peter-hanzo/KD/Документы/Чертежи/Конструктив/веранда 1.pdf

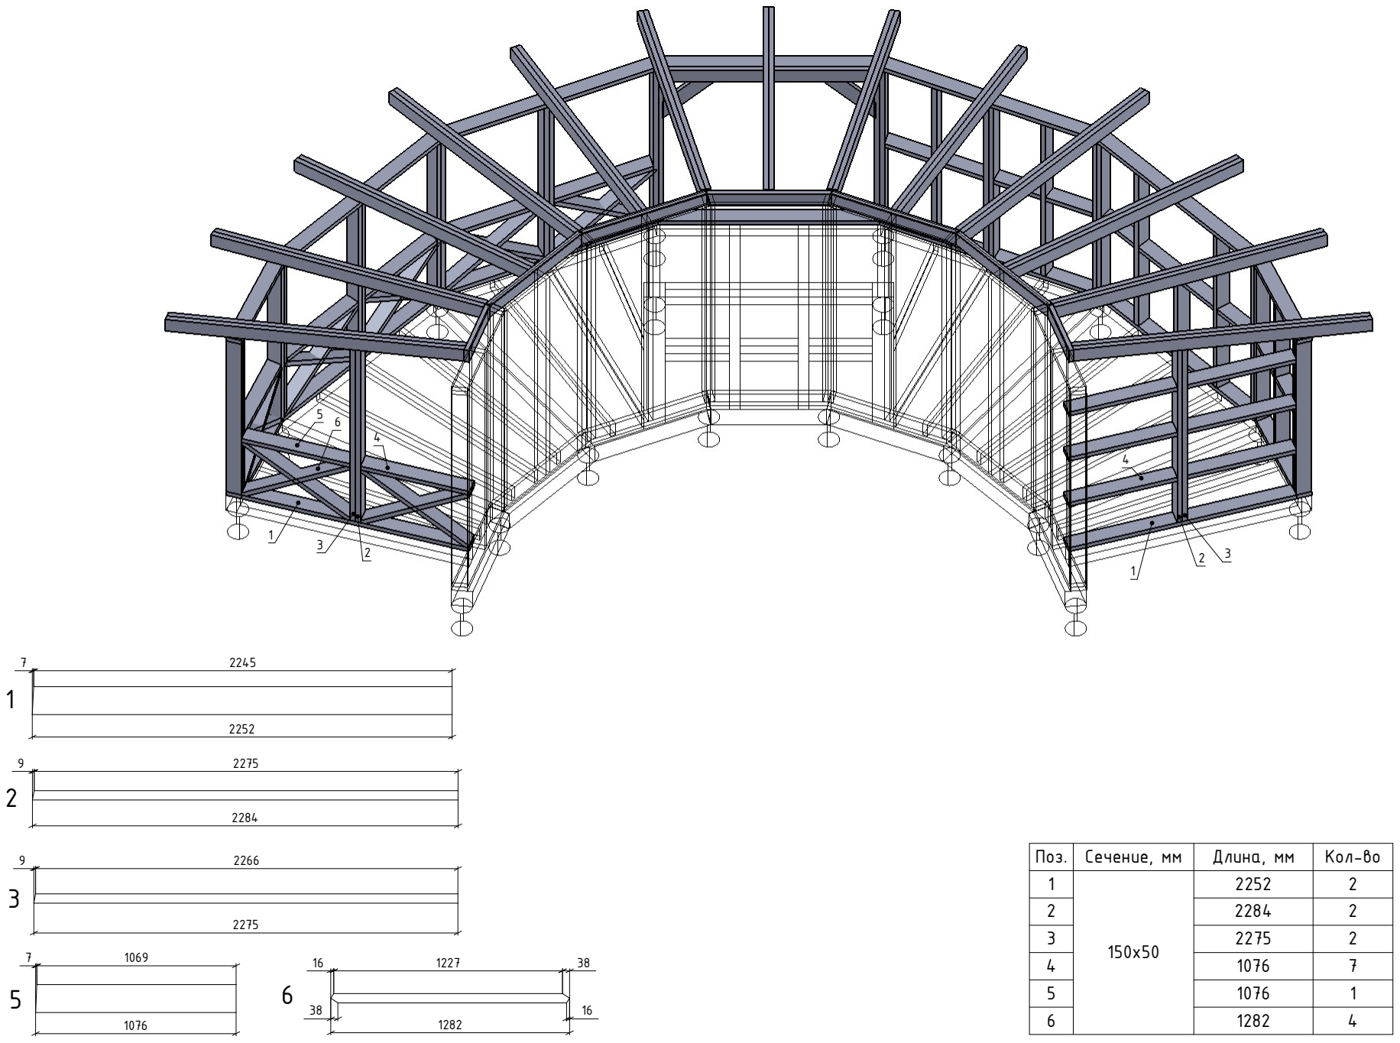
[picture p2: page 1]

6

1227 38
38
1282

16
16
Поз. | Сечение, мм | Длина, мм 2252 2 | Кол-во 1
3 | | 2275 | 2
5 | | 1076 | 1
2 | 150x50 | 2284 | 2
4 | | 1076 | 7
6 | | 1282 | 4

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
7 1069

1076

2245

2252

7 2

2284

9 2275

9 2266

2275
