peter-hanzo/KD/Документы/Участок/Кадастр - выписка.jpg

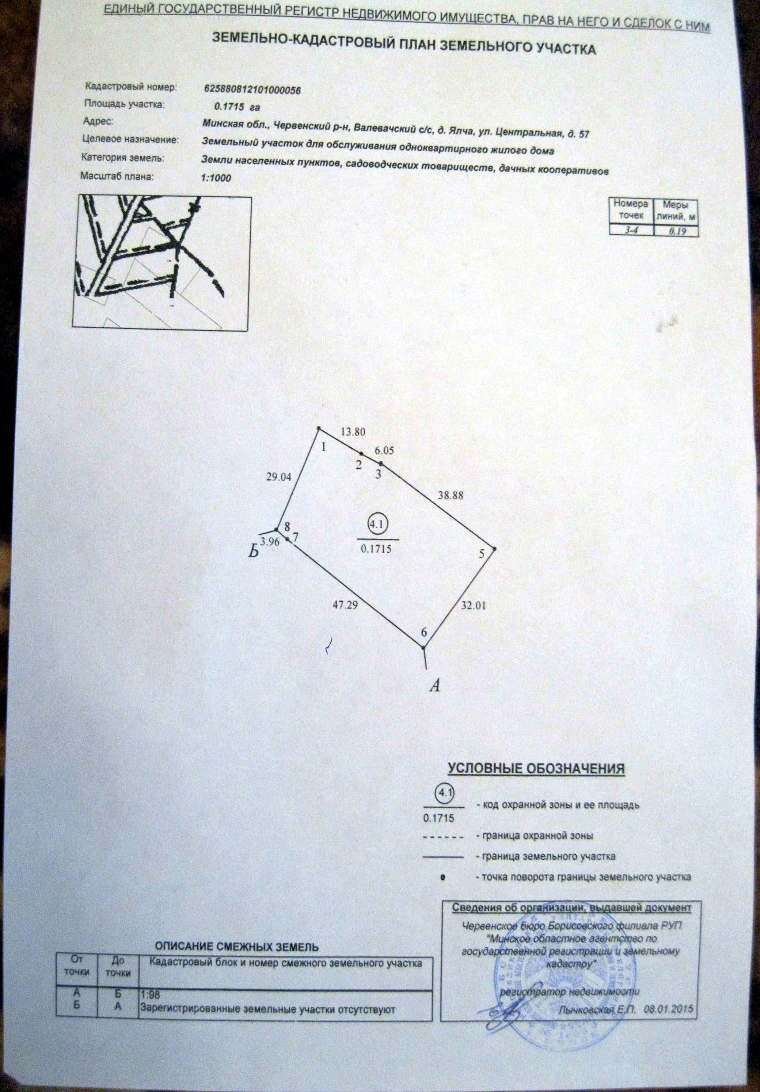
Документы/Участок/Кадастр - выписка.jpg
