peter-hanzo/KD/Документы/Участок/Свидетельство о государственной регистрации.jpg

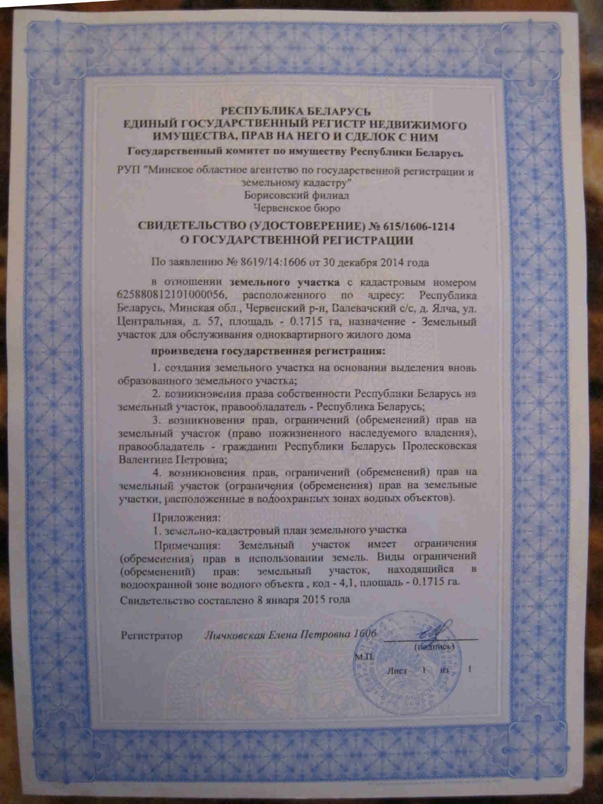
Документы/Участок/Свидетельство о государственной регистрации.jpg
