peter-hanzo/KD/Документы/Фактические расходы/2015-05/2015-05-20 - 2 109 300р - Установка электричества.jpg

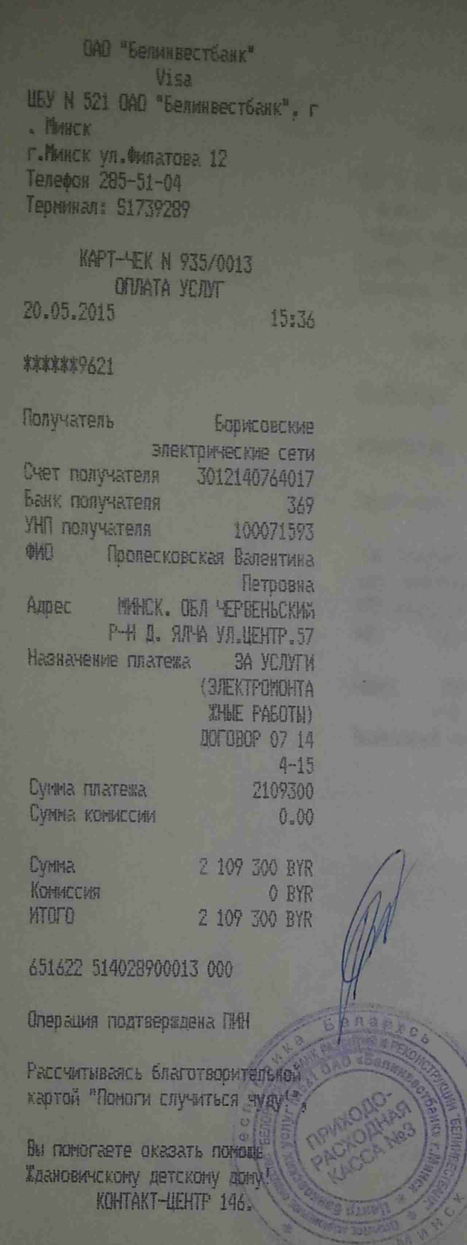
Документы/Фактические расходы/2015-05/2015-05-20 - 2 109 300р - Установка электричества.jpg
