peter-hanzo/KD/Документы/Фактические расходы/2015-05/2015-05-29 - 1 020 000р - Чертежи - Выбава-архитектура.jpg

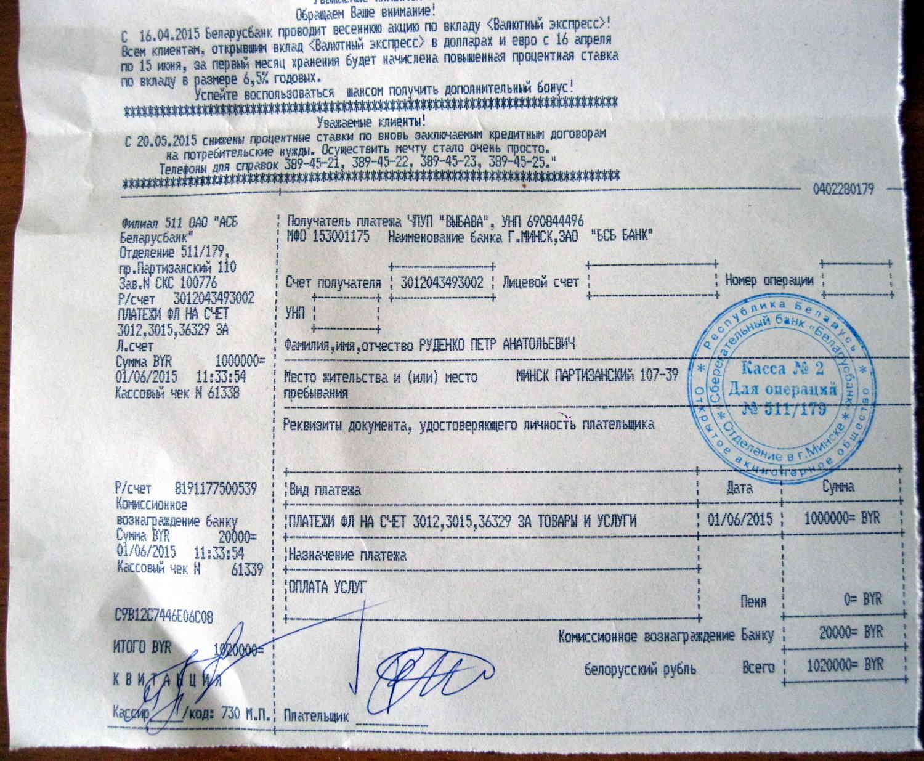
Документы/Фактические расходы/2015-05/2015-05-29 - 1 020 000р - Чертежи - Выбава-архитектура.jpg
