peter-hanzo/KD/Документы/Фактические расходы/2015-06/2015-06-15 - 21 300р - Транспорт - Ялча-Минск.jpg

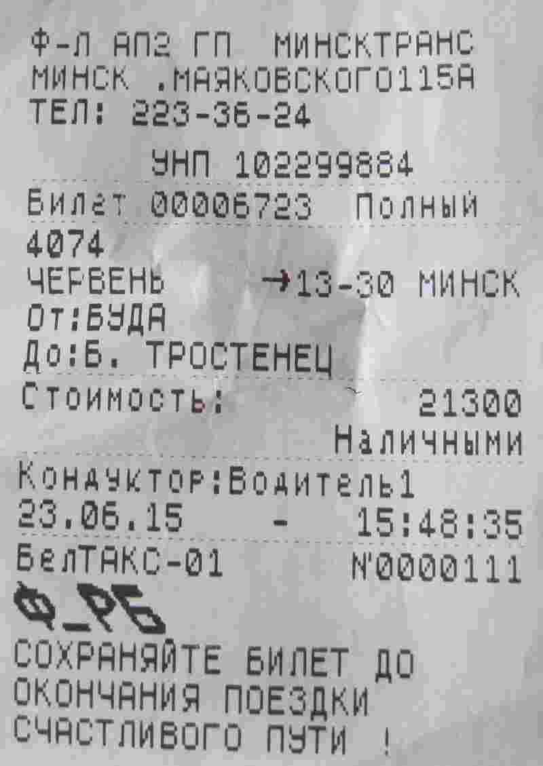
Документы/Фактические расходы/2015-06/2015-06-15 - 21 300р - Транспорт - Ялча-Минск.jpg
