peter-hanzo/KD/Документы/Фактические расходы/2015-06/2015-06-22 - 195 800р - Транспорт - Проездной.jpg

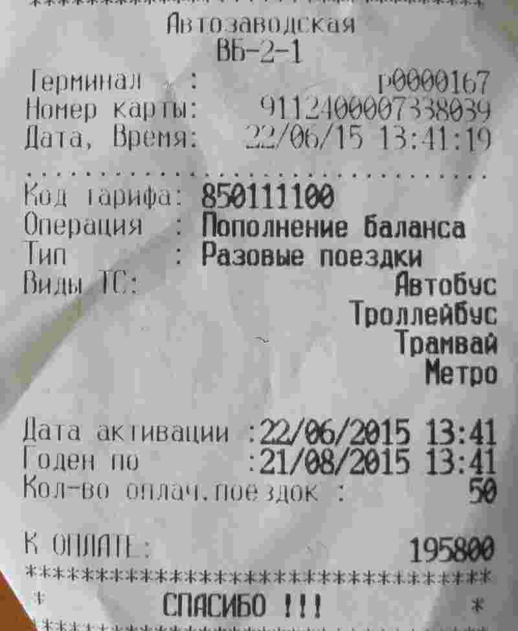
Документы/Фактические расходы/2015-06/2015-06-22 - 195 800р - Транспорт - Проездной.jpg
