peter-hanzo/KD/Документы/Фактические расходы/2015-06/2015-06-26 - 27 000р - Фундамент - Арматура.JPG

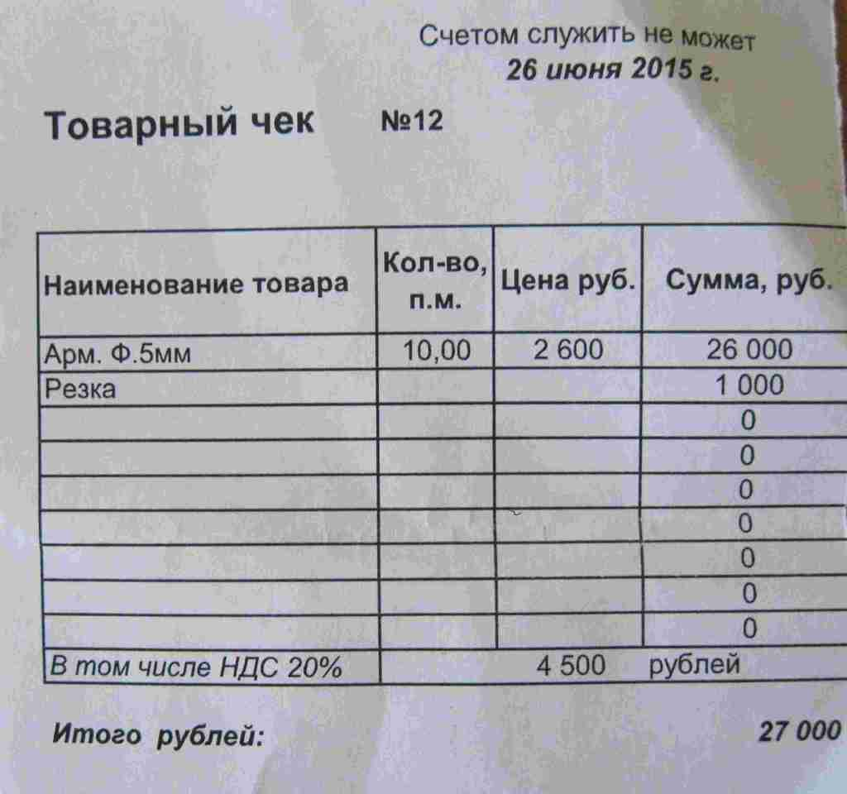
Документы/Фактические расходы/2015-06/2015-06-26 - 27 000р - Фундамент - Арматура.JPG
