peter-hanzo/KD/Документы/Фактические расходы/2015-06/2015-06-26 - 535 700р - Фундамент - Руберойд.JPG

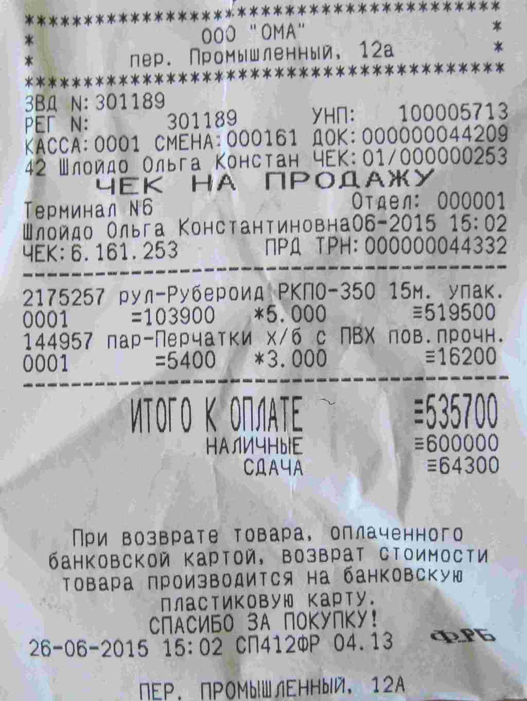
Документы/Фактические расходы/2015-06/2015-06-26 - 535 700р - Фундамент - Руберойд.JPG
