peter-hanzo/KD/Документы/Фактические расходы/2015-06/2015-06-26 - 600 000р - Доставка.JPG

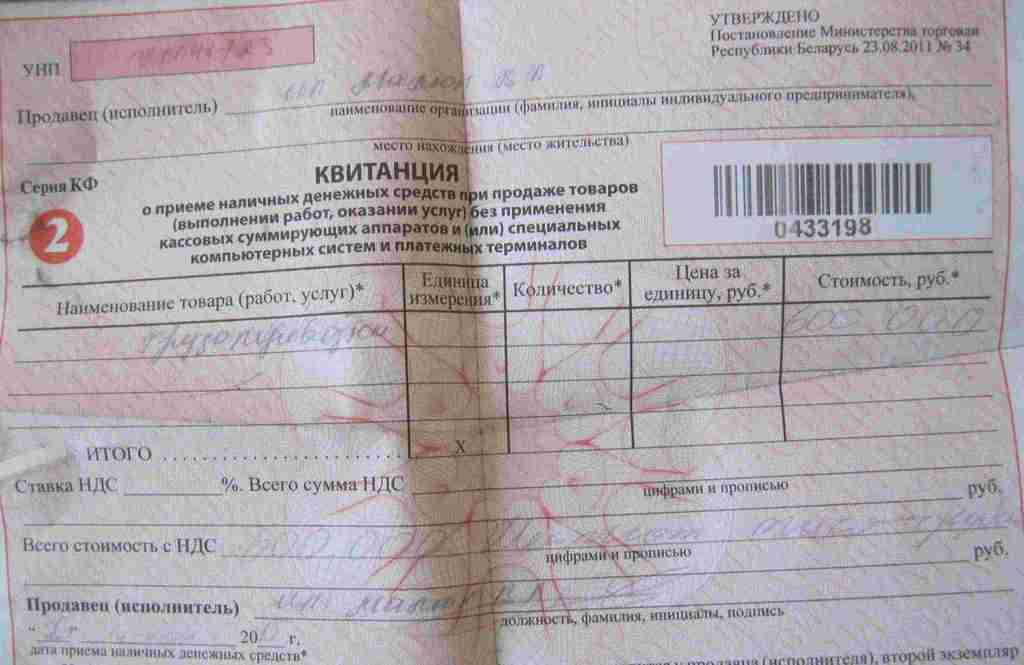
Документы/Фактические расходы/2015-06/2015-06-26 - 600 000р - Доставка.JPG
