peter-hanzo/KD/Документы/Фактические расходы/2015-06/2015-06-28 - 23 850р - Транспорт - Минск-Ялча.JPG

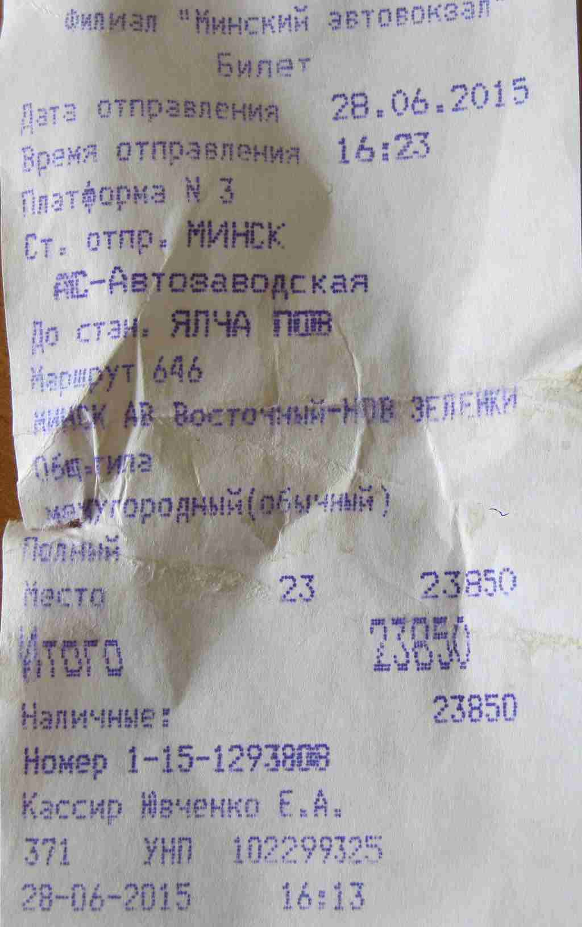
Документы/Фактические расходы/2015-06/2015-06-28 - 23 850р - Транспорт - Минск-Ялча.JPG
