peter-hanzo/KD/Документы/Фактические расходы/2015-06/2015-06-28 - 120 000р - Интернет.JPG

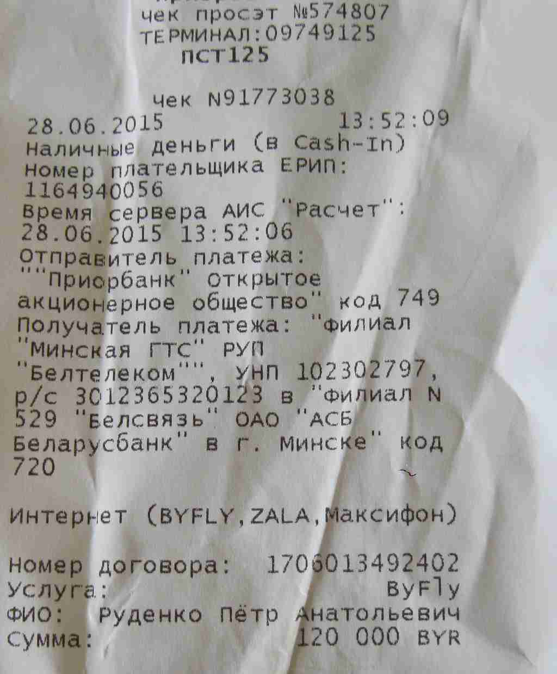
Документы/Фактические расходы/2015-06/2015-06-28 - 120 000р - Интернет.JPG
