peter-hanzo/KD/Документы/Фактические расходы/2015-06/2015-06-29 - 23 950р - Транспорт - Ялча-Минск.JPG

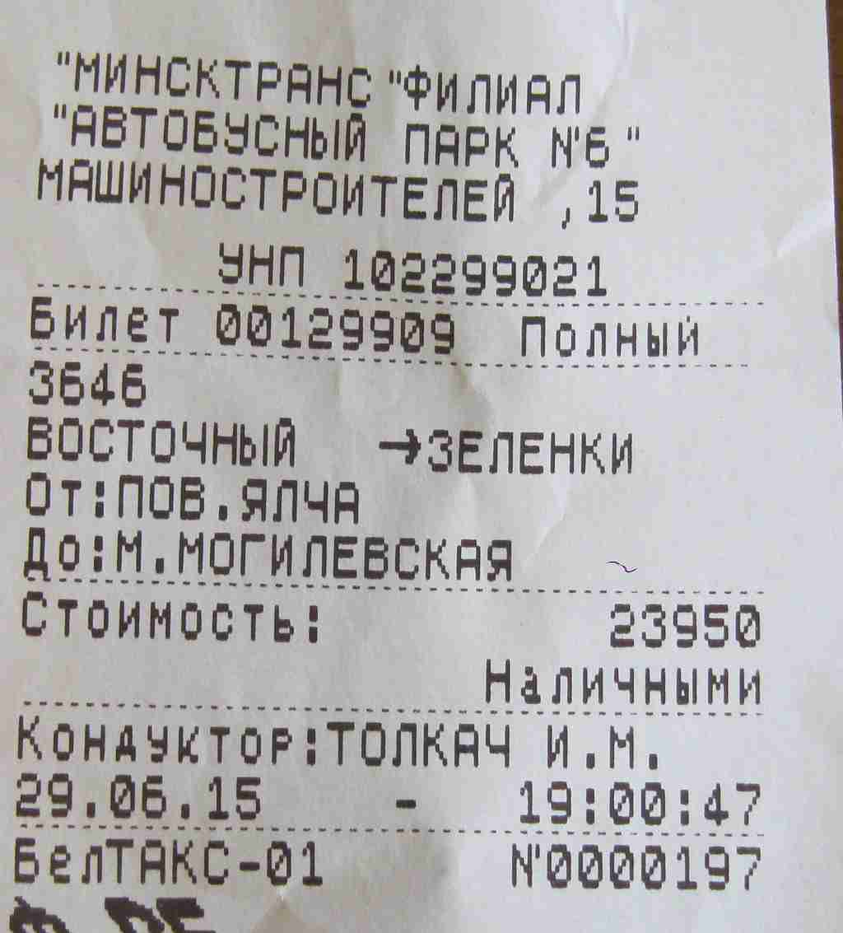
Документы/Фактические расходы/2015-06/2015-06-29 - 23 950р - Транспорт - Ялча-Минск.JPG
