peter-hanzo/KD/Документы/Фактические расходы/2015-07/2015-07-01 - 58 000р - Фундамент - Арматура.JPG

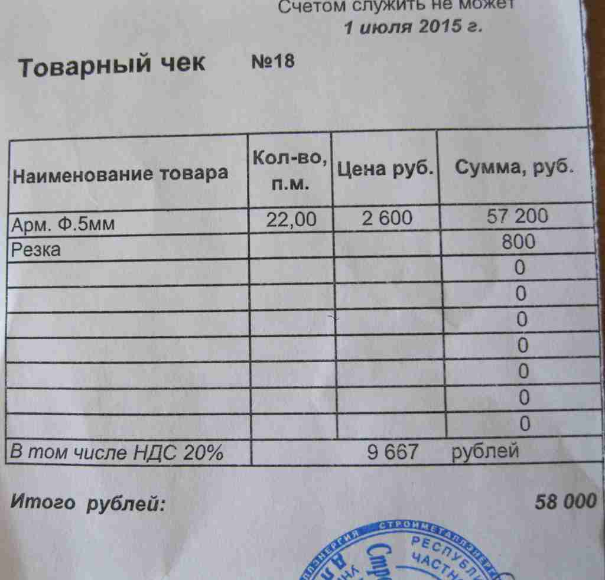
Документы/Фактические расходы/2015-07/2015-07-01 - 58 000р - Фундамент - Арматура.JPG
