peter-hanzo/KD/Документы/Фактические расходы/2015-07/2015-07-01 - 62 000р - Фундамент - Вязальная проволока.JPG

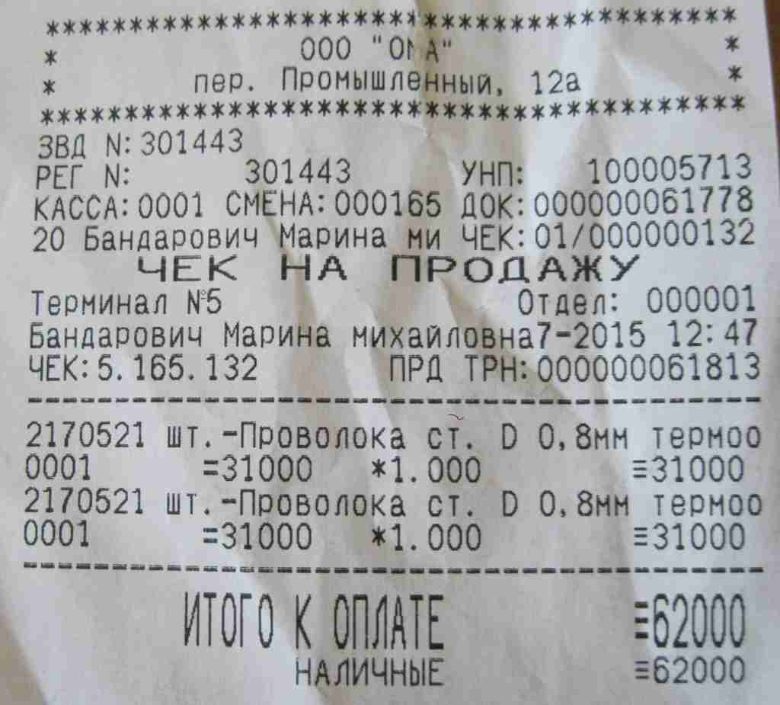
Документы/Фактические расходы/2015-07/2015-07-01 - 62 000р - Фундамент - Вязальная проволока.JPG
