peter-hanzo/KD/Документы/Фактические расходы/2015-07/2015-07-01 - 119 200р - Фундамент - Лента-скотч.JPG

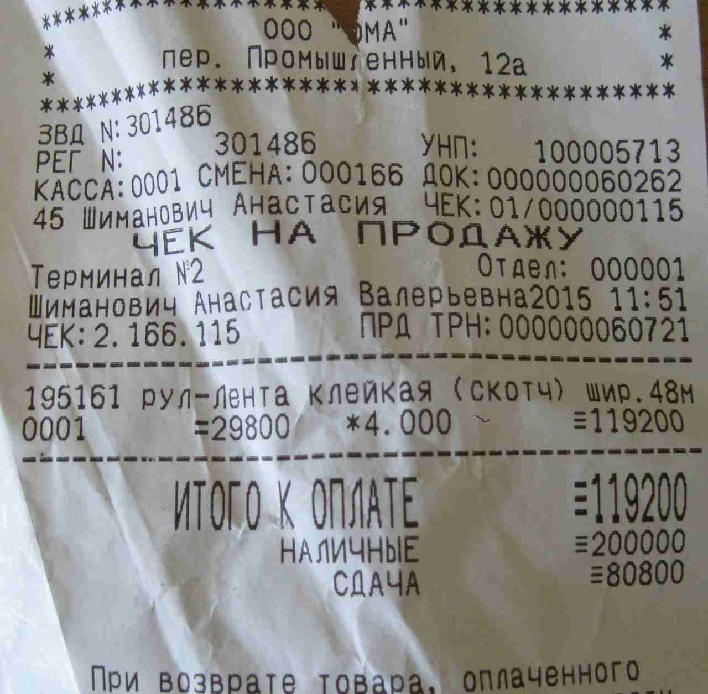
Документы/Фактические расходы/2015-07/2015-07-01 - 119 200р - Фундамент - Лента-скотч.JPG
