peter-hanzo/KD/Документы/Фактические расходы/2015-07/2015-07-01 - 220 00р - Связь - Мобильный.JPG

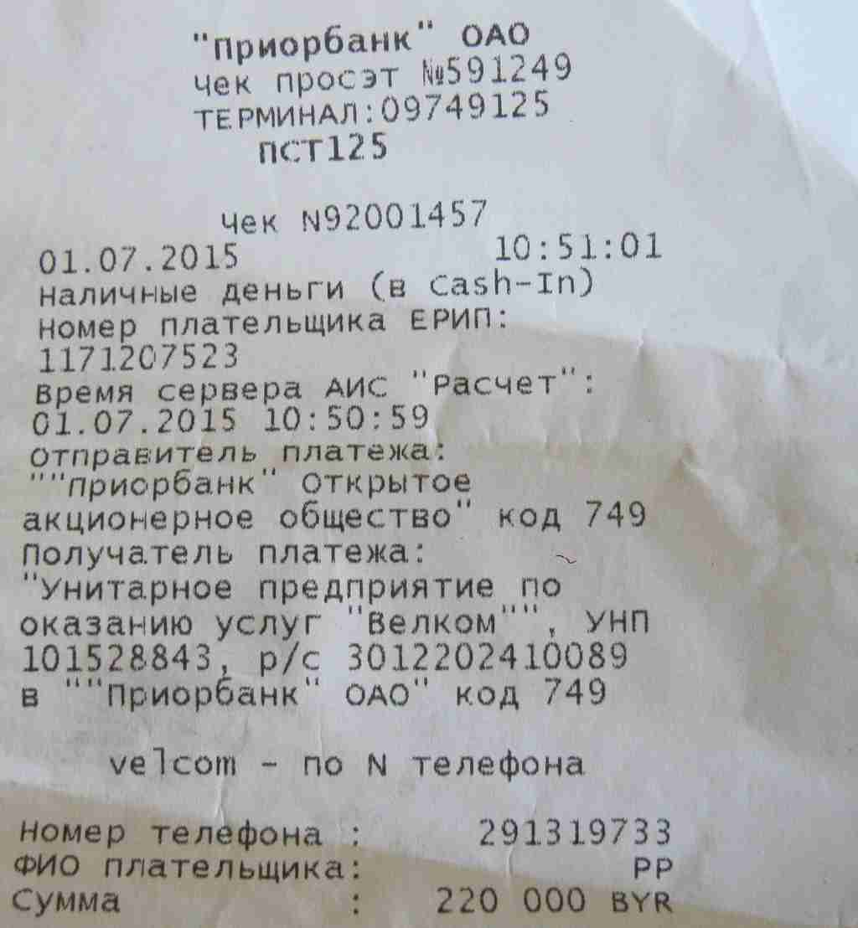
Документы/Фактические расходы/2015-07/2015-07-01 - 220 00р - Связь - Мобильный.JPG
