peter-hanzo/KD/Документы/Фактические расходы/2015-07/2015-07-02 - 23 900р - Транспорт - Ялча-Минск.JPG

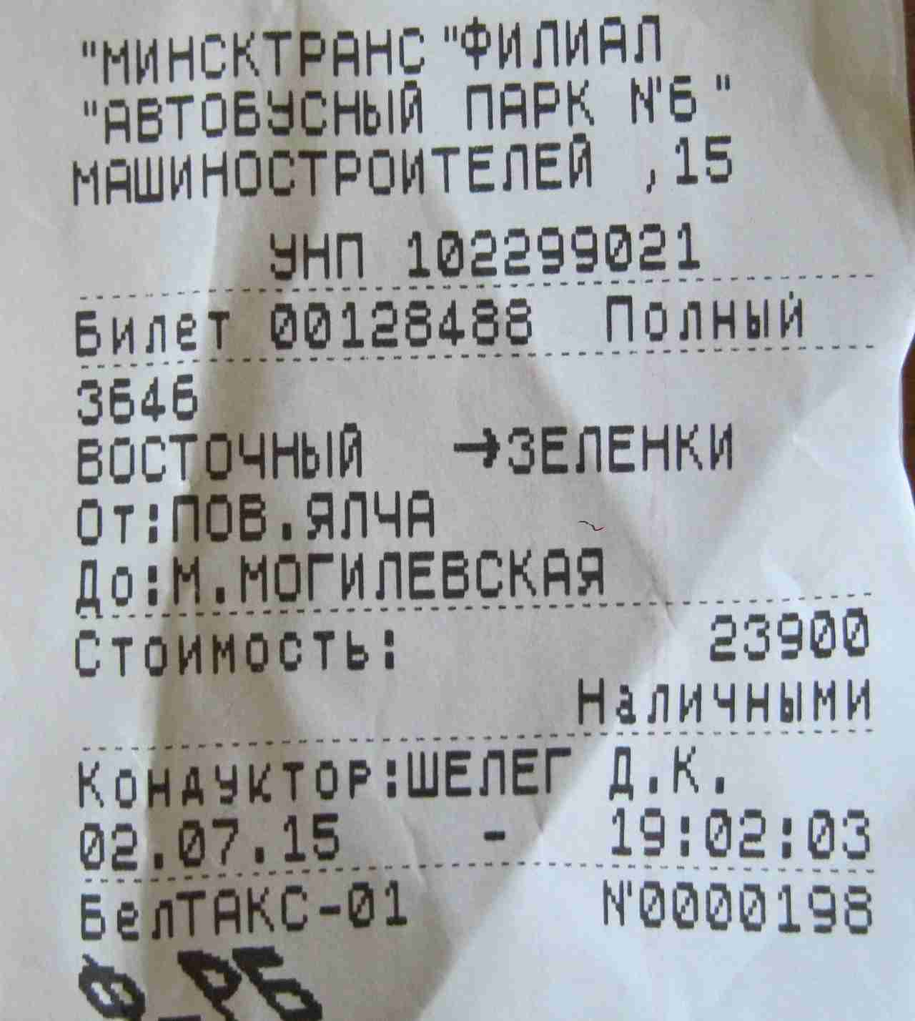
Документы/Фактические расходы/2015-07/2015-07-02 - 23 900р - Транспорт - Ялча-Минск.JPG
