peter-hanzo/KD/Документы/Фактические расходы/2015-07/2015-07-21 - 26 100р - Транспорт - Минск-Ялча.jpg

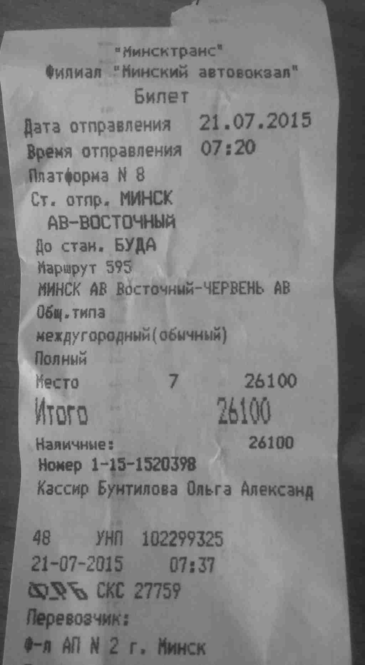
Документы/Фактические расходы/2015-07/2015-07-21 - 26 100р - Транспорт - Минск-Ялча.jpg
