peter-hanzo/KD/Документы/Фактические расходы/2015-07/2015-07-22 - 160 200р - Транспорт - Проездной.jpg

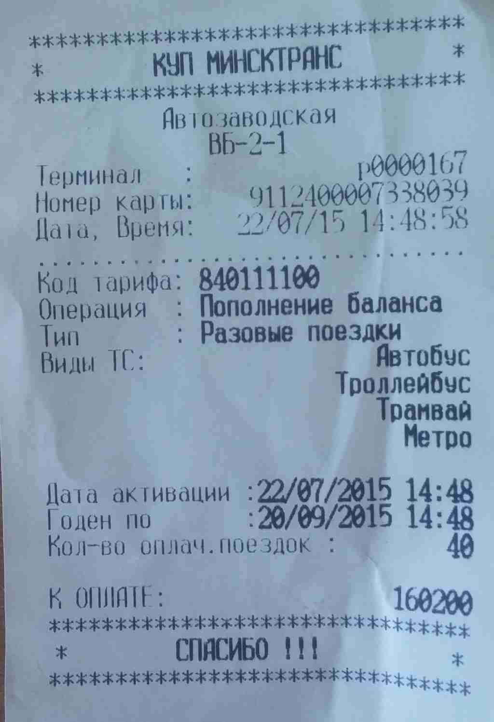
Документы/Фактические расходы/2015-07/2015-07-22 - 160 200р - Транспорт - Проездной.jpg
