peter-hanzo/KD/Документы/Фактические расходы/2015-07/2015-07-29 - 70 000р - Связь - Интернет.JPG

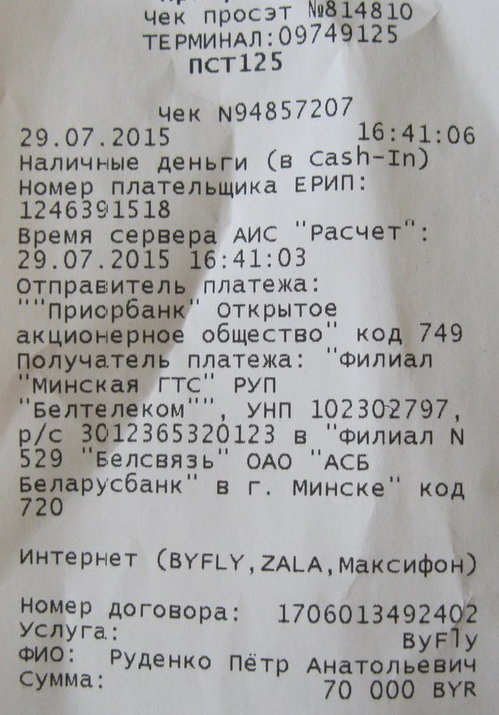
Документы/Фактические расходы/2015-07/2015-07-29 - 70 000р - Связь - Интернет.JPG
