peter-hanzo/KD/Документы/Фактические расходы/2015-08/2015-08-01 - 23 800р - Транспорт - Минск-Ялча.JPG

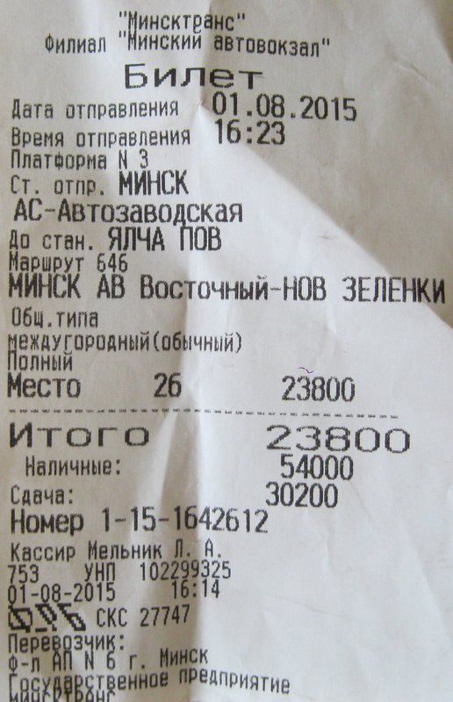
Документы/Фактические расходы/2015-08/2015-08-01 - 23 800р - Транспорт - Минск-Ялча.JPG
