peter-hanzo/KD/Документы/Фактические расходы/2015-08/2015-08-03 - 300 000р - Доставка - Бензин.JPG

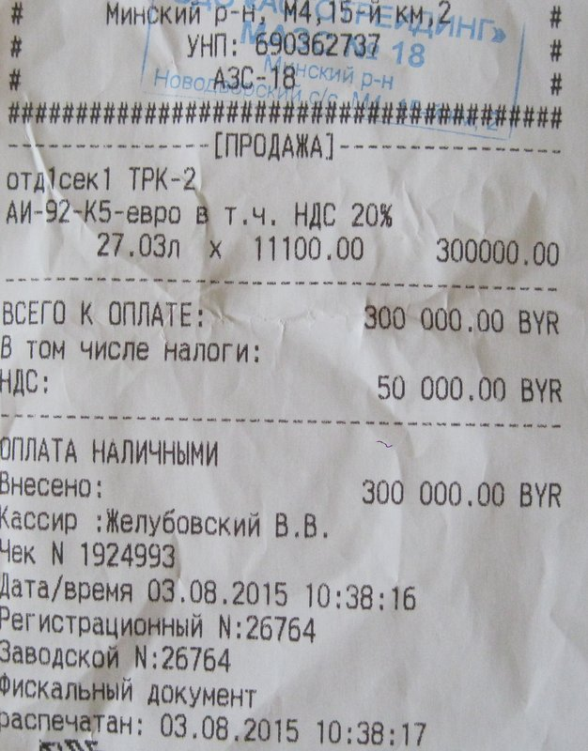
Документы/Фактические расходы/2015-08/2015-08-03 - 300 000р - Доставка - Бензин.JPG
