peter-hanzo/KD/Документы/Фактические расходы/2015-08/2015-08-03 - 620 000р - Инструмент - Аренда инструмента.JPG

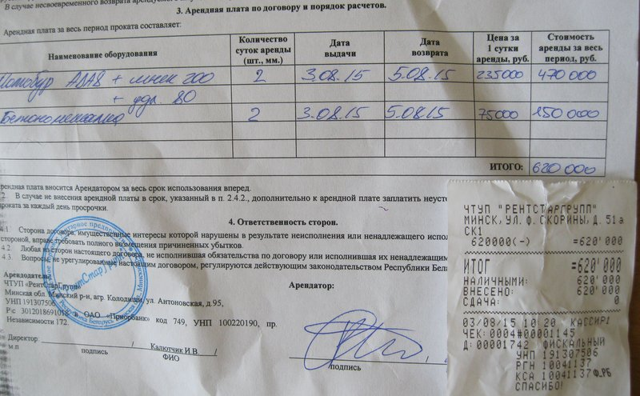
Документы/Фактические расходы/2015-08/2015-08-03 - 620 000р - Инструмент - Аренда инструмента.JPG
