peter-hanzo/KD/Документы/Фактические расходы/2015-08/2015-08-05 - 200 000р - Доставка - Бензин.JPG

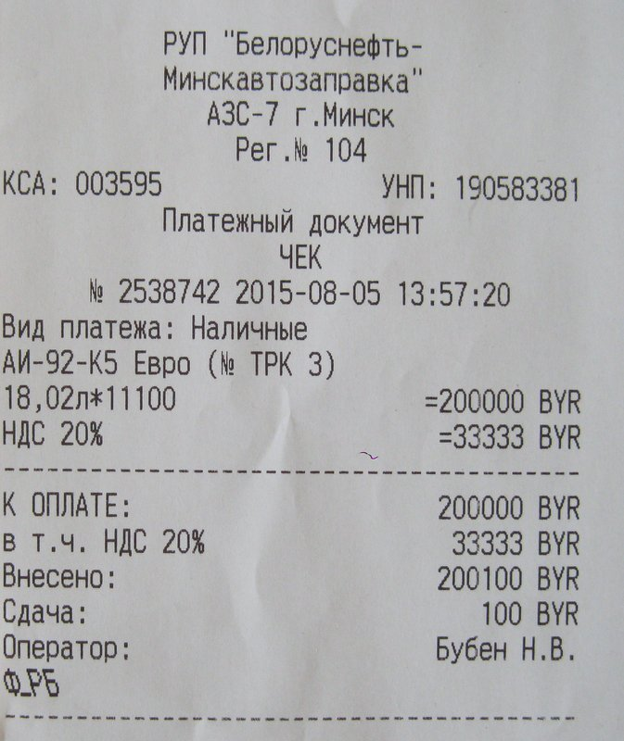
Документы/Фактические расходы/2015-08/2015-08-05 - 200 000р - Доставка - Бензин.JPG
