peter-hanzo/KD/Документы/Фактические расходы/2015-08/2015-08-11 - 195 800р - Транспорт - Проездной.jpg

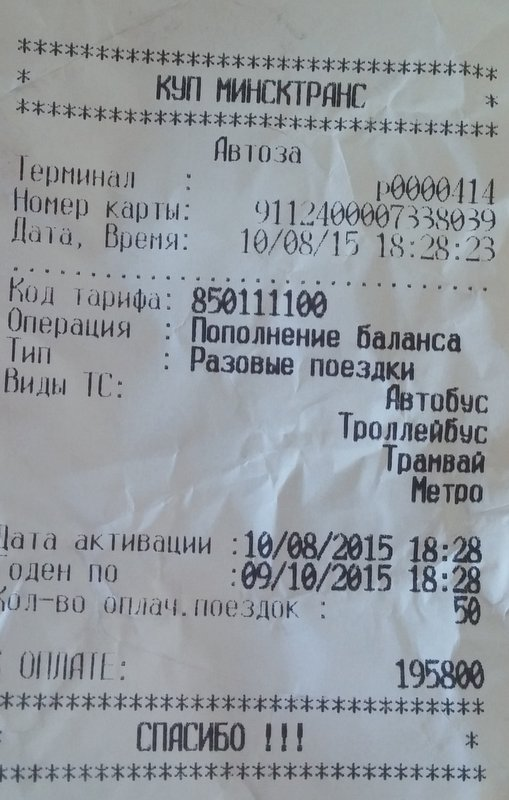
Документы/Фактические расходы/2015-08/2015-08-11 - 195 800р - Транспорт - Проездной.jpg
