peter-hanzo/KD/Документы/Фактические расходы/2015-08/2015-08-12 - 128 000р - Инструмент - Сверло для свай + 2 анкера.jpg

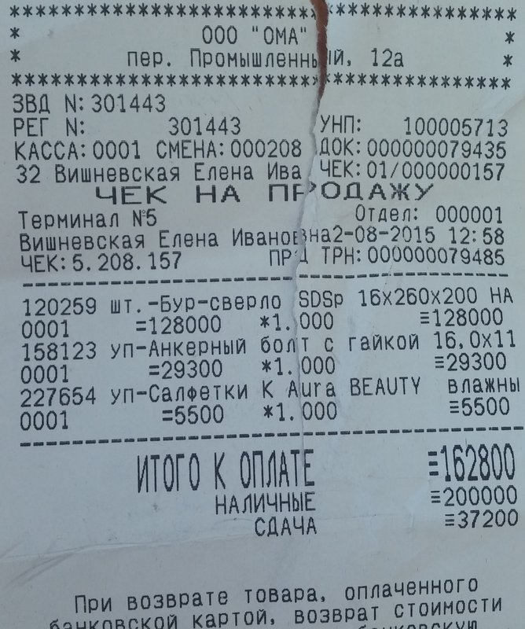
Документы/Фактические расходы/2015-08/2015-08-12 - 128 000р - Инструмент - Сверло для свай + 2 анкера.jpg
