peter-hanzo/KD/Документы/Фактические расходы/2015-08/2015-08-17 - 100 000р - Связь - Интернет.jpg

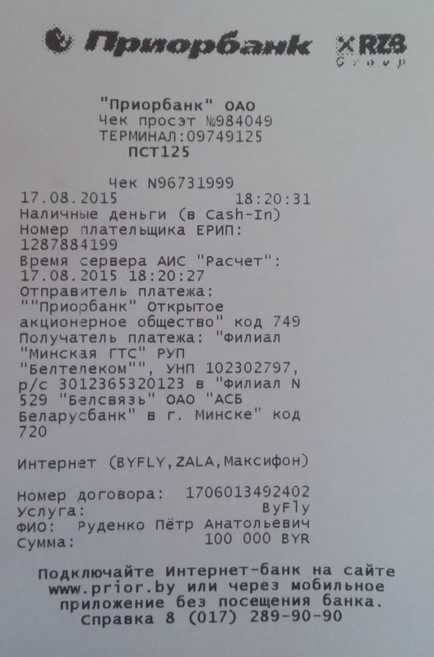
Документы/Фактические расходы/2015-08/2015-08-17 - 100 000р - Связь - Интернет.jpg
