peter-hanzo/KD/Документы/Фактические расходы/2015-08/2015-08-17 - 200 000р - Связь - Мобильный.jpg

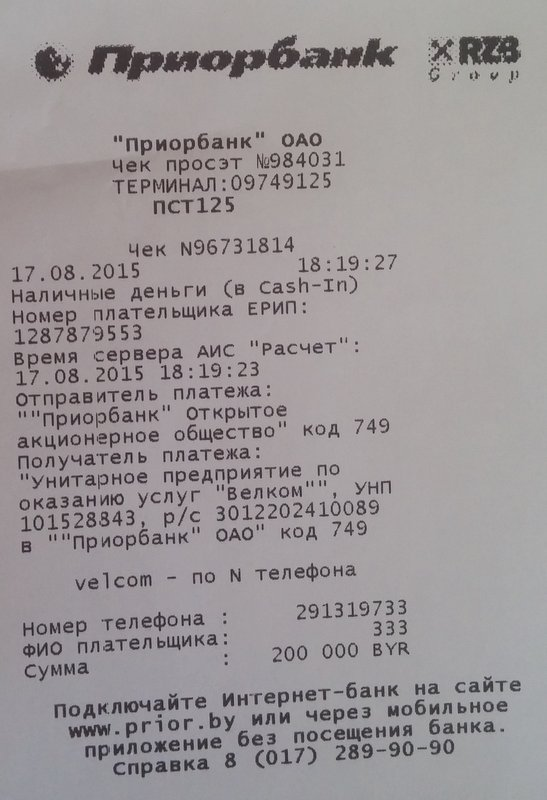
Документы/Фактические расходы/2015-08/2015-08-17 - 200 000р - Связь - Мобильный.jpg
