peter-hanzo/KD/Документы/Фактические расходы/2015-08/2015-08-21 - 26 900р - Фундамент - хомут стальной.jpg

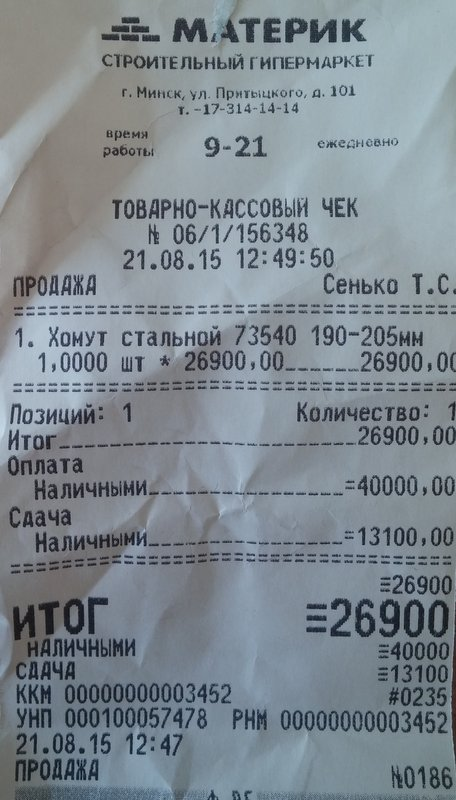
Документы/Фактические расходы/2015-08/2015-08-21 - 26 900р - Фундамент - хомут стальной.jpg
