peter-hanzo/KD/Документы/Фактические расходы/2015-08/2015-08-21 - 300 000р - Доставка - Бензин.jpg

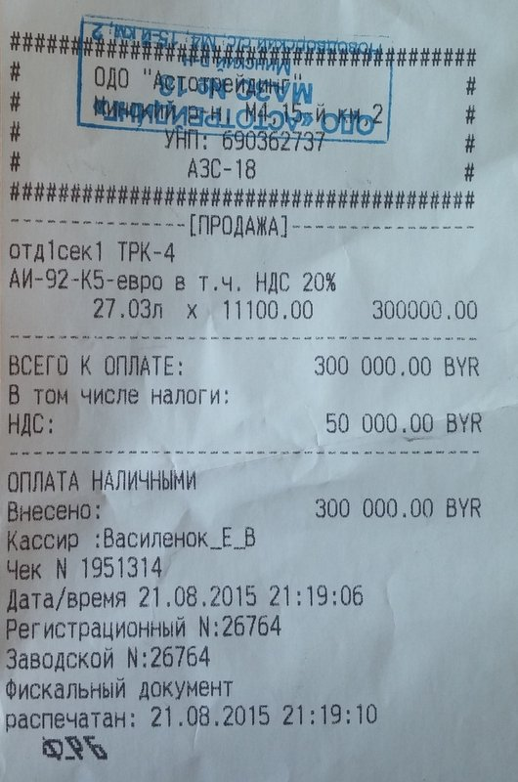
Документы/Фактические расходы/2015-08/2015-08-21 - 300 000р - Доставка - Бензин.jpg
