peter-hanzo/KD/Документы/Фактические расходы/2015-08/2015-08-21 - 768 400р - Каркас - Шурупы шестигранные+пропитка.jpg

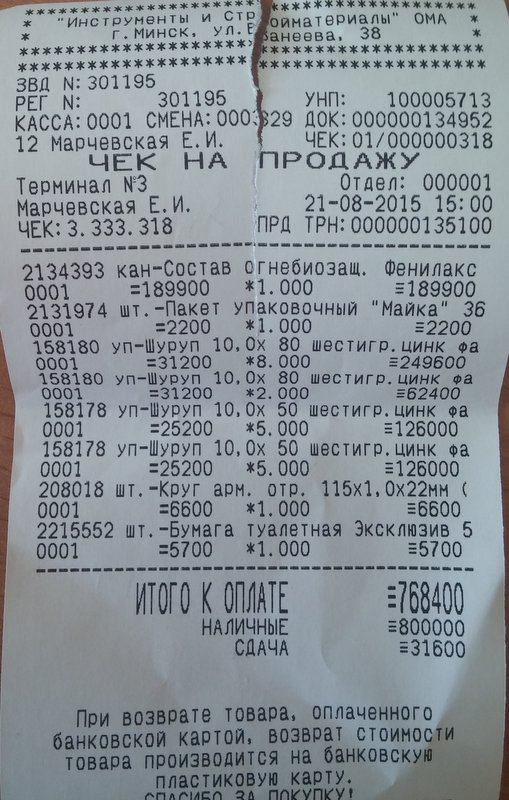
Документы/Фактические расходы/2015-08/2015-08-21 - 768 400р - Каркас - Шурупы шестигранные+пропитка.jpg
