peter-hanzo/KD/Документы/Фактические расходы/2015-08/2015-08-22 - 23 900р - Транспорт - Ялча-Минск.jpg

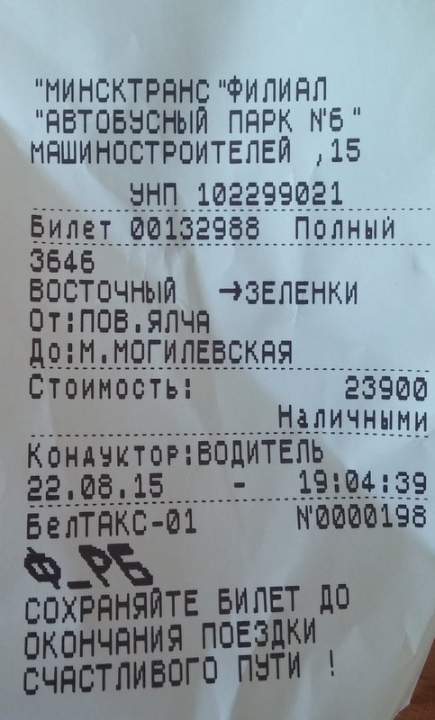
Документы/Фактические расходы/2015-08/2015-08-22 - 23 900р - Транспорт - Ялча-Минск.jpg
