peter-hanzo/KD/Документы/Фактические расходы/2015-08/2015-08-28 - 30 000р - Транспорт - Минск-Ялча.jpg

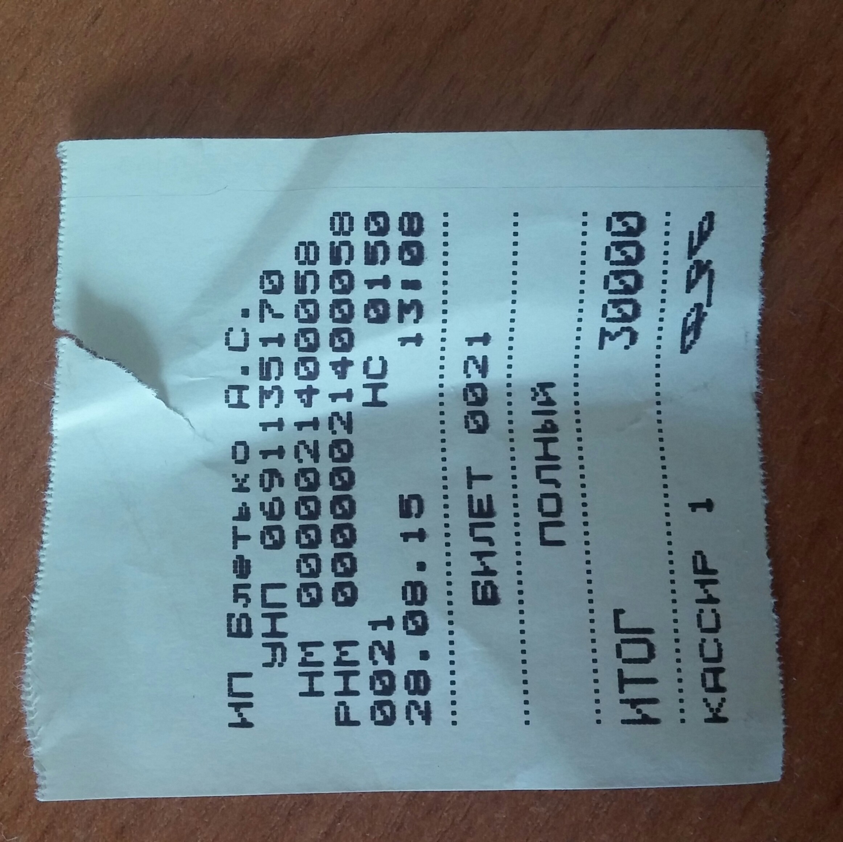
Документы/Фактические расходы/2015-08/2015-08-28 - 30 000р - Транспорт - Минск-Ялча.jpg
