peter-hanzo/KD/Документы/Фактические расходы/2015-08/2015-08-30 - 30 000р - Транспорт - Ялча-Минск.jpg

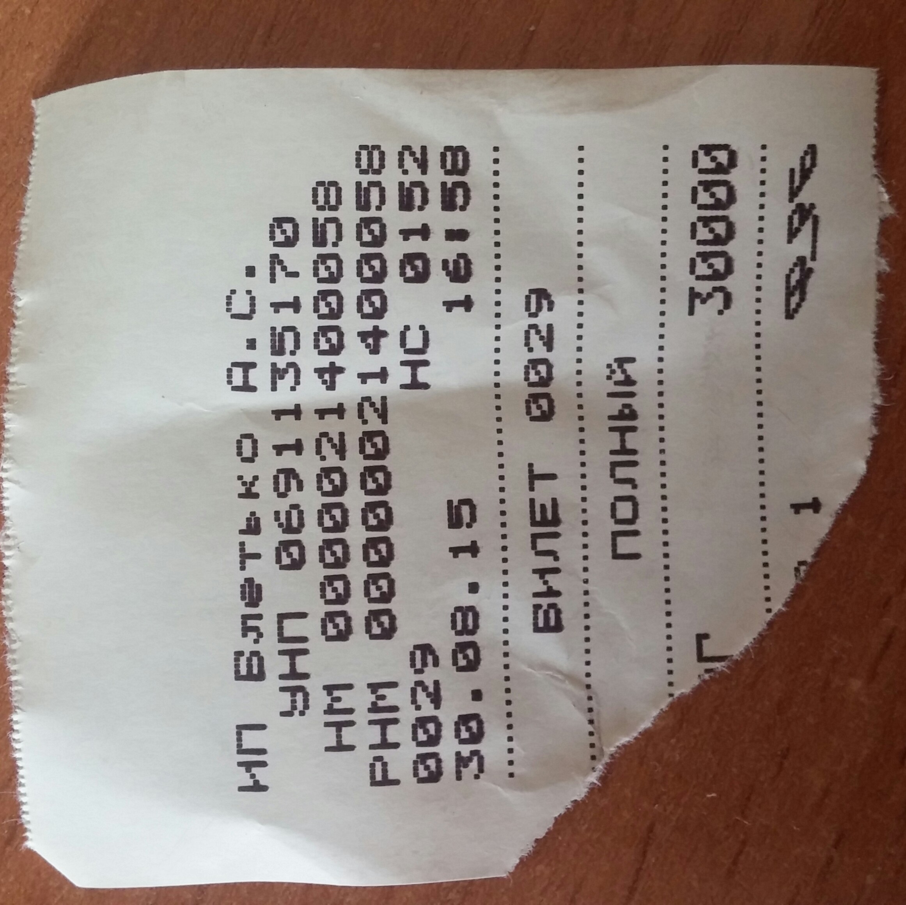
Документы/Фактические расходы/2015-08/2015-08-30 - 30 000р - Транспорт - Ялча-Минск.jpg
