peter-hanzo/KD/Документы/Фактические расходы/2015-09/2015-09-02 - 2 162 200р - Каркас - Шурупы+болты.jpg

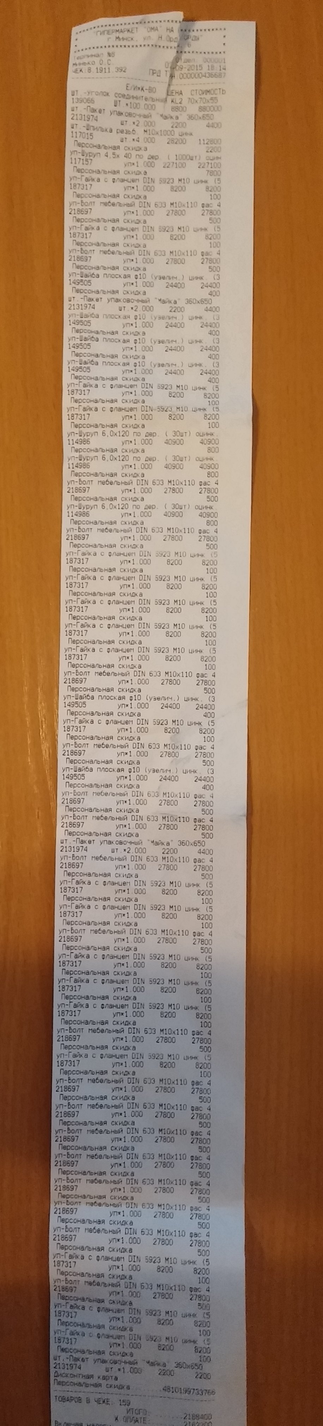
Документы/Фактические расходы/2015-09/2015-09-02 - 2 162 200р - Каркас - Шурупы+болты.jpg
