peter-hanzo/KD/Документы/Фактические расходы/2015-09/2015-09-02 - 18 800р - Инструмент - Головка.jpg

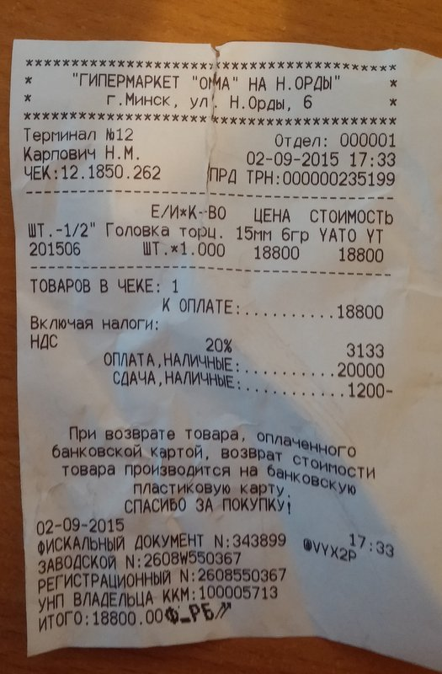
Документы/Фактические расходы/2015-09/2015-09-02 - 18 800р - Инструмент - Головка.jpg
