peter-hanzo/KD/Документы/Фактические расходы/2015-09/2015-09-02 - 250 000р - Связь - Мобильный.jpg

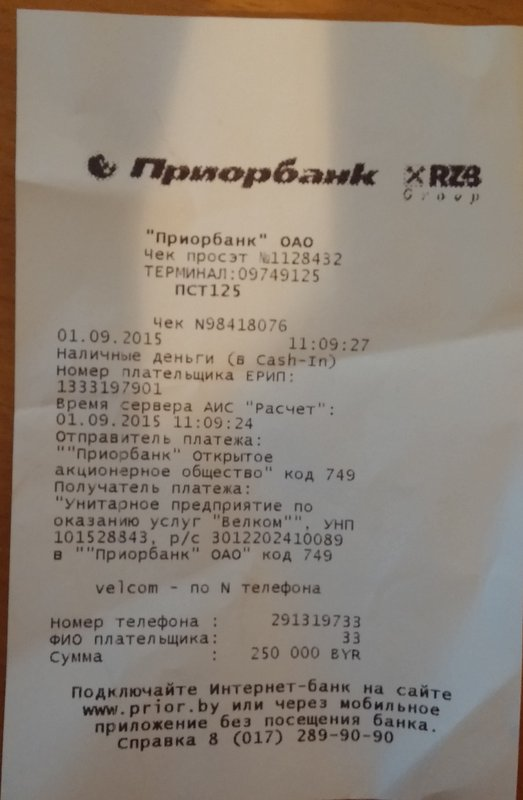
Документы/Фактические расходы/2015-09/2015-09-02 - 250 000р - Связь - Мобильный.jpg
