peter-hanzo/KD/Документы/Фактические расходы/2015-09/2015-09-02 - 276 500р - Каркас - Шурупы.jpg

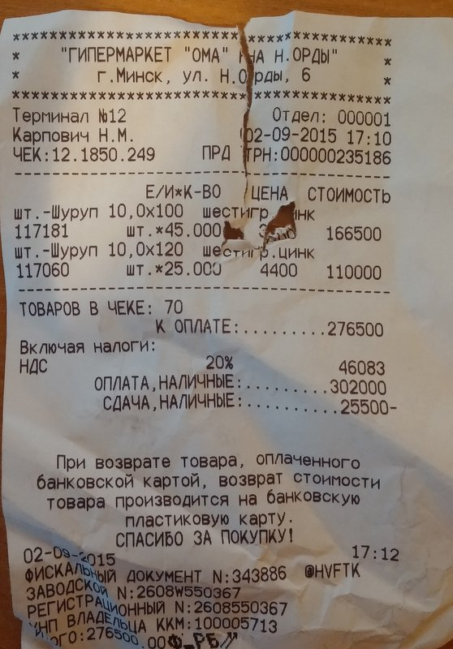
Документы/Фактические расходы/2015-09/2015-09-02 - 276 500р - Каркас - Шурупы.jpg
