peter-hanzo/KD/Документы/Фактические расходы/2015-09/2015-09-02 - 509 700р - Каркас - Крепления+шурупы.jpg

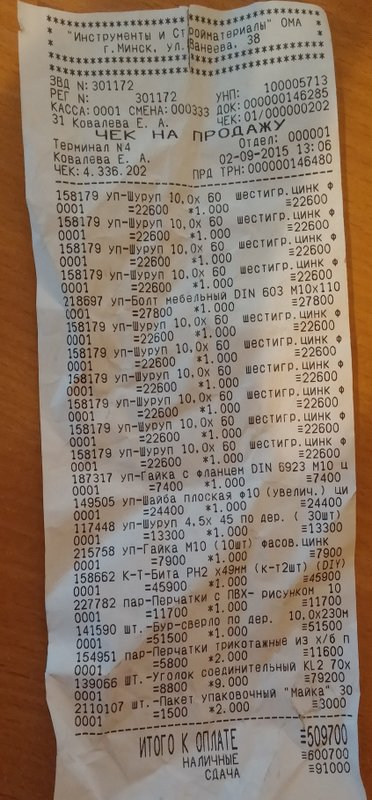
Документы/Фактические расходы/2015-09/2015-09-02 - 509 700р - Каркас - Крепления+шурупы.jpg
