peter-hanzo/KD/Документы/Фактические расходы/2015-09/2015-09-08 - 90 200р - Каркас - Шурупы.jpg

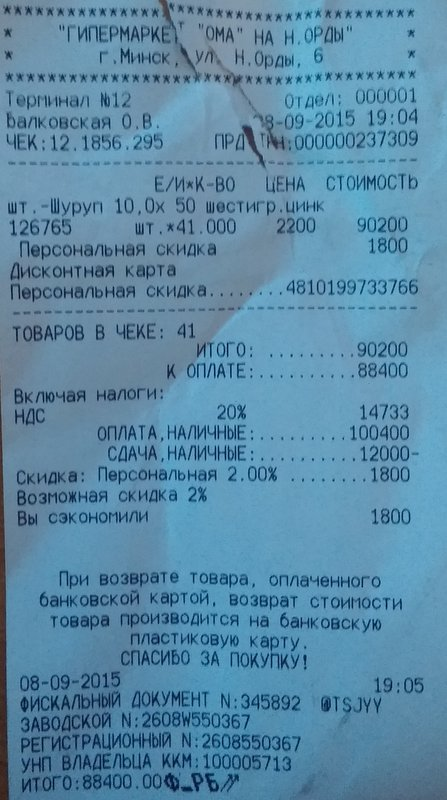
Документы/Фактические расходы/2015-09/2015-09-08 - 90 200р - Каркас - Шурупы.jpg
