peter-hanzo/KD/Документы/Фактические расходы/2015-09/2015-09-08 - 172 100р - Инструмент - Цепь для пилы.jpg

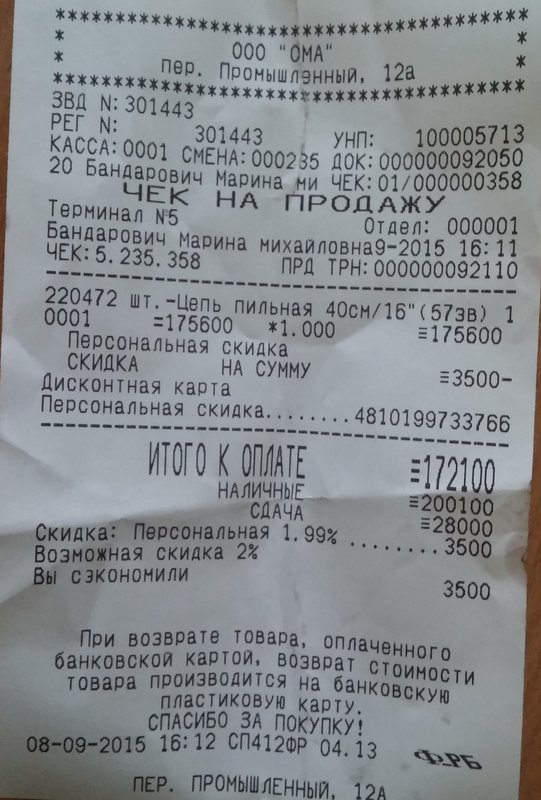
Документы/Фактические расходы/2015-09/2015-09-08 - 172 100р - Инструмент - Цепь для пилы.jpg
