peter-hanzo/KD/Документы/Фактические расходы/2015-09/2015-09-08 - 195 800р - Транспорт - Проездной.jpg

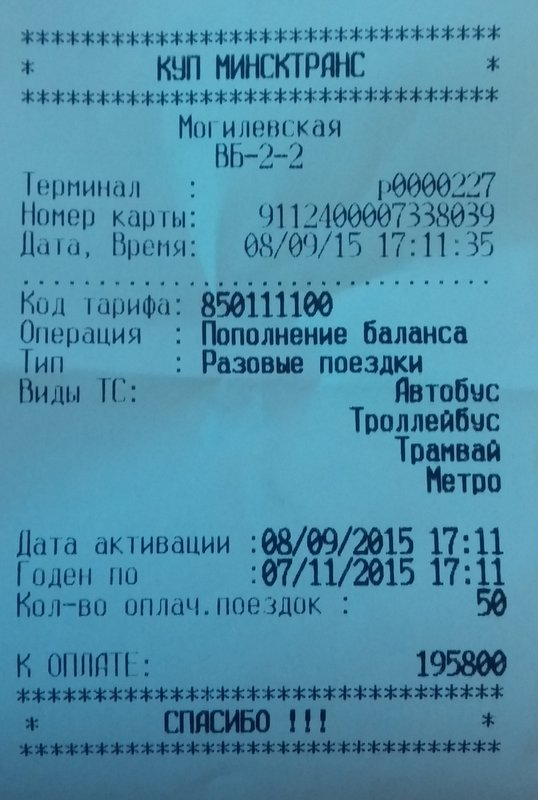
Документы/Фактические расходы/2015-09/2015-09-08 - 195 800р - Транспорт - Проездной.jpg
