peter-hanzo/KD/Документы/Фактические расходы/2015-09/2015-09-08 - 265 000р - Инструмент - Сверло и трещетка.jpg

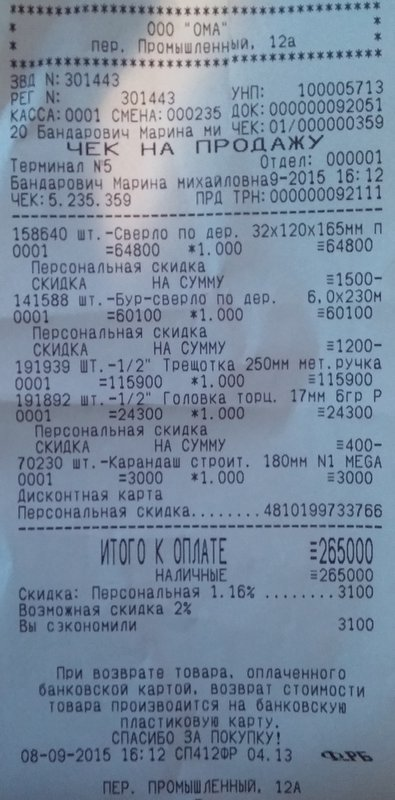
Документы/Фактические расходы/2015-09/2015-09-08 - 265 000р - Инструмент - Сверло и трещетка.jpg
