peter-hanzo/KD/Документы/Фактические расходы/2015-09/2015-09-08 - 6331 000р - Каркас - Доска 150мм.jpg

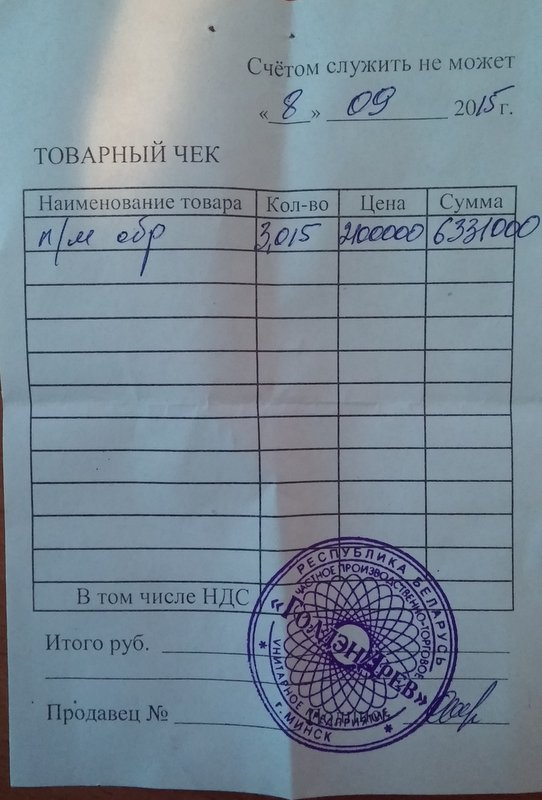
Документы/Фактические расходы/2015-09/2015-09-08 - 6331 000р - Каркас - Доска 150мм.jpg
