peter-hanzo/KD/Документы/Фактические расходы/2015-09/2015-09-15 - 2200 000р - Каркас - Брусок 50мм.jpg

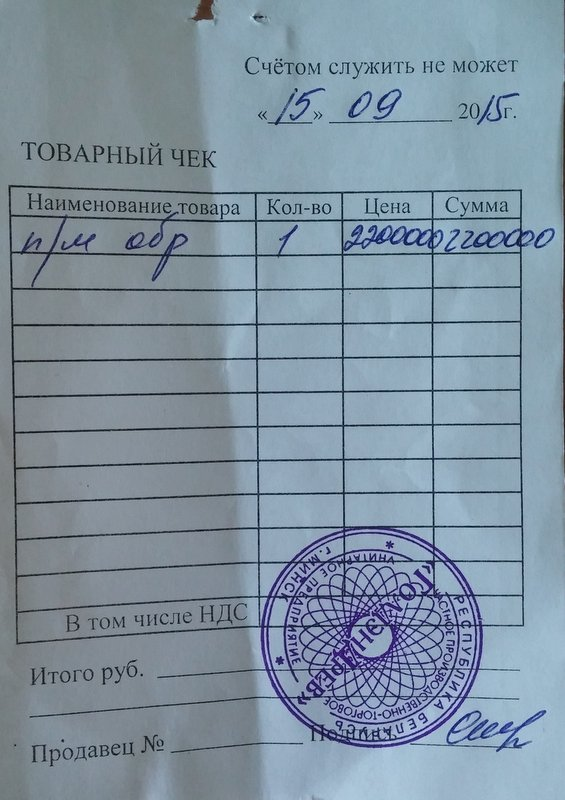
Документы/Фактические расходы/2015-09/2015-09-15 - 2200 000р - Каркас - Брусок 50мм.jpg
