peter-hanzo/KD/Документы/Фактические расходы/2015-09/2015-09-16 - 170 000р - Связь - Мобильный.jpg

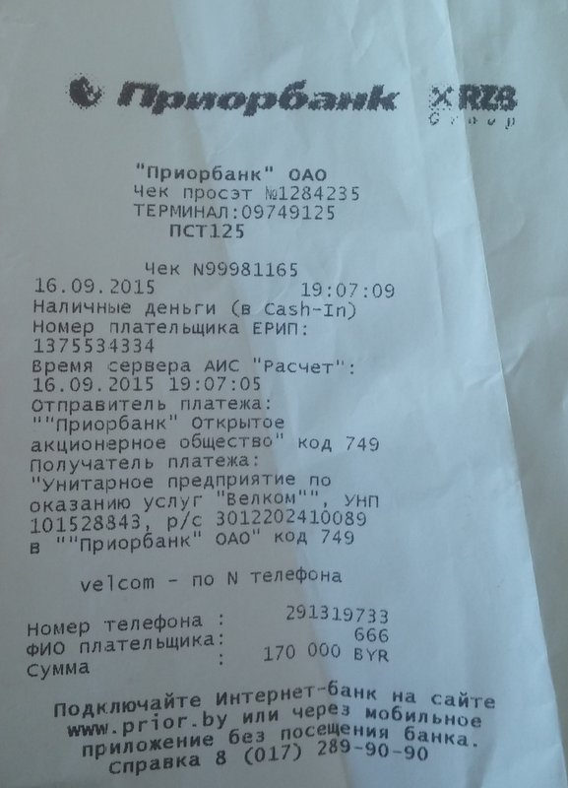
Документы/Фактические расходы/2015-09/2015-09-16 - 170 000р - Связь - Мобильный.jpg
