peter-hanzo/KD/Документы/Фактические расходы/2015-09/2015-09-20 - 3946 000р - Каркас - Крепления и пленка.jpg

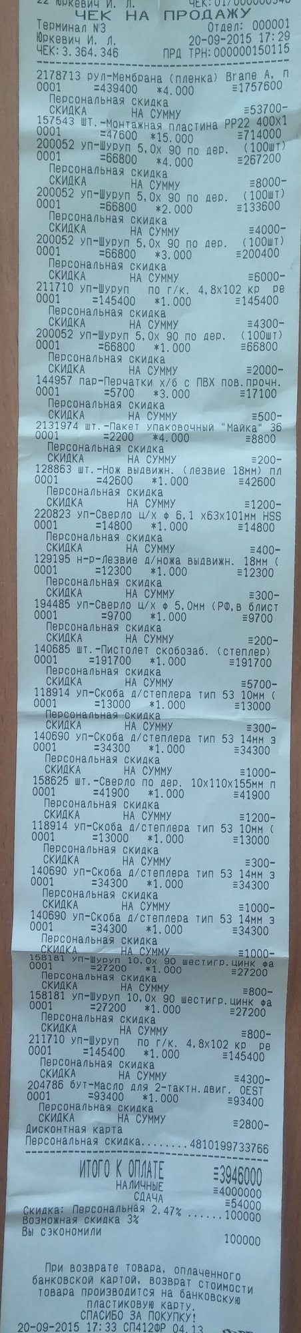
Документы/Фактические расходы/2015-09/2015-09-20 - 3946 000р - Каркас - Крепления и пленка.jpg
