peter-hanzo/KD/Документы/Фактические расходы/2015-09/2015-09-25 - 30 000р - Транспорт - Ялча_Минск.jpg

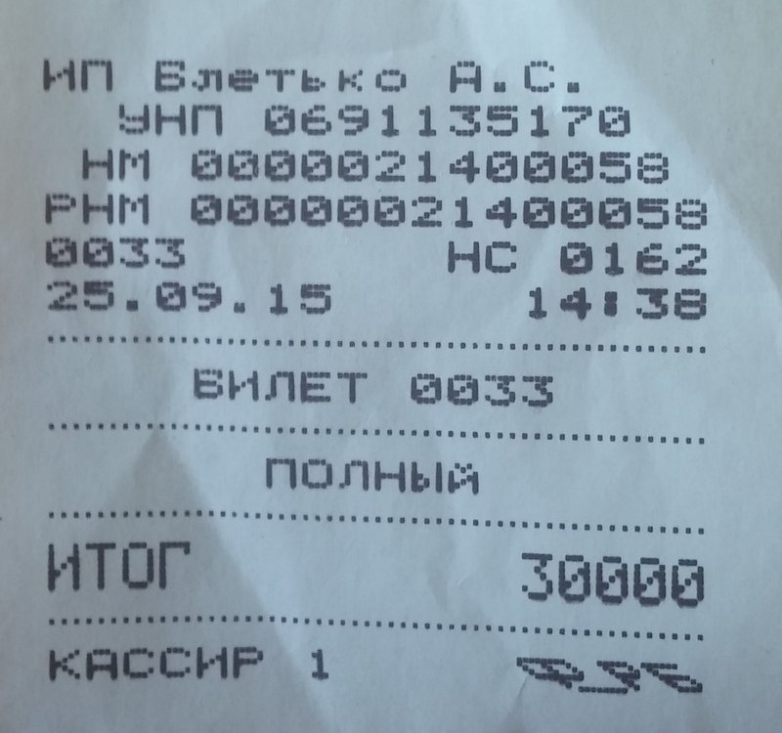
Документы/Фактические расходы/2015-09/2015-09-25 - 30 000р - Транспорт - Ялча_Минск.jpg
