peter-hanzo/KD/Документы/Фактические расходы/2015-09/2015-09-28 - 23 800р - Транспорт - Минск-Ялча.jpg

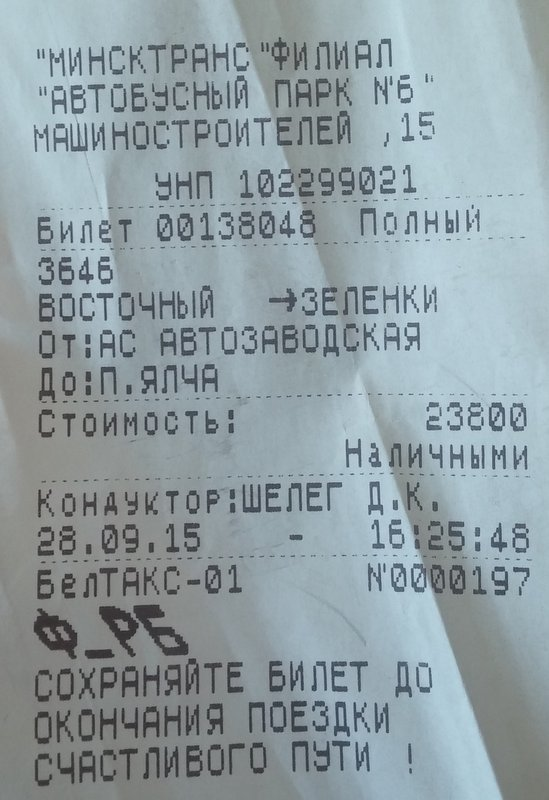
Документы/Фактические расходы/2015-09/2015-09-28 - 23 800р - Транспорт - Минск-Ялча.jpg
