peter-hanzo/KD/Документы/Фактические расходы/2015-10/2015-10-02 - 200 000р - Связь - Мобильный.jpg

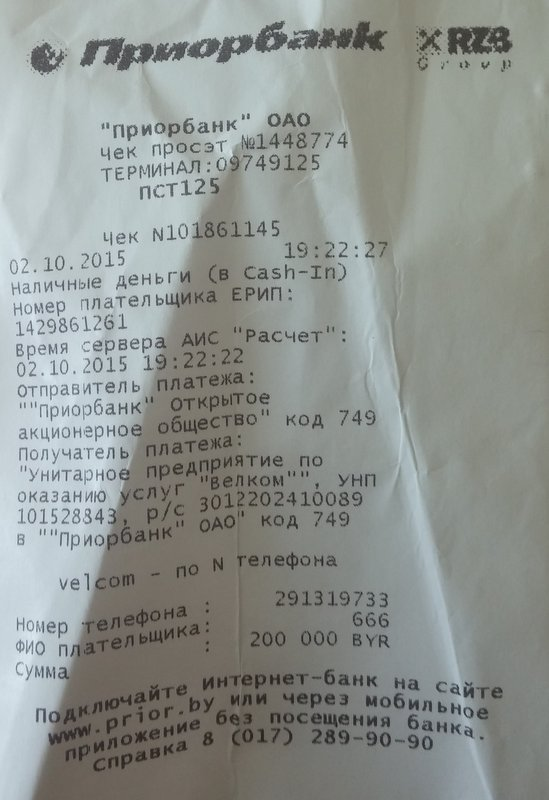
Документы/Фактические расходы/2015-10/2015-10-02 - 200 000р - Связь - Мобильный.jpg
