peter-hanzo/KD/Документы/Фактические расходы/2015-10/2015-10-04 - 731 800р - Крыша - Шурупы и гвозди.jpg

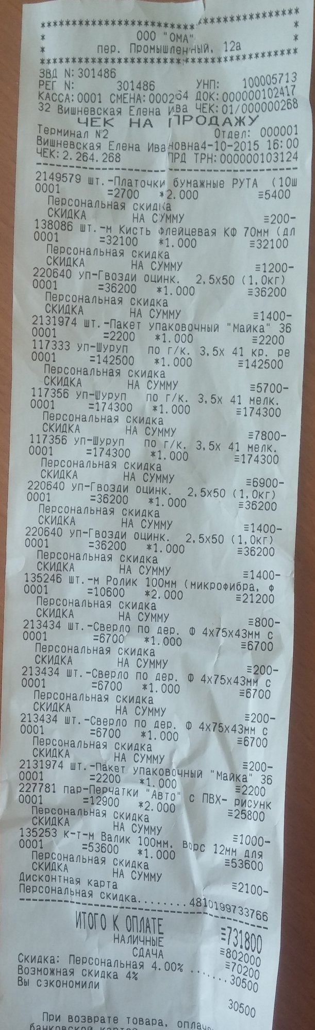
Документы/Фактические расходы/2015-10/2015-10-04 - 731 800р - Крыша - Шурупы и гвозди.jpg
