peter-hanzo/KD/Документы/Фактические расходы/2015-10/2015-10-05 - 607 900р - Каркас - Шурупы и пропитка.jpg

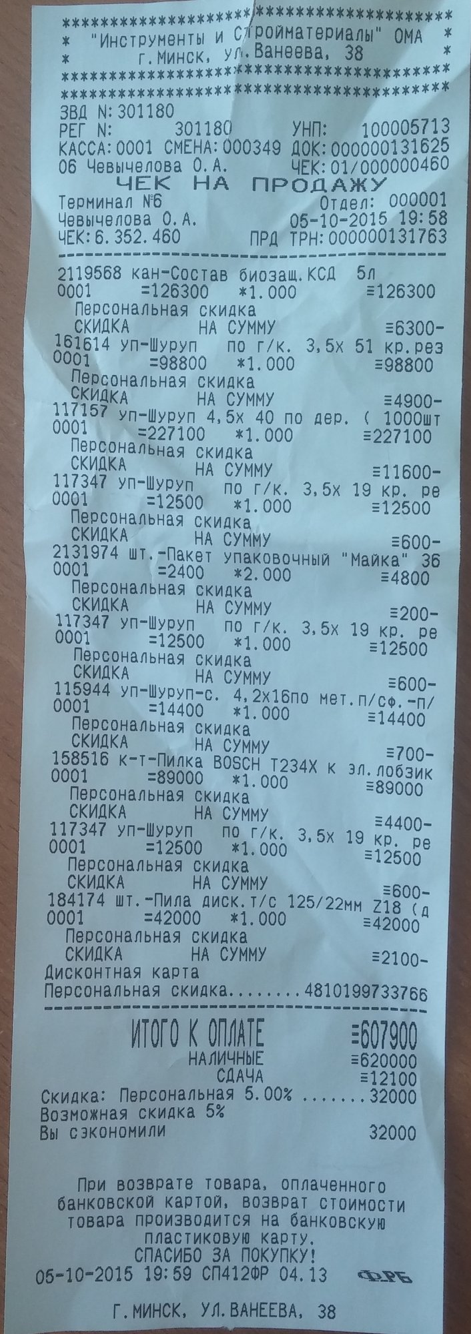
Документы/Фактические расходы/2015-10/2015-10-05 - 607 900р - Каркас - Шурупы и пропитка.jpg
