peter-hanzo/KD/Документы/Фактические расходы/2015-10/2015-10-06 - 2400 000р - Крыша - Подкладочный ковер.jpg

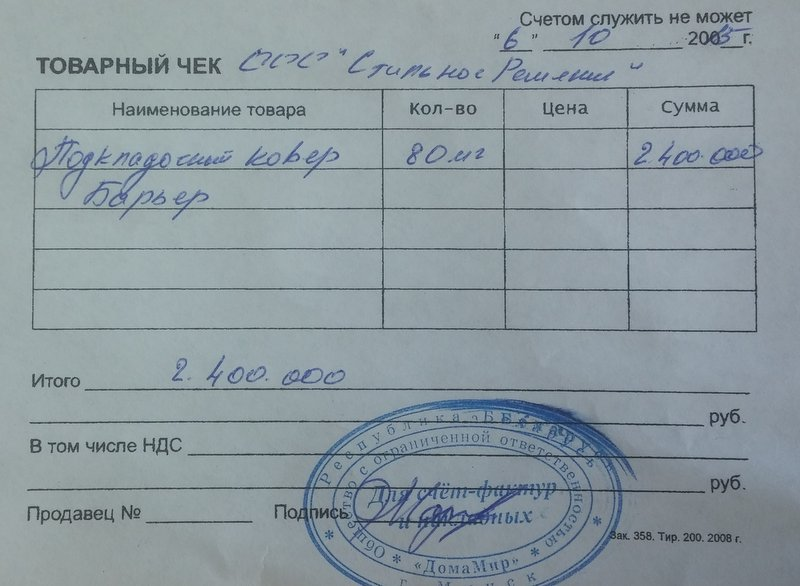
Документы/Фактические расходы/2015-10/2015-10-06 - 2400 000р - Крыша - Подкладочный ковер.jpg
