peter-hanzo/KD/Документы/Фактические расходы/2015-10/2015-10-06 - 3166 500р - Пол - Фанера и мембрана .jpg

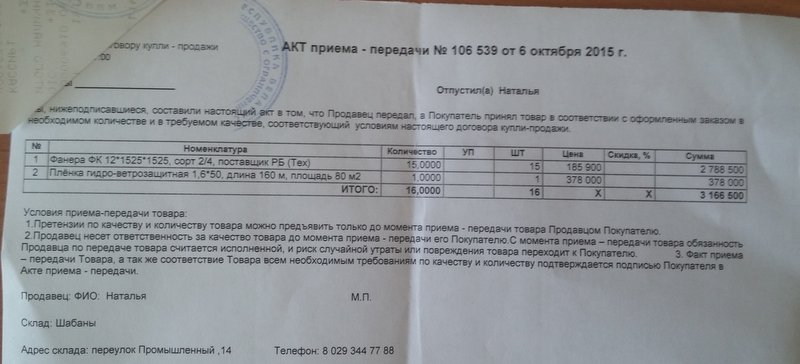
Документы/Фактические расходы/2015-10/2015-10-06 - 3166 500р - Пол - Фанера и мембрана .jpg
