peter-hanzo/KD/Документы/Фактические расходы/2015-10/2015-10-06 - 4972 000р - Стены - Имитация бруса.jpg

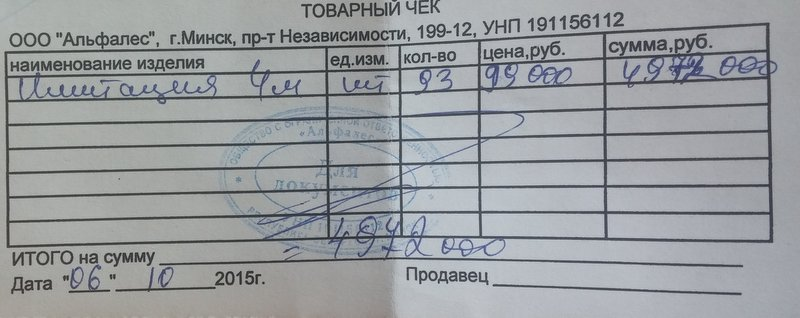
Документы/Фактические расходы/2015-10/2015-10-06 - 4972 000р - Стены - Имитация бруса.jpg
