peter-hanzo/KD/Документы/Фактические расходы/2015-10/2015-10-12 - 718 100р - Крыша - Гвозди+шурупы+инструмент.jpg

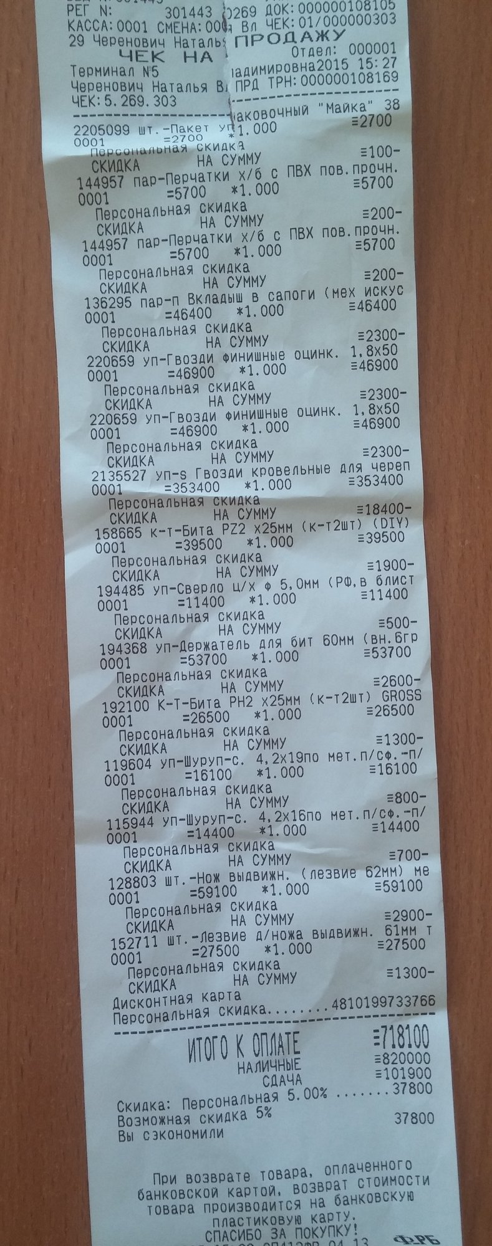
Документы/Фактические расходы/2015-10/2015-10-12 - 718 100р - Крыша - Гвозди+шурупы+инструмент.jpg
