peter-hanzo/KD/Документы/Фактические расходы/2015-10/2015-10-13 - 28 300р - Транспорт - Минск-Ялча.jpg

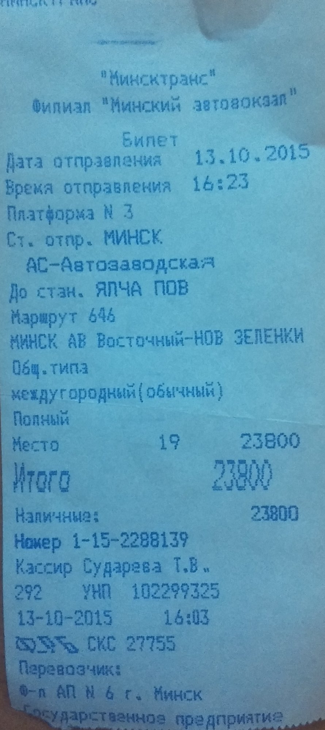
Документы/Фактические расходы/2015-10/2015-10-13 - 28 300р - Транспорт - Минск-Ялча.jpg
