peter-hanzo/KD/Документы/Фактические расходы/2015-10/2015-10-18 - 30 000р - Транспорт - Ялча-Минск.jpg

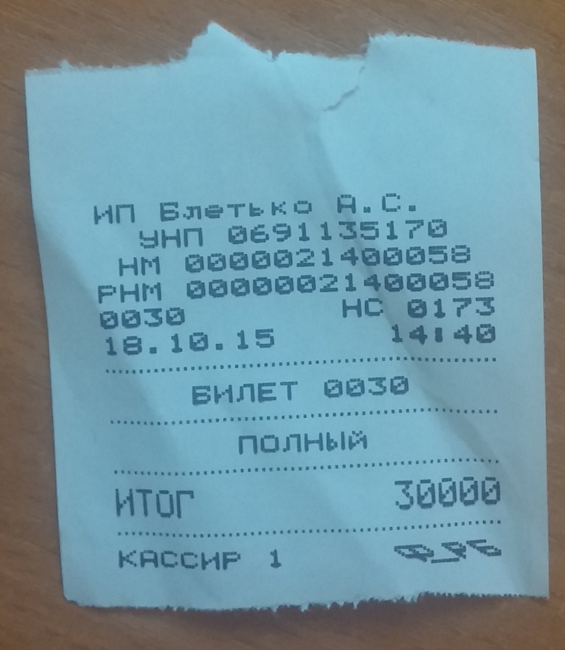
Документы/Фактические расходы/2015-10/2015-10-18 - 30 000р - Транспорт - Ялча-Минск.jpg
