peter-hanzo/KD/Документы/Фактические расходы/2015-10/2015-10-22 - 23 800р - Транспорт - Минск-Ялча.jpg

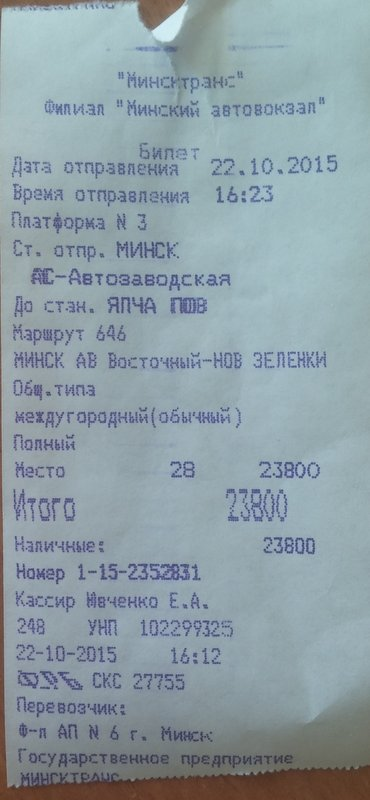
Документы/Фактические расходы/2015-10/2015-10-22 - 23 800р - Транспорт - Минск-Ялча.jpg
