peter-hanzo/KD/Документы/Фактические расходы/2015-10/2015-10-22 - 1038 000р - Стены - Пропитка.jpg

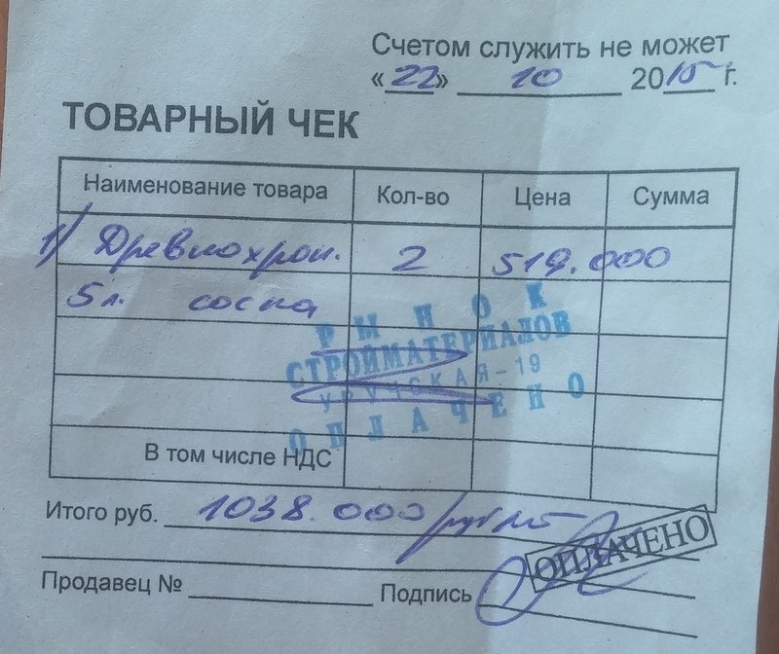
Документы/Фактические расходы/2015-10/2015-10-22 - 1038 000р - Стены - Пропитка.jpg
