peter-hanzo/KD/Документы/Фактические расходы/2015-10/2015-10-29 - 23 800р - Транспорт - Минск-Ялча.jpg.jpg

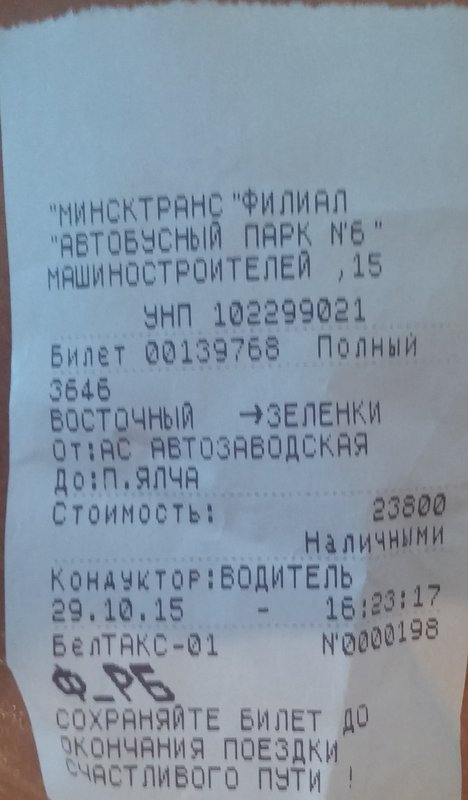
Документы/Фактические расходы/2015-10/2015-10-29 - 23 800р - Транспорт - Минск-Ялча.jpg.jpg
