peter-hanzo/KD/Документы/Фактические расходы/2015-10/2015-10-29 - 525 200р - Стены - Дверь_врезка петель и замка.jpg

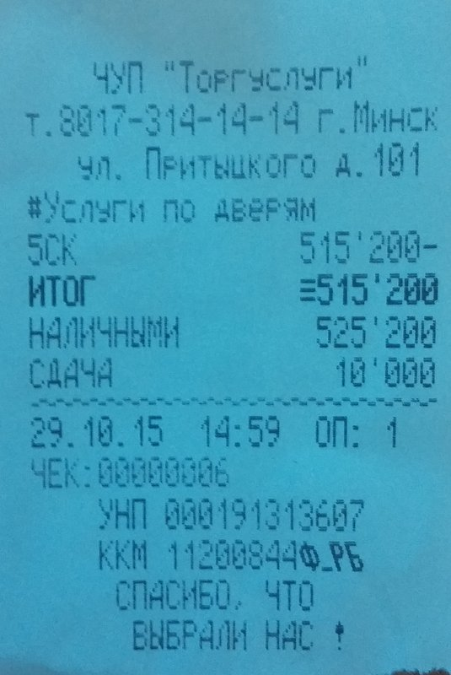
Документы/Фактические расходы/2015-10/2015-10-29 - 525 200р - Стены - Дверь_врезка петель и замка.jpg
