peter-hanzo/KD/Документы/Фактические расходы/2015-10/2015-10-29 - 1625 400р - Стены - входная дверь.jpg

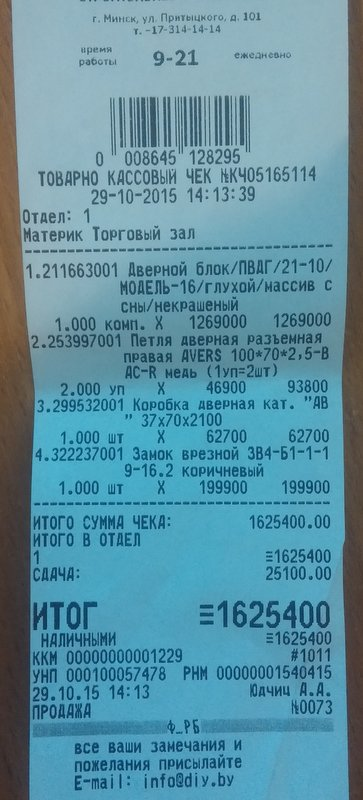
Документы/Фактические расходы/2015-10/2015-10-29 - 1625 400р - Стены - входная дверь.jpg
