peter-hanzo/KD/Документы/Фактические расходы/2015-10/2015-11-01 - 129 000р - Доставка - аренда прицепа.jpg

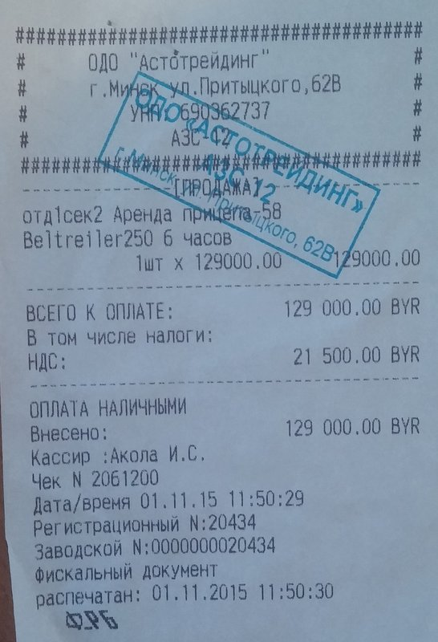
Документы/Фактические расходы/2015-10/2015-11-01 - 129 000р - Доставка - аренда прицепа.jpg
