peter-hanzo/KD/Документы/Фактические расходы/2015-10/2015-11-01 - 244 400р - крыша - жесть для отливов.jpg

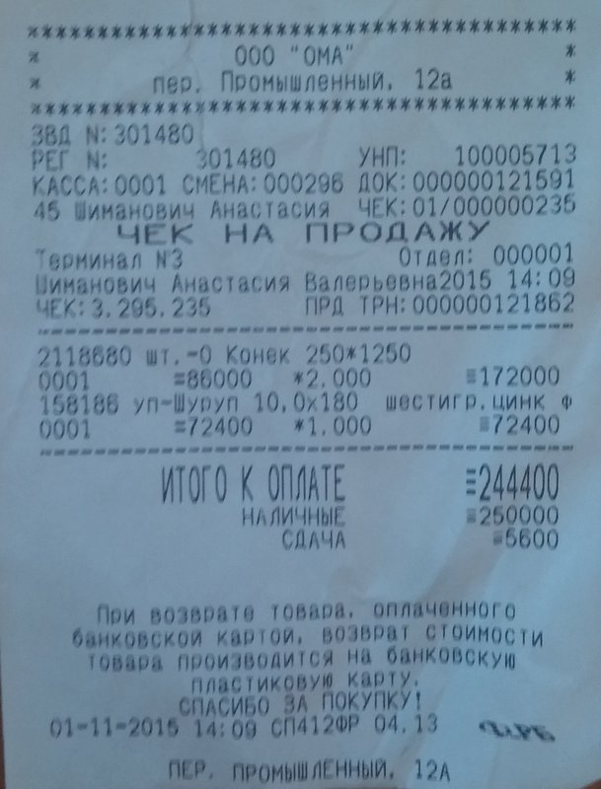
Документы/Фактические расходы/2015-10/2015-11-01 - 244 400р - крыша - жесть для отливов.jpg
