peter-hanzo/KD/Документы/Фактические расходы/2015-10/2015-11-01 - 300 000р - Доставка - бензин.jpg

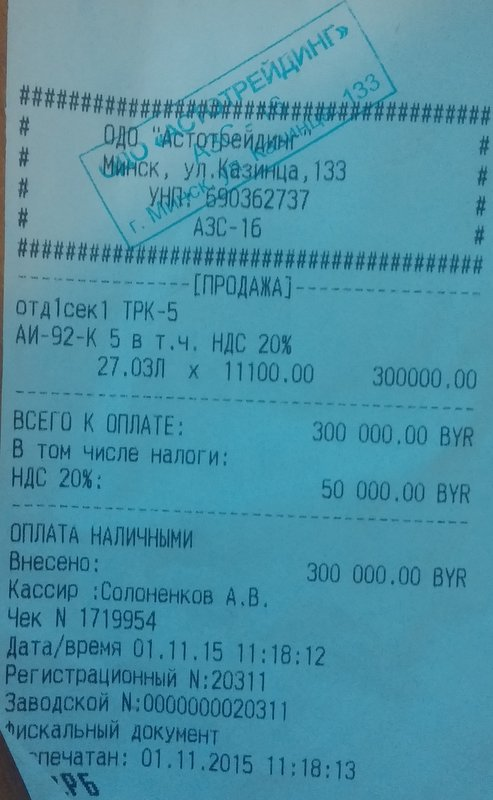
Документы/Фактические расходы/2015-10/2015-11-01 - 300 000р - Доставка - бензин.jpg
