peter-hanzo/KD/Документы/Фактические расходы/2015-10/2015-11-04 - 300 000р - Связь - Мобильный.jpg

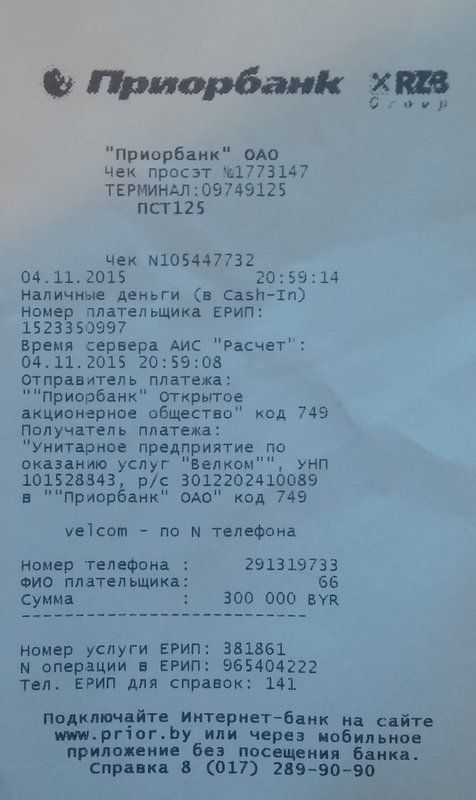
Документы/Фактические расходы/2015-10/2015-11-04 - 300 000р - Связь - Мобильный.jpg
