peter-hanzo/KD/Документы/Фактические расходы/2016-03/2016-03-28 - 200 000р - Доставка - Кабеля для электропроводки.jpg

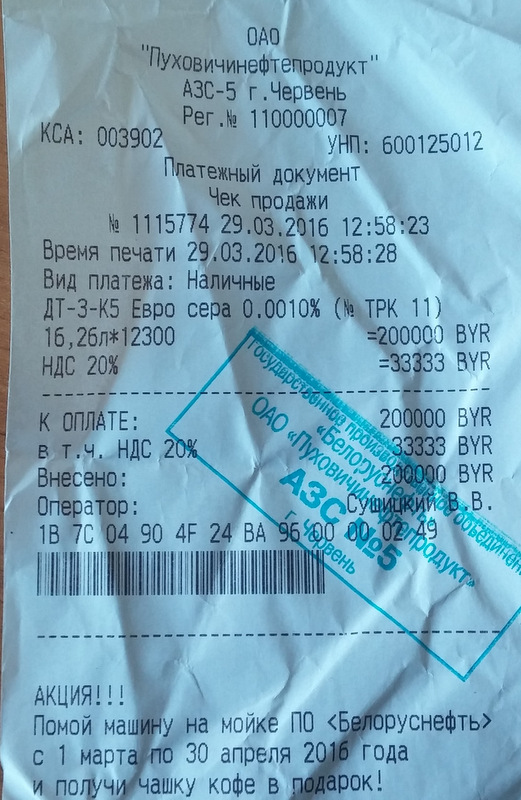
Документы/Фактические расходы/2016-03/2016-03-28 - 200 000р - Доставка - Кабеля для электропроводки.jpg
