peter-hanzo/KD/Документы/Фактические расходы/2016-03/2016-03-28 - 1360 000р - Электричество - Кабеля для электропроводки.jpg

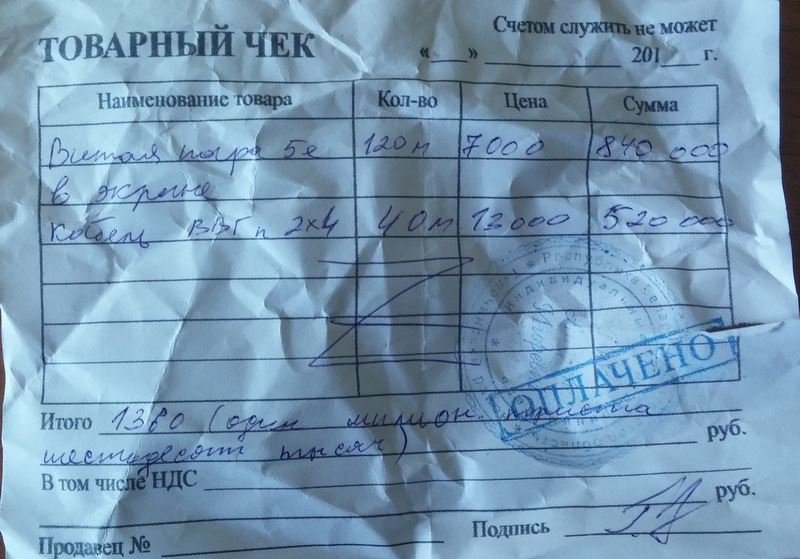
Документы/Фактические расходы/2016-03/2016-03-28 - 1360 000р - Электричество - Кабеля для электропроводки.jpg
