peter-hanzo/KD/Документы/Фактические расходы/2016-04/2016-04-01 - 564 100р - Инструмент - для второго этажа.jpg

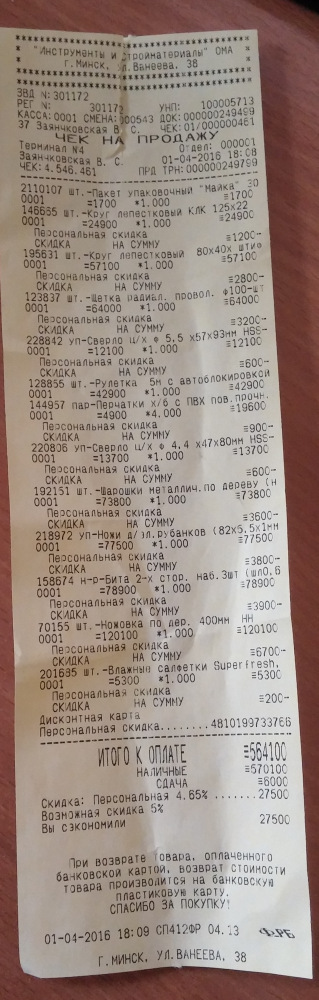
Документы/Фактические расходы/2016-04/2016-04-01 - 564 100р - Инструмент - для второго этажа.jpg
