peter-hanzo/KD/Документы/Фактические расходы/2016-04/2016-04-12 - 330 700р - Инструмент - для веранды часть 1.jpg

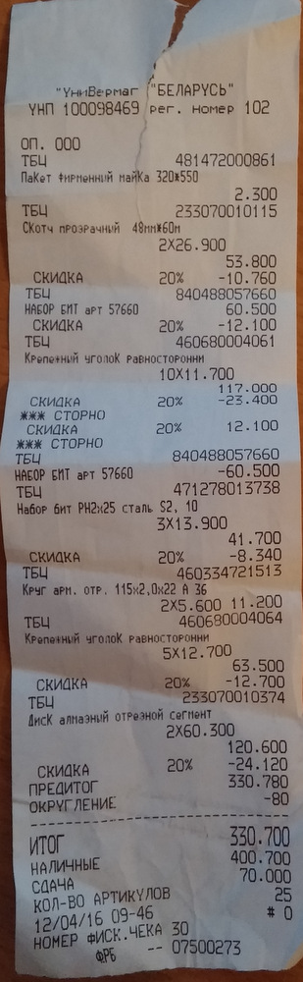
Документы/Фактические расходы/2016-04/2016-04-12 - 330 700р - Инструмент - для веранды часть 1.jpg
