peter-hanzo/KD/Документы/Фактические расходы/2016-04/2016-04-12 - 545 000р - Веранда - арматура.jpg

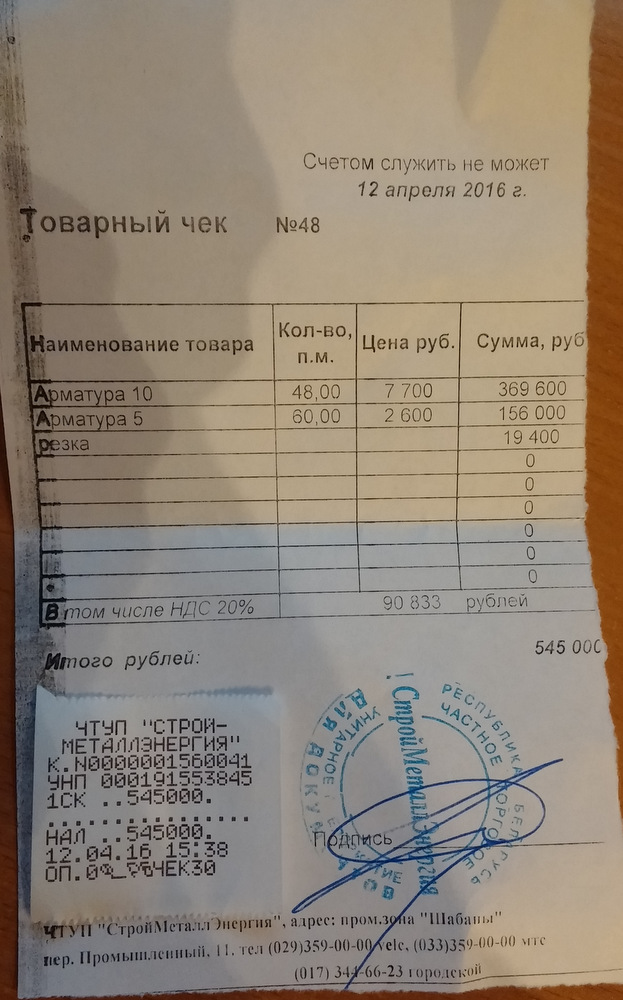
Документы/Фактические расходы/2016-04/2016-04-12 - 545 000р - Веранда - арматура.jpg
