peter-hanzo/KD/Документы/Фактические расходы/2016-04/2016-04-12 - 7240 100р - Веранда - пиломатериалы.jpg

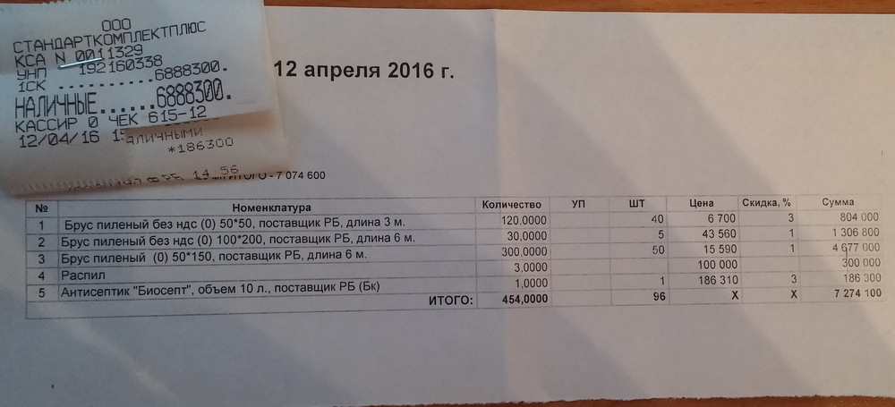
Документы/Фактические расходы/2016-04/2016-04-12 - 7240 100р - Веранда - пиломатериалы.jpg
