peter-hanzo/KD/Документы/Фактические расходы/2016-04/2016-04-12 - 9000 000р - Окна - изготовление окон часть 1.jpg

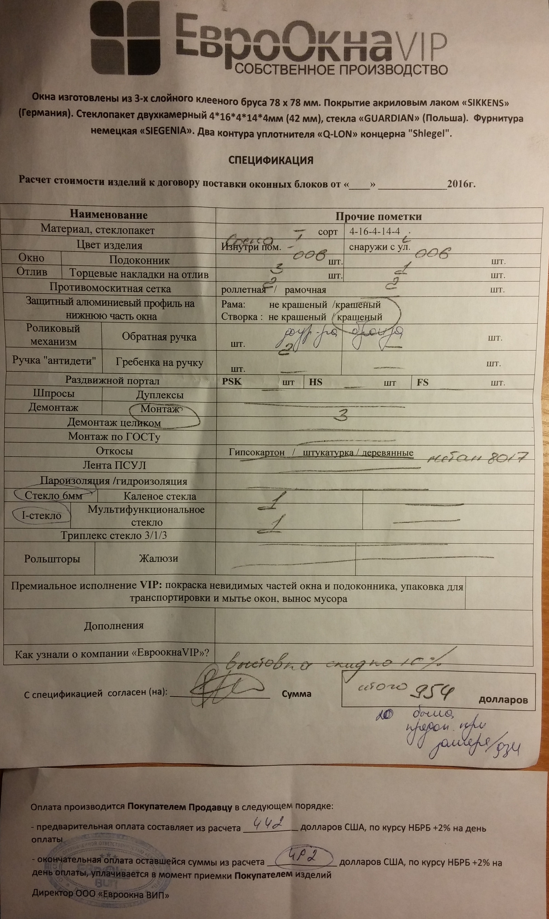
Документы/Фактические расходы/2016-04/2016-04-12 - 9000 000р - Окна - изготовление окон часть 1.jpg
