peter-hanzo/KD/Документы/Фактические расходы/2016-04/2016-04-13 - 197 600р - Веранда - Руберойд на фундамент.jpg

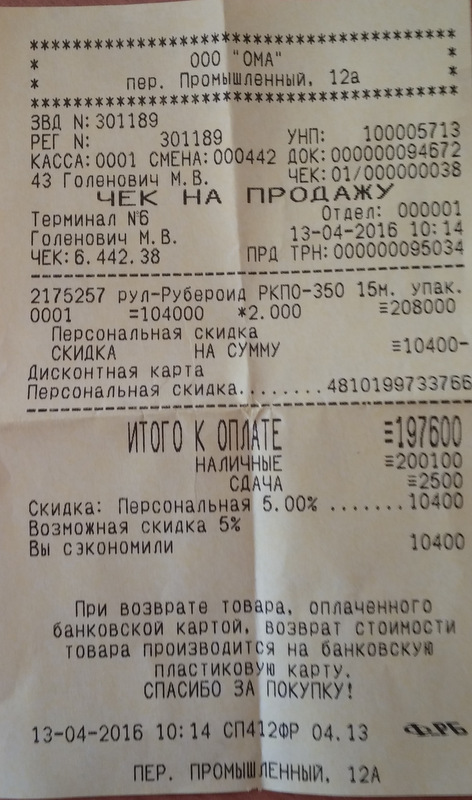
Документы/Фактические расходы/2016-04/2016-04-13 - 197 600р - Веранда - Руберойд на фундамент.jpg
