peter-hanzo/KD/Документы/Фактические расходы/2016-04/2016-04-13 - 329 900р - Веранда - Цемент для фундамента.jpg

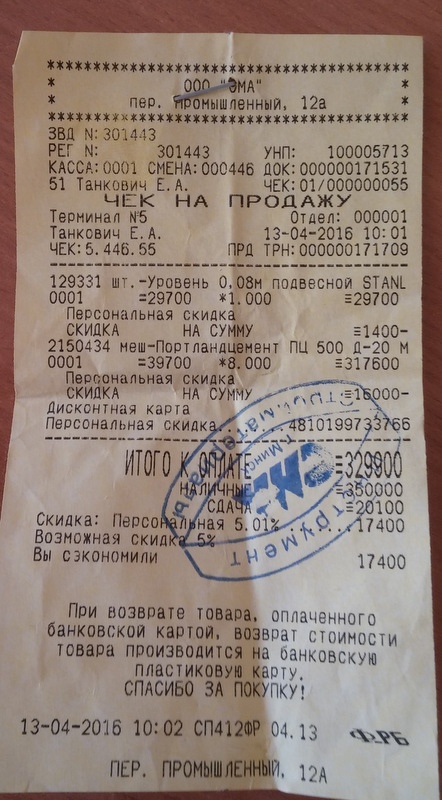
Документы/Фактические расходы/2016-04/2016-04-13 - 329 900р - Веранда - Цемент для фундамента.jpg
