peter-hanzo/KD/Документы/Фактические расходы/2016-04/2016-04-14 - 2040 000р - Водопровод - Кольца для септика_.jpg

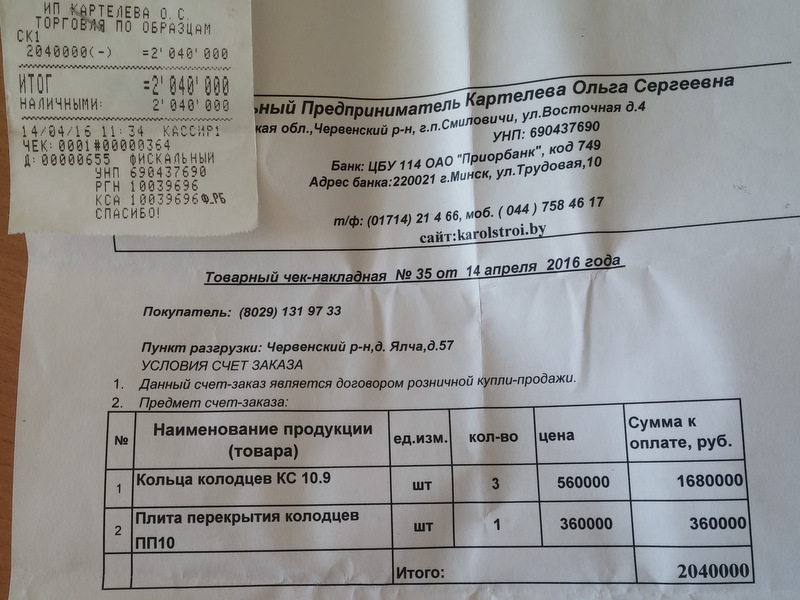
Документы/Фактические расходы/2016-04/2016-04-14 - 2040 000р - Водопровод - Кольца для септика_.jpg
