peter-hanzo/KD/Документы/Фактические расходы/2016-04/2016-04-16 - 592 000р - Инструмент - Пилки и струбцины.jpg

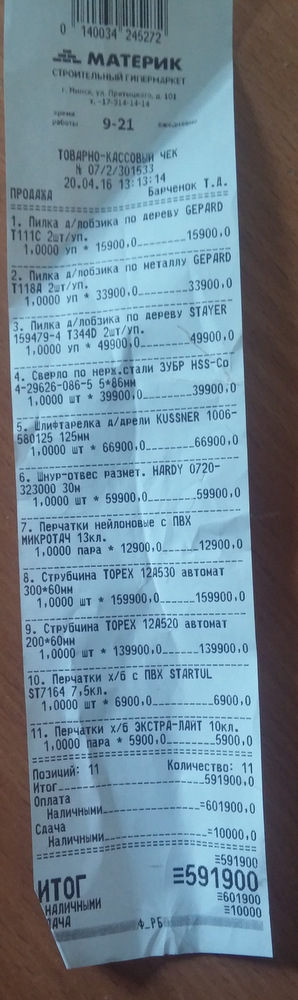
Документы/Фактические расходы/2016-04/2016-04-16 - 592 000р - Инструмент - Пилки и струбцины.jpg
