peter-hanzo/KD/Документы/Фактические расходы/2016-04/2016-04-19 - 3420 000р - Инструмент - Покупка лобзика болгарки рубанка.jpg

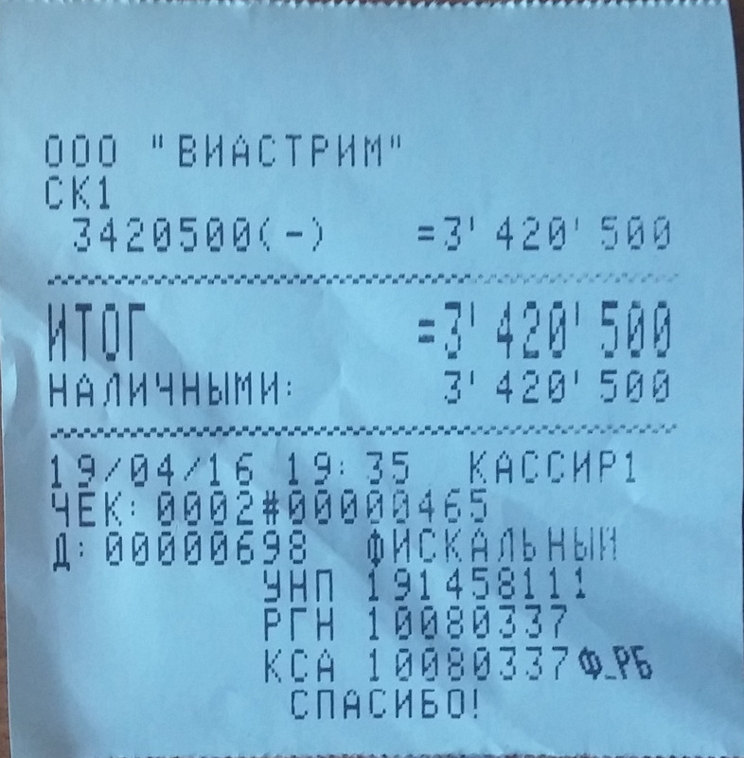
Документы/Фактические расходы/2016-04/2016-04-19 - 3420 000р - Инструмент - Покупка лобзика болгарки рубанка.jpg
