peter-hanzo/KD/Документы/Фактические расходы/2016-04/2016-04-25 - 130 000 - Инструмент - Масло и миксер.jpg

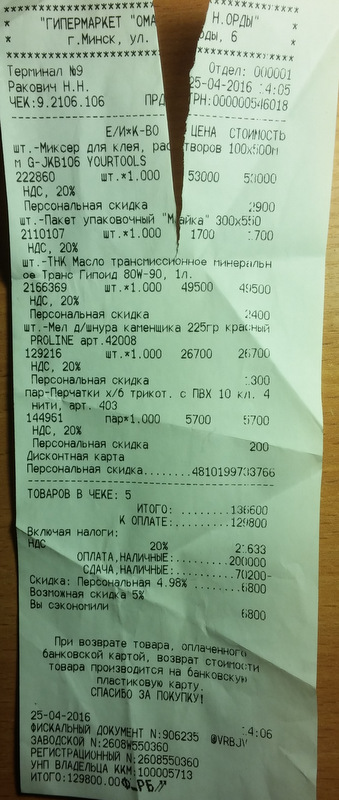
Документы/Фактические расходы/2016-04/2016-04-25 - 130 000 - Инструмент - Масло и миксер.jpg
