peter-hanzo/KD/Документы/Фактические расходы/2016-04/2016-04-25 - 6056 000р - Забор - евроограждение оплата.jpg

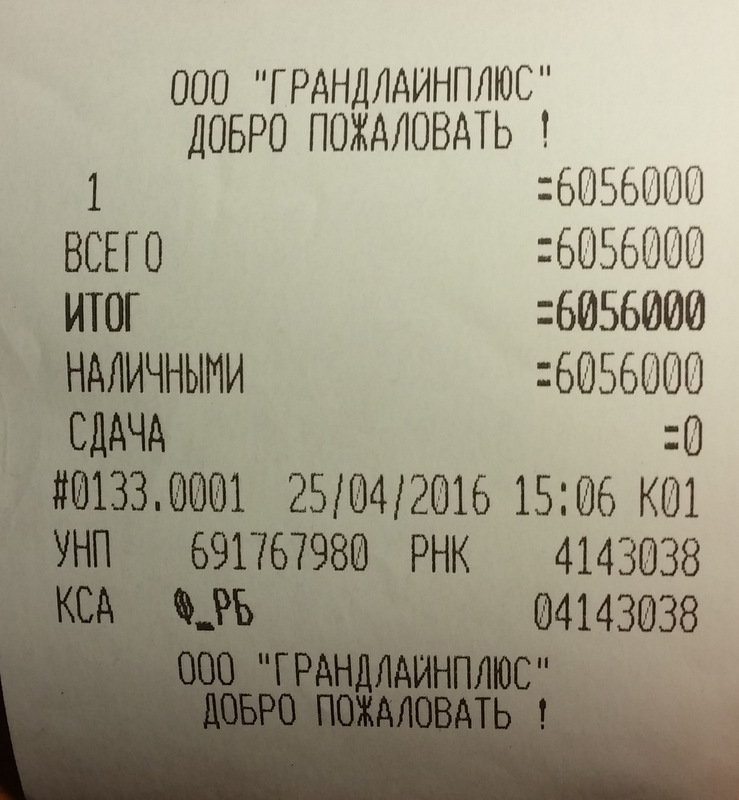
Документы/Фактические расходы/2016-04/2016-04-25 - 6056 000р - Забор - евроограждение оплата.jpg
