peter-hanzo/KD/Документы/Фактические расходы/2016-05/2016-05-10 - 181 400р - Инструмент - круги на болгарку.jpg

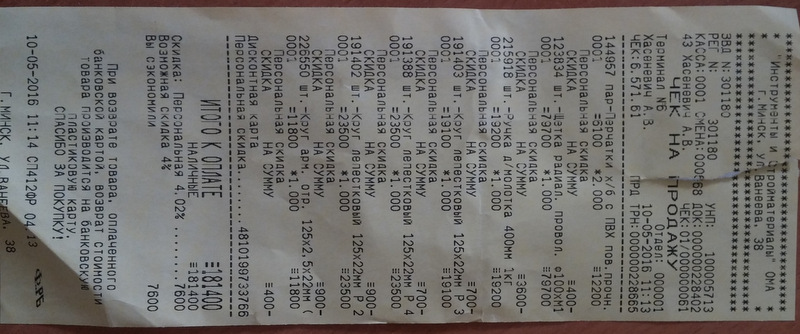
Документы/Фактические расходы/2016-05/2016-05-10 - 181 400р - Инструмент - круги на болгарку.jpg
