peter-hanzo/KD/Документы/Фактические расходы/2016-05/2016-05-10 - 921 800р - Веранда - крепеж.jpg

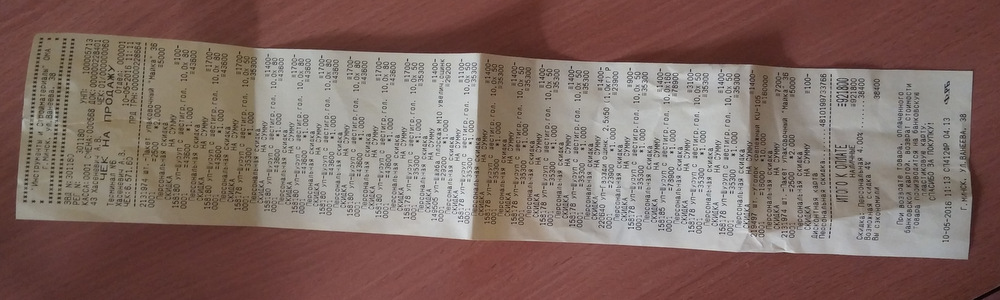
Документы/Фактические расходы/2016-05/2016-05-10 - 921 800р - Веранда - крепеж.jpg
