peter-hanzo/KD/Документы/Фактические расходы/2016-05/2016-05-16 - 158 000р - Веранда - уголок.jpg

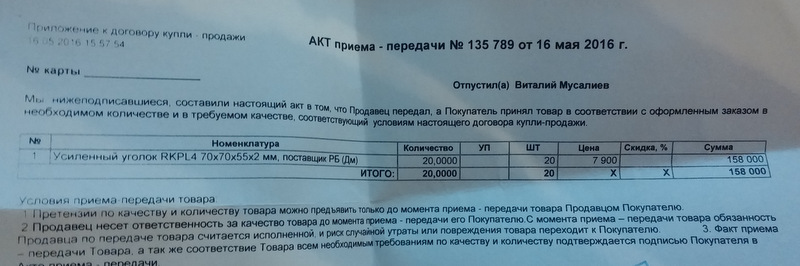
Документы/Фактические расходы/2016-05/2016-05-16 - 158 000р - Веранда - уголок.jpg
