peter-hanzo/KD/Документы/Фактические расходы/2016-05/2016-05-16 - 1120 000р - Веранда - доска на каркас.jpg

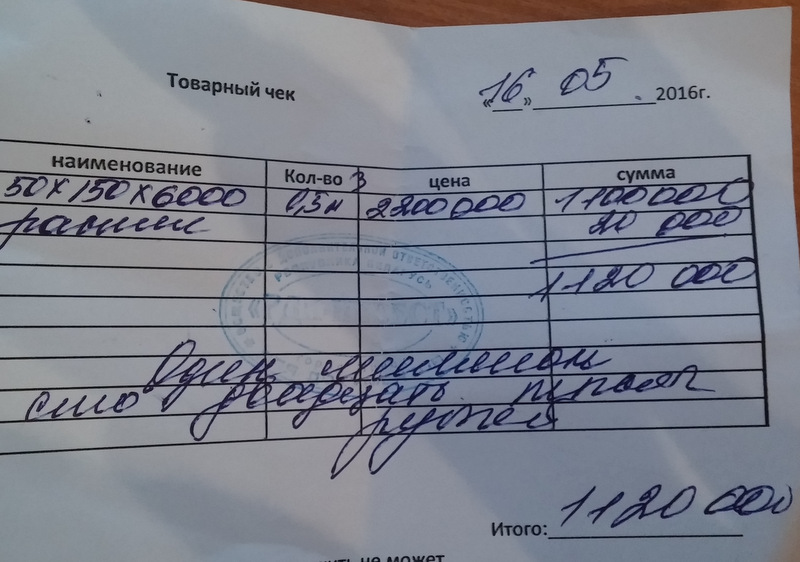
Документы/Фактические расходы/2016-05/2016-05-16 - 1120 000р - Веранда - доска на каркас.jpg
