peter-hanzo/KD/Документы/Фактические расходы/2016-05/2016-05-16 - 1268 000р - Второй этаж - брус и фанера.jpg

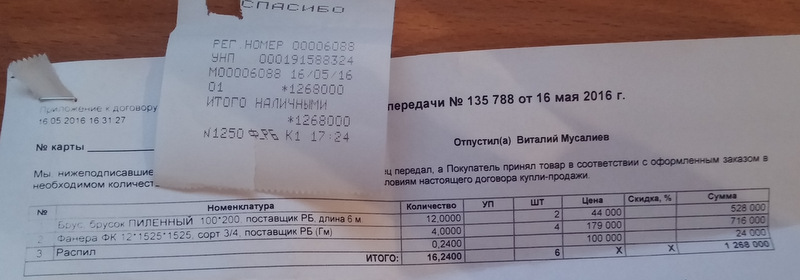
Документы/Фактические расходы/2016-05/2016-05-16 - 1268 000р - Второй этаж - брус и фанера.jpg
