peter-hanzo/KD/Документы/Фактические расходы/2016-05/2016-05-16 - 4480 000р - Веранда - доска для пола и потолка.jpg

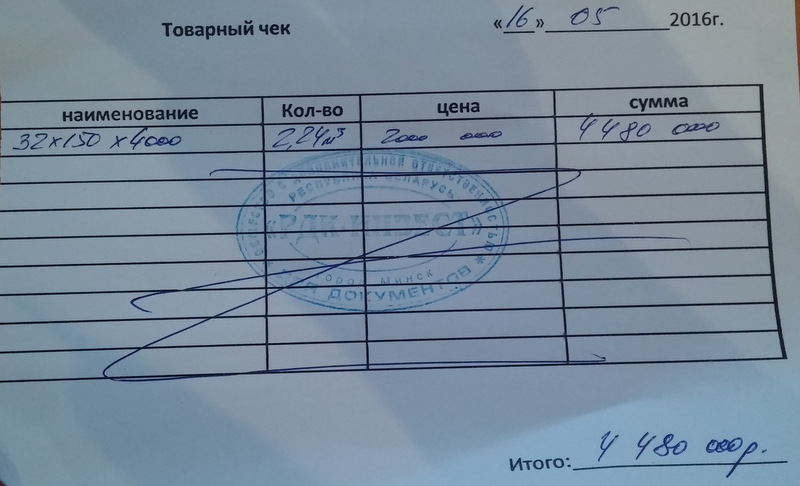
Документы/Фактические расходы/2016-05/2016-05-16 - 4480 000р - Веранда - доска для пола и потолка.jpg
