peter-hanzo/KD/Документы/Фактические расходы/2016-05/2016-05-17 - 152 000р - Веранда - уголок крепежный.jpg

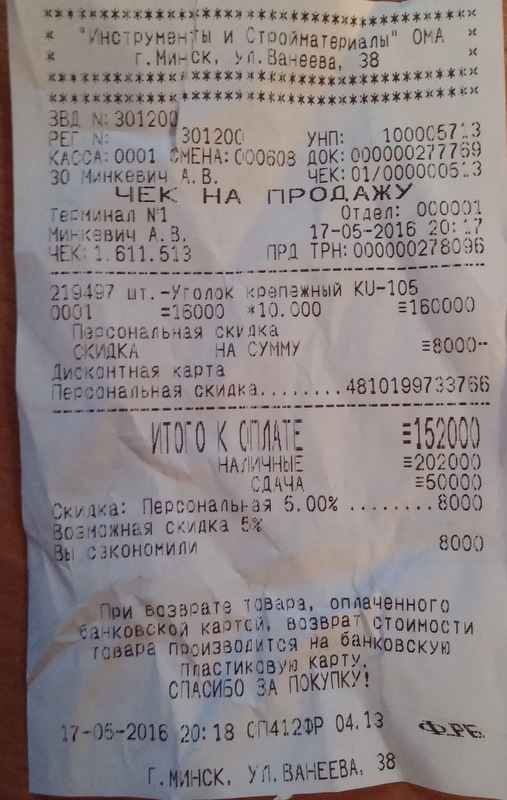
Документы/Фактические расходы/2016-05/2016-05-17 - 152 000р - Веранда - уголок крепежный.jpg
