peter-hanzo/KD/Документы/Фактические расходы/2016-05/2016-05-17 - 403 200р - Веранда - пропитка для пола.jpg

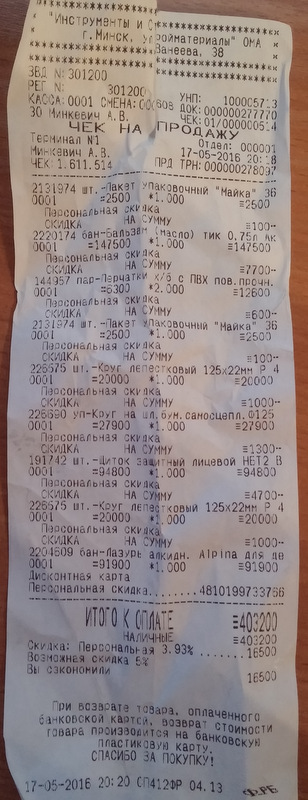
Документы/Фактические расходы/2016-05/2016-05-17 - 403 200р - Веранда - пропитка для пола.jpg
