peter-hanzo/KD/Документы/Фактические расходы/2016-05/2016-05-17 - 1200 000р - Веранда - подкладочный ковер на кровлю=.jpg

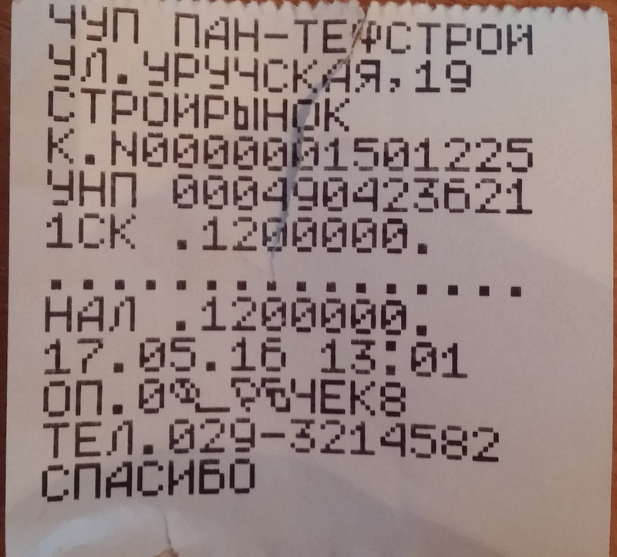
Документы/Фактические расходы/2016-05/2016-05-17 - 1200 000р - Веранда - подкладочный ковер на кровлю=.jpg
