peter-hanzo/KD/Документы/Фактические расходы/2016-05/2016-05-20 - 419 000р - Веранда - крепеж для каркаса.jpg

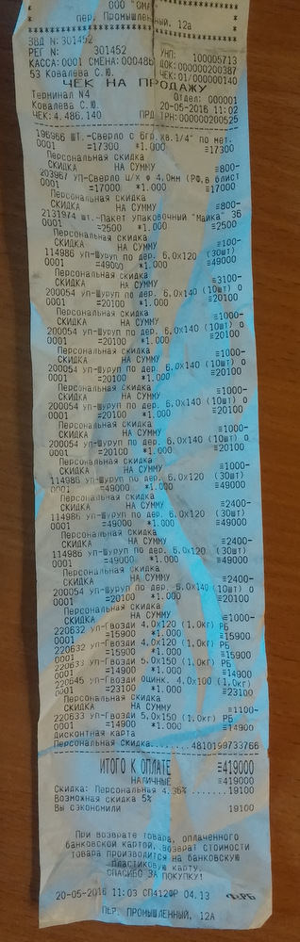
Документы/Фактические расходы/2016-05/2016-05-20 - 419 000р - Веранда - крепеж для каркаса.jpg
