peter-hanzo/KD/Документы/Фактические расходы/2016-05/2016-05-23 - 196 700р - Веранда - расходники для пола.jpg

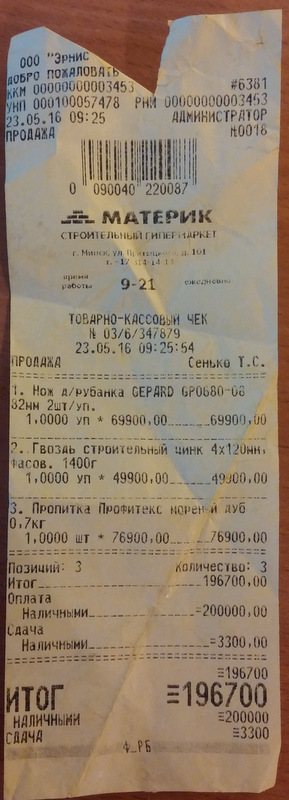
Документы/Фактические расходы/2016-05/2016-05-23 - 196 700р - Веранда - расходники для пола.jpg
