peter-hanzo/KD/Документы/Фактические расходы/2016-05/2016-05-25 - 40 000р - Водопровод - цемет 25кг.jpg

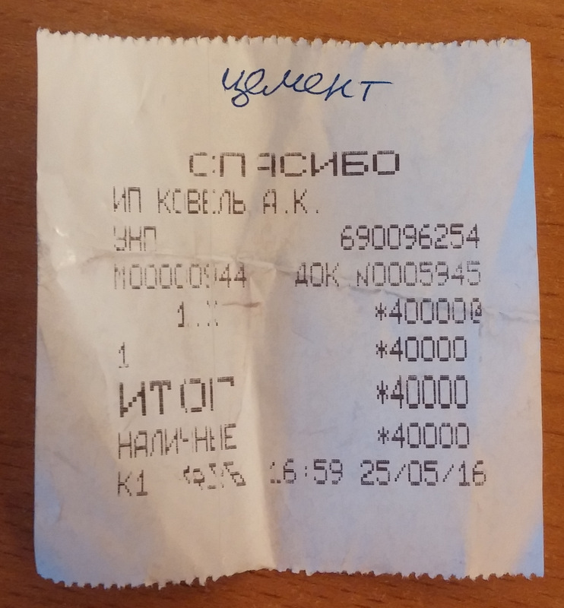
Документы/Фактические расходы/2016-05/2016-05-25 - 40 000р - Водопровод - цемет 25кг.jpg
