peter-hanzo/KD/Документы/Фактические расходы/2016-05/2016-05-25 - 75 000р - Водопровод - сантехника.jpg

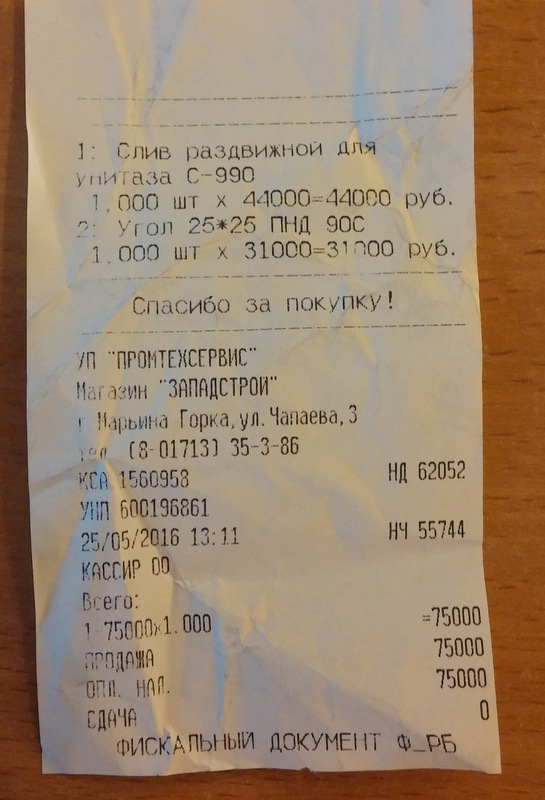
Документы/Фактические расходы/2016-05/2016-05-25 - 75 000р - Водопровод - сантехника.jpg
