peter-hanzo/KD/Документы/Фактические расходы/2016-05/2016-05-25 - 264 400р - Водопровод - фильтр от песка.jpg

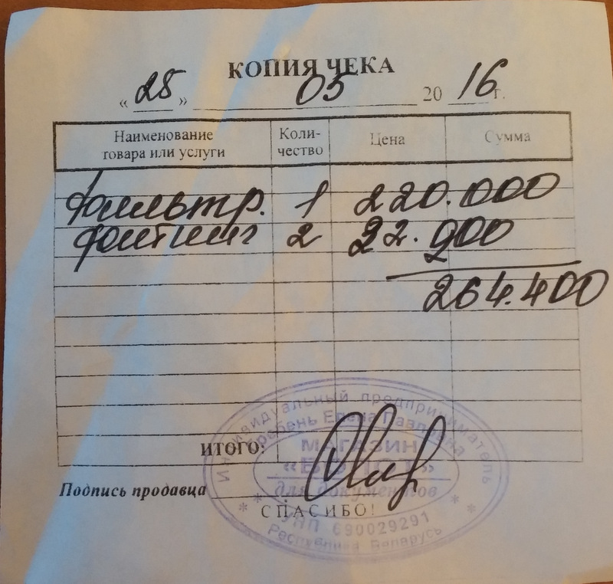
Документы/Фактические расходы/2016-05/2016-05-25 - 264 400р - Водопровод - фильтр от песка.jpg
