peter-hanzo/KD/Документы/Фактические расходы/2016-05/2016-05-25 - 800 200р - Второй этаж - уголки для лаг пола.jpg

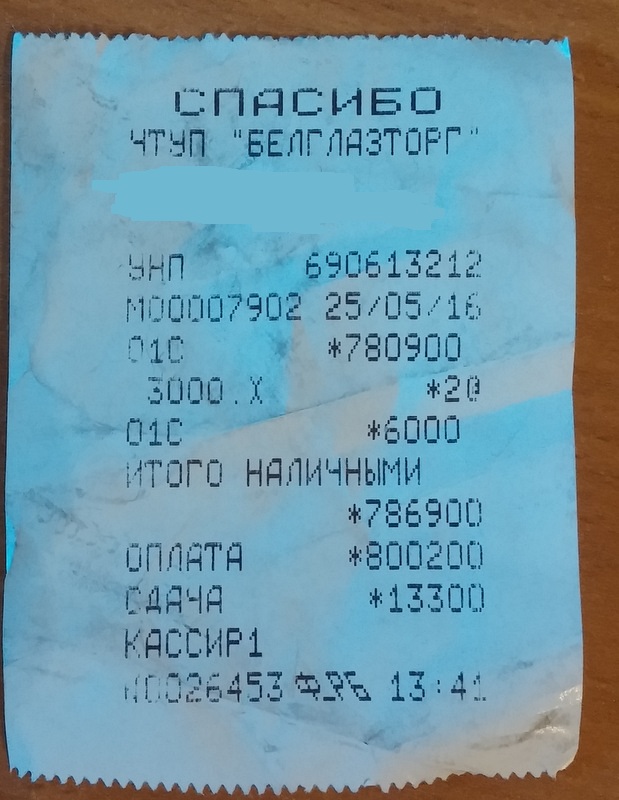
Документы/Фактические расходы/2016-05/2016-05-25 - 800 200р - Второй этаж - уголки для лаг пола.jpg
