peter-hanzo/KD/Документы/Фактические расходы/2016-05/2016-05-25 - 871 700р - Санузел - смеситель.jpg

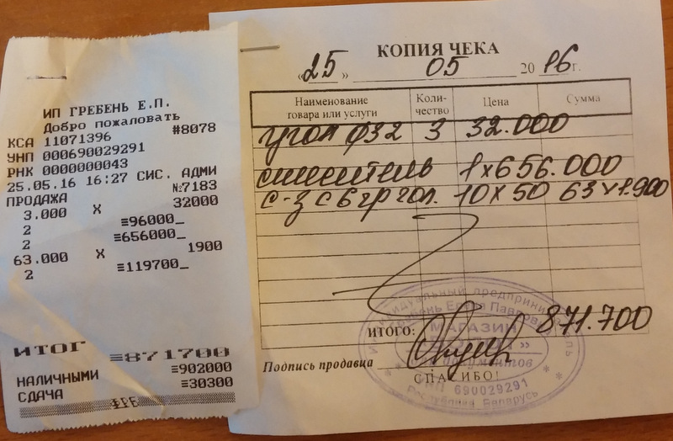
Документы/Фактические расходы/2016-05/2016-05-25 - 871 700р - Санузел - смеситель.jpg
