peter-hanzo/KD/Документы/Фактические расходы/2016-05/2016-05-25 - 1089 500р - Водопровод - коплектующие для  сантехники.jpg

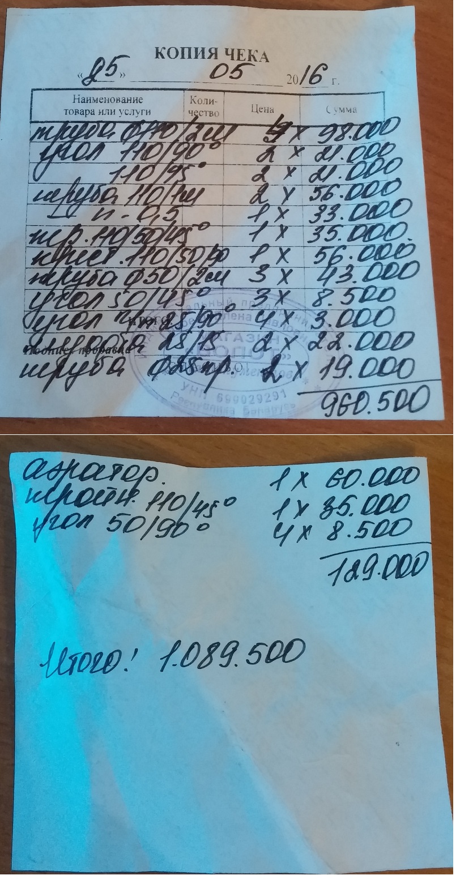
Документы/Фактические расходы/2016-05/2016-05-25 - 1089 500р - Водопровод - коплектующие для сантехники.jpg
