peter-hanzo/KD/Документы/Фактические расходы/2016-05/2016-05-25 - 1922 000р - Водопровод - унитаз и сантехника.jpg

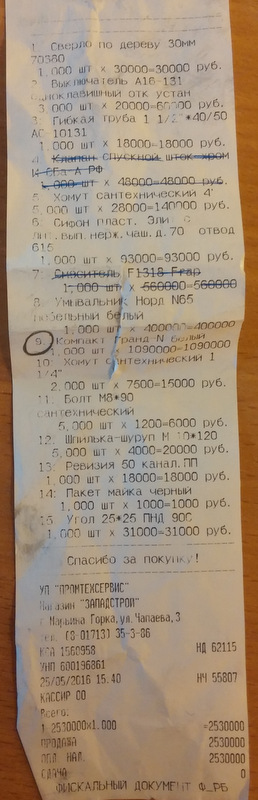
Документы/Фактические расходы/2016-05/2016-05-25 - 1922 000р - Водопровод - унитаз и сантехника.jpg
