peter-hanzo/KD/Документы/Фактические расходы/2016-05/2016-05-25 - 1924 600р - Электричество - провода и автоматы.jpg

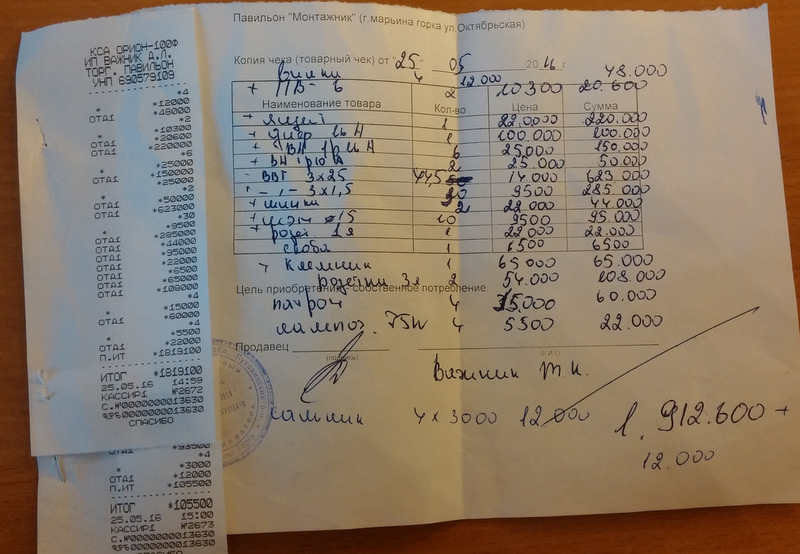
Документы/Фактические расходы/2016-05/2016-05-25 - 1924 600р - Электричество - провода и автоматы.jpg
