peter-hanzo/KD/Документы/Фактические расходы/2016-05/2016-05-25 - 3200 000р - Водопровод - коплектующие для скважины.jpg

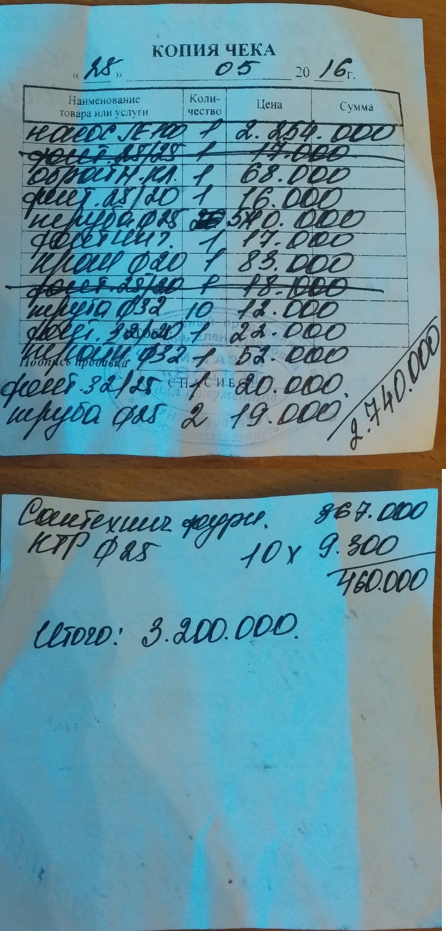
Документы/Фактические расходы/2016-05/2016-05-25 - 3200 000р - Водопровод - коплектующие для скважины.jpg
