peter-hanzo/KD/Документы/Фактические расходы/2016-05/2016-05-27 - 28 000р - Водопровод - комплектующие часть 2.jpg

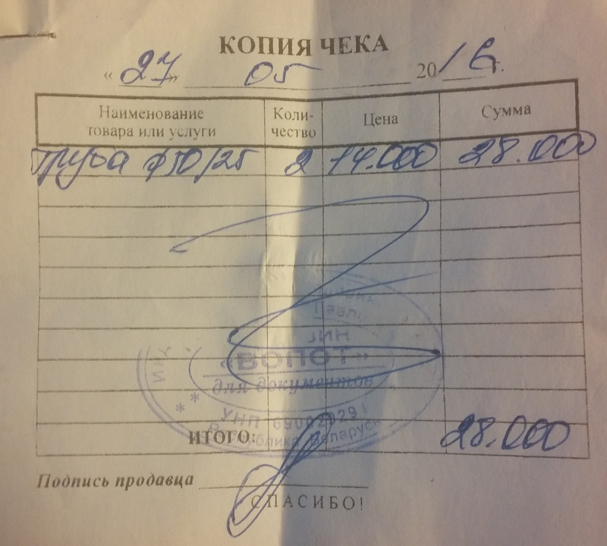
Документы/Фактические расходы/2016-05/2016-05-27 - 28 000р - Водопровод - комплектующие часть 2.jpg
