peter-hanzo/KD/Документы/Фактические расходы/2016-05/2016-05-27 - 185 000р - Электричество - комплектующие часть 3.jpg

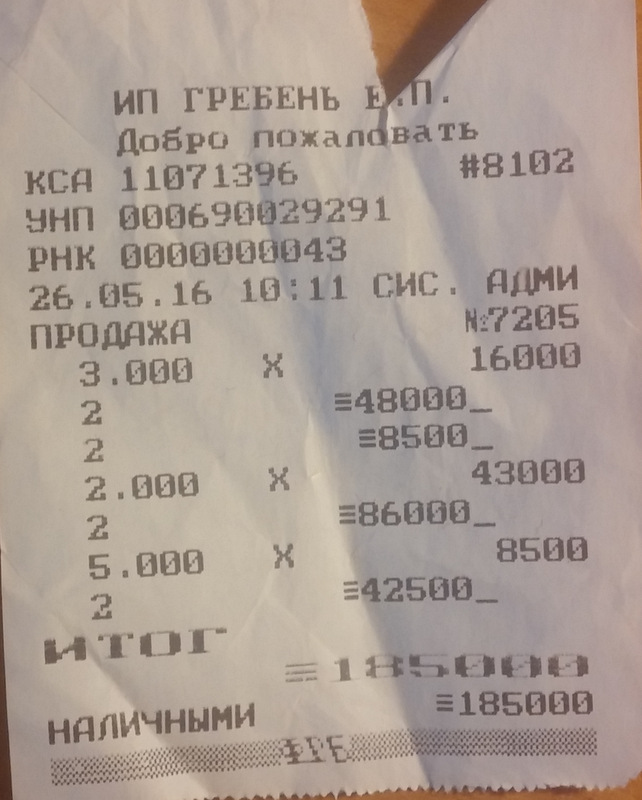
Документы/Фактические расходы/2016-05/2016-05-27 - 185 000р - Электричество - комплектующие часть 3.jpg
