peter-hanzo/KD/Документы/Фактические расходы/2016-05/2016-05-27 - 285 000р - Водопровод - комплектующие часть 3.jpg

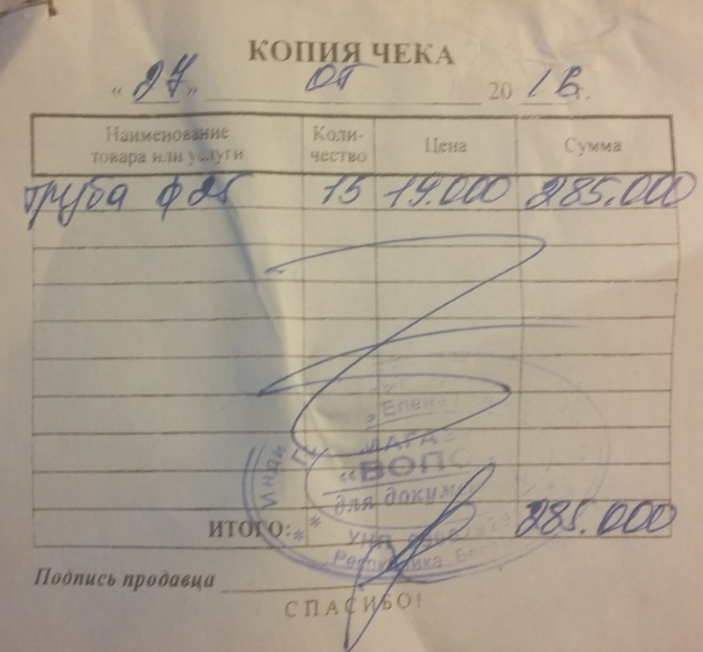
Документы/Фактические расходы/2016-05/2016-05-27 - 285 000р - Водопровод - комплектующие часть 3.jpg
