peter-hanzo/KD/Документы/Фактические расходы/2016-05/2016-05-27 - 434 000р - Водопровод - комплектующие часть 5.jpg

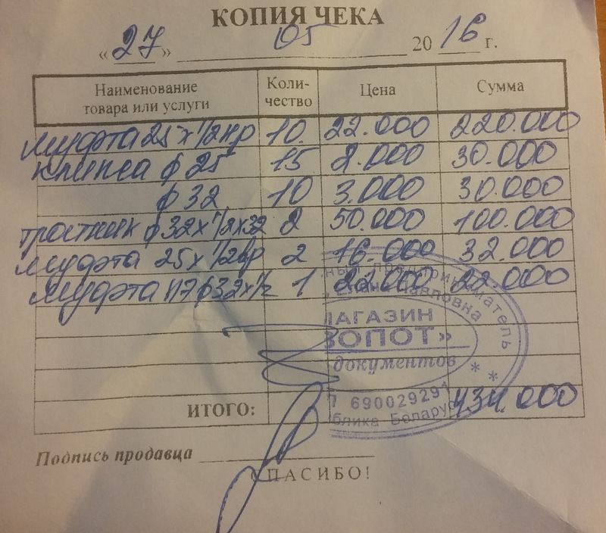
Документы/Фактические расходы/2016-05/2016-05-27 - 434 000р - Водопровод - комплектующие часть 5.jpg
