peter-hanzo/KD/Документы/Фактические расходы/2016-05/2016-05-27 - 525 000р - Водопровод - комплектующие часть 4.jpg

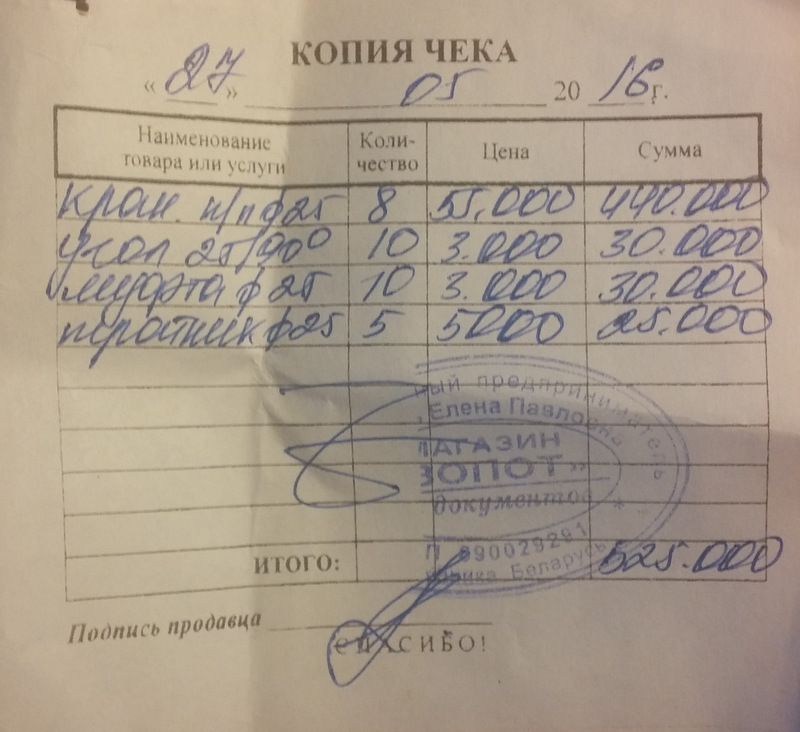
Документы/Фактические расходы/2016-05/2016-05-27 - 525 000р - Водопровод - комплектующие часть 4.jpg
