peter-hanzo/KD/Документы/Фактические расходы/2016-05/2016-05-27 - 855 000р - Электричество - комплектующие часть 2.jpg

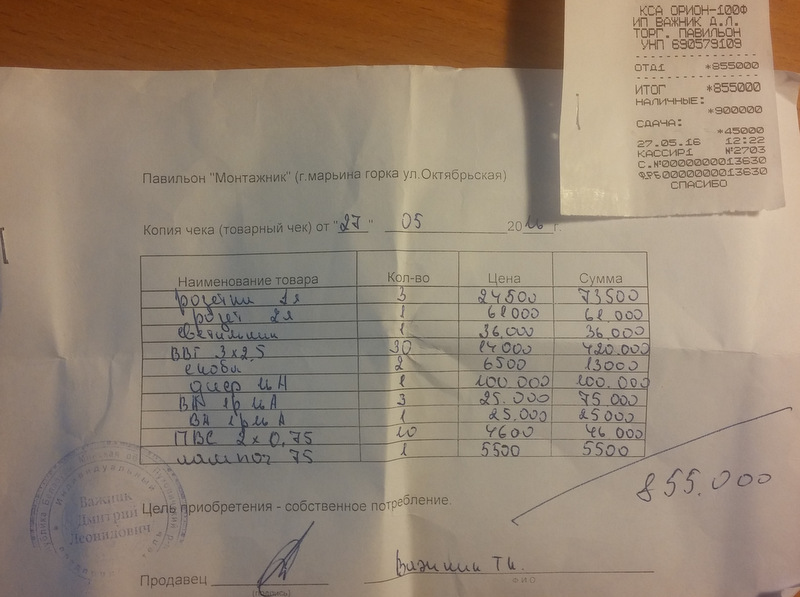
Документы/Фактические расходы/2016-05/2016-05-27 - 855 000р - Электричество - комплектующие часть 2.jpg
