peter-hanzo/KD/Документы/Фактические расходы/2016-05/2016-05-27 - 2140 000р - Электричество - диодная лента.jpg

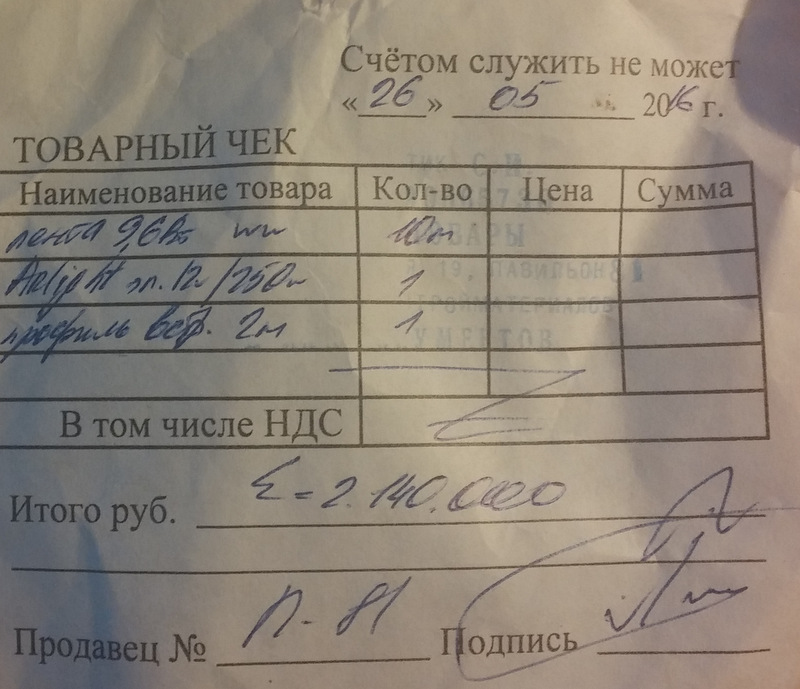
Документы/Фактические расходы/2016-05/2016-05-27 - 2140 000р - Электричество - диодная лента.jpg
