peter-hanzo/KD/Документы/Фактические расходы/2016-05/2016-05-29 - 100 000р - Электричество - светильники.jpg

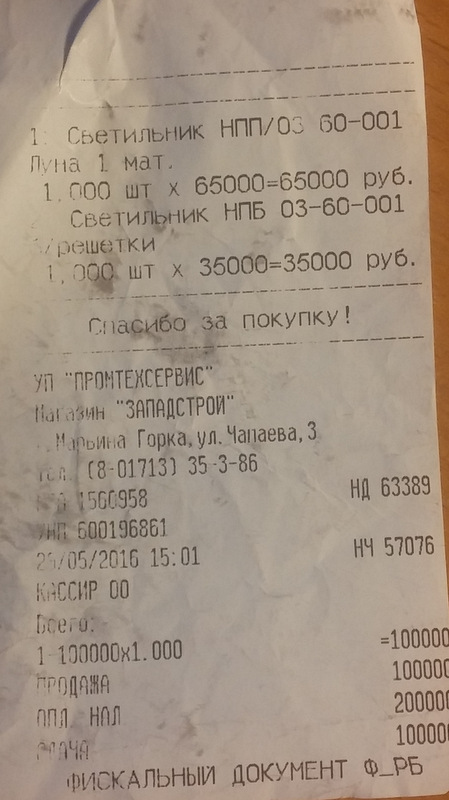
Документы/Фактические расходы/2016-05/2016-05-29 - 100 000р - Электричество - светильники.jpg
