peter-hanzo/KD/Документы/Фактические расходы/2016-05/2016-05-29 - 602 600р - Электричество - вентилятор.jpg

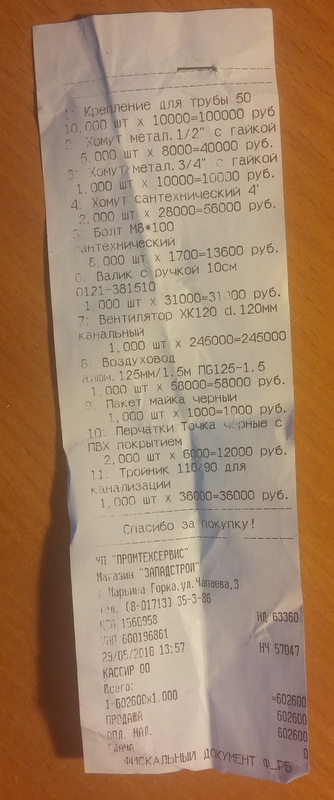
Документы/Фактические расходы/2016-05/2016-05-29 - 602 600р - Электричество - вентилятор.jpg
