peter-hanzo/KD/Документы/Фактические расходы/2016-06/2016-06-03 - 54 800р - Веранда - круги шлифовальные.jpg

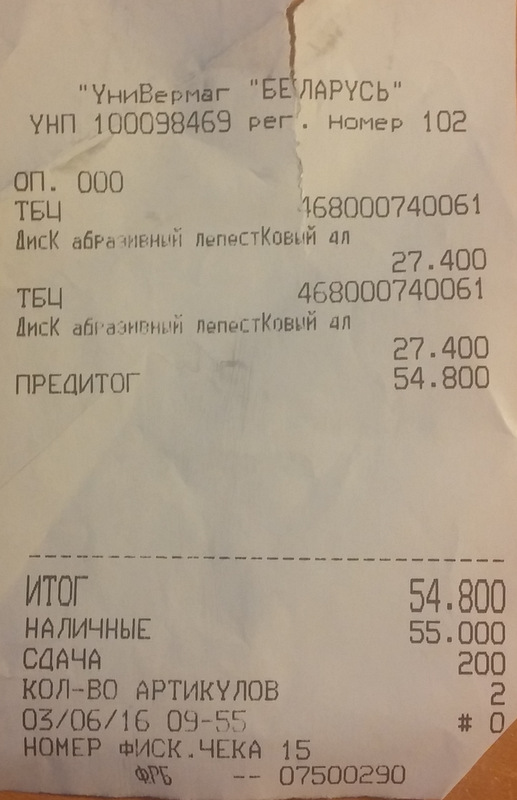
Документы/Фактические расходы/2016-06/2016-06-03 - 54 800р - Веранда - круги шлифовальные.jpg
