peter-hanzo/KD/Документы/Фактические расходы/2016-06/2016-06-18 - 300 000р - Санузел - доставка двери.jpg

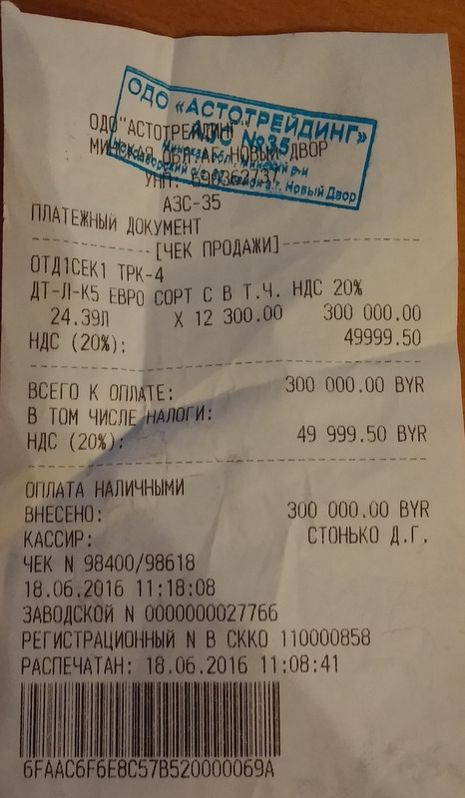
Документы/Фактические расходы/2016-06/2016-06-18 - 300 000р - Санузел - доставка двери.jpg
