peter-hanzo/KD/Документы/Фактические расходы/2016-06/2016-06-18 - 2618 400р - Санузел - дверь и комплектующие.jpg

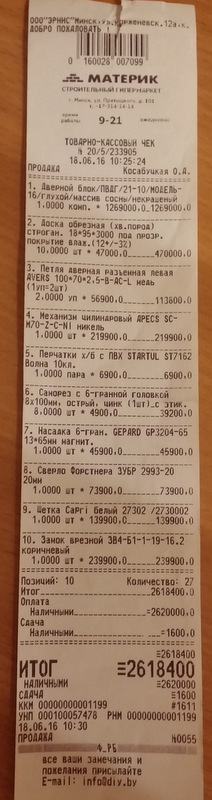
Документы/Фактические расходы/2016-06/2016-06-18 - 2618 400р - Санузел - дверь и комплектующие.jpg
