peter-hanzo/KD/Документы/Фактические расходы/2016-07/2016-07-14 - 30.00 - 15$ - Кровля - консультация у кровельщиков.jpg

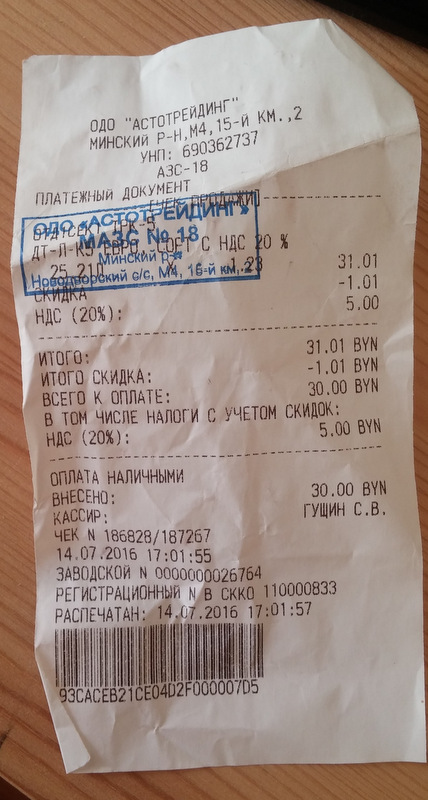
Документы/Фактические расходы/2016-07/2016-07-14 - 30.00 - 15$ - Кровля - консультация у кровельщиков.jpg
