peter-hanzo/KD/Документы/Фактические расходы/2016-07/2016-07-27 - 29.64 - 15$ - Первый этаж - известь гашеная.jpg

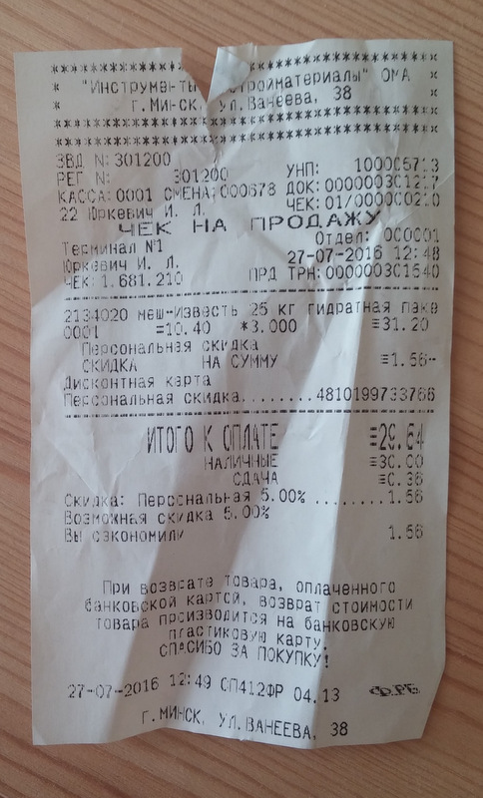
Документы/Фактические расходы/2016-07/2016-07-27 - 29.64 - 15$ - Первый этаж - известь гашеная.jpg
