peter-hanzo/KD/Документы/Фактические расходы/2016-07/2016-07-27 - 39.18 - 20$ - Первый этаж - спанбон для стружки.jpg

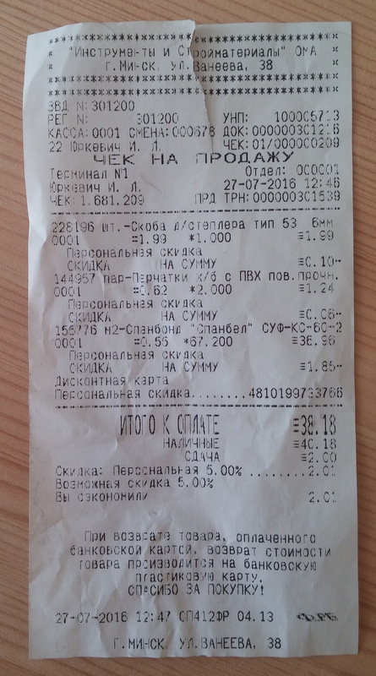
Документы/Фактические расходы/2016-07/2016-07-27 - 39.18 - 20$ - Первый этаж - спанбон для стружки.jpg
