peter-hanzo/KD/Документы/Фактические расходы/2016-07/2016-07-27 - 619.15 - 310$ - Первый этаж - доска пола_.jpg

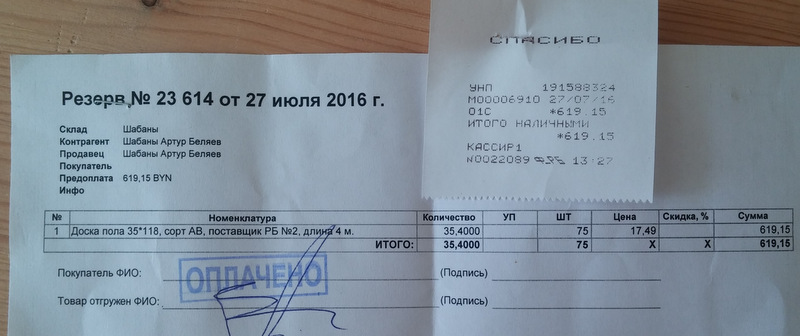
Документы/Фактические расходы/2016-07/2016-07-27 - 619.15 - 310$ - Первый этаж - доска пола_.jpg
