peter-hanzo/KD/Документы/Фактические расходы/2016-07/2016-07-29 - 20.00 - 10$ - Первый этаж - доставка межков для стружки.jpg

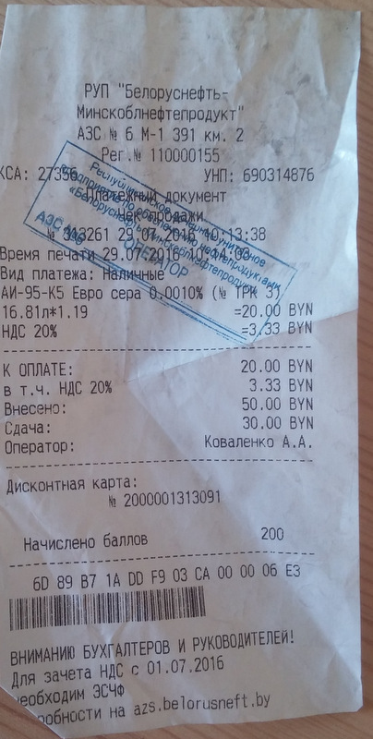
Документы/Фактические расходы/2016-07/2016-07-29 - 20.00 - 10$ - Первый этаж - доставка межков для стружки.jpg
