peter-hanzo/KD/Документы/Фактические расходы/2016-07/2016-07-29 - 541.80 - 272$ - Умный дом - комплектующие ноолайт.jpg

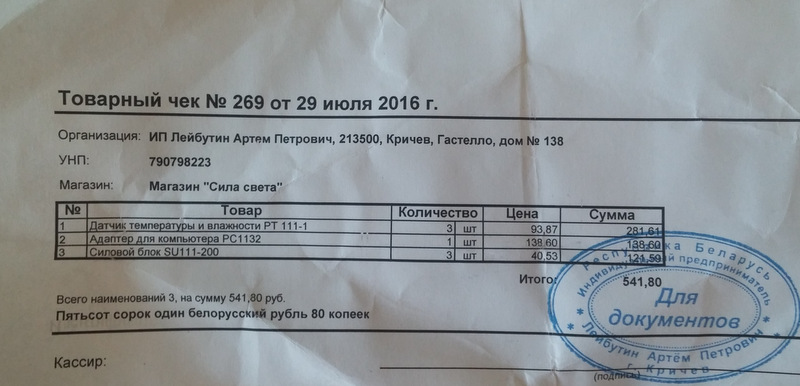
Документы/Фактические расходы/2016-07/2016-07-29 - 541.80 - 272$ - Умный дом - комплектующие ноолайт.jpg
