peter-hanzo/KD/Документы/Фактические расходы/2016-08/2016-08-02 - 38.32 - 19$ - Первый этаж - шурупы.jpg

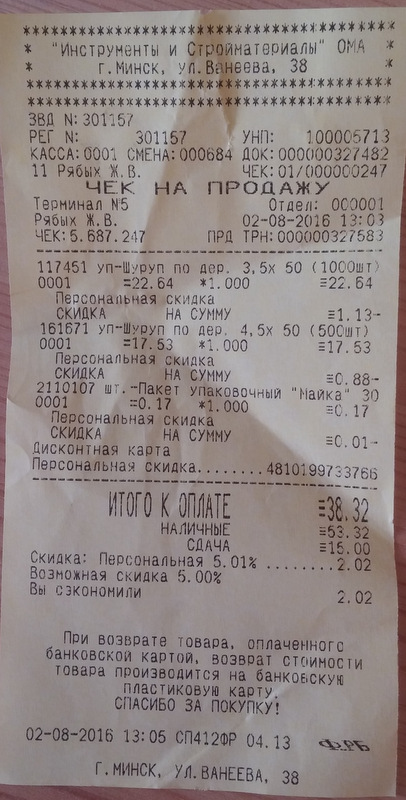
Документы/Фактические расходы/2016-08/2016-08-02 - 38.32 - 19$ - Первый этаж - шурупы.jpg
