peter-hanzo/KD/Документы/Фактические расходы/2016-08/2016-08-16 - 27.24 - 14$ - Умный дом - контакторы.jpg

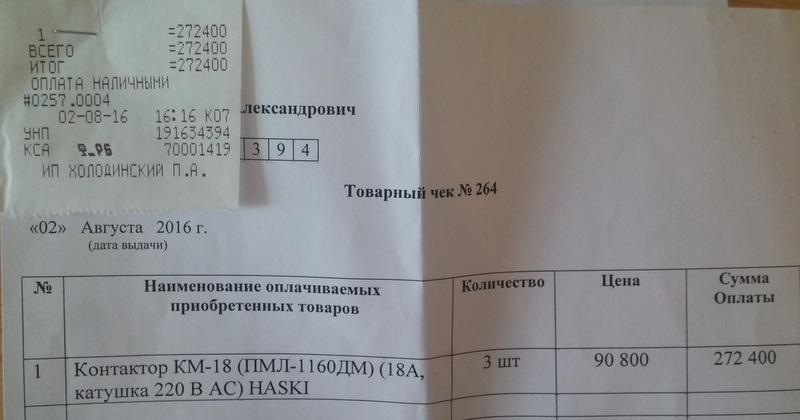
Документы/Фактические расходы/2016-08/2016-08-16 - 27.24 - 14$ - Умный дом - контакторы.jpg
