peter-hanzo/KD/Документы/Фактические расходы/2016-08/2016-08-31 - 38.40 - 20$ - Герметизация - утеплитель первого производителя.jpg

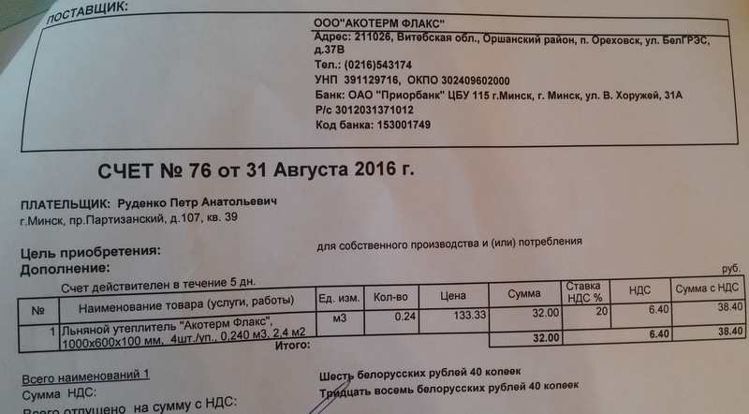
Документы/Фактические расходы/2016-08/2016-08-31 - 38.40 - 20$ - Герметизация - утеплитель первого производителя.jpg
