peter-hanzo/KD/Документы/Фактические расходы/2016-08/2016-08-31 - 167.00 - 85$ - Второй этаж - доска пола+.jpg

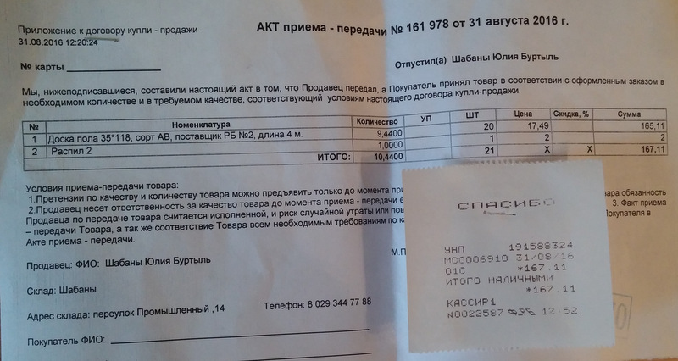
Документы/Фактические расходы/2016-08/2016-08-31 - 167.00 - 85$ - Второй этаж - доска пола+.jpg
