peter-hanzo/KD/Документы/Фактические расходы/2016-09/2016-09-12 - 44.45 - 23$ - Второй этаж - масло и крепления+.jpg

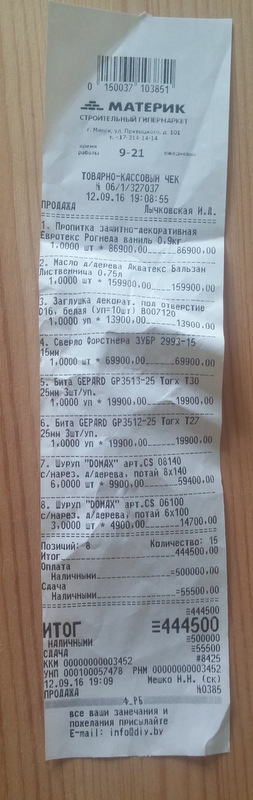
Документы/Фактические расходы/2016-09/2016-09-12 - 44.45 - 23$ - Второй этаж - масло и крепления+.jpg
