peter-hanzo/KD/Документы/Фактические расходы/2016-09/2016-09-13 - 15.99 - 8$ - Второй этаж - масло для потолка+.jpg

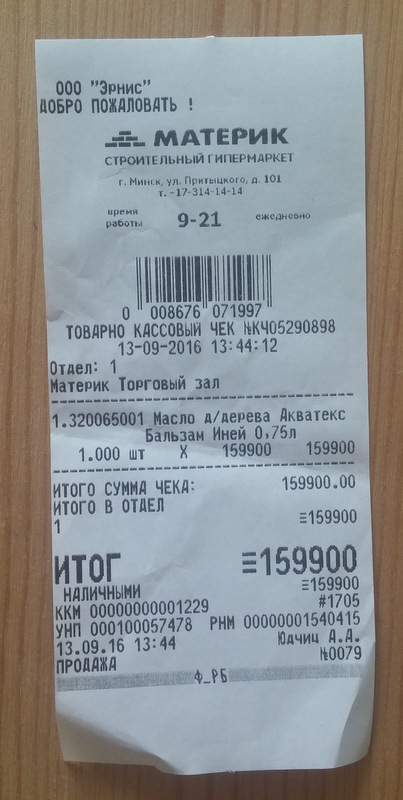
Документы/Фактические расходы/2016-09/2016-09-13 - 15.99 - 8$ - Второй этаж - масло для потолка+.jpg
