peter-hanzo/KD/Документы/Фактические расходы/2016-09/2016-09-20 - 12.93 - 7$ - Умный дом - контактор+.jpg

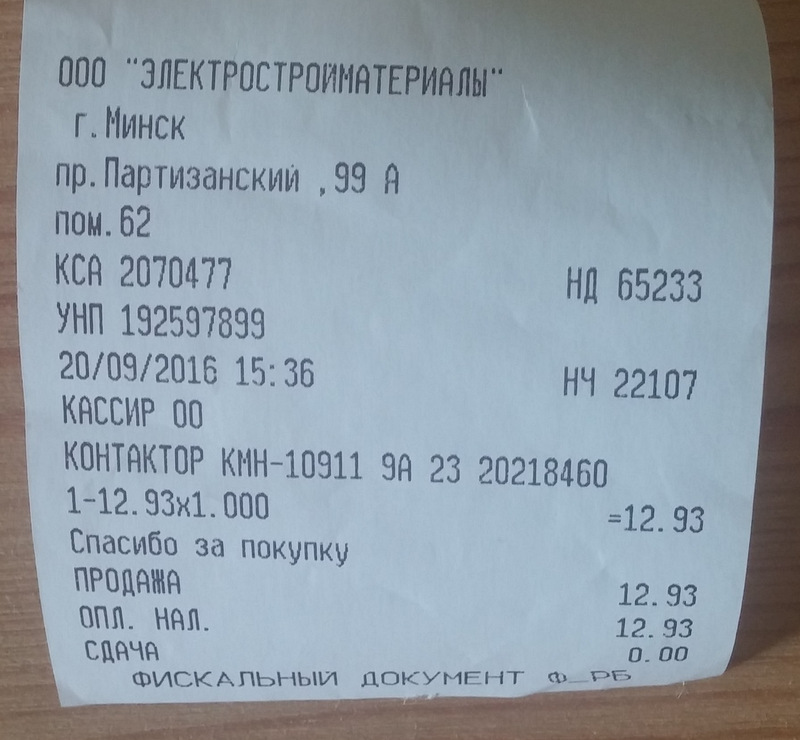
Документы/Фактические расходы/2016-09/2016-09-20 - 12.93 - 7$ - Умный дом - контактор+.jpg
