peter-hanzo/KD/Документы/Фактические расходы/2016-09/2016-09-24 - 12.03 - 6$ - Благоустройство - замок в гараж+.jpg

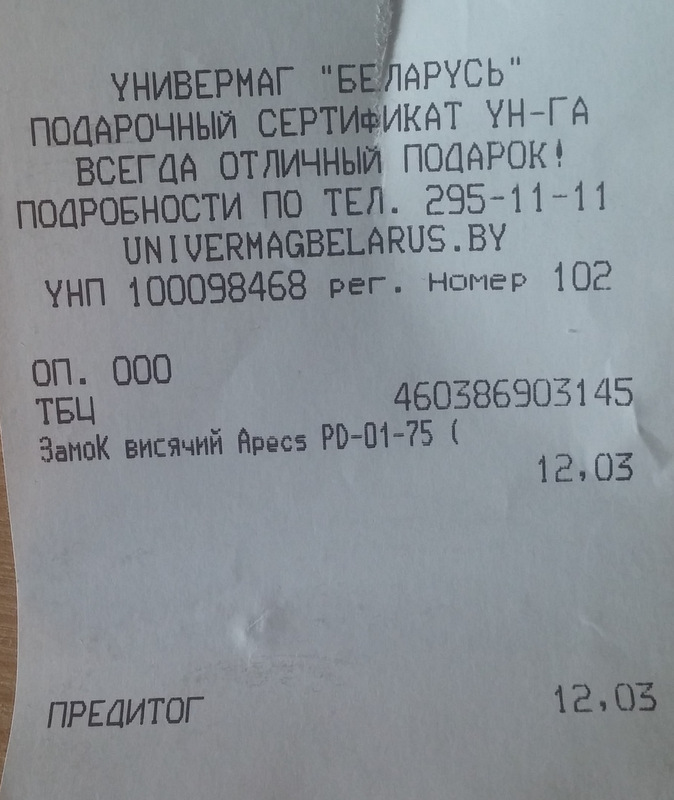
Документы/Фактические расходы/2016-09/2016-09-24 - 12.03 - 6$ - Благоустройство - замок в гараж+.jpg
