peter-hanzo/KD/Документы/Фактические расходы/2017-04/2017-04-07 - 70.47 - 37$ - Второй этаж - Шумоглушитель.jpg

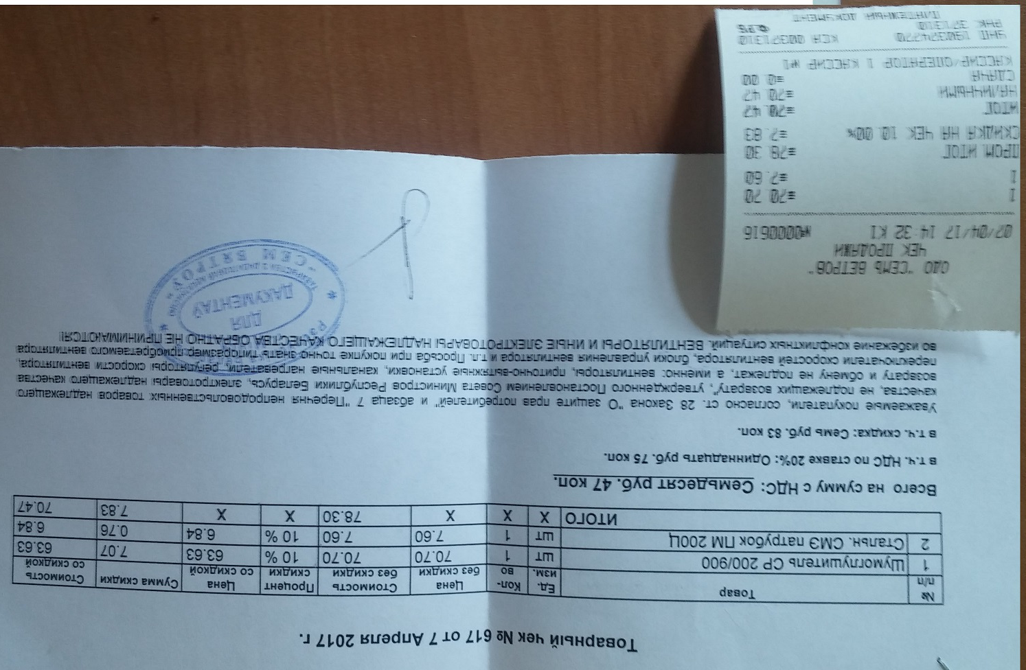
Документы/Фактические расходы/2017-04/2017-04-07 - 70.47 - 37$ - Второй этаж - Шумоглушитель.jpg
