peter-hanzo/KD/Документы/Фактические расходы/2017-04/2017-04-07 - 87.20 - 46$ - Второй этаж - Вентилятор.jpg

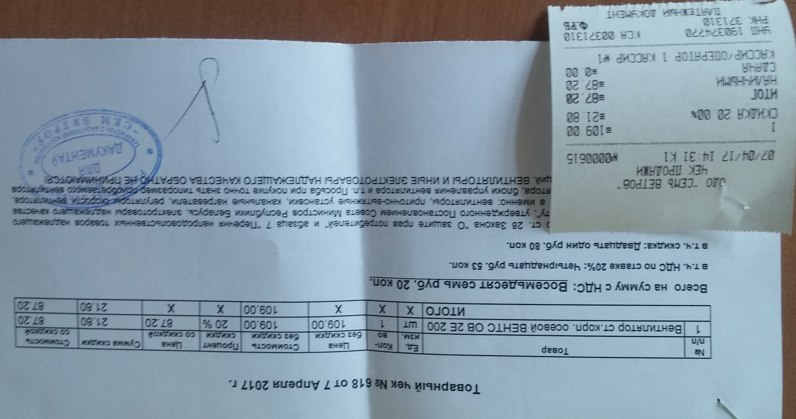
Документы/Фактические расходы/2017-04/2017-04-07 - 87.20 - 46$ - Второй этаж - Вентилятор.jpg
