peter-hanzo/KD/Документы/Фактические расходы/2017-04/2017-04-07 - 700.00 - 370$ - Серверная - Аванс за климатический шкаф.jpg

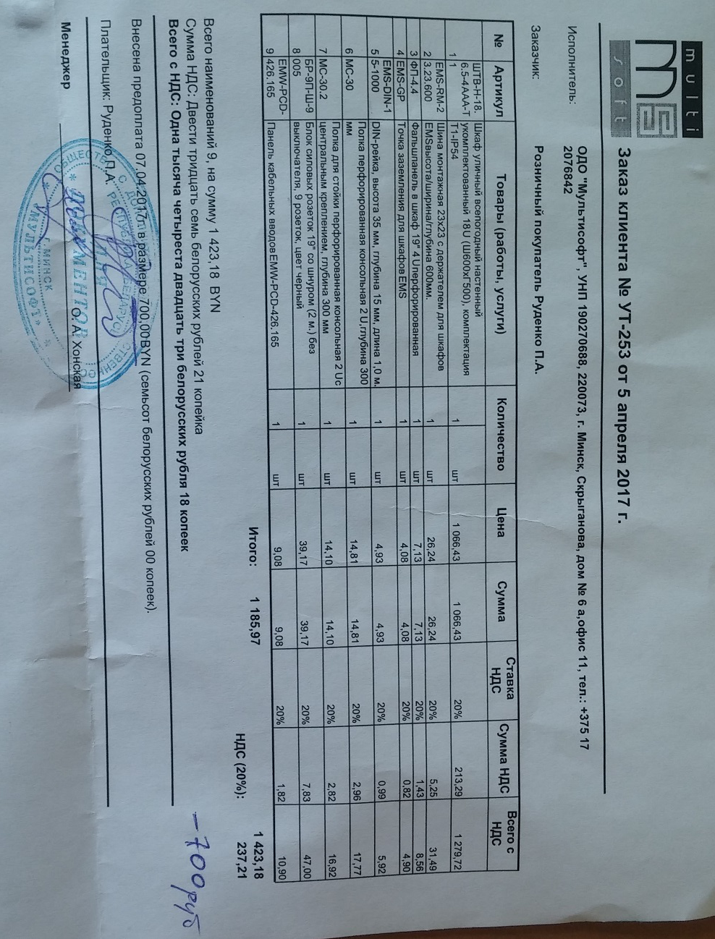
Документы/Фактические расходы/2017-04/2017-04-07 - 700.00 - 370$ - Серверная - Аванс за климатический шкаф.jpg
