peter-hanzo/KD/Документы/Фактические расходы/2017-04/2017-04-12 - 71.50 - 38$ - Второй этаж - Дефлектор.jpg

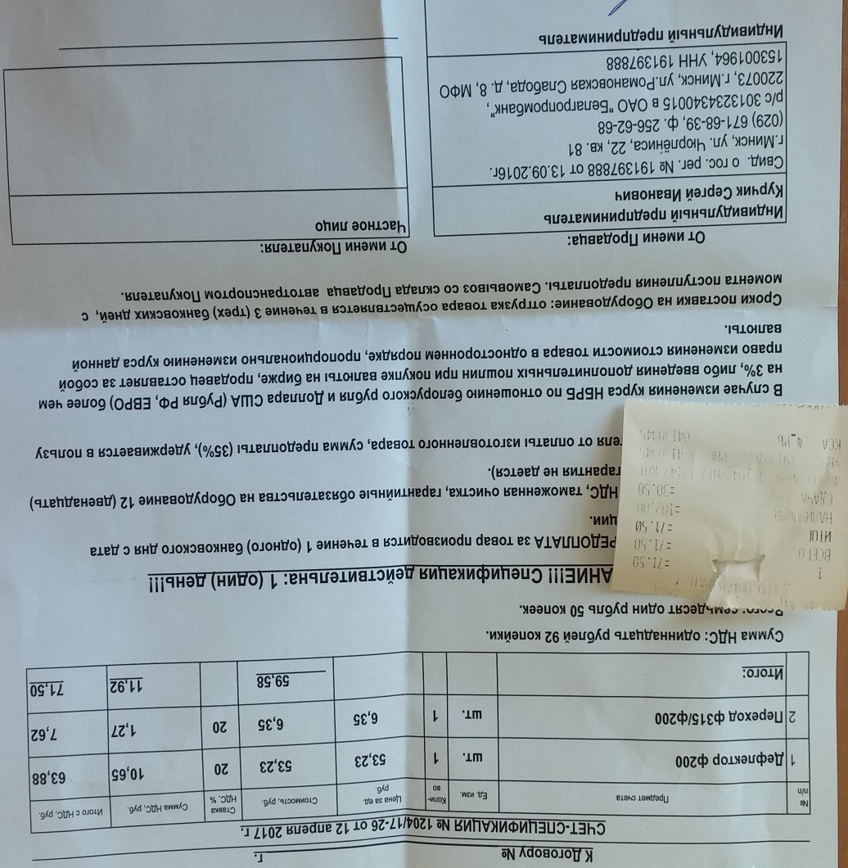
Документы/Фактические расходы/2017-04/2017-04-12 - 71.50 - 38$ - Второй этаж - Дефлектор.jpg
