peter-hanzo/KD/Документы/Фактические расходы/2017-04/2017-04-12 - 142.03 - 75$ - Второй этаж - Комплектующие вентиляции и другое.jpg

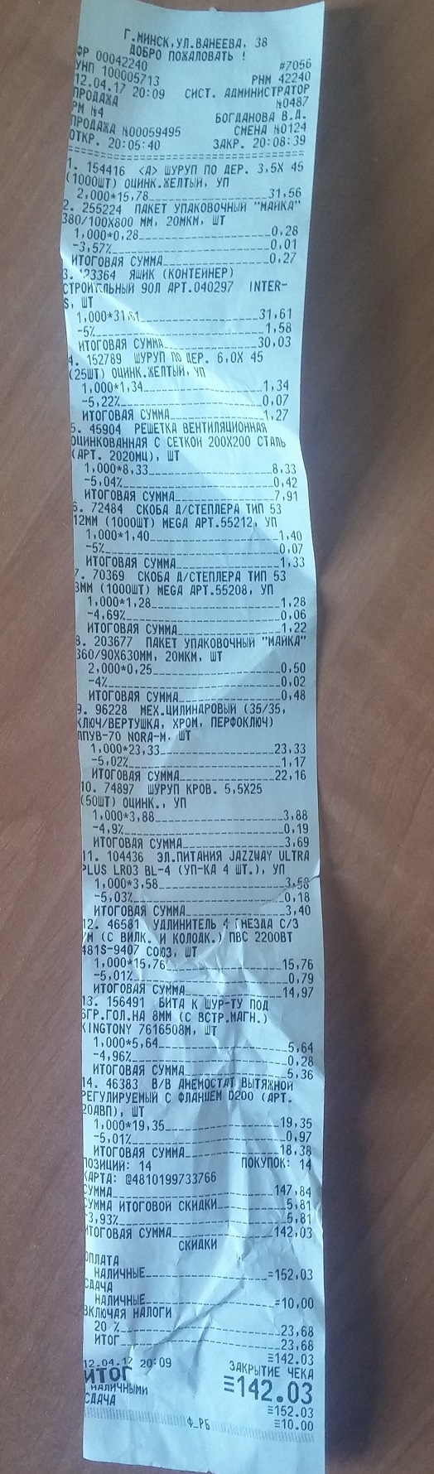
Документы/Фактические расходы/2017-04/2017-04-12 - 142.03 - 75$ - Второй этаж - Комплектующие вентиляции и другое.jpg
