peter-hanzo/KD/Документы/Фактические расходы/2017-04/2017-04-18 - 3.38 - 2$ - Второй этаж - Инструмент.jpg

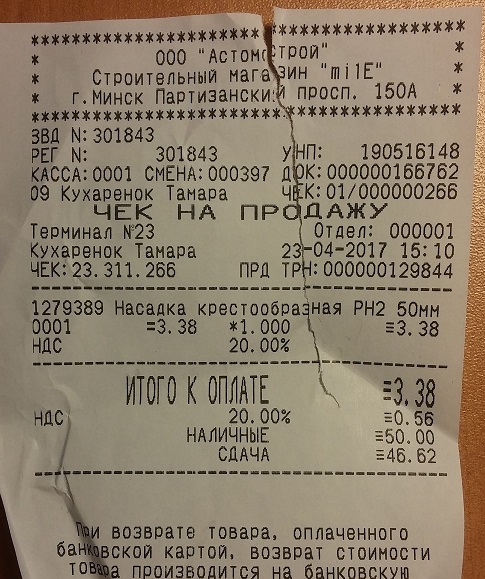
Документы/Фактические расходы/2017-04/2017-04-18 - 3.38 - 2$ - Второй этаж - Инструмент.jpg
