peter-hanzo/KD/Документы/Фактические расходы/2017-04/2017-04-18 - 4.93 - 2$ - Второй этаж - Штатлевка.jpg

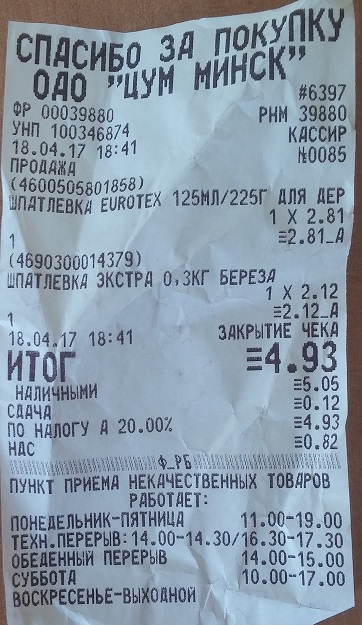
Документы/Фактические расходы/2017-04/2017-04-18 - 4.93 - 2$ - Второй этаж - Штатлевка.jpg
