peter-hanzo/KD/Документы/Фактические расходы/2017-04/2017-04-19 - 75.00 - 40$ - Второй этаж - Проходной элемент.jpg

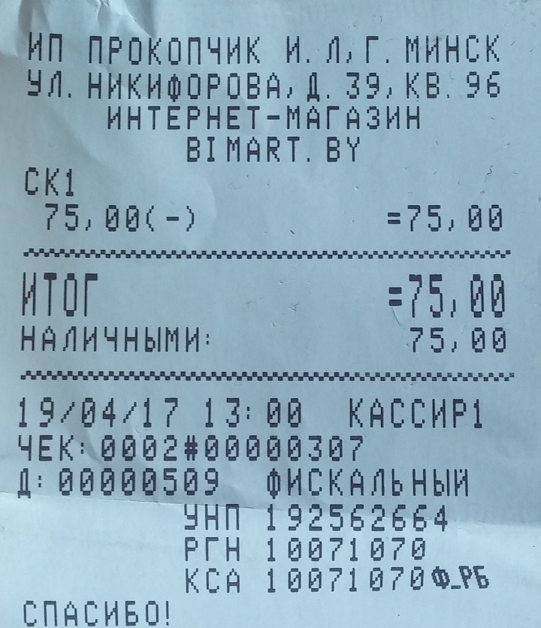
Документы/Фактические расходы/2017-04/2017-04-19 - 75.00 - 40$ - Второй этаж - Проходной элемент.jpg
