peter-hanzo/KD/Документы/Фактические расходы/2017-04/2017-04-19 - 359.50 - 191$ - Электросети - Кабеля и гофра.jpg

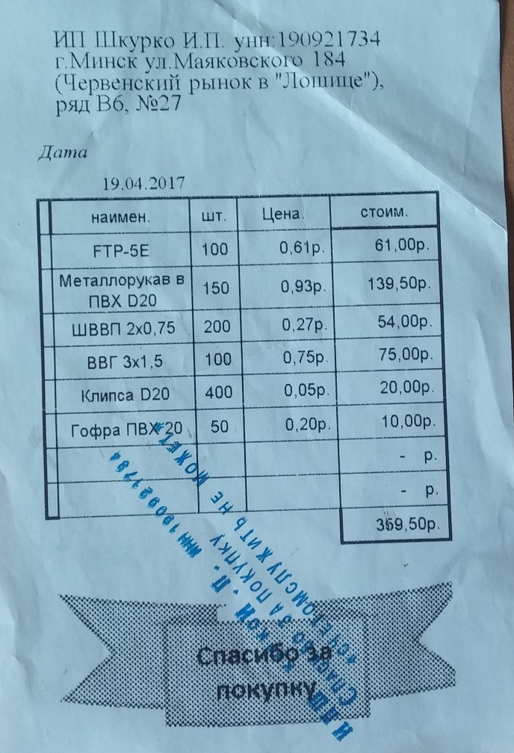
Документы/Фактические расходы/2017-04/2017-04-19 - 359.50 - 191$ - Электросети - Кабеля и гофра.jpg
