peter-hanzo/KD/Документы/Фактические расходы/2017-04/2017-04-24 - 13.25 - 7$ - Второй этаж - Инструмент.jpg

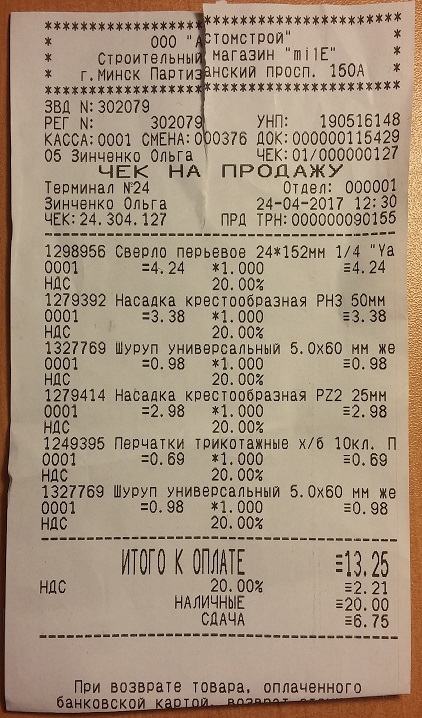
Документы/Фактические расходы/2017-04/2017-04-24 - 13.25 - 7$ - Второй этаж - Инструмент.jpg
