peter-hanzo/KD/Документы/Фактические расходы/2017-04/2017-04-28 - 29.36 - 15$ - Купол - Крепеж.jpg

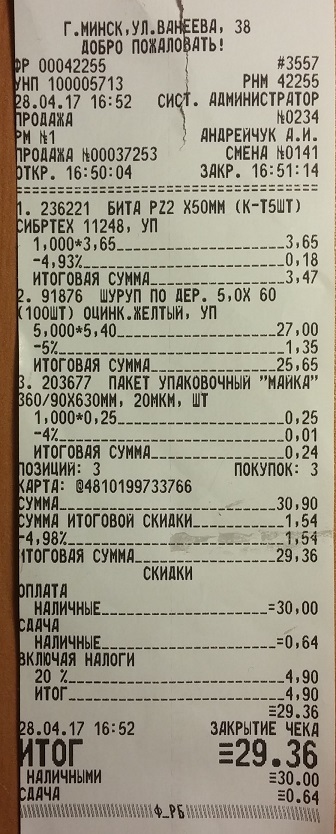
Документы/Фактические расходы/2017-04/2017-04-28 - 29.36 - 15$ - Купол - Крепеж.jpg
