peter-hanzo/KD/Документы/Фактические расходы/2017-04/2017-04-29 - 10.05 - 5$ - Серверная - Разъемы.jpg

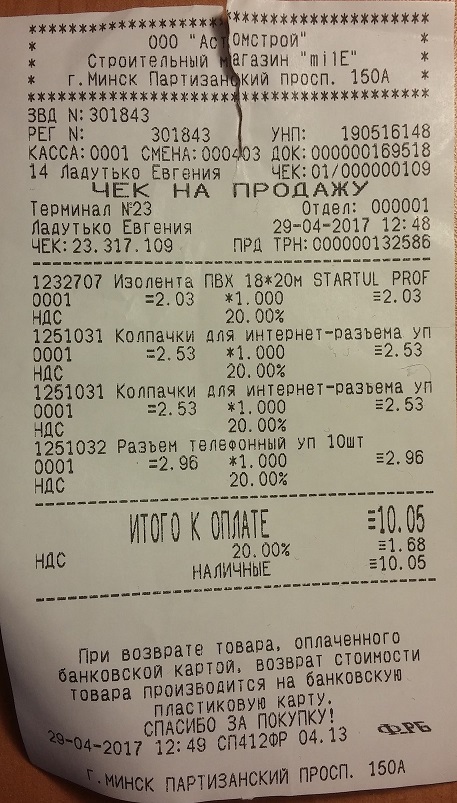
Документы/Фактические расходы/2017-04/2017-04-29 - 10.05 - 5$ - Серверная - Разъемы.jpg
