peter-hanzo/KD/Документы/Фактические расходы/2017-04/2017-04-29 - 10.23 - 5$ - Второй этаж - Инструмент.jpg

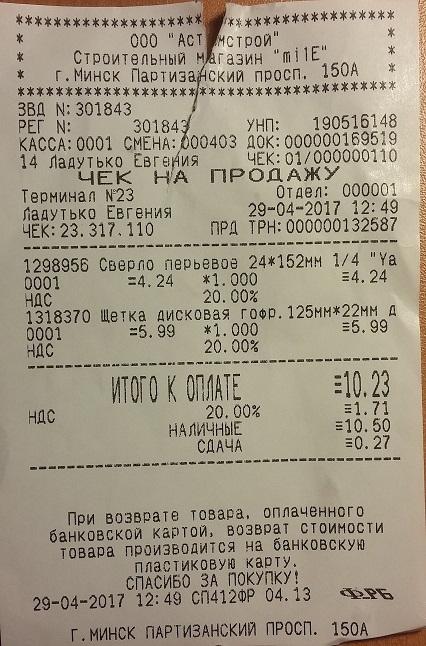
Документы/Фактические расходы/2017-04/2017-04-29 - 10.23 - 5$ - Второй этаж - Инструмент.jpg
