peter-hanzo/KD/Документы/Фактические расходы/2017-05/2017-05-05 - 4.00 - 2$ - Водопровод -  Фильтр для воды.jpg

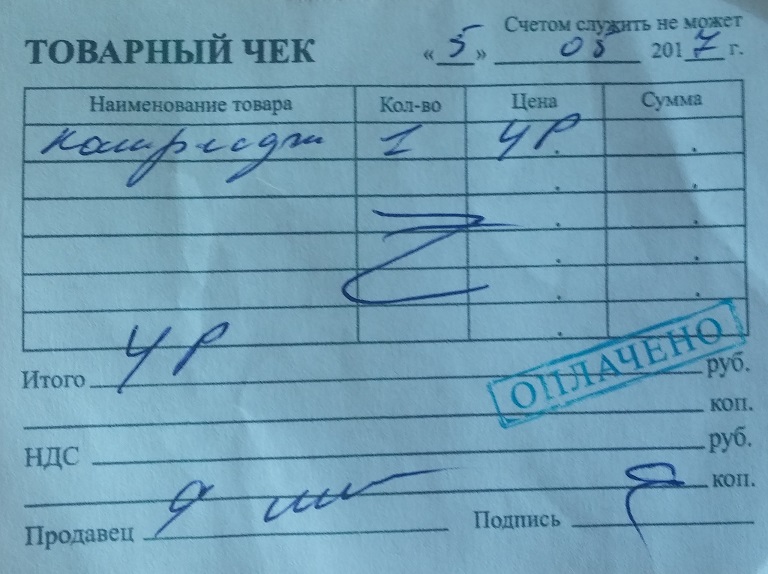
Документы/Фактические расходы/2017-05/2017-05-05 - 4.00 - 2$ - Водопровод - Фильтр для воды.jpg
