peter-hanzo/KD/Документы/Фактические расходы/2017-05/2017-05-05 - 6.00 - 3$ - Электросети - шурупы для крепления.jpg

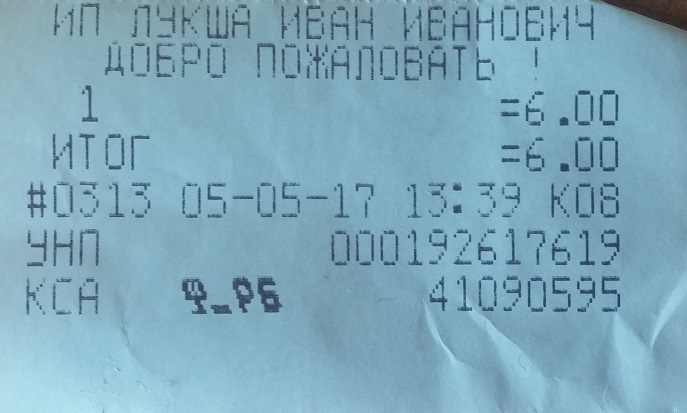
Документы/Фактические расходы/2017-05/2017-05-05 - 6.00 - 3$ - Электросети - шурупы для крепления.jpg
