peter-hanzo/KD/Документы/Фактические расходы/2017-05/2017-05-05 - 94.79 - 50$ - Электросети - Кабель и муфты.jpg

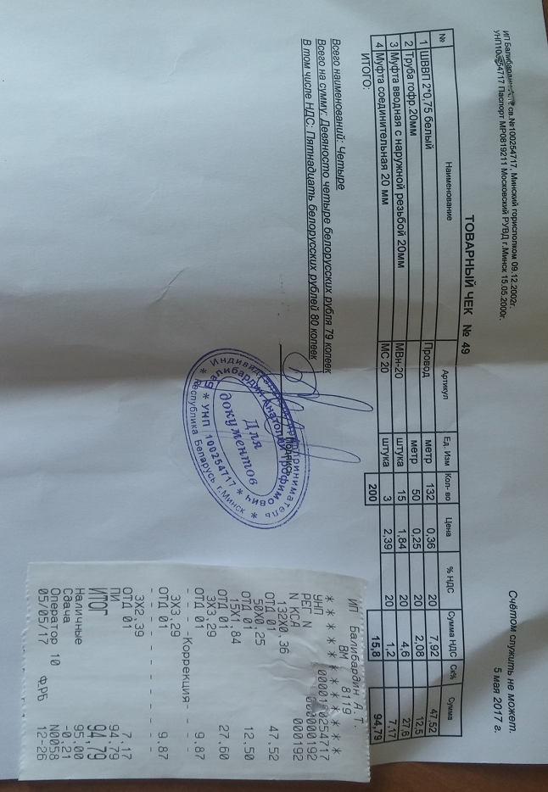
Документы/Фактические расходы/2017-05/2017-05-05 - 94.79 - 50$ - Электросети - Кабель и муфты.jpg
