peter-hanzo/KD/Документы/Фактические расходы/2017-05/2017-05-06 - 6.00 - 3$ - Серверная - утеплитель для шкафа.jpg

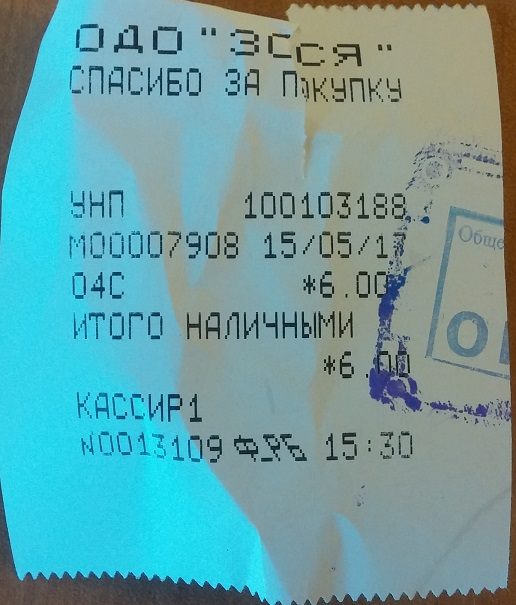
Документы/Фактические расходы/2017-05/2017-05-06 - 6.00 - 3$ - Серверная - утеплитель для шкафа.jpg
