peter-hanzo/KD/Документы/Фактические расходы/2017-05/2017-05-10 - 4.63 - 2$ - Электросети - шурупы для монтажа кабелей.jpg

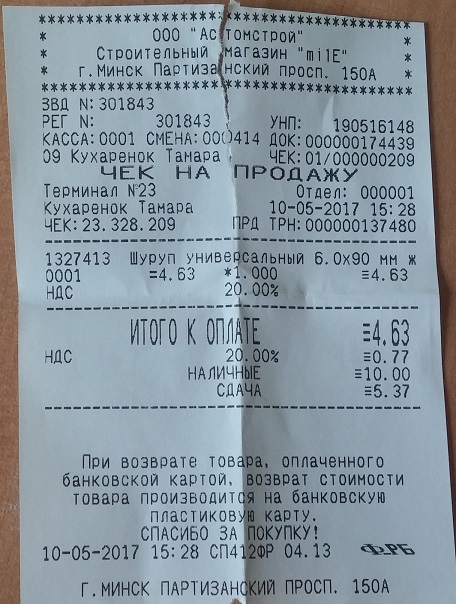
Документы/Фактические расходы/2017-05/2017-05-10 - 4.63 - 2$ - Электросети - шурупы для монтажа кабелей.jpg
