peter-hanzo/KD/Документы/Фактические расходы/2017-05/2017-05-17 - 55.06 - 30$ - Каркас - материалы для перемычек.jpg

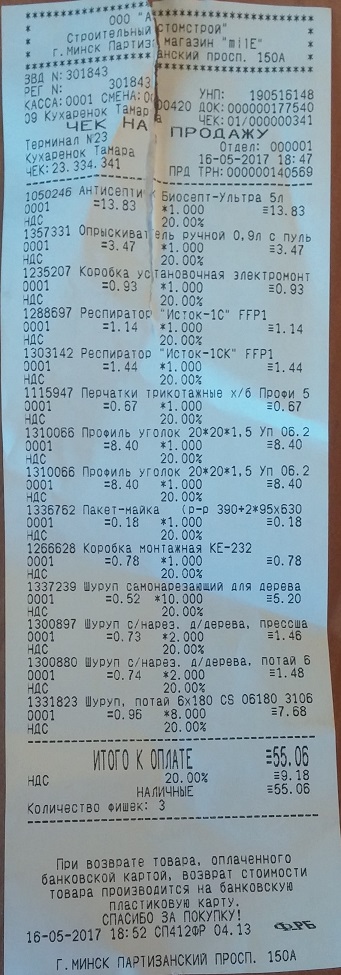
Документы/Фактические расходы/2017-05/2017-05-17 - 55.06 - 30$ - Каркас - материалы для перемычек.jpg
