peter-hanzo/KD/Документы/Фактические расходы/2017-05/2017-05-22 - 48.72 - 26$ - Второй этаж - масло пилки гвозди шурупы.jpg

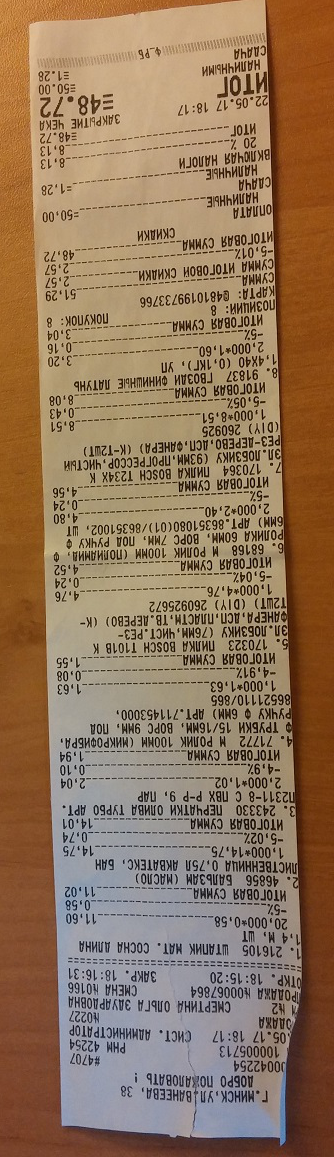
Документы/Фактические расходы/2017-05/2017-05-22 - 48.72 - 26$ - Второй этаж - масло пилки гвозди шурупы.jpg
