peter-hanzo/KD/Документы/Фактические расходы/2017-05/2017-05-23 - 29.40 - 16$ - Серверная - цемент 6 мешков.jpg

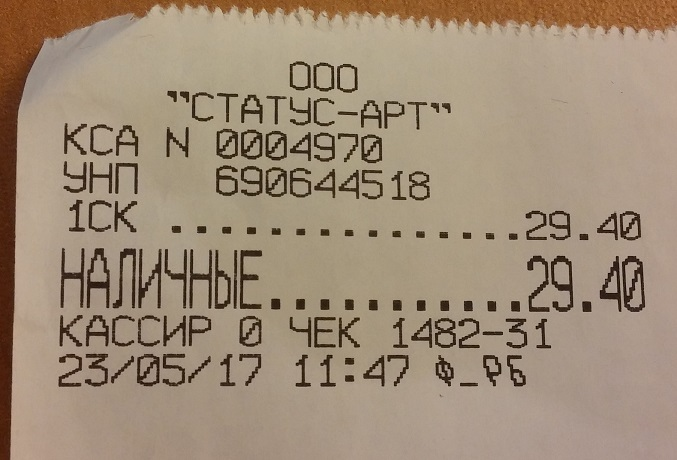
Документы/Фактические расходы/2017-05/2017-05-23 - 29.40 - 16$ - Серверная - цемент 6 мешков.jpg
