peter-hanzo/KD/Документы/Фактические расходы/2017-05/2017-05-23 - 88.14 - 47$ - Утепление купола - крафт бумага 300м.jpg

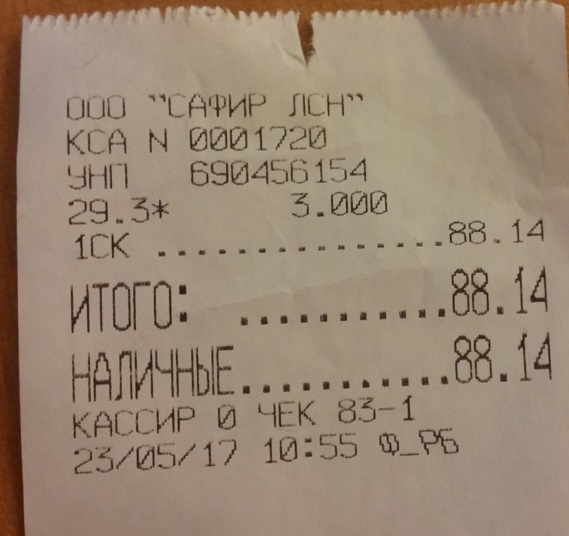
Документы/Фактические расходы/2017-05/2017-05-23 - 88.14 - 47$ - Утепление купола - крафт бумага 300м.jpg
