peter-hanzo/KD/Документы/Фактические расходы/2017-05/2017-05-25 - 26.50 - 14$ - Водопровод -  детали труб часть 2.jpg

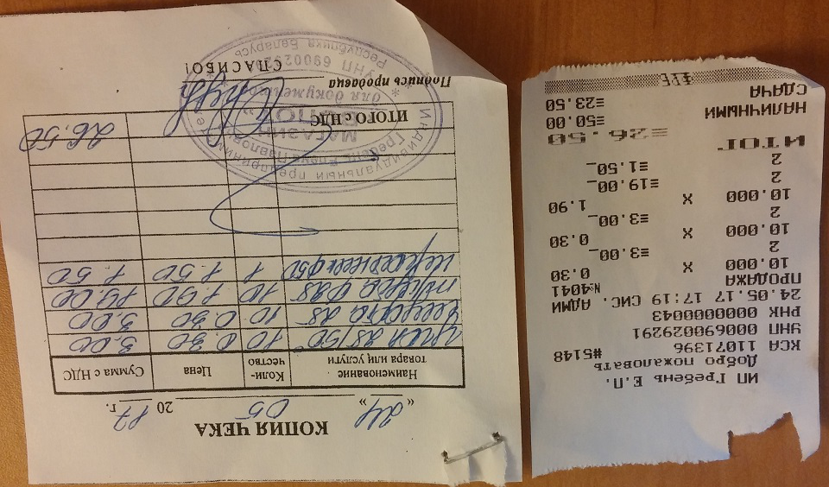
Документы/Фактические расходы/2017-05/2017-05-25 - 26.50 - 14$ - Водопровод - детали труб часть 2.jpg
