peter-hanzo/KD/Документы/Фактические расходы/2017-05/2017-05-27 - 7.12 - 3$ - Водопровод -  детали труб часть 3.jpg

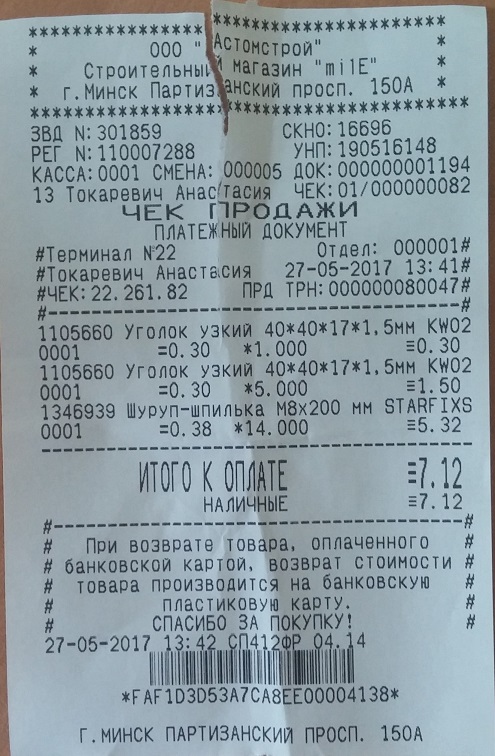
Документы/Фактические расходы/2017-05/2017-05-27 - 7.12 - 3$ - Водопровод - детали труб часть 3.jpg
