peter-hanzo/KD/Документы/Фактические расходы/2017-05/2017-05-29 - 23.01 - 12$ - Электросети - детали для электрошкафа часть 2.jpg

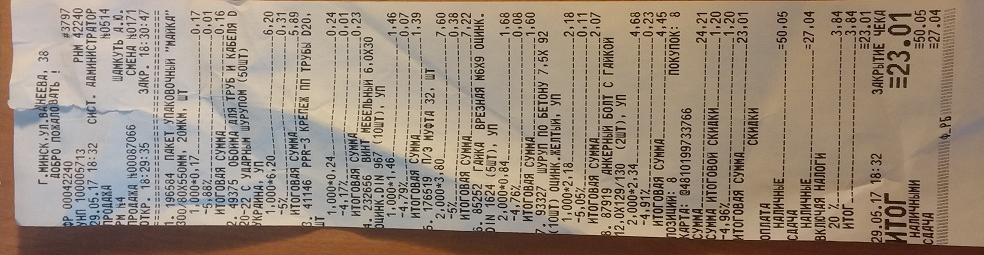
Документы/Фактические расходы/2017-05/2017-05-29 - 23.01 - 12$ - Электросети - детали для электрошкафа часть 2.jpg
