peter-hanzo/KD/Документы/Фактические расходы/2017-05/2017-05-30 - 78.5 - 42$ - Электросети - кабель и термотруба.jpg

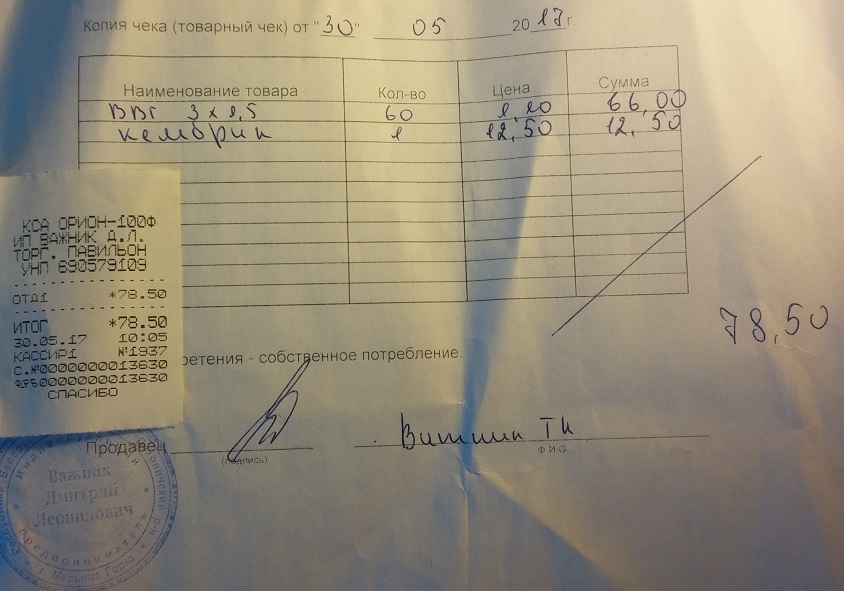
Документы/Фактические расходы/2017-05/2017-05-30 - 78.5 - 42$ - Электросети - кабель и термотруба.jpg
