peter-hanzo/KD/Документы/Фактические расходы/2017-06/2017-06-02 - 146.35 - 78$ - Электросети - детали для электрошкафа часть 1.jpg

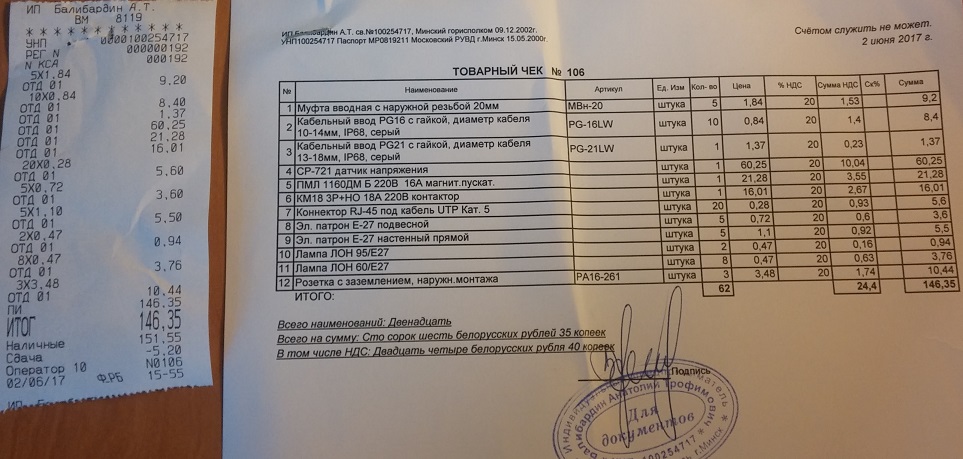
Документы/Фактические расходы/2017-06/2017-06-02 - 146.35 - 78$ - Электросети - детали для электрошкафа часть 1.jpg
