peter-hanzo/KD/Документы/Фактические расходы/2017-06/2017-06-07 - 119.70 - 63$ - Серверная - комплектующие 1.jpg

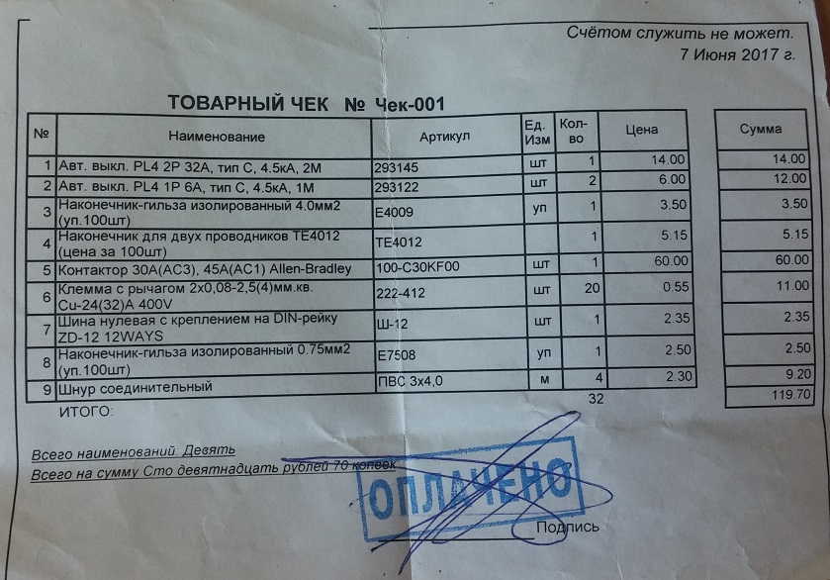
Документы/Фактические расходы/2017-06/2017-06-07 - 119.70 - 63$ - Серверная - комплектующие 1.jpg
