peter-hanzo/KD/Документы/Фактические расходы/2017-06/2017-06-08 - 35.94 - 19$ - Электросети - комплектующие 1.jpg

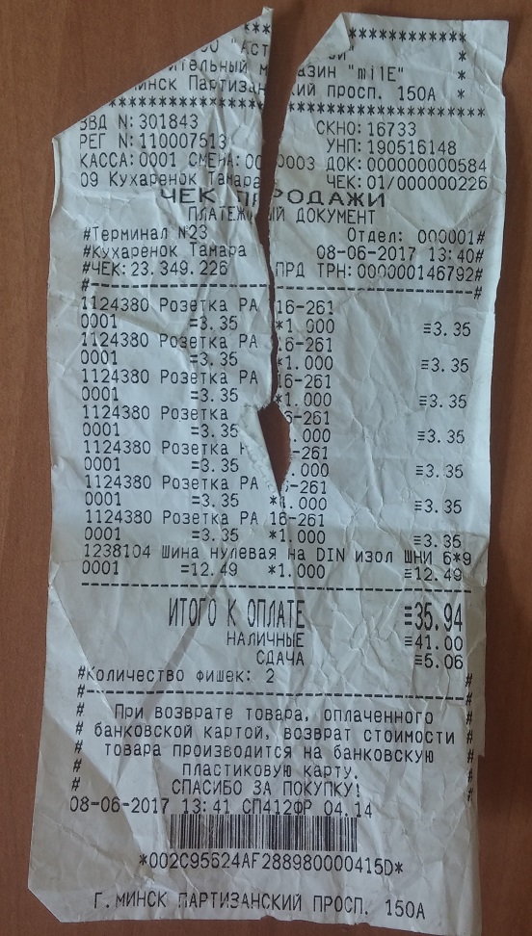
Документы/Фактические расходы/2017-06/2017-06-08 - 35.94 - 19$ - Электросети - комплектующие 1.jpg
