peter-hanzo/KD/Документы/Фактические расходы/2017-06/2017-06-09 - 24.50 - 13$ - Телефон - комплектующие 1.jpg

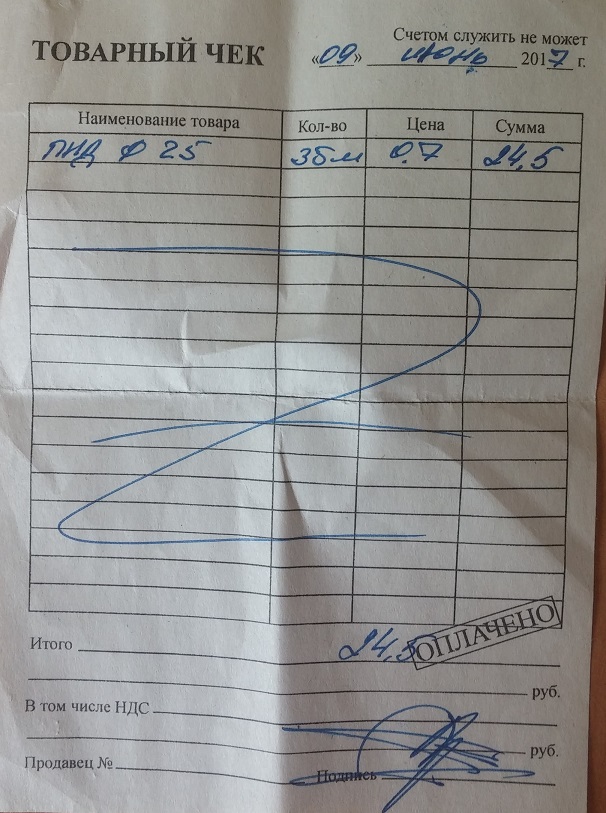
Документы/Фактические расходы/2017-06/2017-06-09 - 24.50 - 13$ - Телефон - комплектующие 1.jpg
