peter-hanzo/KD/Документы/Фактические расходы/2017-06/2017-06-09 - 153.12 - 82$ - Серверная - комплектующие 2.jpg

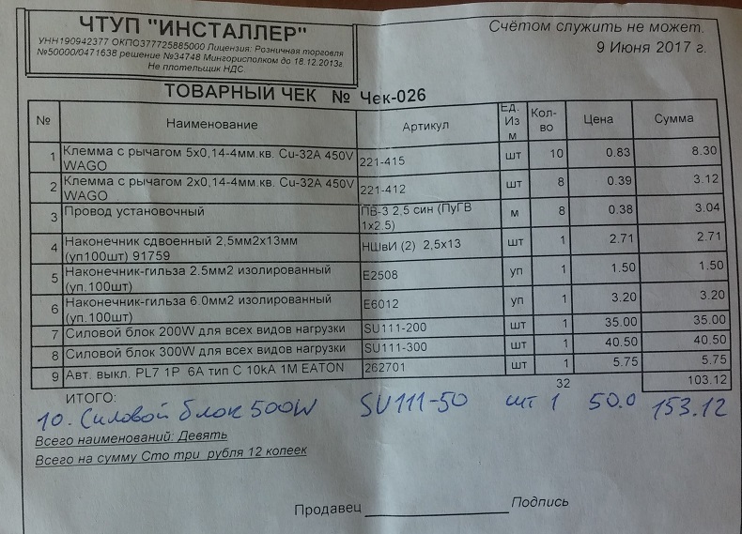
Документы/Фактические расходы/2017-06/2017-06-09 - 153.12 - 82$ - Серверная - комплектующие 2.jpg
