peter-hanzo/KD/Документы/Фактические расходы/2017-06/2017-06-14 - 104.64 - 55$ - Серверная - комплектующие 3.jpg

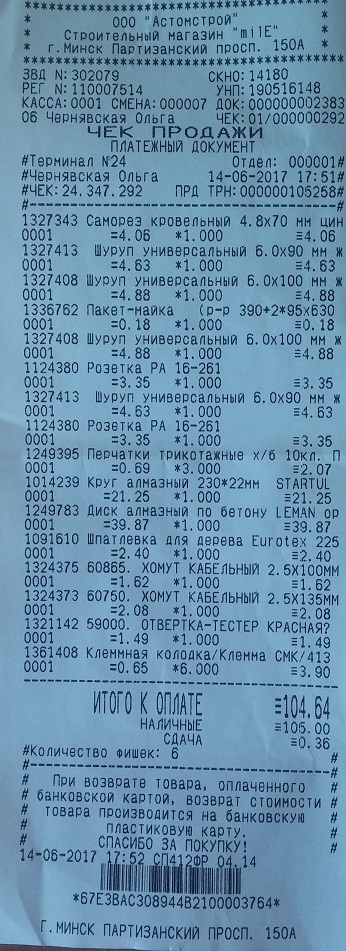
Документы/Фактические расходы/2017-06/2017-06-14 - 104.64 - 55$ - Серверная - комплектующие 3.jpg
