peter-hanzo/KD/Документы/Фактические расходы/2017-06/2017-06-23 - 2296.00 - 1189$ - Второй этаж - утеплитель на весь дом.jpg

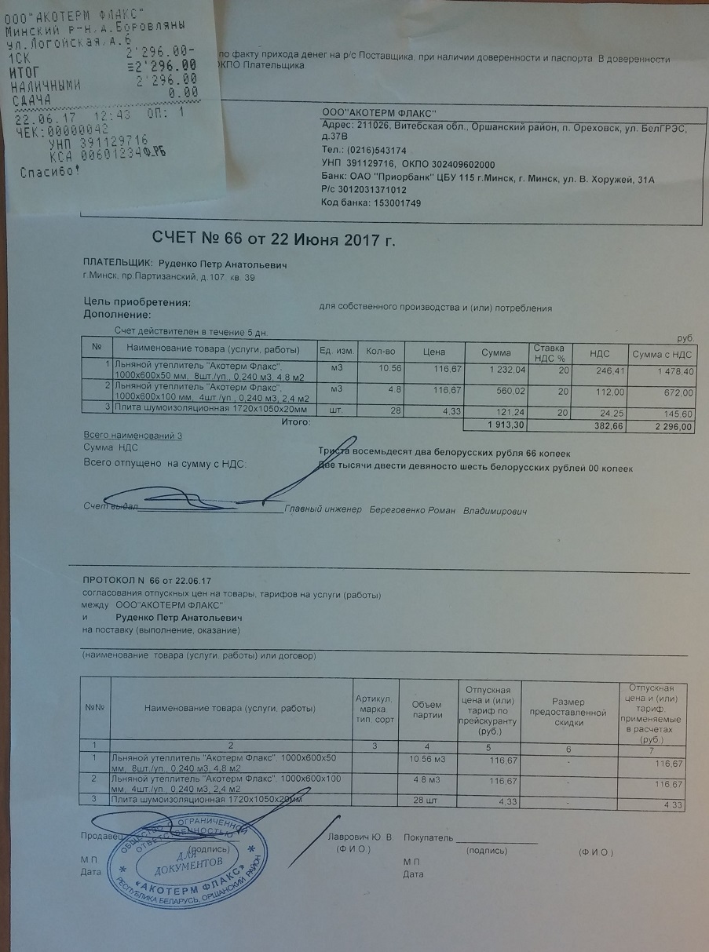
Документы/Фактические расходы/2017-06/2017-06-23 - 2296.00 - 1189$ - Второй этаж - утеплитель на весь дом.jpg
