peter-hanzo/KD/Документы/Фактические расходы/2017-07/2017-07-02 - 126.00 - 64$ - Отделка - комплектующие часть 1.jpg

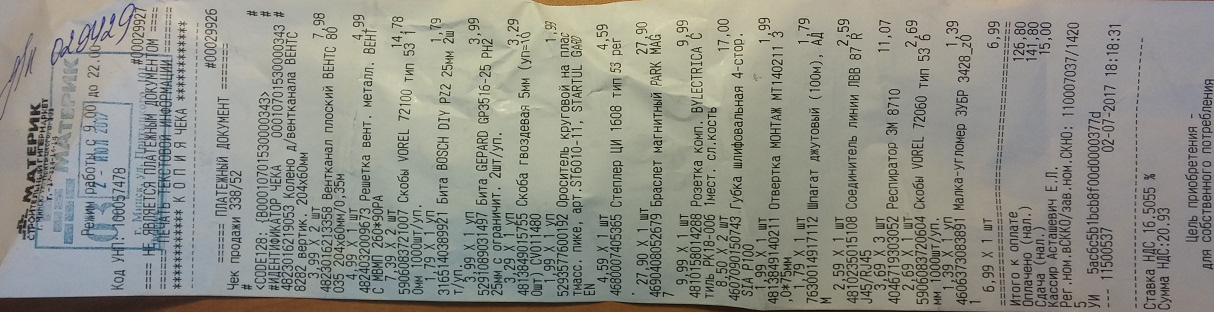
Документы/Фактические расходы/2017-07/2017-07-02 - 126.00 - 64$ - Отделка - комплектующие часть 1.jpg
