peter-hanzo/KD/Документы/Фактические расходы/2017-07/2017-07-05 - 34.53 - 17$ - Вентиляция - комплектующие.jpg

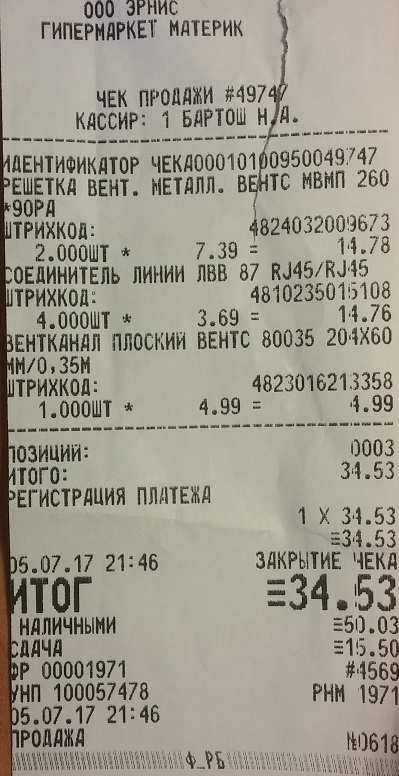
Документы/Фактические расходы/2017-07/2017-07-05 - 34.53 - 17$ - Вентиляция - комплектующие.jpg
