peter-hanzo/KD/Документы/Фактические расходы/2017-07/2017-07-06 - 98.00 - [50$] - Первый этаж - монтаж утеплителя часть 1.jpg

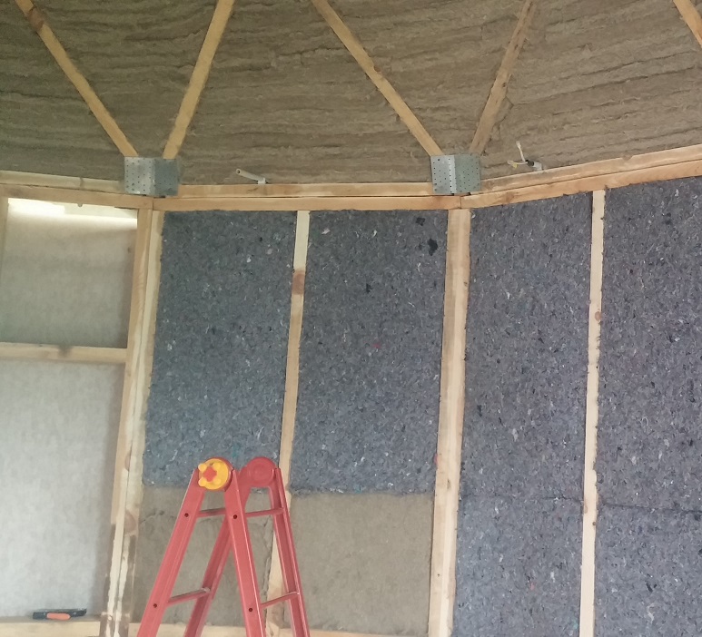
Документы/Фактические расходы/2017-07/2017-07-06 - 98.00 - [50$] - Первый этаж - монтаж утеплителя часть 1.jpg
