peter-hanzo/KD/Документы/Фактические расходы/2017-07/2017-07-07 - 196.00 - [100$] - Первый этаж - монтаж утеплителя часть 2.jpg

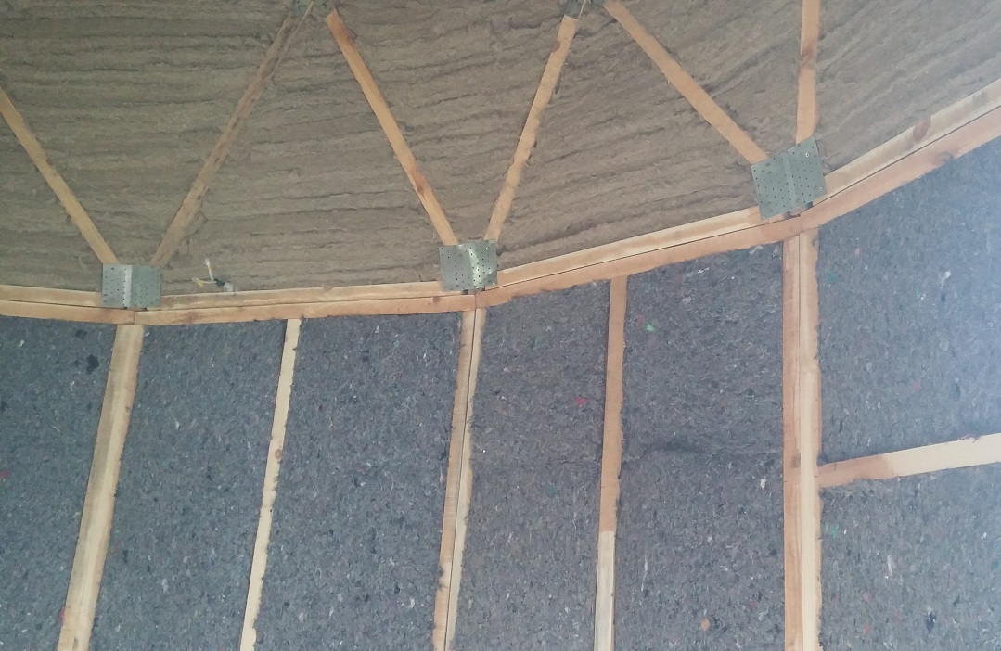
Документы/Фактические расходы/2017-07/2017-07-07 - 196.00 - [100$] - Первый этаж - монтаж утеплителя часть 2.jpg
