peter-hanzo/KD/Документы/Фактические расходы/2017-07/2017-07-11 - 15.02 - 8$ - Серверная - розетки.jpg

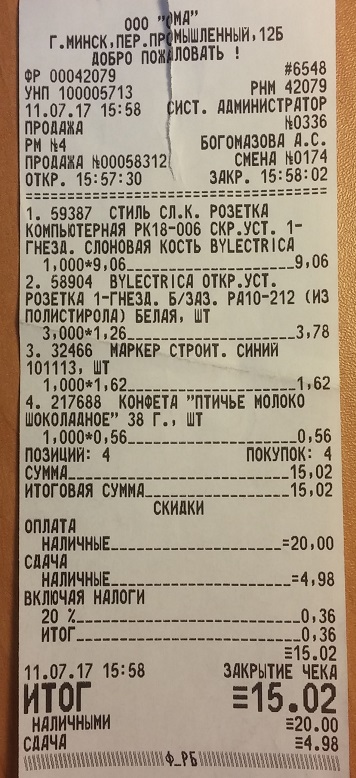
Документы/Фактические расходы/2017-07/2017-07-11 - 15.02 - 8$ - Серверная - розетки.jpg
