peter-hanzo/KD/Документы/Фактические расходы/2017-07/2017-07-11 - 103.93 - 53$ - Отделка - доска для стен и купола часть 2.jpg

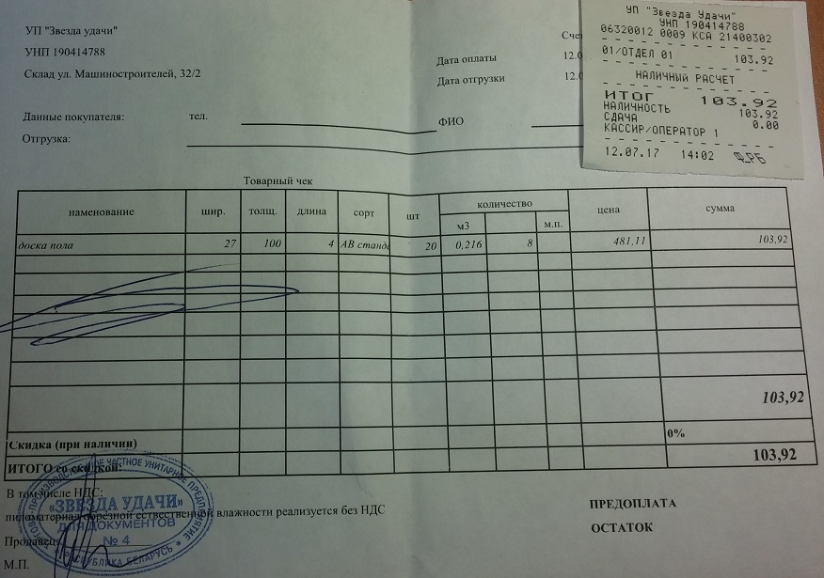
Документы/Фактические расходы/2017-07/2017-07-11 - 103.93 - 53$ - Отделка - доска для стен и купола часть 2.jpg
