peter-hanzo/KD/Документы/Фактические расходы/2017-07/2017-07-11 - 1107.31 - 563$ - Отделка - доска для стен и купола часть 1.jpg

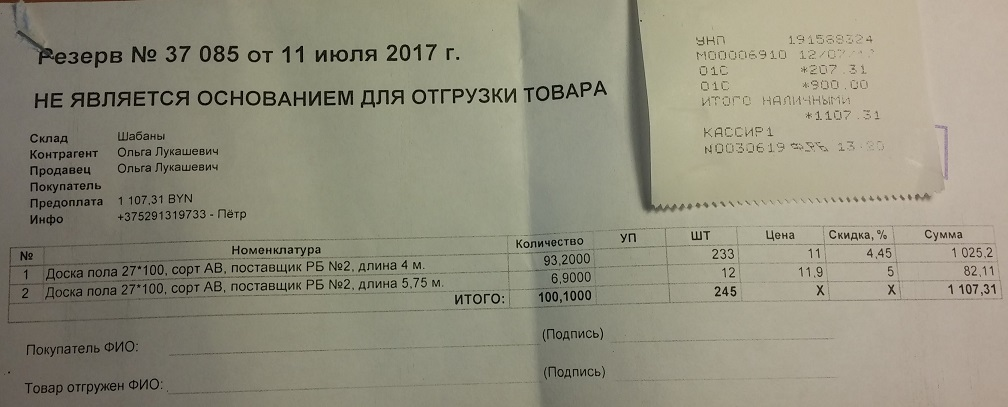
Документы/Фактические расходы/2017-07/2017-07-11 - 1107.31 - 563$ - Отделка - доска для стен и купола часть 1.jpg
