peter-hanzo/KD/Документы/Фактические расходы/2017-07/2017-07-13 - 235.00 - [120$] - Отделка - монтаж доски часть 1.jpg

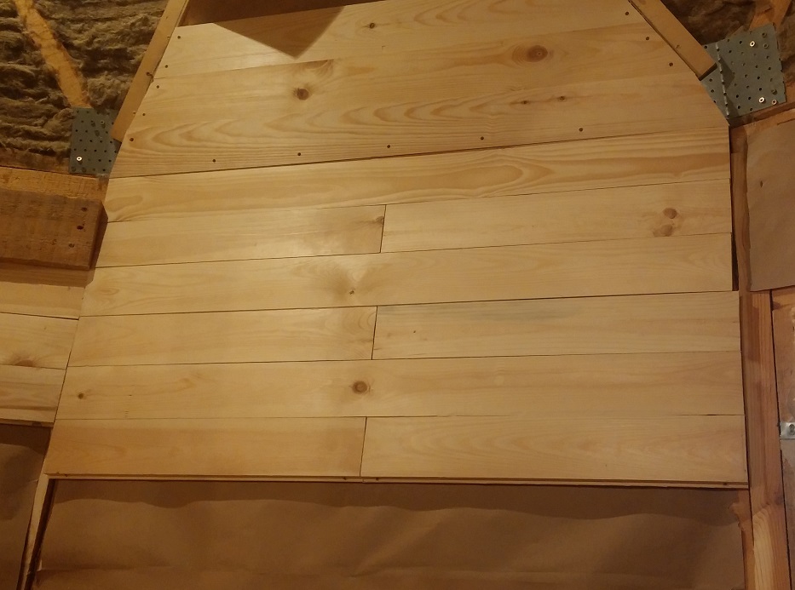
Документы/Фактические расходы/2017-07/2017-07-13 - 235.00 - [120$] - Отделка - монтаж доски часть 1.jpg
