peter-hanzo/KD/Документы/Фактические расходы/2017-07/2017-07-20 - 23.53 - 12$ - Отделка - комплектующие часть 2.jpg

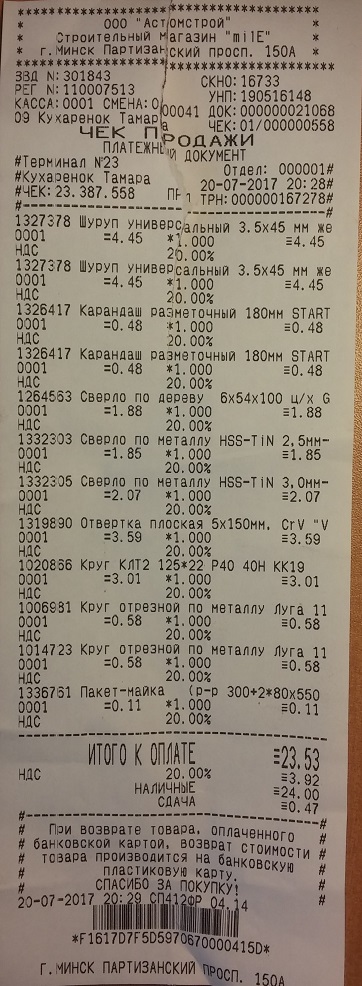
Документы/Фактические расходы/2017-07/2017-07-20 - 23.53 - 12$ - Отделка - комплектующие часть 2.jpg
