peter-hanzo/KD/Документы/Фактические расходы/2017-07/2017-07-21 - 155.00 - [80$] - Отделка - монтаж доски часть 2.jpg

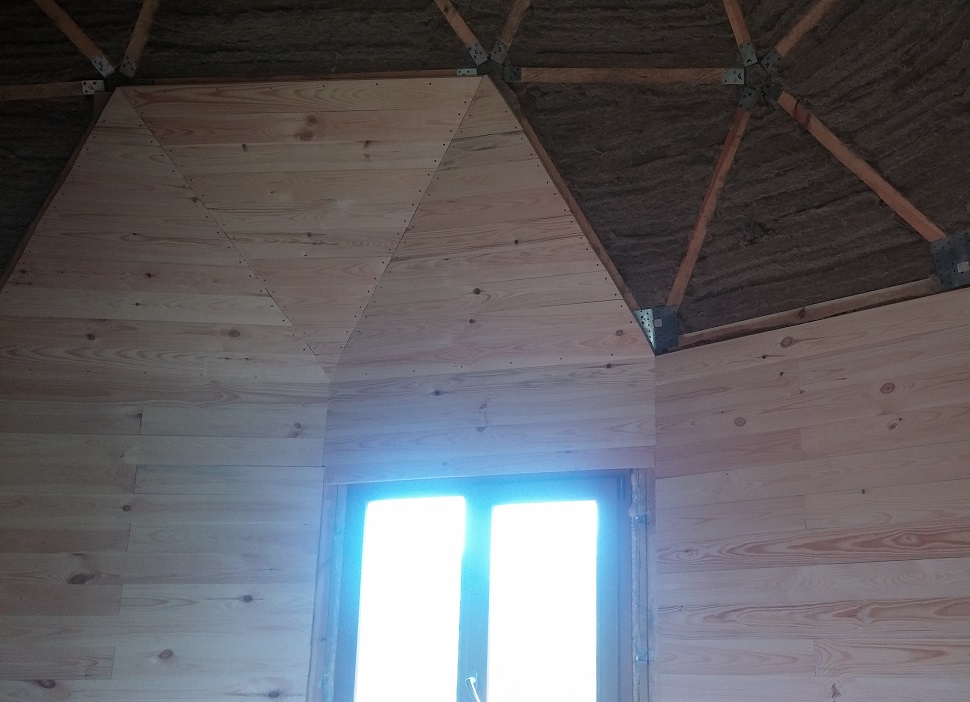
Документы/Фактические расходы/2017-07/2017-07-21 - 155.00 - [80$] - Отделка - монтаж доски часть 2.jpg
