peter-hanzo/KD/Документы/Фактические расходы/2017-07/2017-07-25 - 8.26 - 4$ - Отделка - комплектующие часть 3.jpg

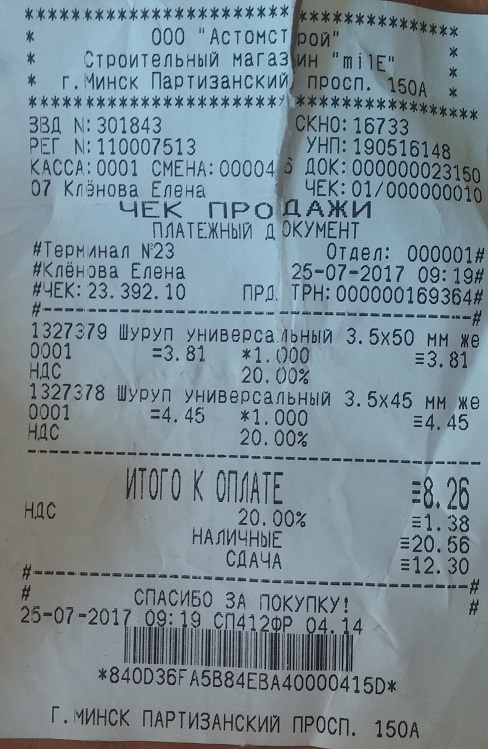
Документы/Фактические расходы/2017-07/2017-07-25 - 8.26 - 4$ - Отделка - комплектующие часть 3.jpg
