peter-hanzo/KD/Документы/Фактические расходы/2017-07/2017-07-26 - 350.00 - [180$] - Отделка - монтаж доски часть 3.jpg

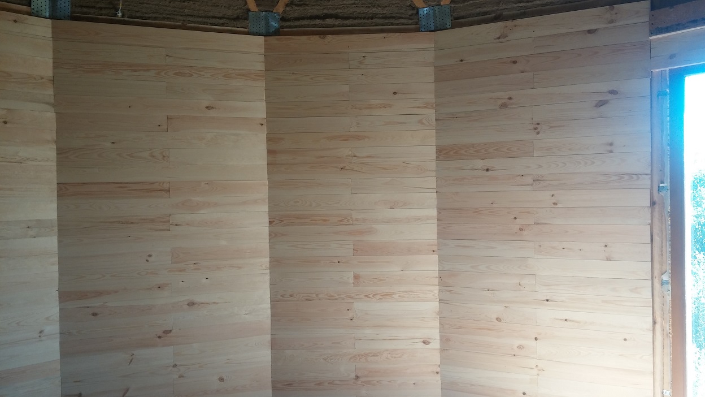
Документы/Фактические расходы/2017-07/2017-07-26 - 350.00 - [180$] - Отделка - монтаж доски часть 3.jpg
