peter-hanzo/KD/Документы/Фактические расходы/2017-08/2017-08-02 - 234.00 - [120$] - Отделка - монтаж доски часть 4.jpg

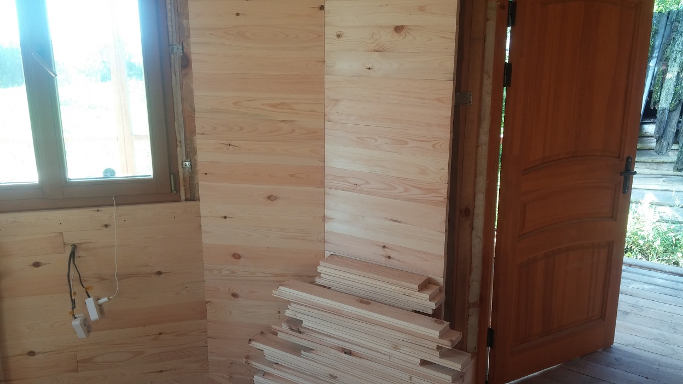
Документы/Фактические расходы/2017-08/2017-08-02 - 234.00 - [120$] - Отделка - монтаж доски часть 4.jpg
