peter-hanzo/KD/Документы/Фактические расходы/2017-08/2017-08-06 - 19.87 - 10$ - Благоустройство - замки на гараж и щиток.jpg

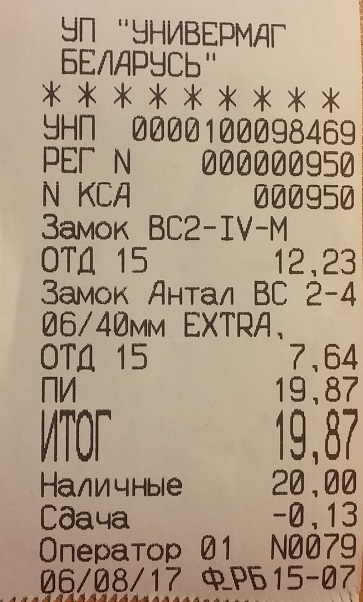
Документы/Фактические расходы/2017-08/2017-08-06 - 19.87 - 10$ - Благоустройство - замки на гараж и щиток.jpg
