peter-hanzo/KD/Документы/Фактические расходы/2017-08/2017-08-08 - 156.00 - [80$] - Отделка - обшивка доской часть 5.jpg

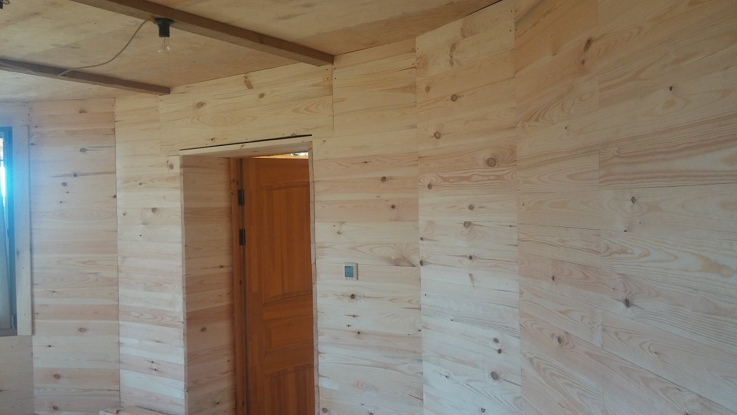
Документы/Фактические расходы/2017-08/2017-08-08 - 156.00 - [80$] - Отделка - обшивка доской часть 5.jpg
