peter-hanzo/KD/Документы/Фактические расходы/2017-08/2017-08-10 - 7.50 - 4$ - Отделка - клей для потолка.jpg

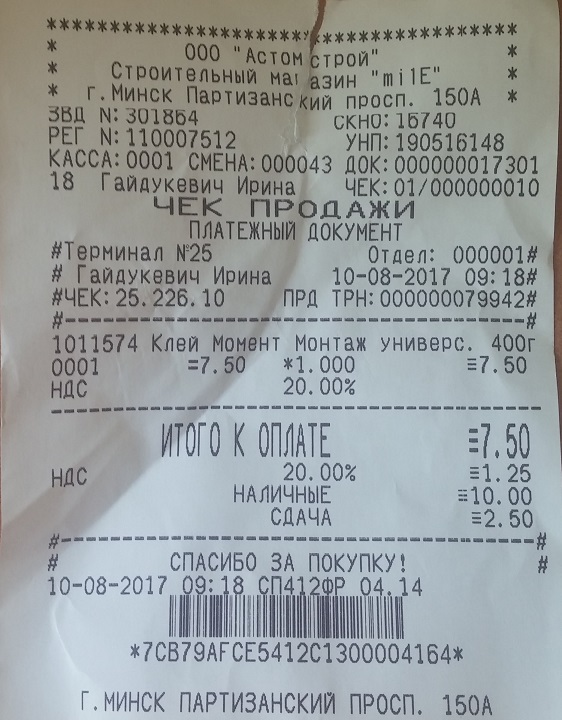
Документы/Фактические расходы/2017-08/2017-08-10 - 7.50 - 4$ - Отделка - клей для потолка.jpg
