peter-hanzo/KD/Документы/Фактические расходы/2017-08/2017-08-10 - 137.00 - [70$] - Отделка - обшивка купола часть 2.jpg

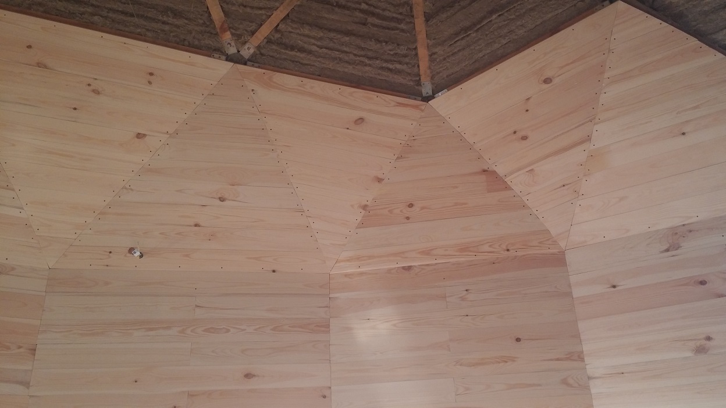
Документы/Фактические расходы/2017-08/2017-08-10 - 137.00 - [70$] - Отделка - обшивка купола часть 2.jpg
