peter-hanzo/KD/Документы/Фактические расходы/2017-08/2017-08-14 - 20.00 - 10$ - Крыша - замер отливов.jpg

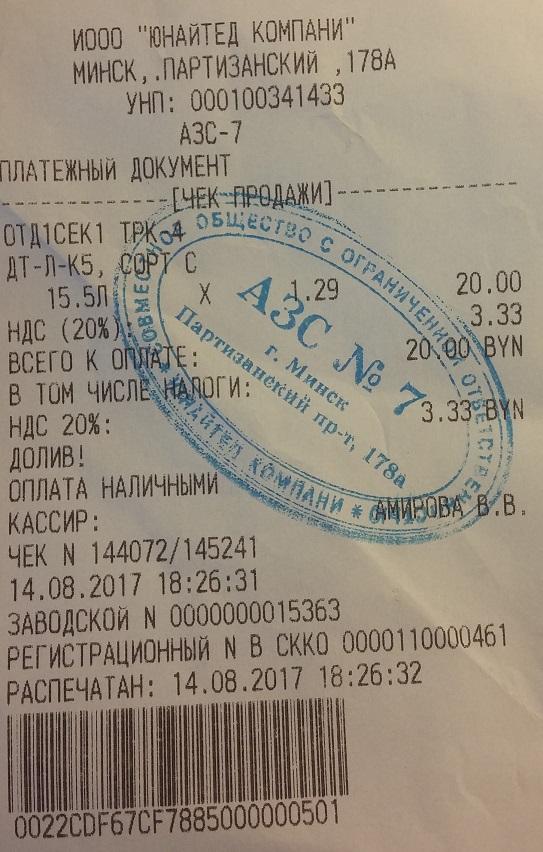
Документы/Фактические расходы/2017-08/2017-08-14 - 20.00 - 10$ - Крыша - замер отливов.jpg
