peter-hanzo/KD/Документы/Фактические расходы/2017-08/2017-08-17 - 194.00 - [100$] - Отделка - обшивка купола часть 3.jpg

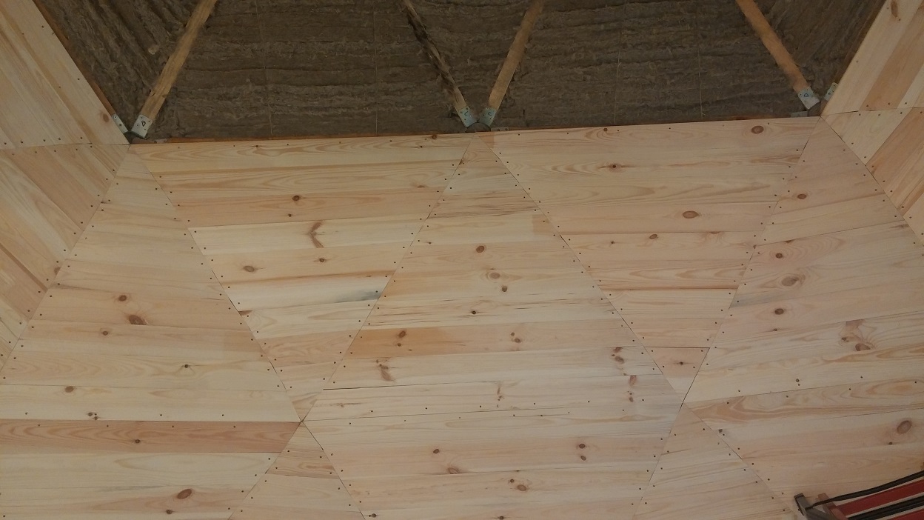
Документы/Фактические расходы/2017-08/2017-08-17 - 194.00 - [100$] - Отделка - обшивка купола часть 3.jpg
