peter-hanzo/KD/Документы/Фактические расходы/2017-08/2017-08-23 - 77.00 - [40$] - Отделка - обшивка купола часть 4.jpg

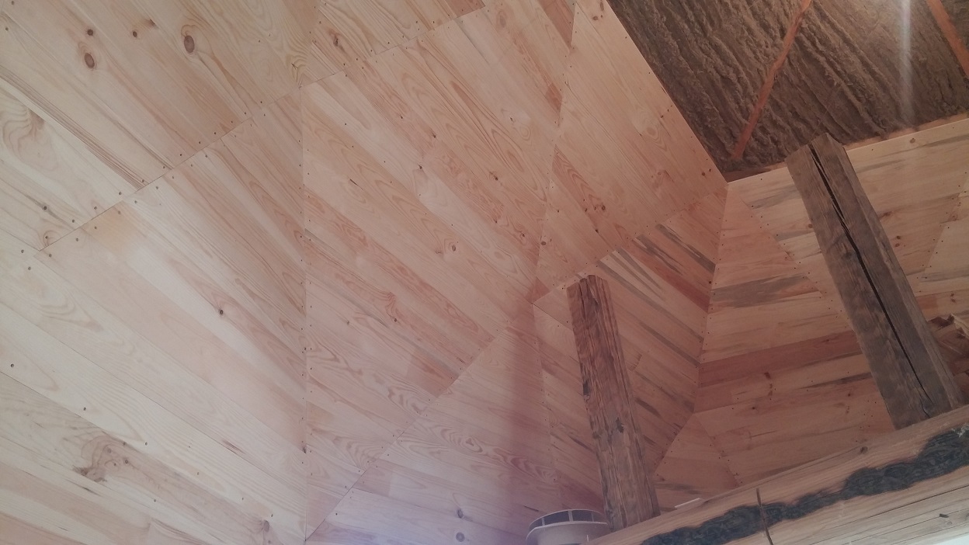
Документы/Фактические расходы/2017-08/2017-08-23 - 77.00 - [40$] - Отделка - обшивка купола часть 4.jpg
