peter-hanzo/KD/Документы/Фактические расходы/2017-08/2017-08-23 - 400.00 - [207$] - Крыша - материал для отливов.jpg

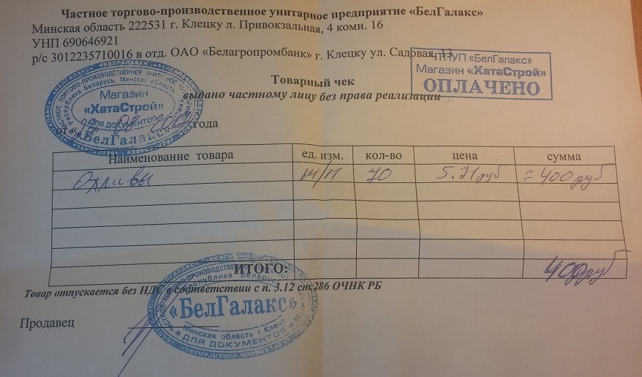
Документы/Фактические расходы/2017-08/2017-08-23 - 400.00 - [207$] - Крыша - материал для отливов.jpg
