peter-hanzo/KD/Документы/Фактические расходы/2017-08/2017-08-24 - 97.00 - [50$] - Отделка - комплектующие и расходники.jpg

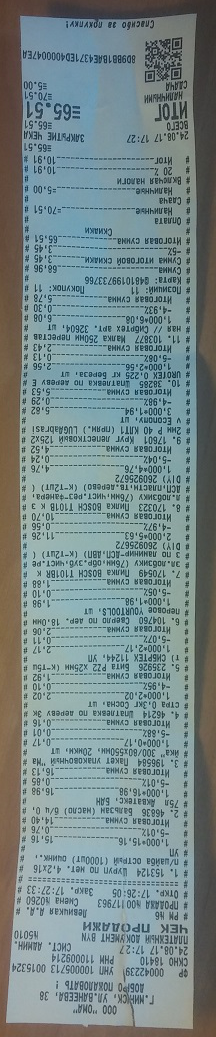
Документы/Фактические расходы/2017-08/2017-08-24 - 97.00 - [50$] - Отделка - комплектующие и расходники.jpg
