peter-hanzo/KD/Документы/Фактические расходы/2017-08/2017-08-26 - 97.00 - [50$] - Отделка - обшивка купола часть 5.jpg

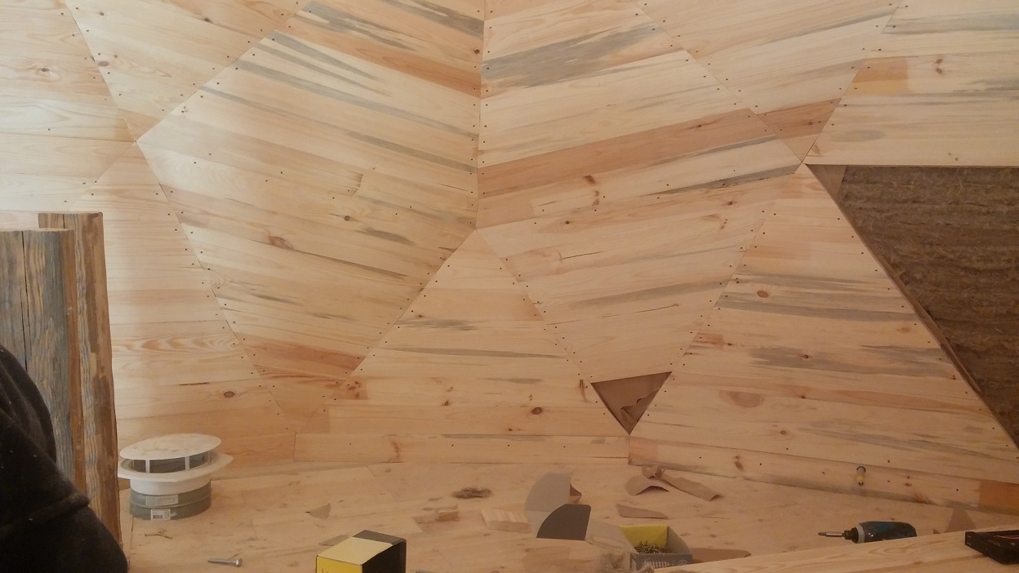
Документы/Фактические расходы/2017-08/2017-08-26 - 97.00 - [50$] - Отделка - обшивка купола часть 5.jpg
