peter-hanzo/KD/Документы/Фактические расходы/2017-08/2017-08-29 - 77.00 - [40$] - Отделка - обшивка купола часть 6.jpg

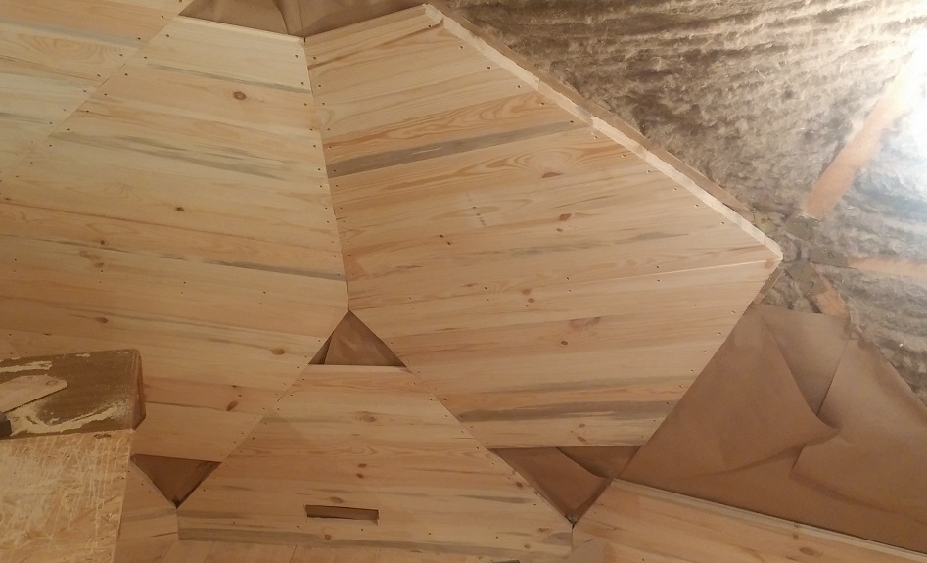
Документы/Фактические расходы/2017-08/2017-08-29 - 77.00 - [40$] - Отделка - обшивка купола часть 6.jpg
