peter-hanzo/KD/Документы/Фактические расходы/2017-08/2017-08-30 - 77.00 - [40$] - Крыша - подготовка для отливов.jpg

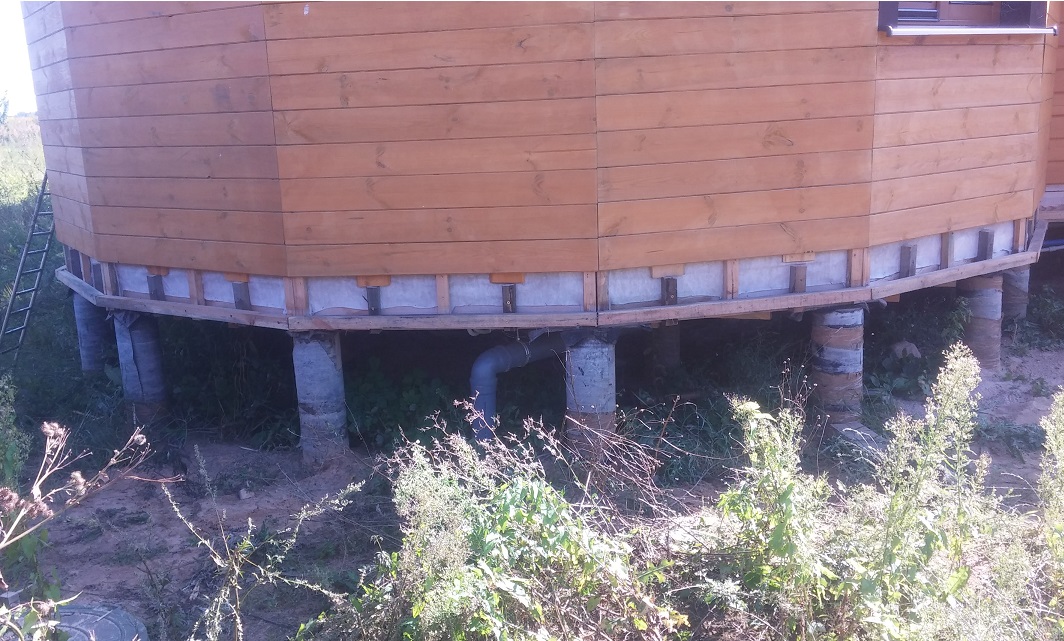
Документы/Фактические расходы/2017-08/2017-08-30 - 77.00 - [40$] - Крыша - подготовка для отливов.jpg
