peter-hanzo/KD/Документы/Фактические расходы/2017-08/2017-08-31 - 212.00 - 110$ - Отделка - доска для зашивки под домом.jpg

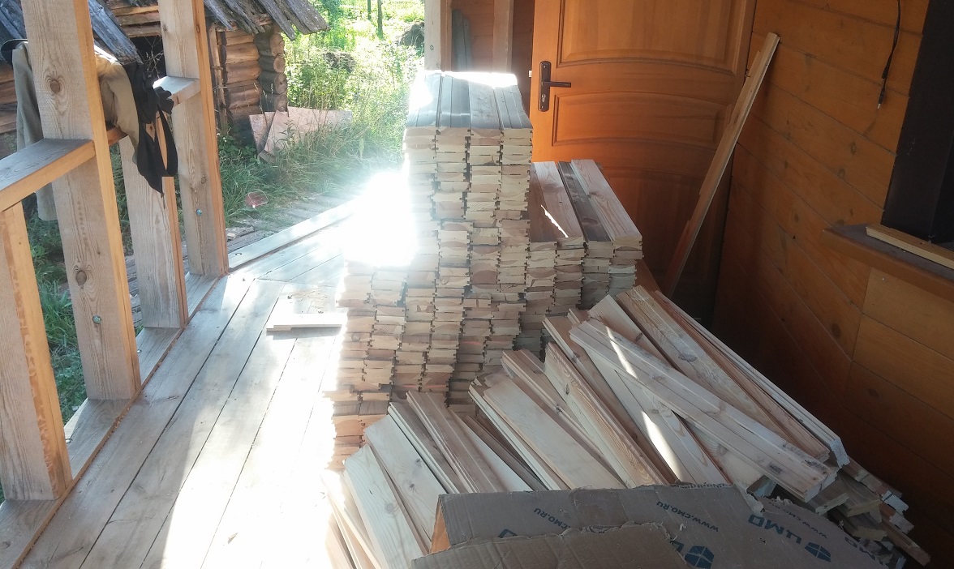
Документы/Фактические расходы/2017-08/2017-08-31 - 212.00 - 110$ - Отделка - доска для зашивки под домом.jpg
