peter-hanzo/KD/Документы/Фактические расходы/2017-08/2017-08-31 - 289.00 - 150$ - Отделка - доска для обшивки санузла.jpg

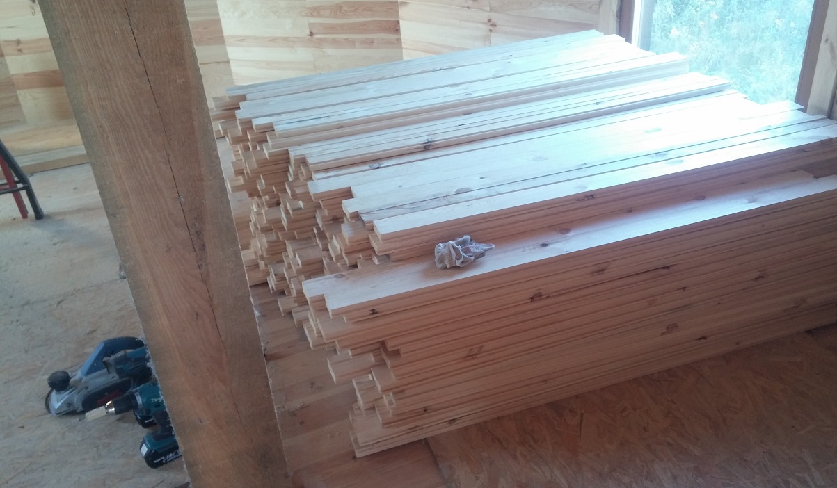
Документы/Фактические расходы/2017-08/2017-08-31 - 289.00 - 150$ - Отделка - доска для обшивки санузла.jpg
