peter-hanzo/KD/Документы/Фактические расходы/2017-09/2017-09-01 - 1511.80 - 780$ - Крыша - материалы для кровли.jpg

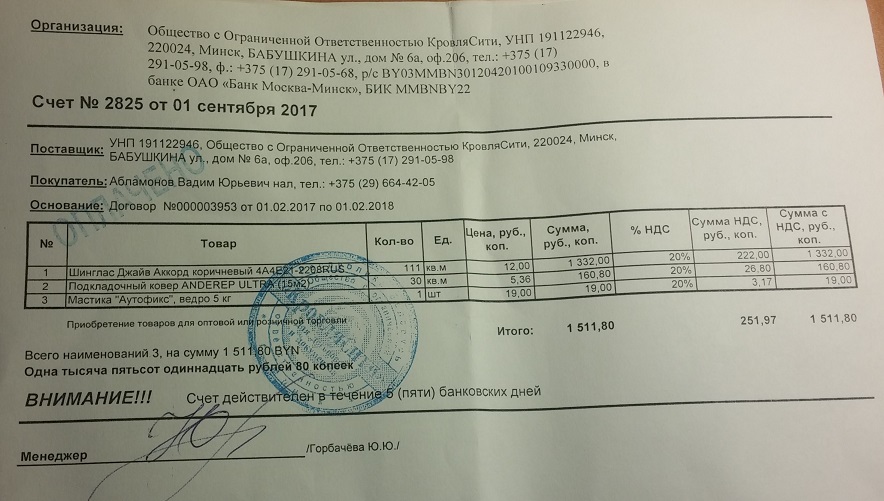
Документы/Фактические расходы/2017-09/2017-09-01 - 1511.80 - 780$ - Крыша - материалы для кровли.jpg
