peter-hanzo/KD/Документы/Фактические расходы/2017-09/2017-09-02 - 155.00 - 80$ - Крыша - монтаж отливов часть 2.jpg

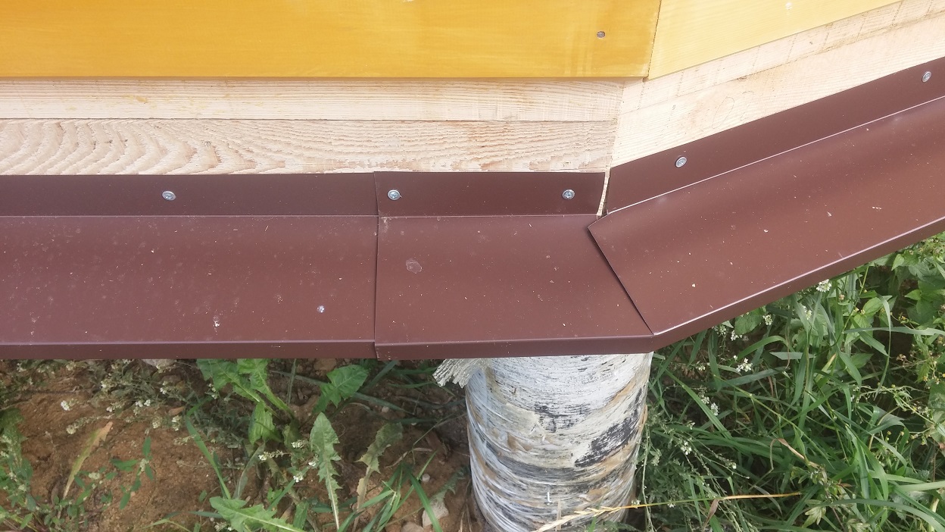
Документы/Фактические расходы/2017-09/2017-09-02 - 155.00 - 80$ - Крыша - монтаж отливов часть 2.jpg
