peter-hanzo/KD/Документы/Фактические расходы/2017-09/2017-09-02 - 310.00 - 160$ - Крыша - монтаж отливов часть 1.jpg

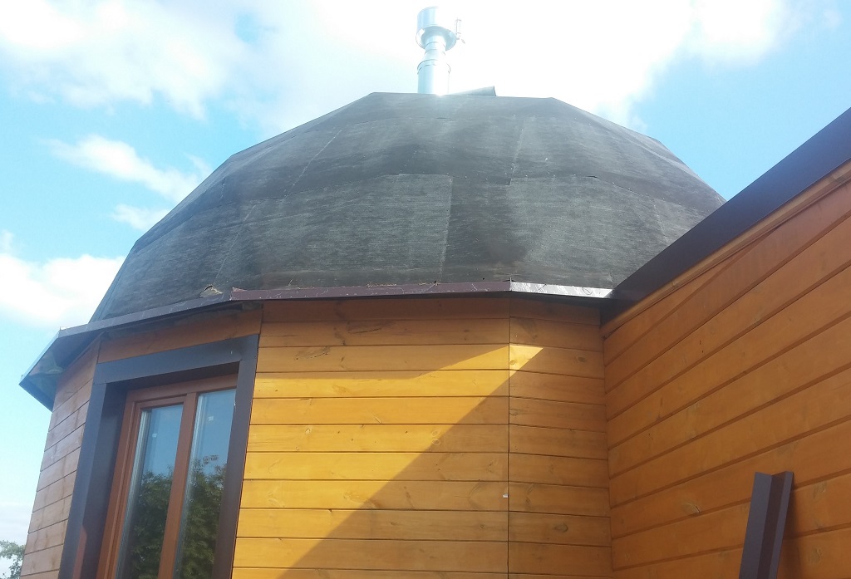
Документы/Фактические расходы/2017-09/2017-09-02 - 310.00 - 160$ - Крыша - монтаж отливов часть 1.jpg
