peter-hanzo/KD/Документы/Фактические расходы/2017-09/2017-09-03 - 58.00 - [30$] - Крыша - изготовление лестницы и мачты.jpg

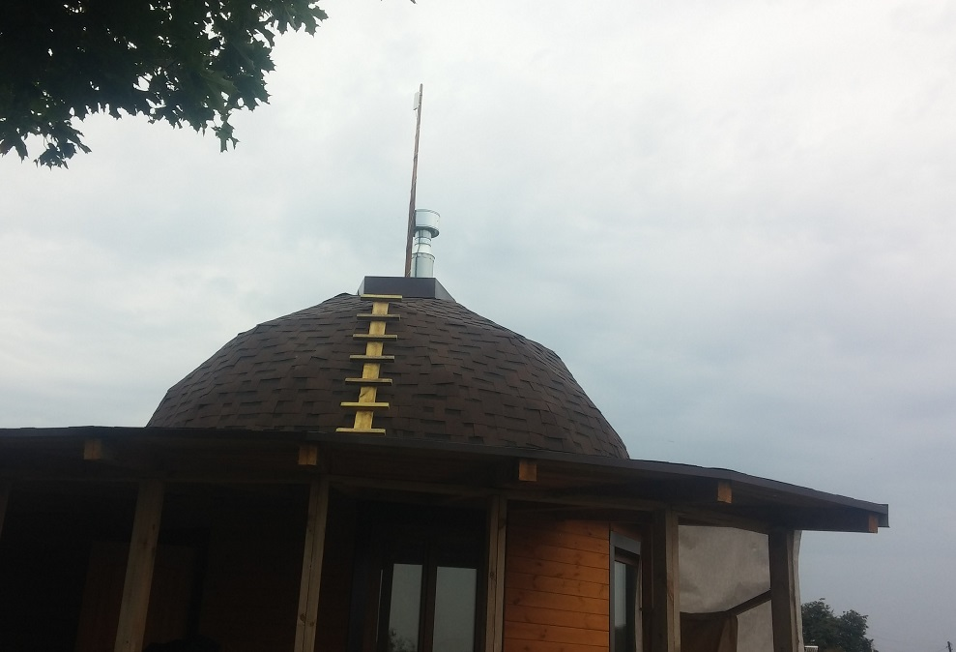
Документы/Фактические расходы/2017-09/2017-09-03 - 58.00 - [30$] - Крыша - изготовление лестницы и мачты.jpg
