peter-hanzo/KD/Документы/Фактические расходы/2017-09/2017-09-03 - 155.00 - 80$ - Крыша - монтаж отливов часть 3.jpg

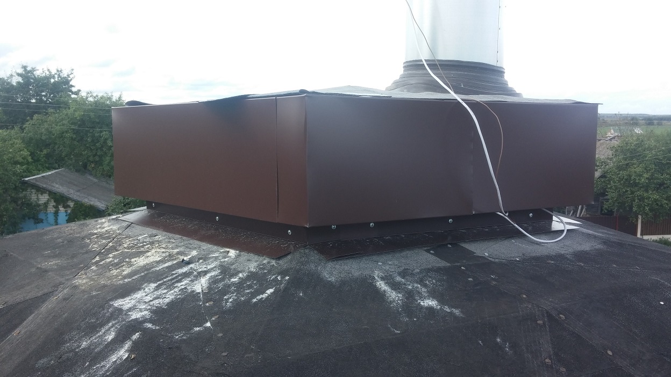
Документы/Фактические расходы/2017-09/2017-09-03 - 155.00 - 80$ - Крыша - монтаж отливов часть 3.jpg
