peter-hanzo/KD/Документы/Фактические расходы/2017-09/2017-09-07 - 581.00 - 300$ - Крыша - монтаж черепицы 1.jpg

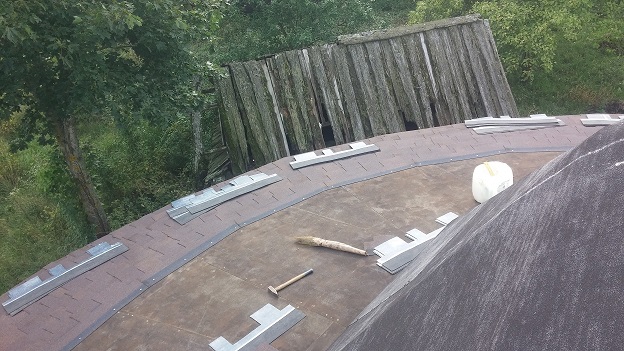
Документы/Фактические расходы/2017-09/2017-09-07 - 581.00 - 300$ - Крыша - монтаж черепицы 1.jpg
