peter-hanzo/KD/Документы/Фактические расходы/2017-09/2017-09-11 - 62.80 - 32$ - Крыша - материалы для кровли 2.jpg

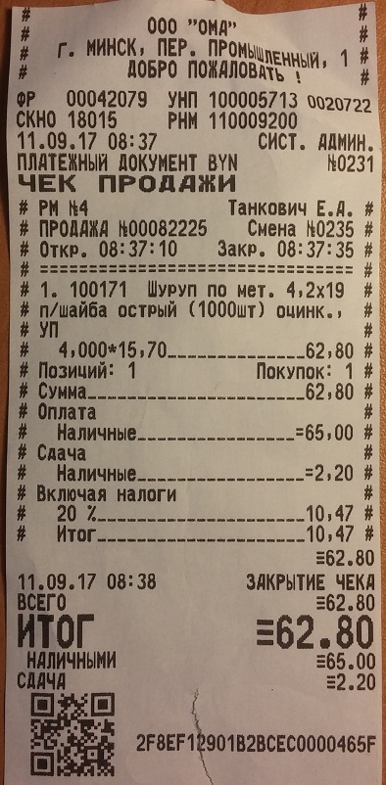
Документы/Фактические расходы/2017-09/2017-09-11 - 62.80 - 32$ - Крыша - материалы для кровли 2.jpg
