peter-hanzo/KD/Документы/Фактические расходы/2017-09/2017-09-11 - 581.00 - 300$ - Крыша - монтаж черепицы 2.jpg

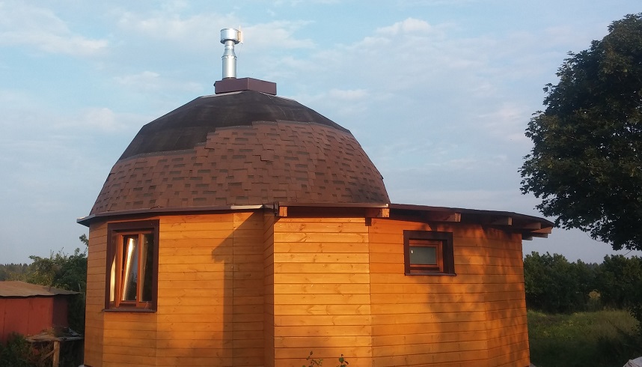
Документы/Фактические расходы/2017-09/2017-09-11 - 581.00 - 300$ - Крыша - монтаж черепицы 2.jpg
