peter-hanzo/KD/Документы/Фактические расходы/2017-09/2017-09-13 - 72.00 - 37$ - Крыша - материалы для кровли 3.jpg

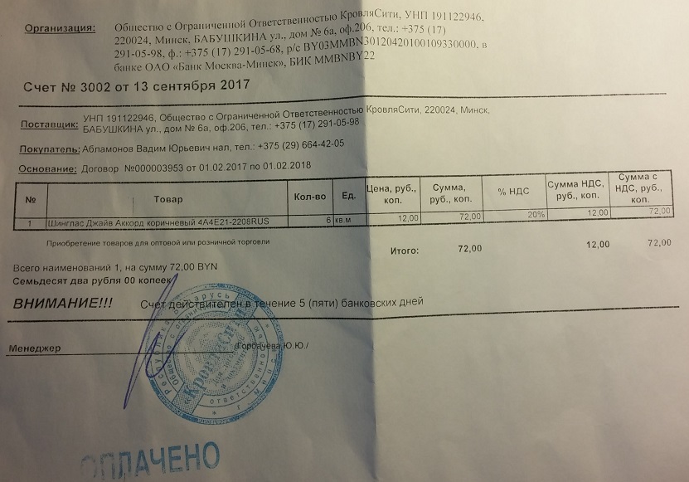
Документы/Фактические расходы/2017-09/2017-09-13 - 72.00 - 37$ - Крыша - материалы для кровли 3.jpg
