peter-hanzo/KD/Документы/Фактические расходы/2017-09/2017-09-13 - 360.27 - 185$ - Серверная - комплектующие.jpg

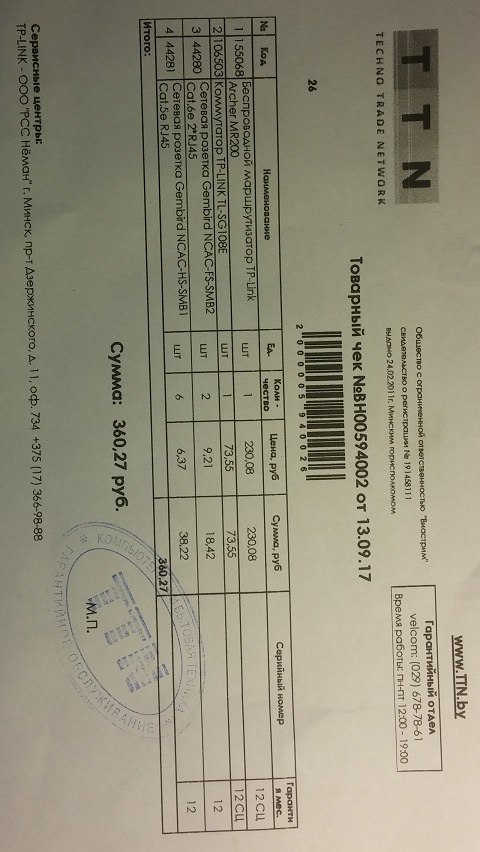
Документы/Фактические расходы/2017-09/2017-09-13 - 360.27 - 185$ - Серверная - комплектующие.jpg
