peter-hanzo/KD/Документы/Фактические расходы/2017-09/2017-09-13 - 581.00 - 300$ - Крыша - монтаж черепицы 3.jpg

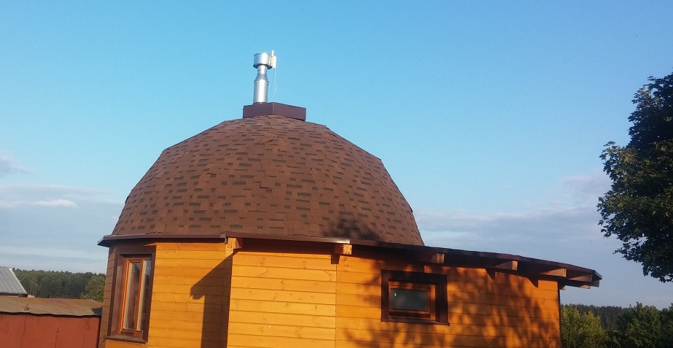
Документы/Фактические расходы/2017-09/2017-09-13 - 581.00 - 300$ - Крыша - монтаж черепицы 3.jpg
