peter-hanzo/KD/Документы/Фактические расходы/2017-09/2017-09-15 - 100.00 - 51$ - Благоустройство - две машины песка.jpg

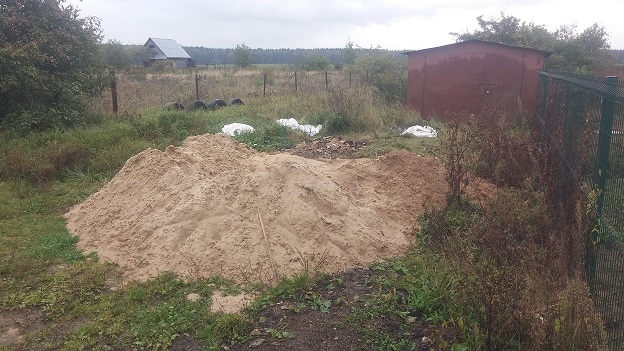
Документы/Фактические расходы/2017-09/2017-09-15 - 100.00 - 51$ - Благоустройство - две машины песка.jpg
