peter-hanzo/KD/Документы/Фактические расходы/2017-09/2017-09-17 - 128.00 - [65$] - Благоустройство - отмостка часть 2.jpg

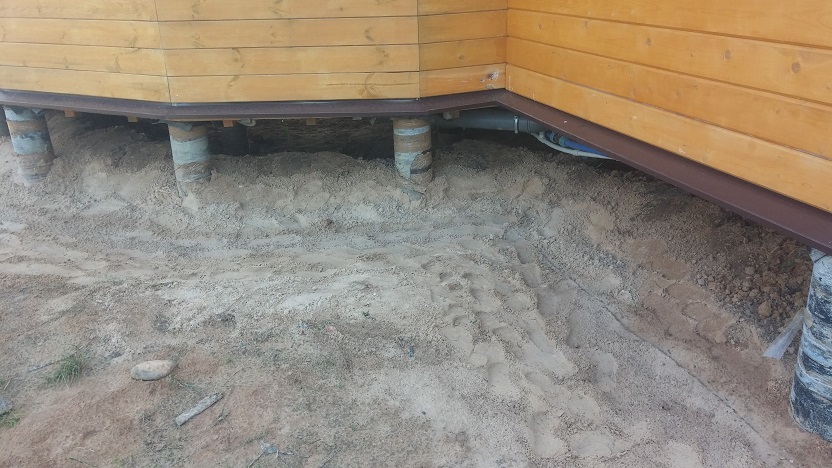
Документы/Фактические расходы/2017-09/2017-09-17 - 128.00 - [65$] - Благоустройство - отмостка часть 2.jpg
