peter-hanzo/KD/Документы/Фактические расходы/2017-09/2017-09-20 - 236.00 - [120$] - Стены - зашивка фундамента 1.jpg

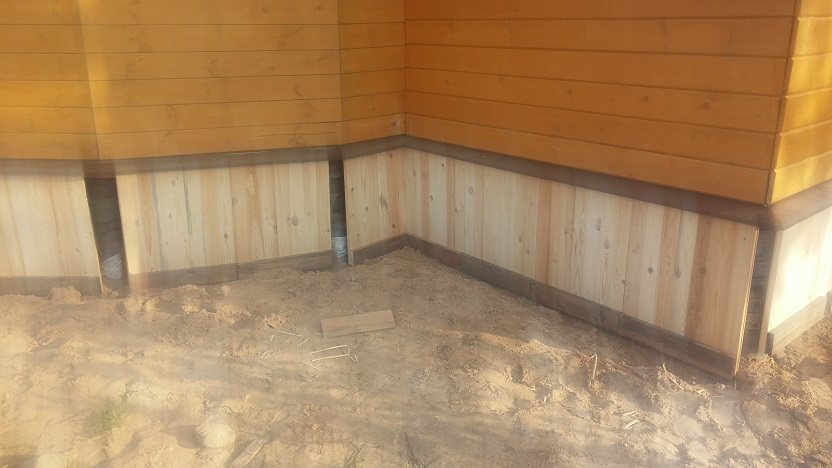
Документы/Фактические расходы/2017-09/2017-09-20 - 236.00 - [120$] - Стены - зашивка фундамента 1.jpg
