peter-hanzo/KD/Документы/Фактические расходы/2017-09/2017-09-23 - 47.51 - 24$ - Отделка - расходники 2.jpg

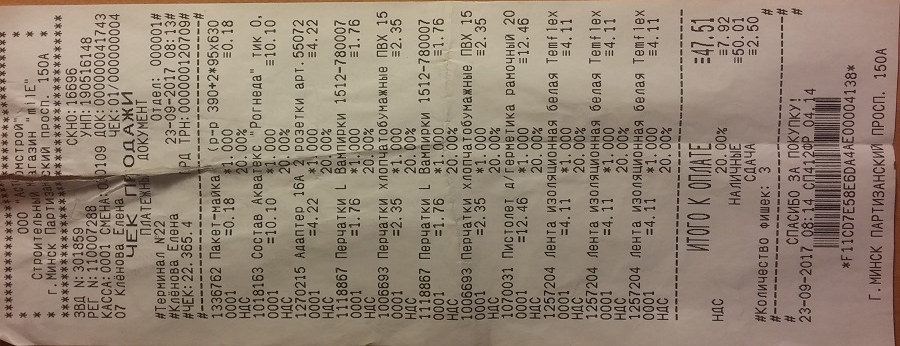
Документы/Фактические расходы/2017-09/2017-09-23 - 47.51 - 24$ - Отделка - расходники 2.jpg
