peter-hanzo/KD/Документы/Фактические расходы/2017-09/2017-09-25 - 13.96 - 7$ - Серверная - комплектующие 4.jpg

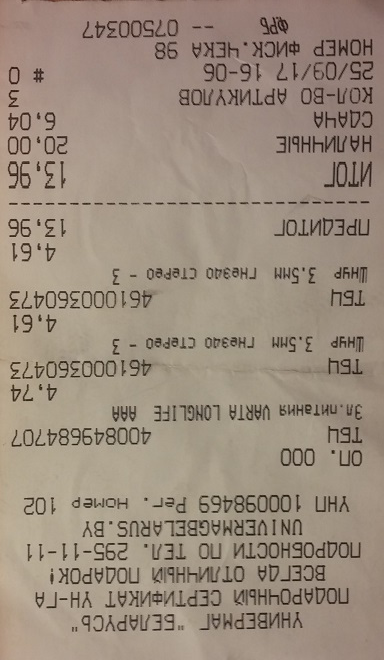
Документы/Фактические расходы/2017-09/2017-09-25 - 13.96 - 7$ - Серверная - комплектующие 4.jpg
