peter-hanzo/KD/Документы/Фактические расходы/2017-09/2017-09-25 - 118.00 - [60$] - Отделка - обшивка купола часть 7.jpg

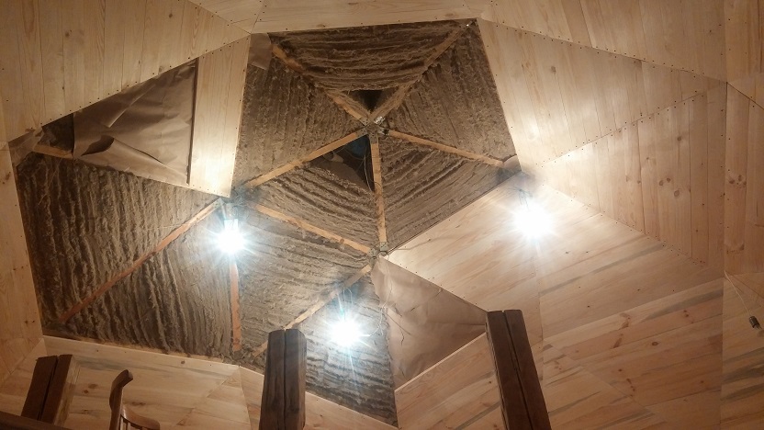
Документы/Фактические расходы/2017-09/2017-09-25 - 118.00 - [60$] - Отделка - обшивка купола часть 7.jpg
