peter-hanzo/KD/Документы/Фактические расходы/2017-09/2017-09-25 - 140.48 - 75$ - Отделка - комплектующие и расходники 2.jpg

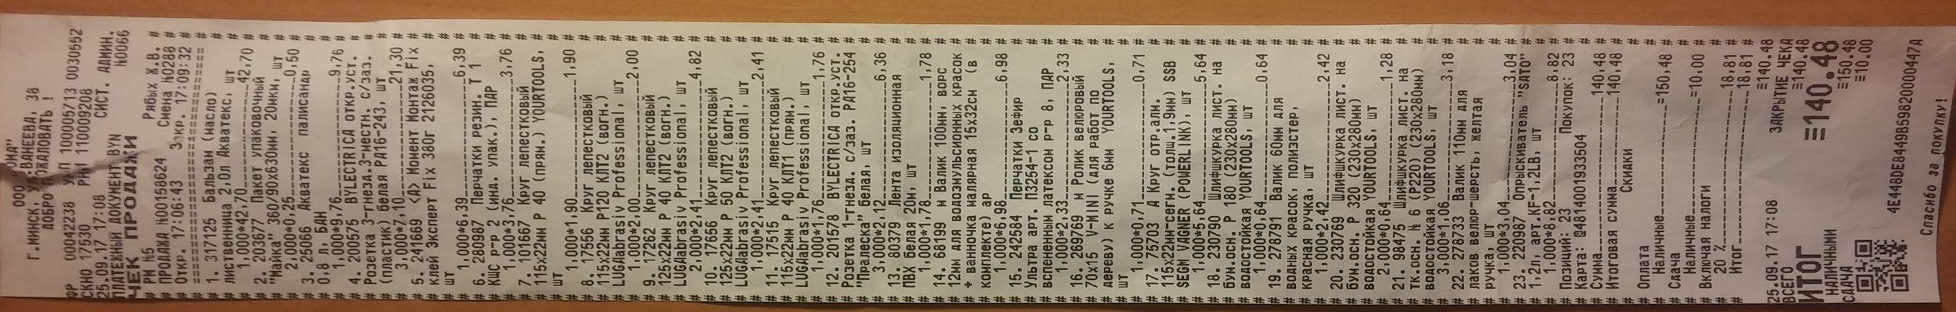
Документы/Фактические расходы/2017-09/2017-09-25 - 140.48 - 75$ - Отделка - комплектующие и расходники 2.jpg
