peter-hanzo/KD/Документы/Фактические расходы/2017-09/2017-09-27 - 177.00 - [90$] - Отделка - шлифовка и покраска каркаса.jpg

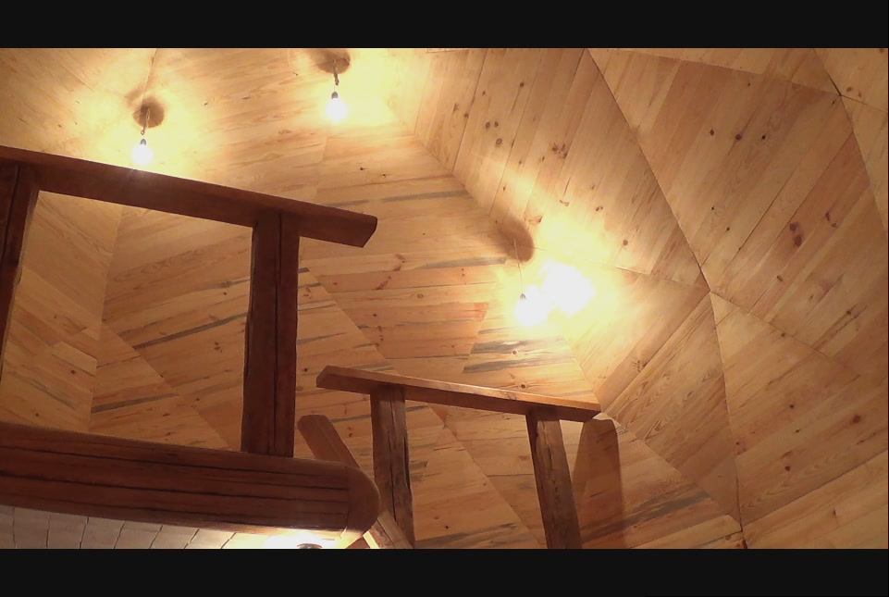
Документы/Фактические расходы/2017-09/2017-09-27 - 177.00 - [90$] - Отделка - шлифовка и покраска каркаса.jpg
