peter-hanzo/KD/Документы/Фактические расходы/2017-09/2017-09-29 - 31.12 - 16$ - Отделка - расходники 3.jpg

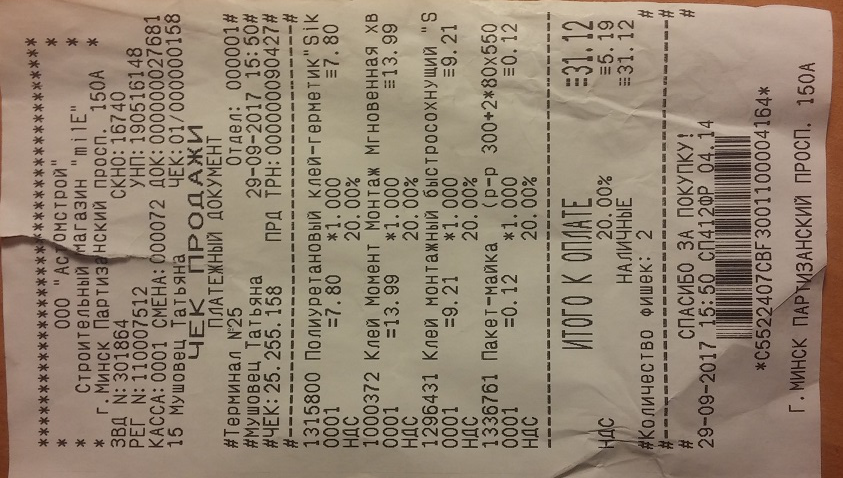
Документы/Фактические расходы/2017-09/2017-09-29 - 31.12 - 16$ - Отделка - расходники 3.jpg
