peter-hanzo/KD/Документы/Фактические расходы/2017-10/2017-10-01 - 118.00 - [60$] - Отделка - обшивка купола часть 8.jpg

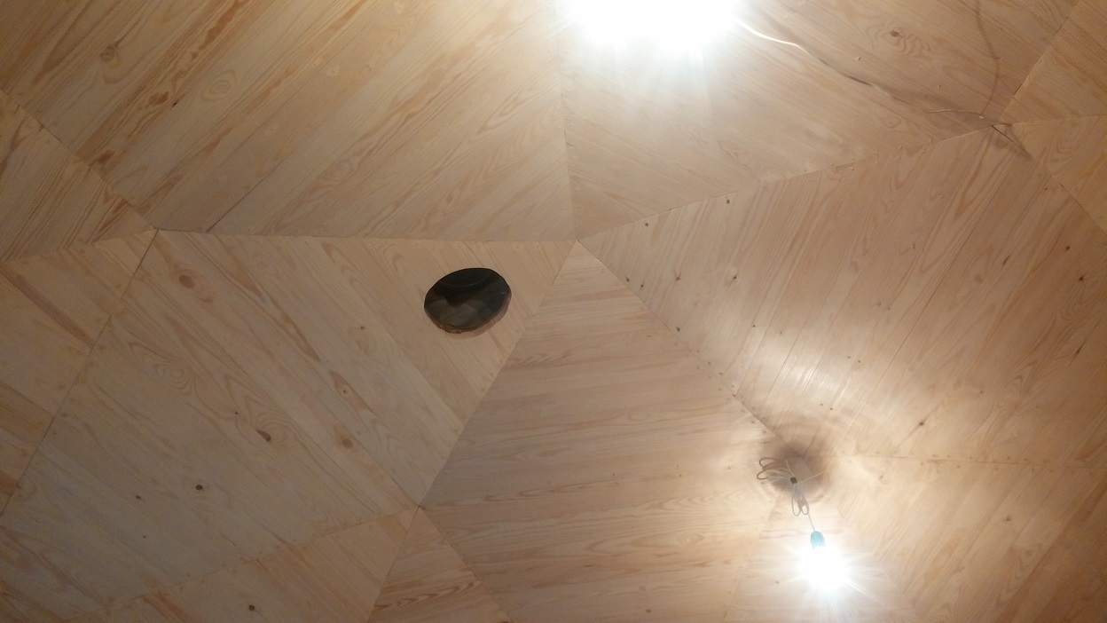
Документы/Фактические расходы/2017-10/2017-10-01 - 118.00 - [60$] - Отделка - обшивка купола часть 8.jpg
