peter-hanzo/KD/Документы/Фактические расходы/2017-10/2017-10-02 - 20.54 - 10$ - Отделка - расходники 4.jpg

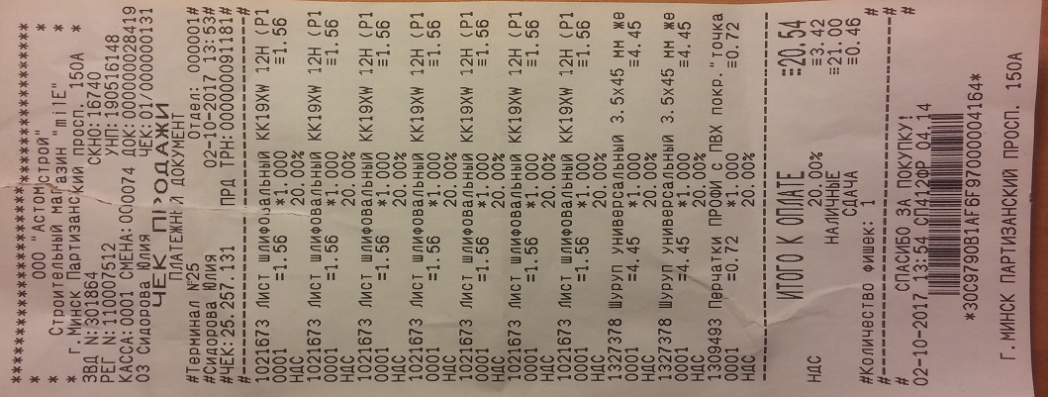
Документы/Фактические расходы/2017-10/2017-10-02 - 20.54 - 10$ - Отделка - расходники 4.jpg
