peter-hanzo/KD/Документы/Фактические расходы/2017-10/2017-10-02 - 98.00 - [80$] - Отделка - шпатлевка и шлифовка купола.jpg

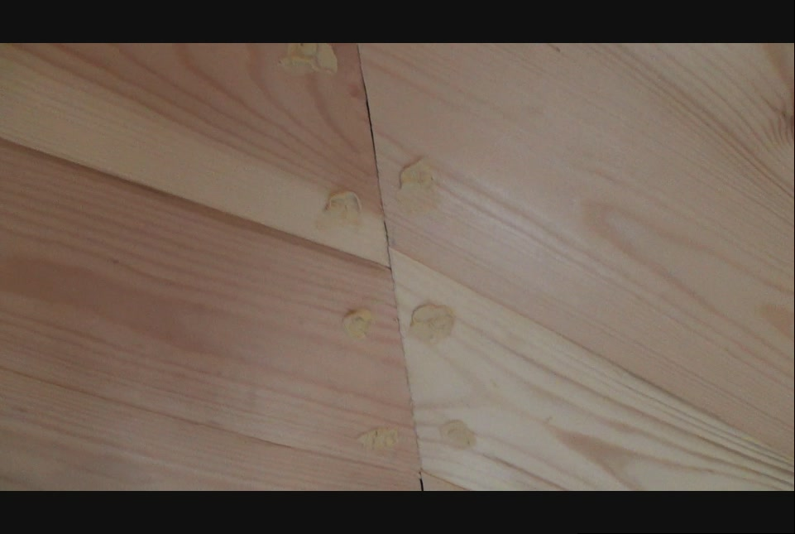
Документы/Фактические расходы/2017-10/2017-10-02 - 98.00 - [80$] - Отделка - шпатлевка и шлифовка купола.jpg
