peter-hanzo/KD/Документы/Фактические расходы/2017-10/2017-10-03 - 39.00 - [20$] - Отделка - покраска пола 1.jpg

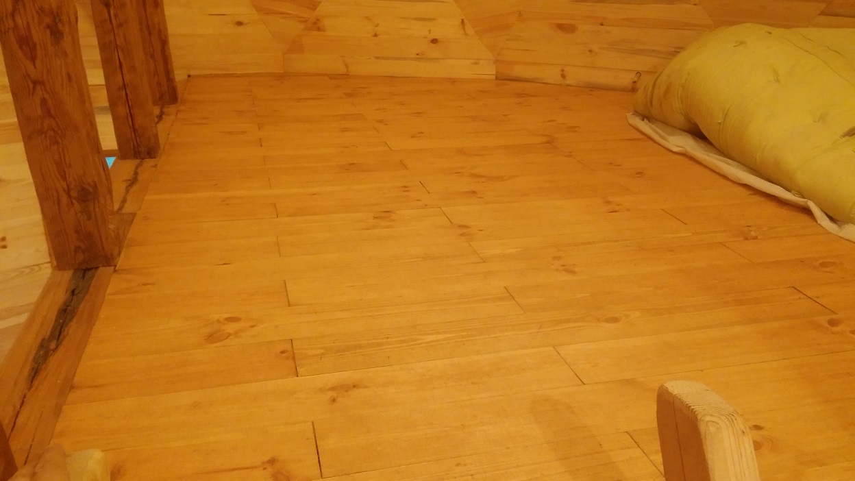
Документы/Фактические расходы/2017-10/2017-10-03 - 39.00 - [20$] - Отделка - покраска пола 1.jpg
