peter-hanzo/KD/Документы/Фактические расходы/2017-10/2017-10-03 - 78.00 - [40$] - Отделка - покраска пола 2.jpg

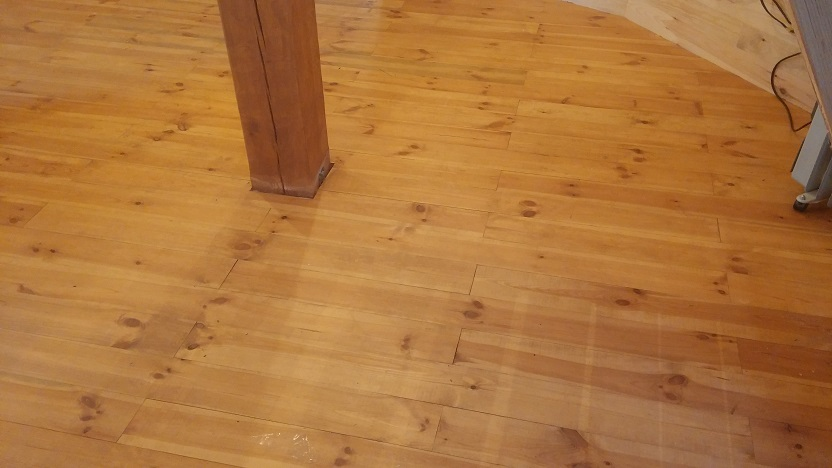
Документы/Фактические расходы/2017-10/2017-10-03 - 78.00 - [40$] - Отделка - покраска пола 2.jpg
