peter-hanzo/KD/Документы/Фактические расходы/2017-10/2017-10-03 - 236.00 - [120$] - Отделка - покраска стен и купола.jpg

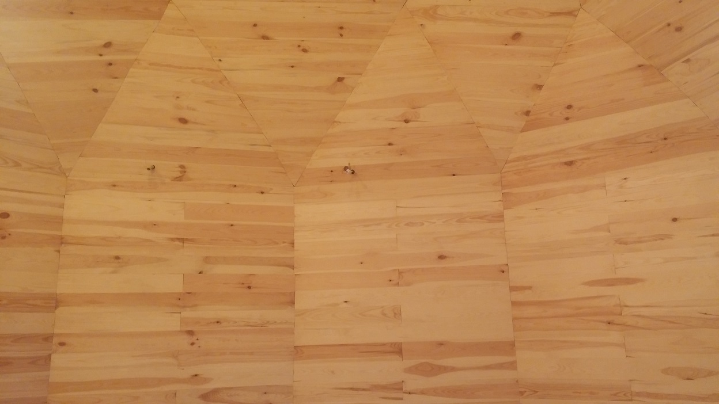
Документы/Фактические расходы/2017-10/2017-10-03 - 236.00 - [120$] - Отделка - покраска стен и купола.jpg
