peter-hanzo/KD/Документы/Фактические расходы/2017-10/2017-10-05 - 69.00 - [35$] - Отделка - монтаж и покраска наличников.jpg

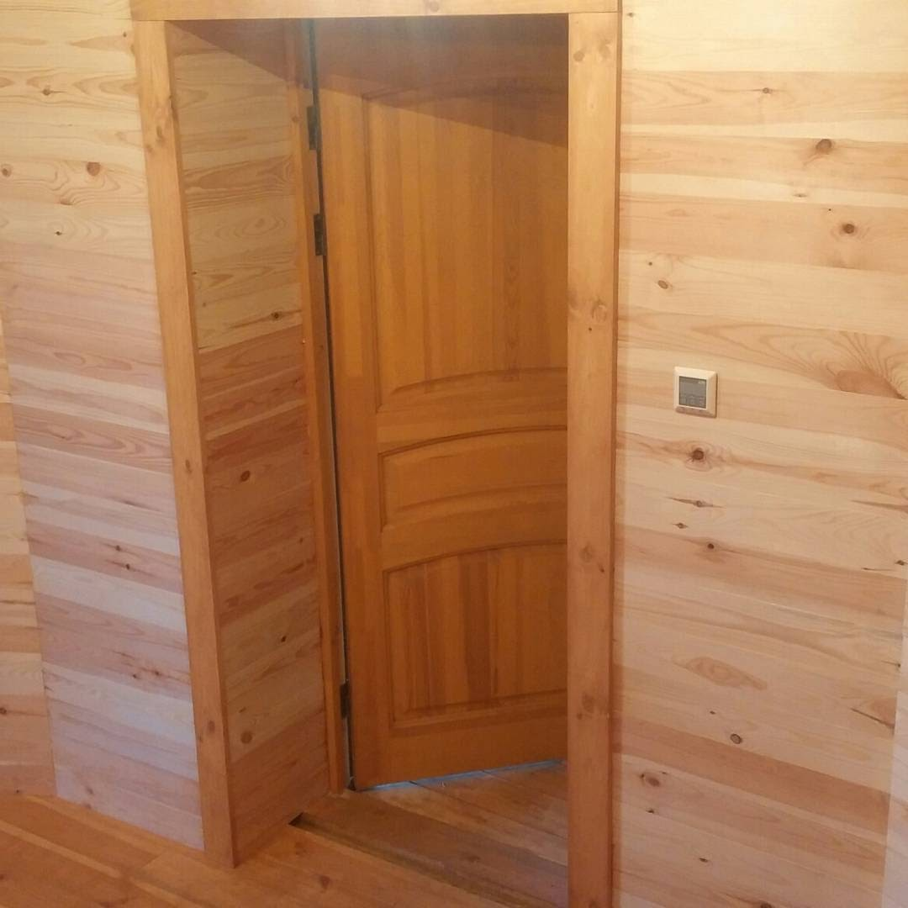
Документы/Фактические расходы/2017-10/2017-10-05 - 69.00 - [35$] - Отделка - монтаж и покраска наличников.jpg
