peter-hanzo/KD/Документы/Фактические расходы/2017-10/2017-10-05 - 256.00 - 130$ - Электросети - создание проекта.jpg

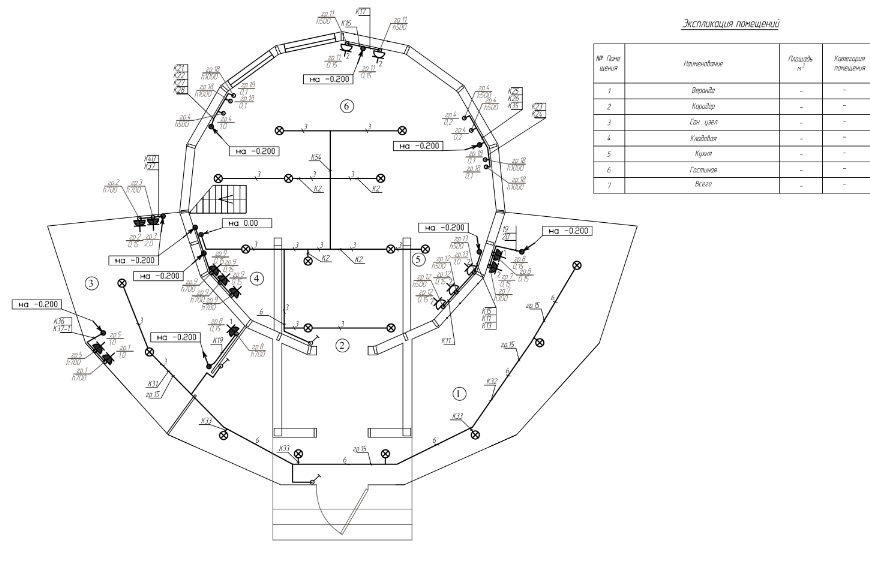
Документы/Фактические расходы/2017-10/2017-10-05 - 256.00 - 130$ - Электросети - создание проекта.jpg
