peter-hanzo/KD/Документы/Фактические расходы/2017-10/2017-10-06 - 8.9 - 5$ - Отделка - расходники 5.jpg

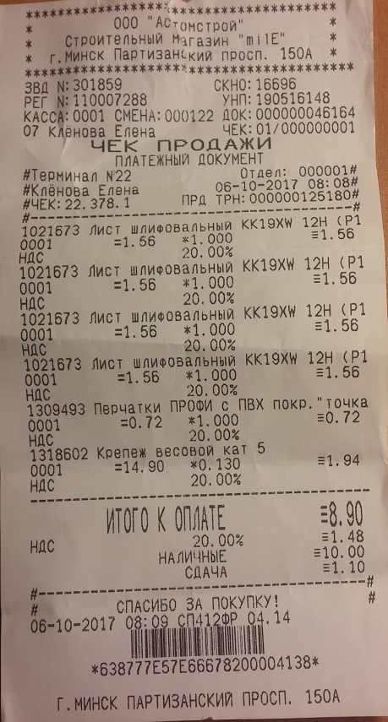
Документы/Фактические расходы/2017-10/2017-10-06 - 8.9 - 5$ - Отделка - расходники 5.jpg
