peter-hanzo/KD/Документы/Фактические расходы/2017-10/2017-10-06 - 49.00 - [25$] - Отделка - установка диффузора.jpg

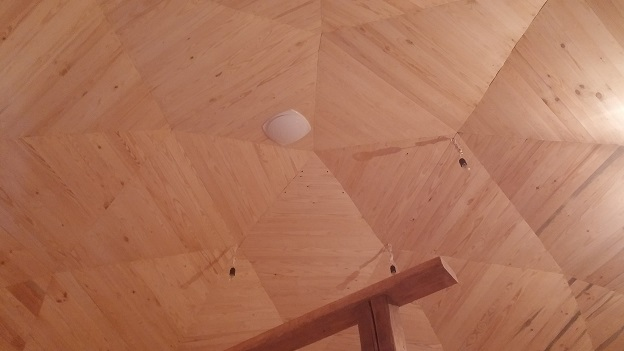
Документы/Фактические расходы/2017-10/2017-10-06 - 49.00 - [25$] - Отделка - установка диффузора.jpg
