peter-hanzo/KD/Документы/Фактические расходы/2017-10/2017-10-07 - 59.00 - [30$] - Отделка - установка вентрешеток.jpg

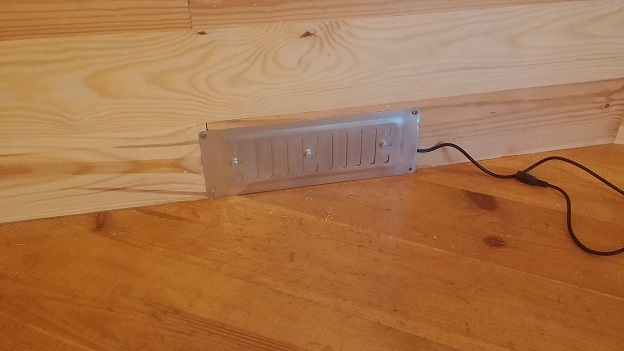
Документы/Фактические расходы/2017-10/2017-10-07 - 59.00 - [30$] - Отделка - установка вентрешеток.jpg
