peter-hanzo/KD/Документы/Фактические расходы/2018-07/2018-07-06 - 26.17 - 13$ - Санузел - материалы 1 .jpg

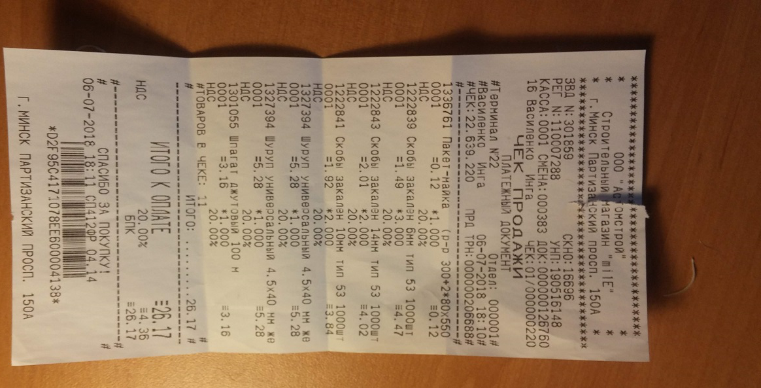
Документы/Фактические расходы/2018-07/2018-07-06 - 26.17 - 13$ - Санузел - материалы 1 .jpg
