peter-hanzo/KD/Документы/Фактические расходы/2018-07/2018-07-17 - 20.00 - 10$ - Санузел - монтаж вытяжки.jpg

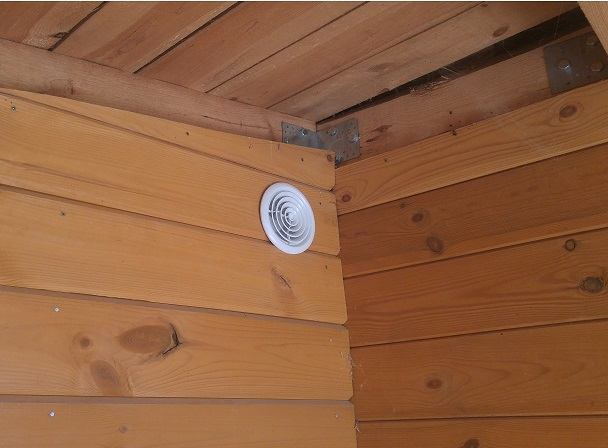
Документы/Фактические расходы/2018-07/2018-07-17 - 20.00 - 10$ - Санузел - монтаж вытяжки.jpg
