peter-hanzo/KD/Документы/Фактические расходы/2018-07/2018-07-25 - 159.00 - 80$ - Санузел - обшивка стен часть 2.jpg

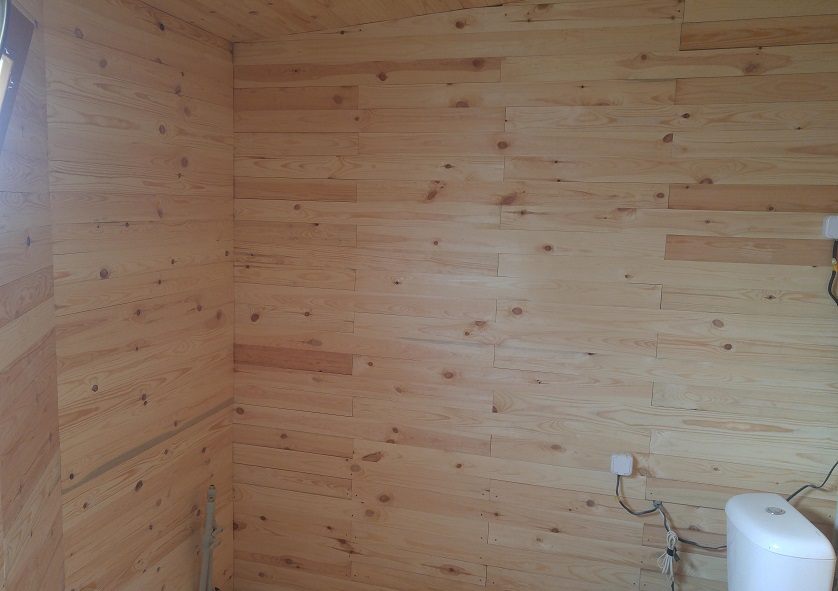
Документы/Фактические расходы/2018-07/2018-07-25 - 159.00 - 80$ - Санузел - обшивка стен часть 2.jpg
