peter-hanzo/KD/Документы/Фактические расходы/2018-09/2018-09-06 - 56.86 - 26$ - Электросети - автоматы.jpg

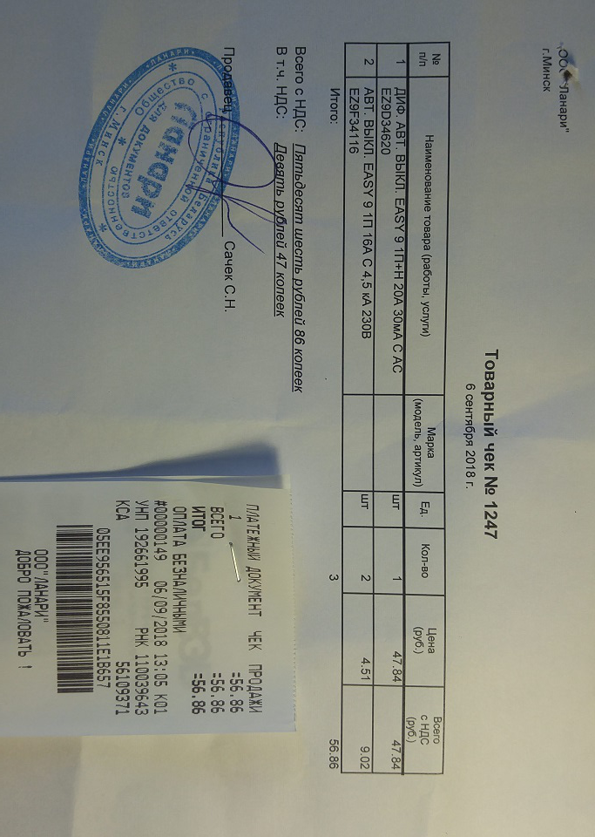
Документы/Фактические расходы/2018-09/2018-09-06 - 56.86 - 26$ - Электросети - автоматы.jpg
