peter-hanzo/KD/Документы/Фактические расходы/2018-09/2018-09-13 - 43.09 - 20$ - Санузел - герметики для пола.jpg

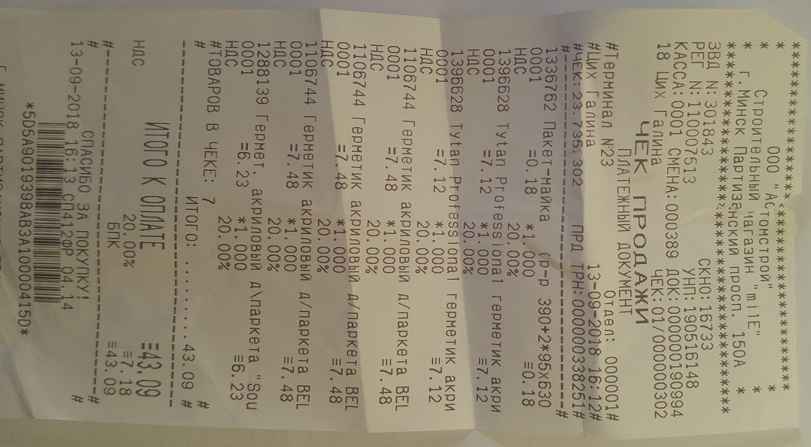
Документы/Фактические расходы/2018-09/2018-09-13 - 43.09 - 20$ - Санузел - герметики для пола.jpg
