peter-hanzo/KD/Документы/Фактические расходы/2018-09/2018-09-20 - 60.00 - 28$ - Веранда - зашивка стены.jpg

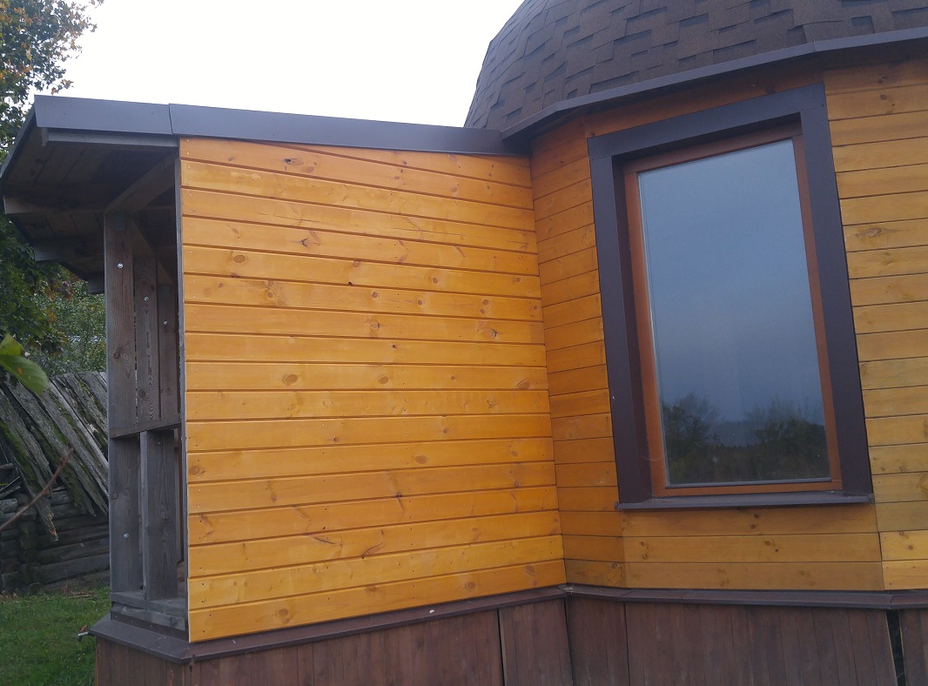
Документы/Фактические расходы/2018-09/2018-09-20 - 60.00 - 28$ - Веранда - зашивка стены.jpg
