peter-hanzo/KD/Документы/Фото/20150729_193632.jpg

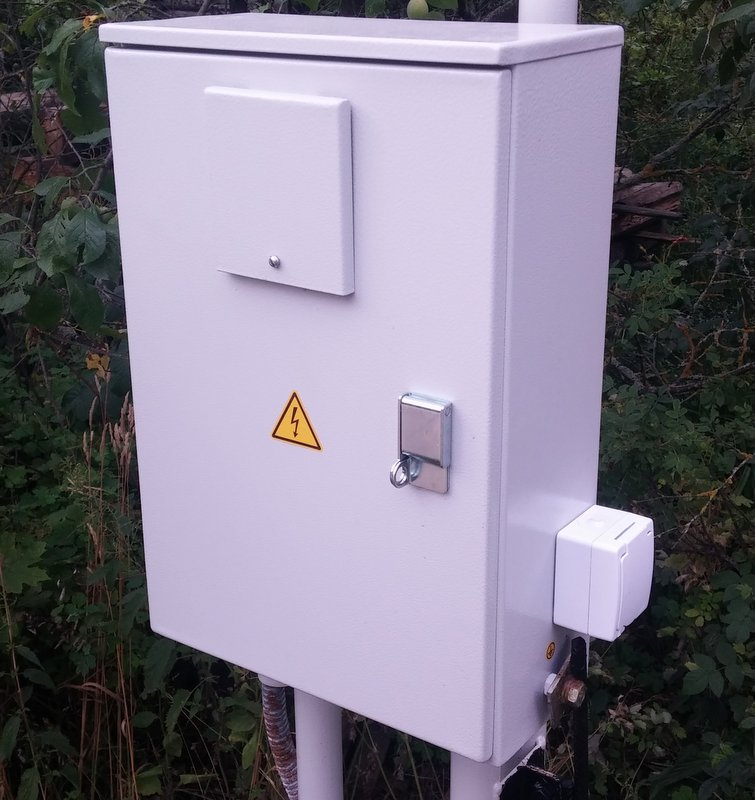
Документы/Фото/20150729_193632.jpg
