peter-hanzo/KD/Документы/Фото/20150819_125832.jpg

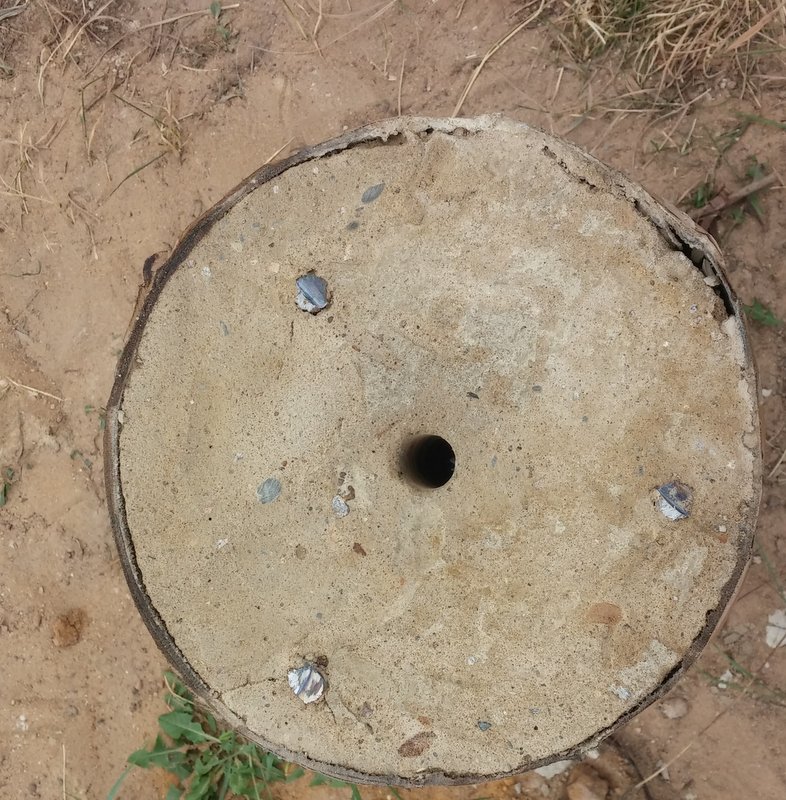
Документы/Фото/20150819_125832.jpg
