peter-hanzo/KD/Документы/Фото/20150819_130000.jpg

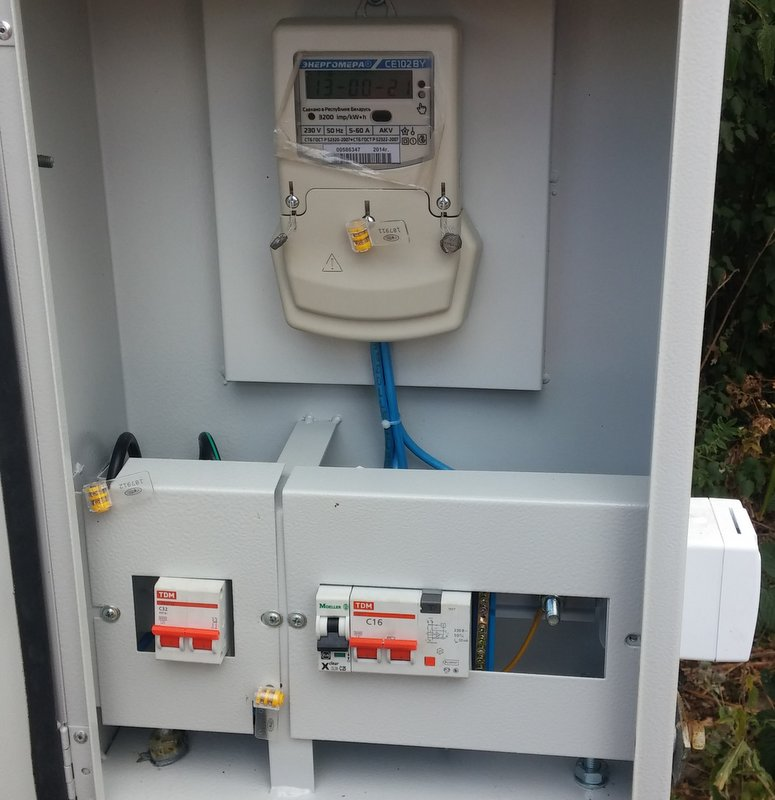
Документы/Фото/20150819_130000.jpg
