peter-hanzo/KD/Документы/Фото/20151011_103024.jpg

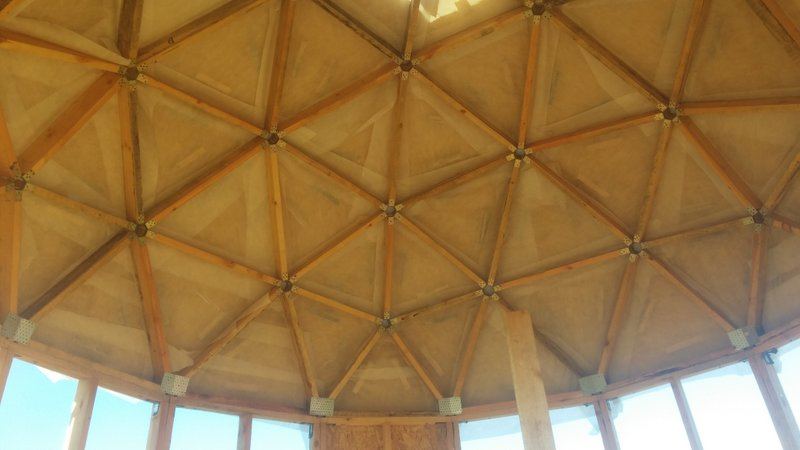
Документы/Фото/20151011_103024.jpg
