peter-hanzo/KD/Документы/Фото/20151011_103039.jpg

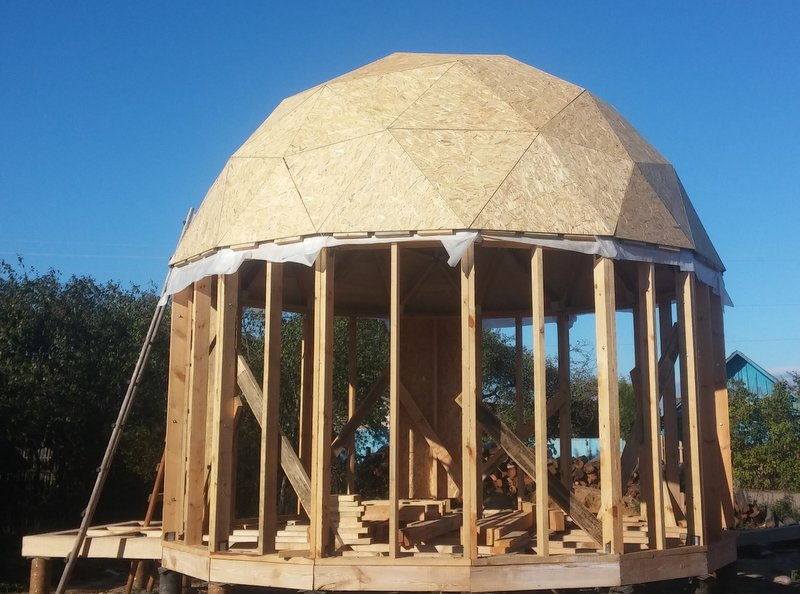
Документы/Фото/20151011_103039.jpg
