peter-hanzo/KD/Документы/Фото/20160522_205530.jpg

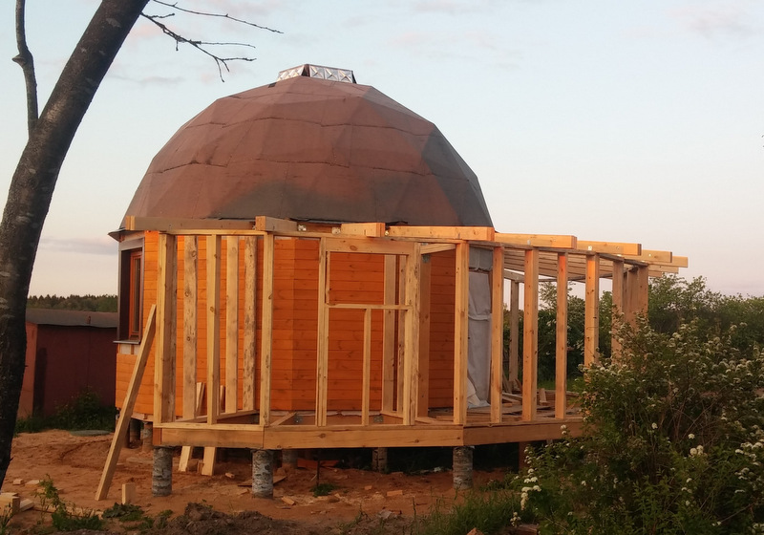
Документы/Фото/20160522_205530.jpg
