peter-hanzo/KD/Документы/Фото/20160524_100009.jpg

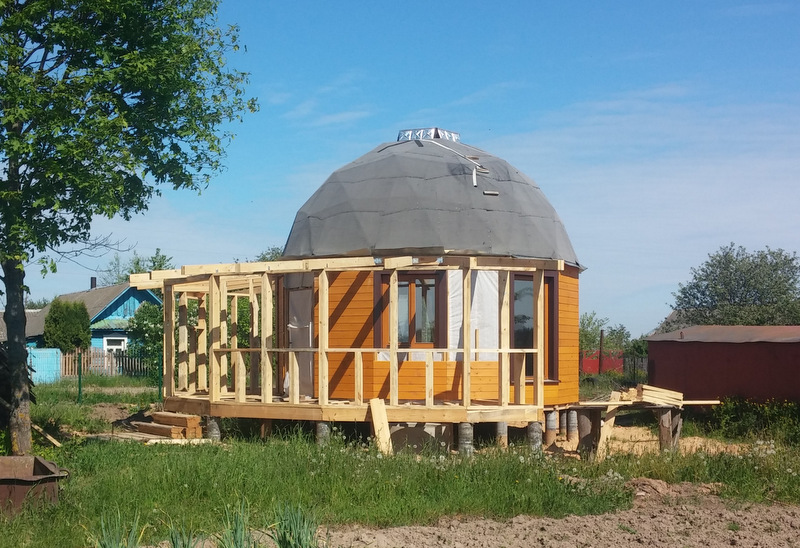
Документы/Фото/20160524_100009.jpg
