peter-hanzo/KD/Документы/Фото/20160524_174023.jpg

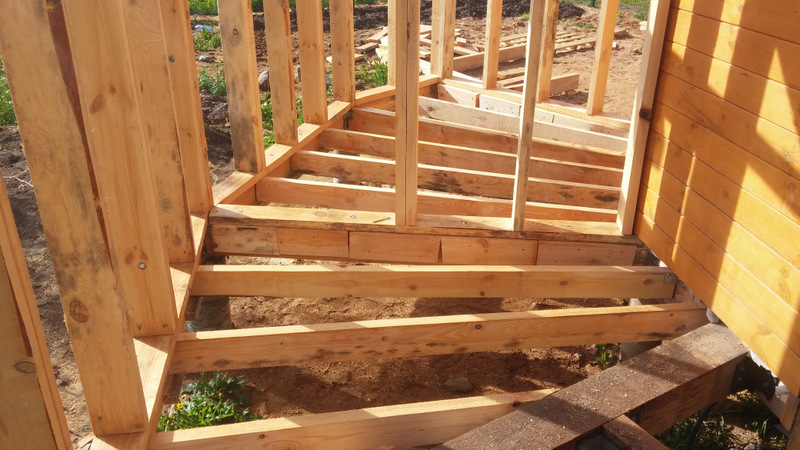
Документы/Фото/20160524_174023.jpg
