peter-hanzo/KD/Документы/Фото/20160606_160915.jpg

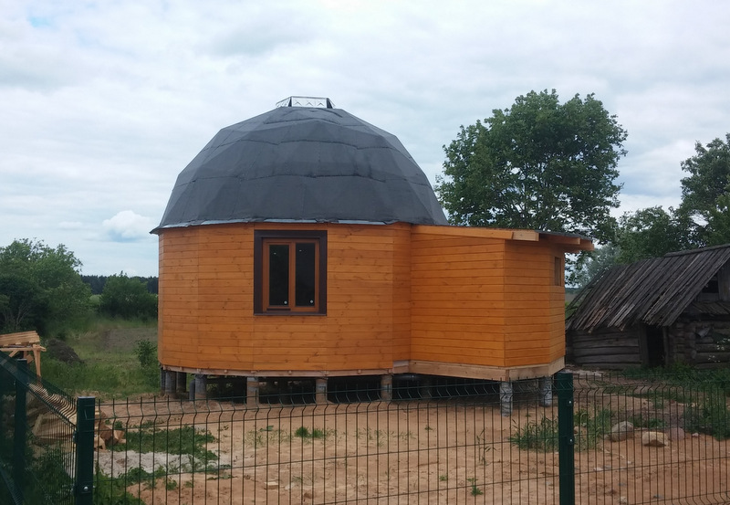
Документы/Фото/20160606_160915.jpg
