peter-hanzo/KD/Документы/Фото/20160606_161140.jpg

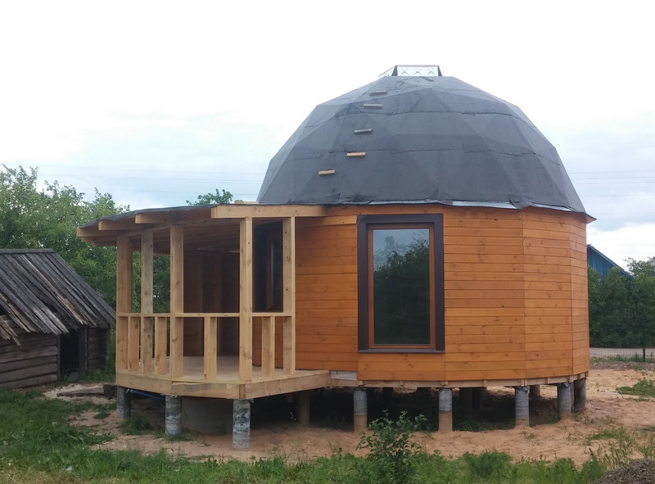
Документы/Фото/20160606_161140.jpg
