peter-hanzo/KD/Документы/Фото/купол1.jpg

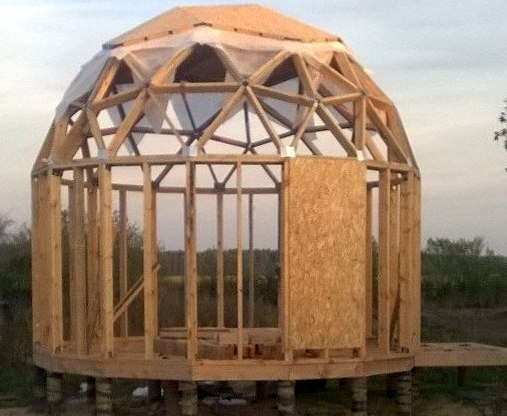
Документы/Фото/купол1.jpg
