peter-hanzo/KD/Документы/Чертежи/Архитектура (эскизный)/план2.png

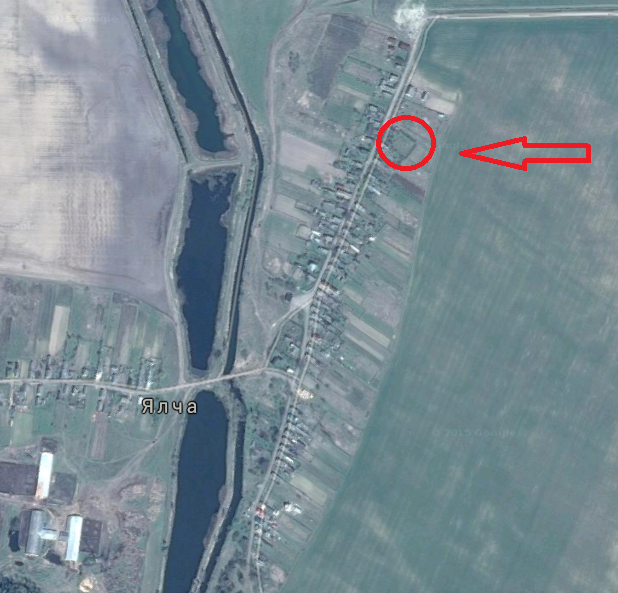
Документы/Чертежи/Архитектура (эскизный)/план2.png
