peter-hanzo/KD/Документы/Чертежи/Архитектура (эскизный)/ситуационный план.jpg

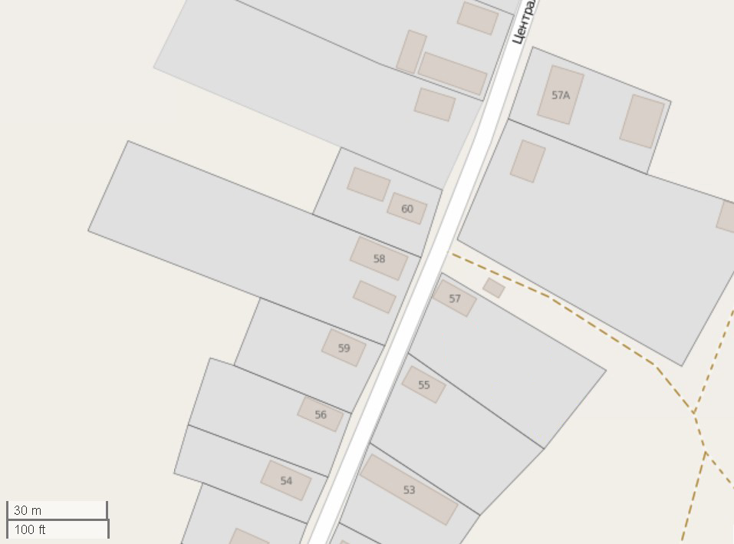
Документы/Чертежи/Архитектура (эскизный)/ситуационный план.jpg
