peter-hanzo/KD/Документы/Чертежи/Конструктив/Балка купола-DD.png

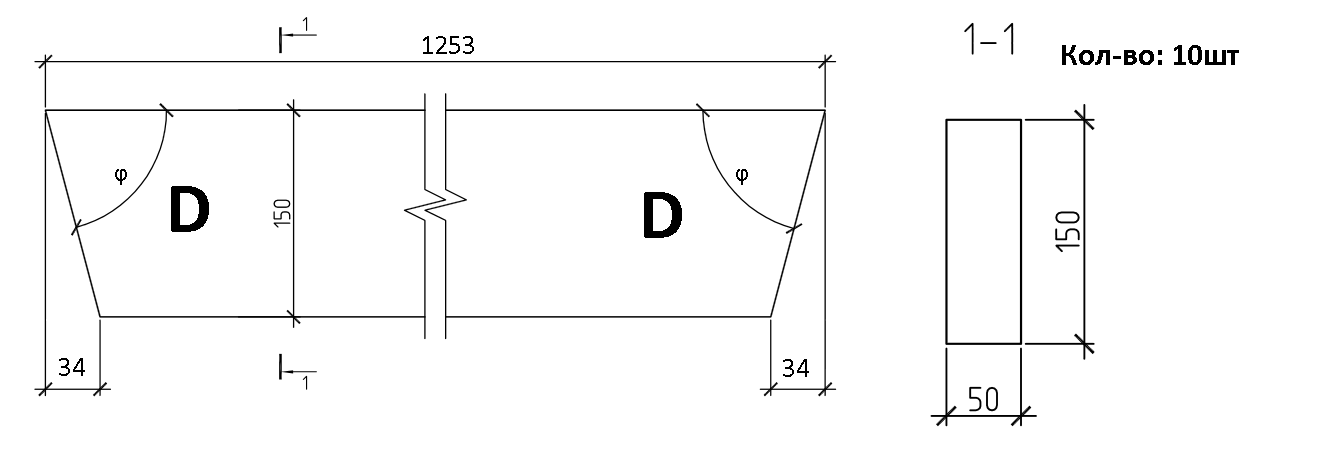
Документы/Чертежи/Конструктив/Балка купола-DD.png
