peter-hanzo/KD/Документы/Чертежи/Конструктив/Балка купола-СС.png

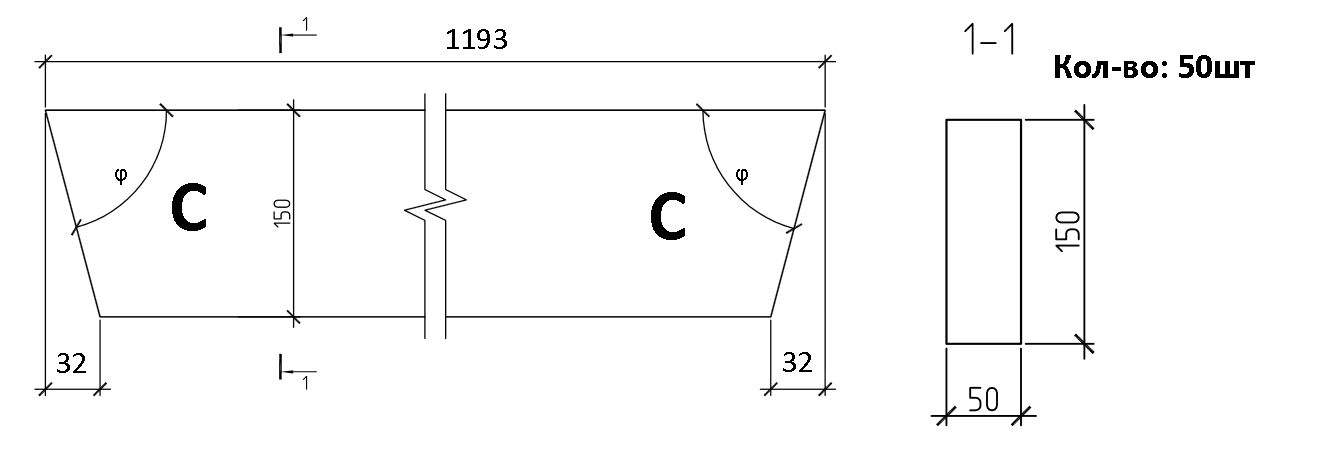
Документы/Чертежи/Конструктив/Балка купола-СС.png
