peter-hanzo/KD/Документы/Чертежи/Конструктив/Балка райзера-3.png

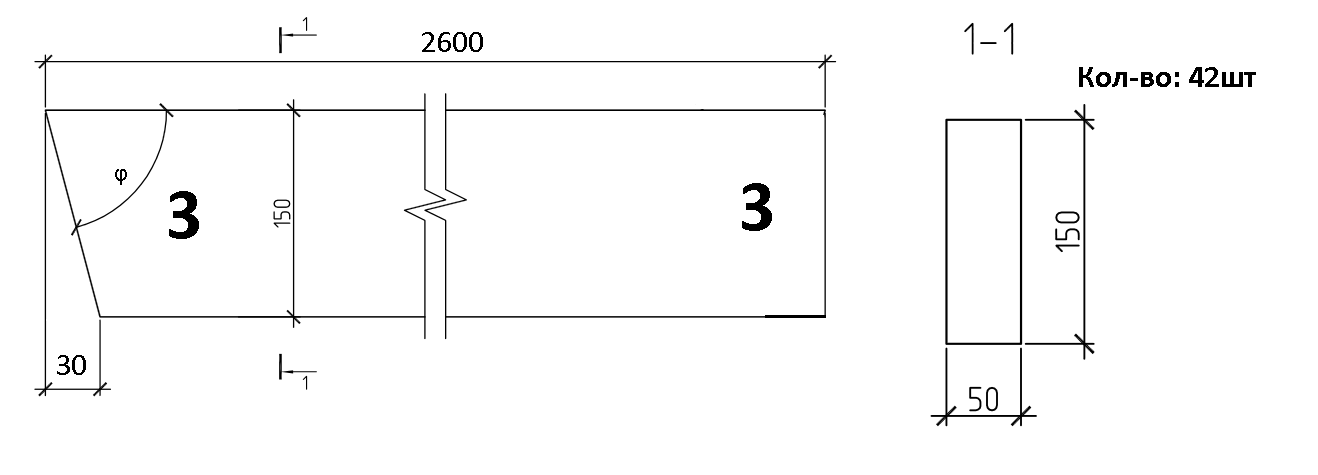
Документы/Чертежи/Конструктив/Балка райзера-3.png
