peter-hanzo/KD/Скетчи/1.jpg

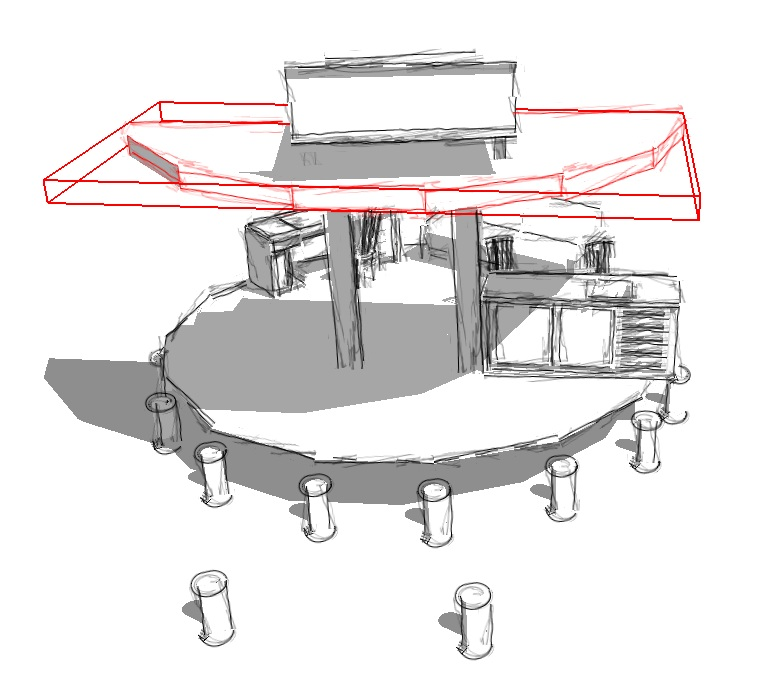
Скетчи/1.jpg
