peter-hanzo/KD/Скетчи/2.jpg

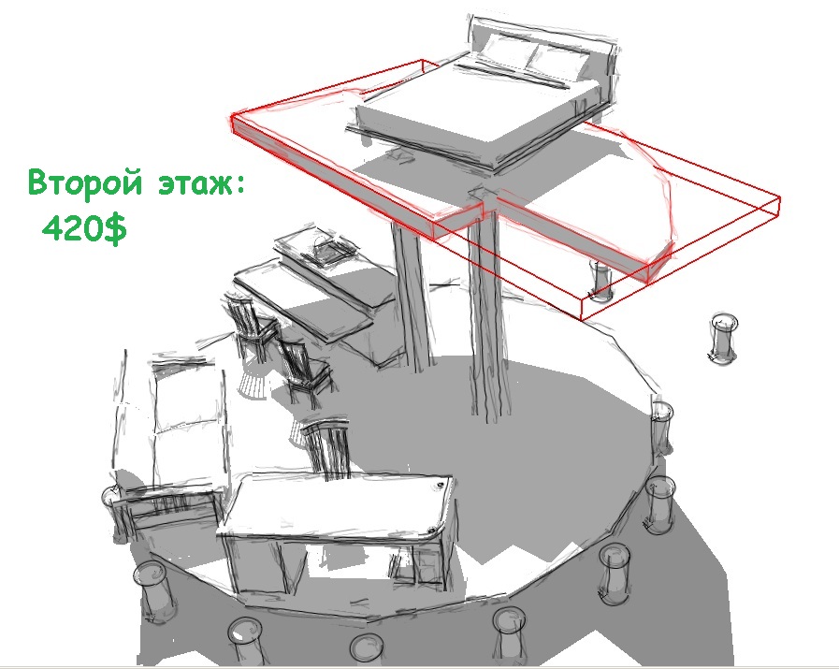
Скетчи/2.jpg
