peter-hanzo/KD/Скетчи/4.jpg

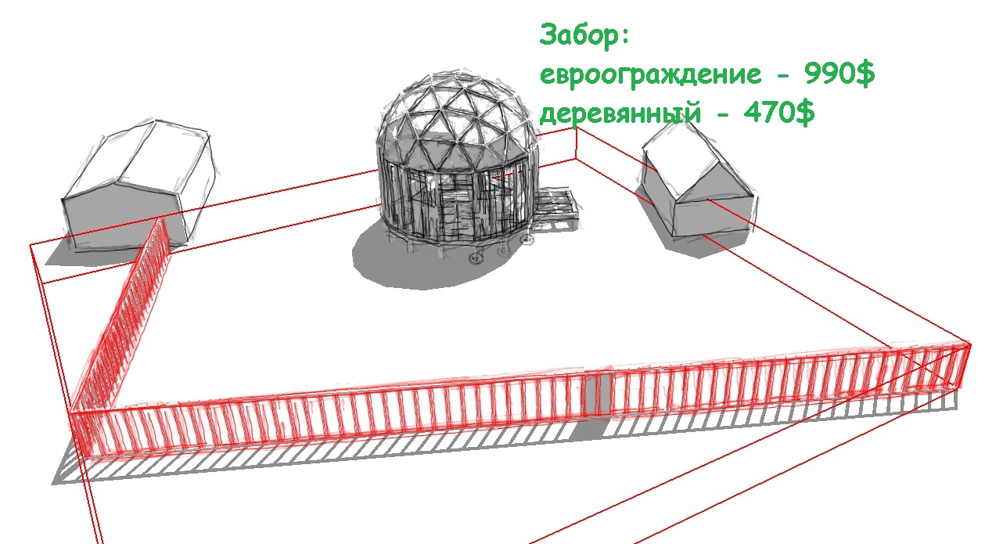
Скетчи/4.jpg
