peter-hanzo/KD/Скетчи/5.jpg

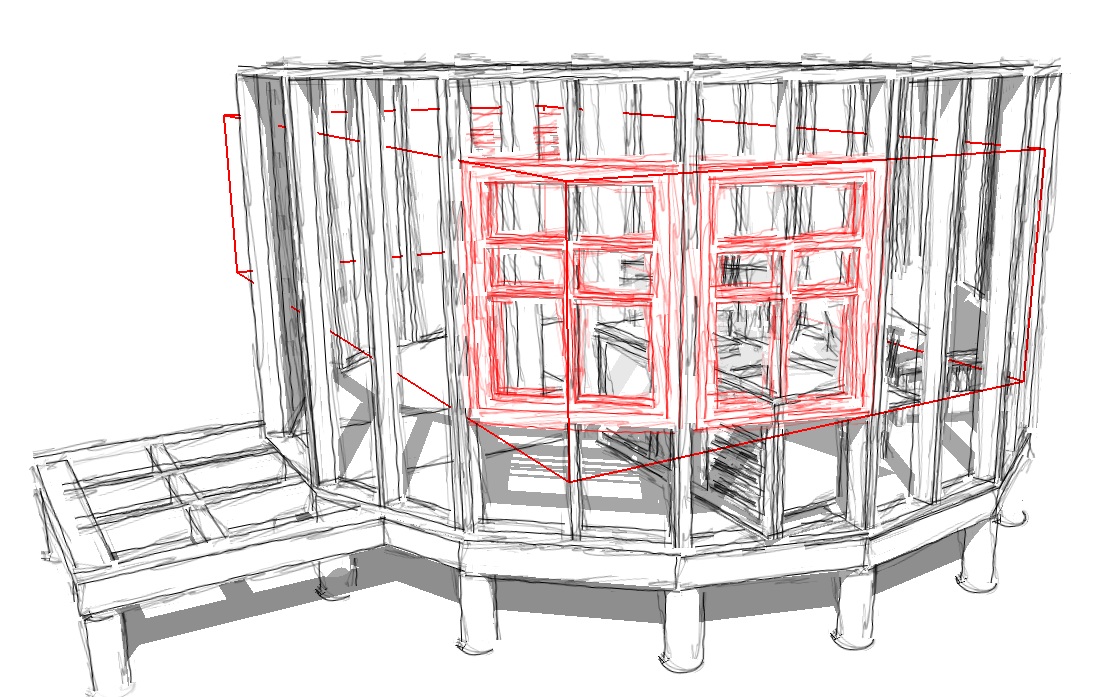
Скетчи/5.jpg
