peter-hanzo/KD/Скетчи/6.jpg

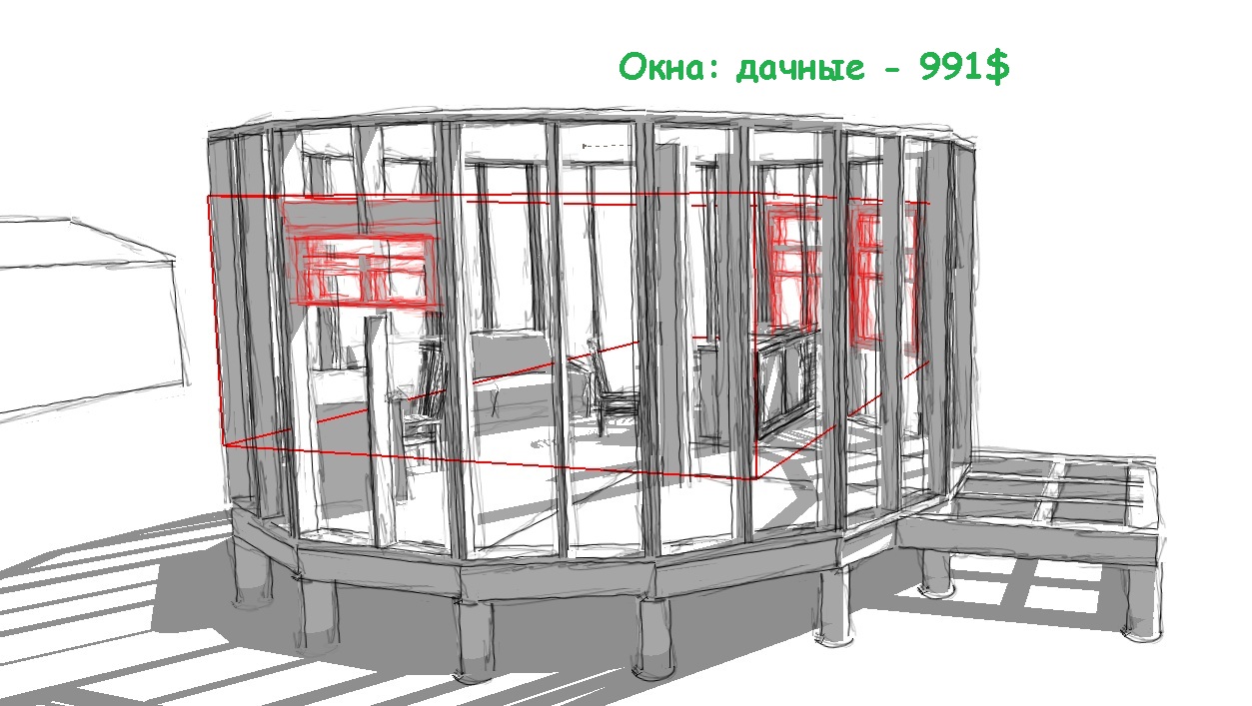
Скетчи/6.jpg
