peter-hanzo/KD/Скетчи/8.jpg

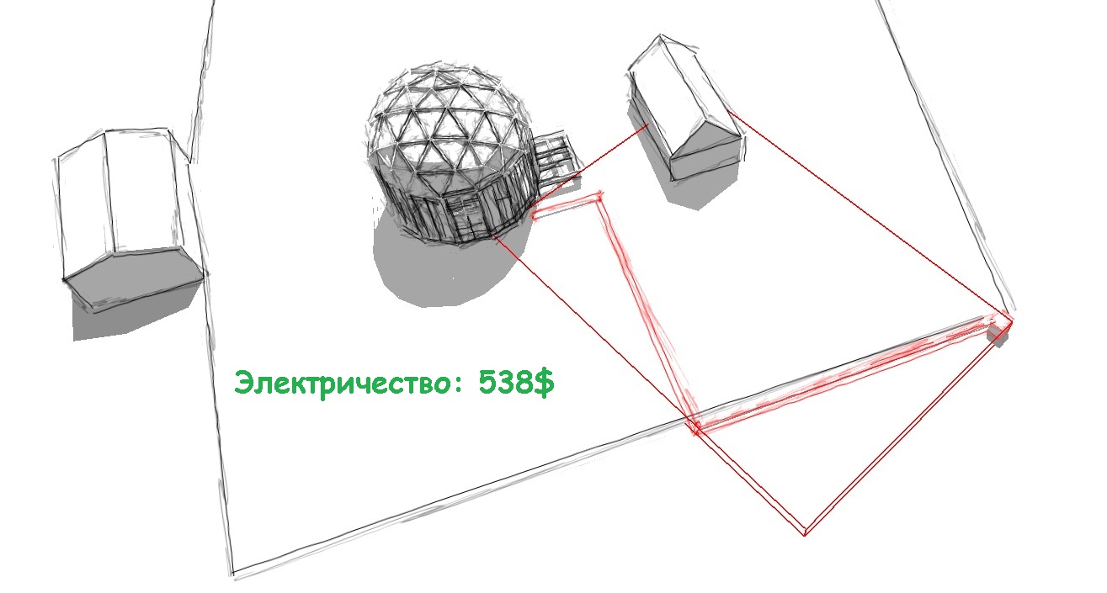
Скетчи/8.jpg
