peter-hanzo/KD/Скетчи/10.jpg

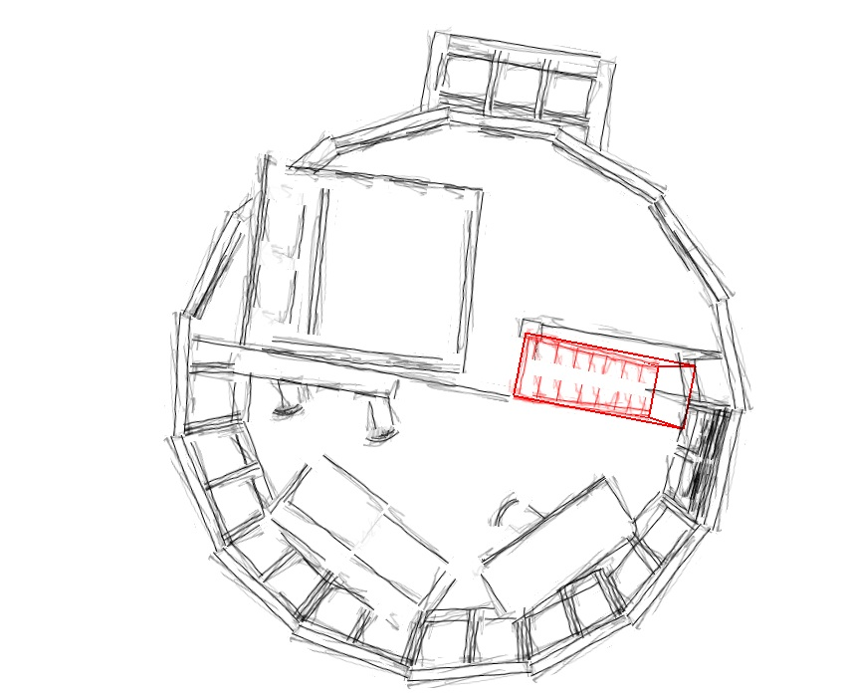
Скетчи/10.jpg
