peter-hanzo/KD/Скетчи/11.jpg

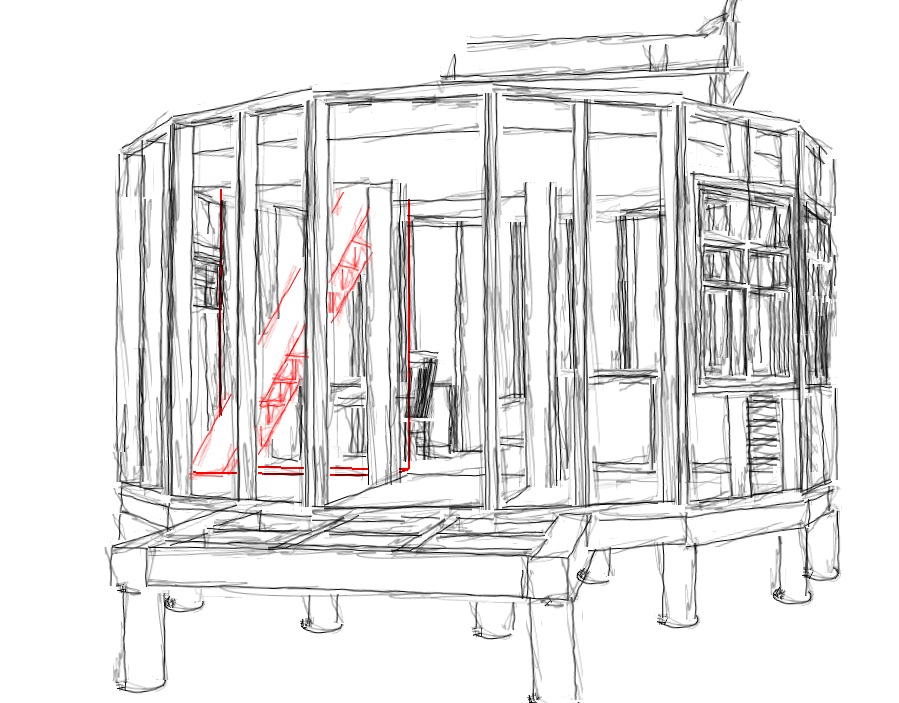
Скетчи/11.jpg
