peter-hanzo/KD/Скетчи/25.jpg

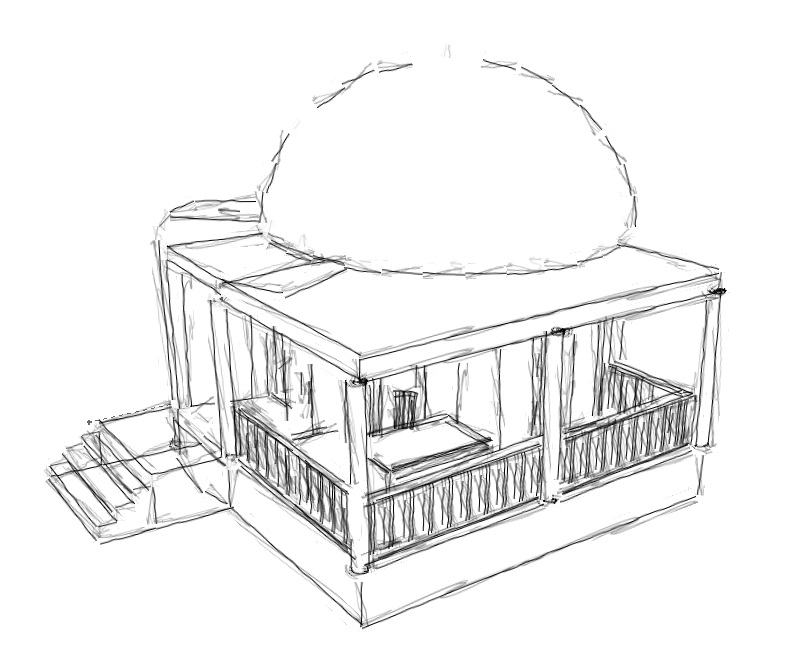
Скетчи/25.jpg
