peter-hanzo/KD/Скетчи/48.jpg

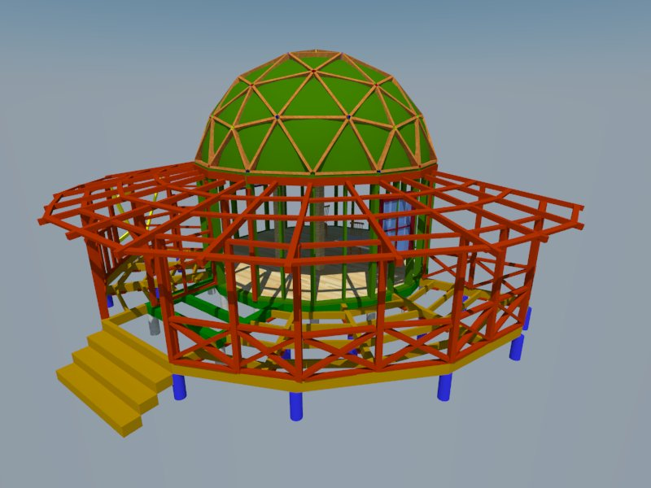
Скетчи/48.jpg
