peter-hanzo/KD/Скетчи/54.jpg

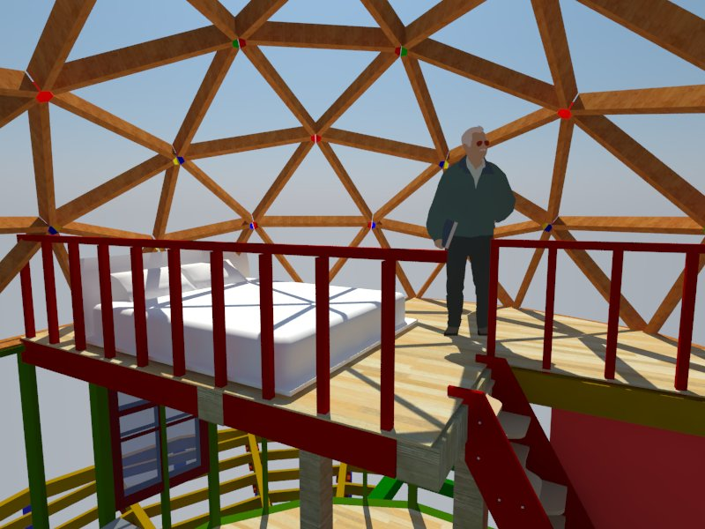
Скетчи/54.jpg
