peter-hanzo/KD/Скетчи/Fasad_rayzer_6m-1.png

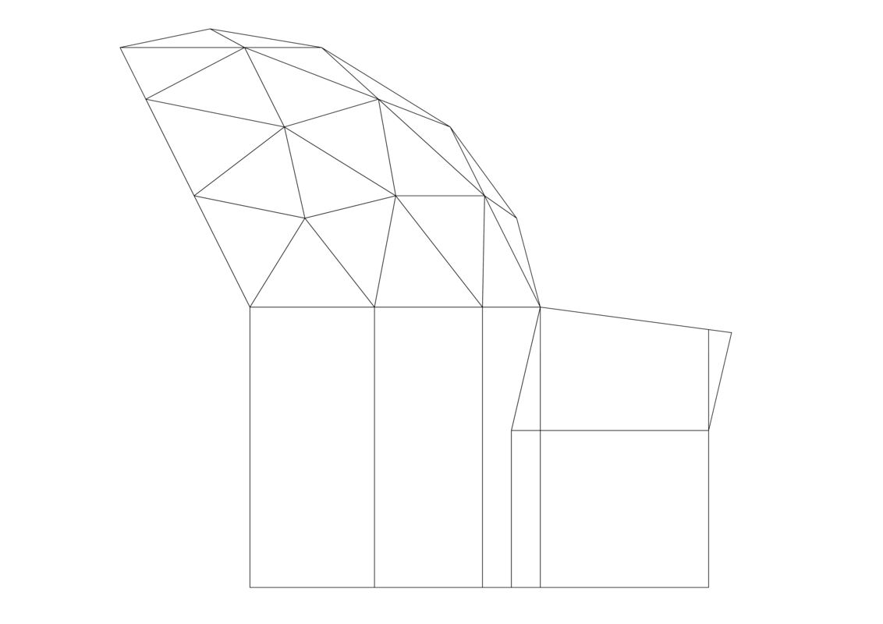
Скетчи/Fasad_rayzer_6m-1.png
