peter-hanzo/KD/Скетчи/вид дома.png

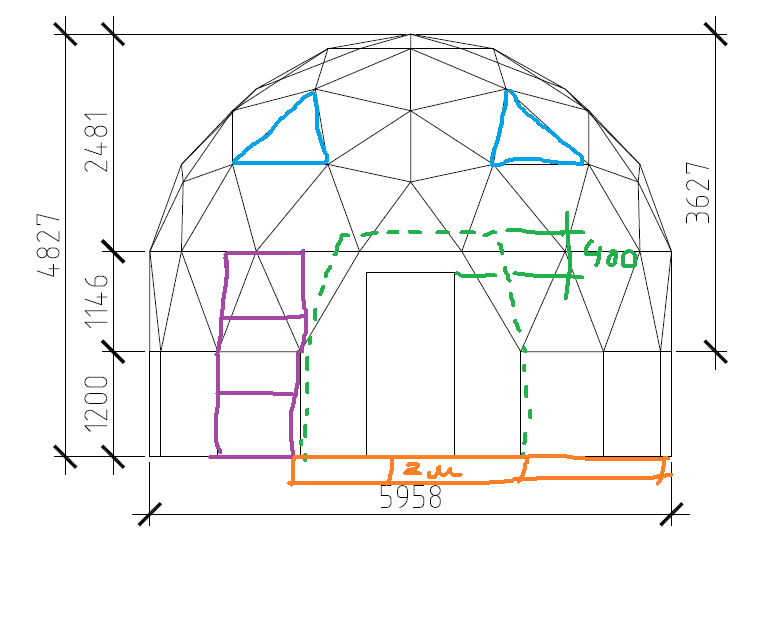
Скетчи/вид дома.png
