peter-hanzo/KD/Скетчи/Внешний вид круглого дома.jpg

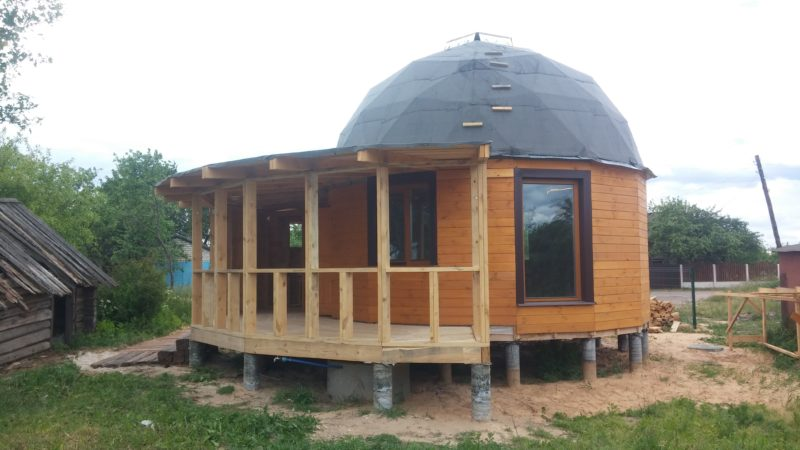
Скетчи/Внешний вид круглого дома.jpg
