peter-hanzo/KD/Скетчи/план дома.png

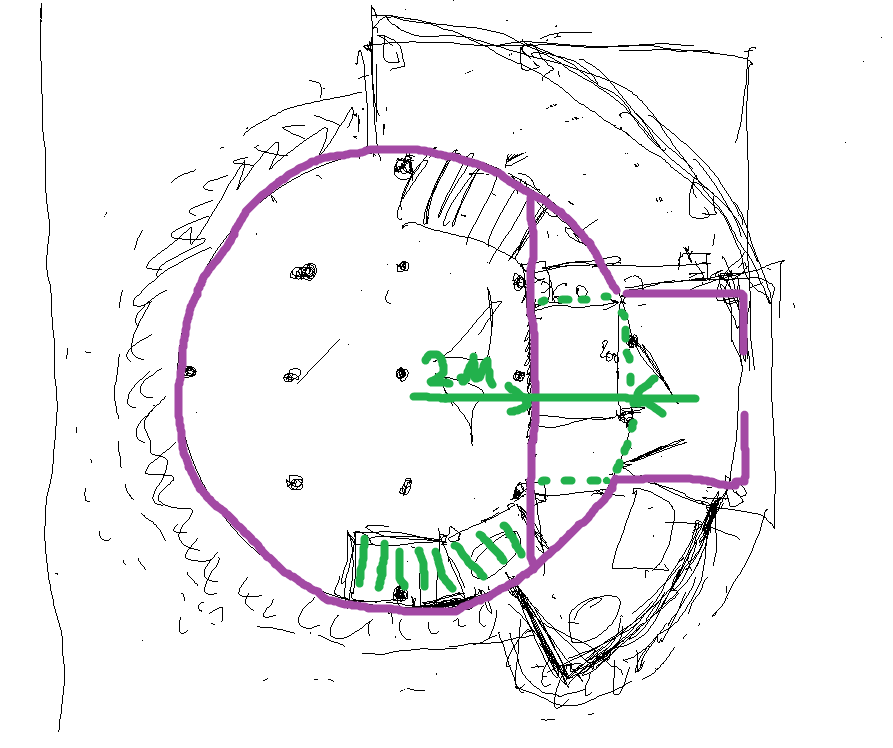
Скетчи/план дома.png
