peter-hanzo/KD/Скетчи/эскиз дома.jpg

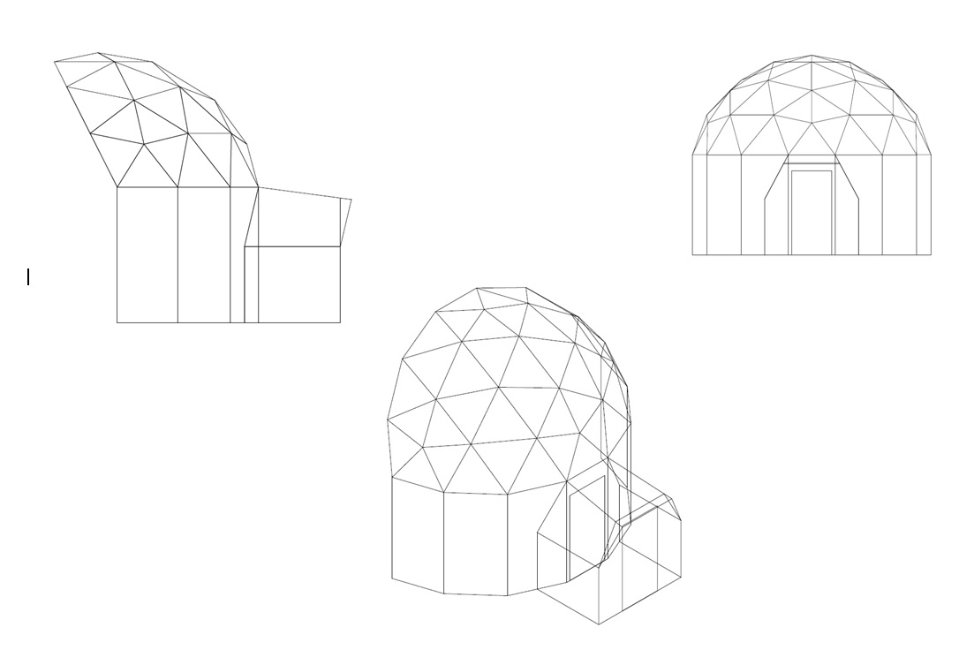
Скетчи/эскиз дома.jpg
