peter-hanzo/KD/Скетчи/ялча доп площадь3.jpg

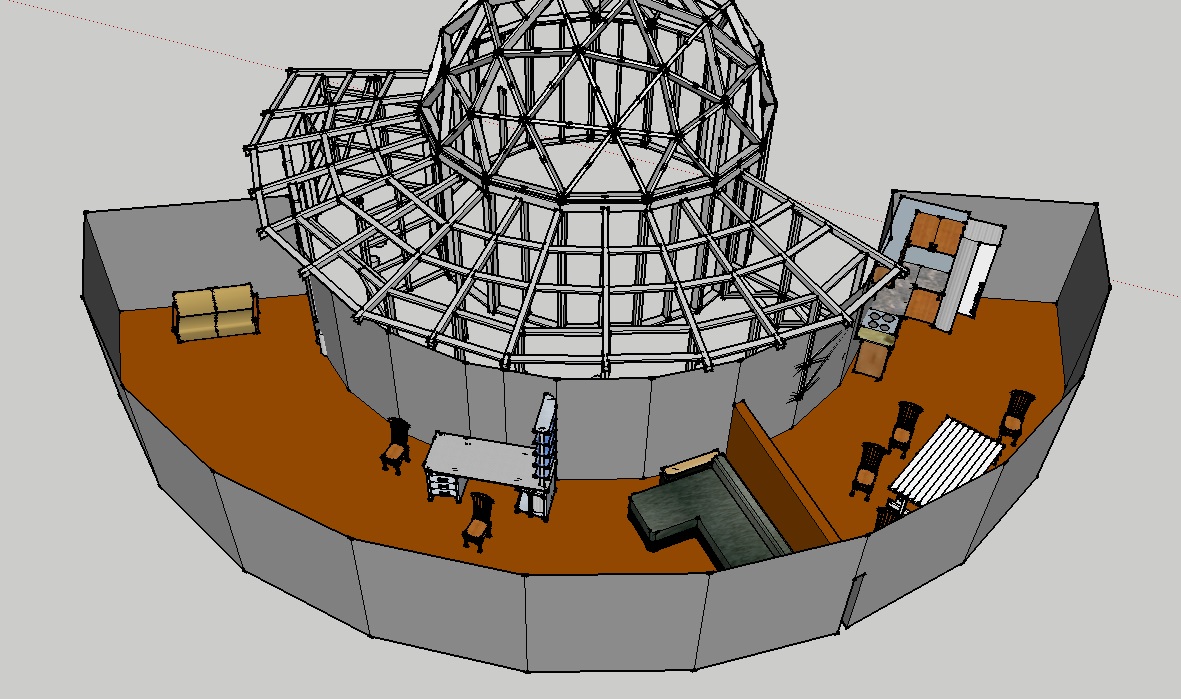
Скетчи/ялча доп площадь3.jpg
