peter-hanzo/KD/Что бывает/Фото/20150721_20202600.png

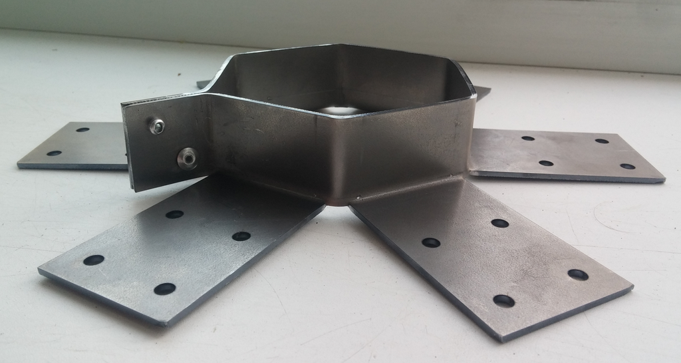
Что бывает/Фото/20150721_20202600.png
