peter-hanzo/KD/Что бывает/Фото/20150721_202117000.png

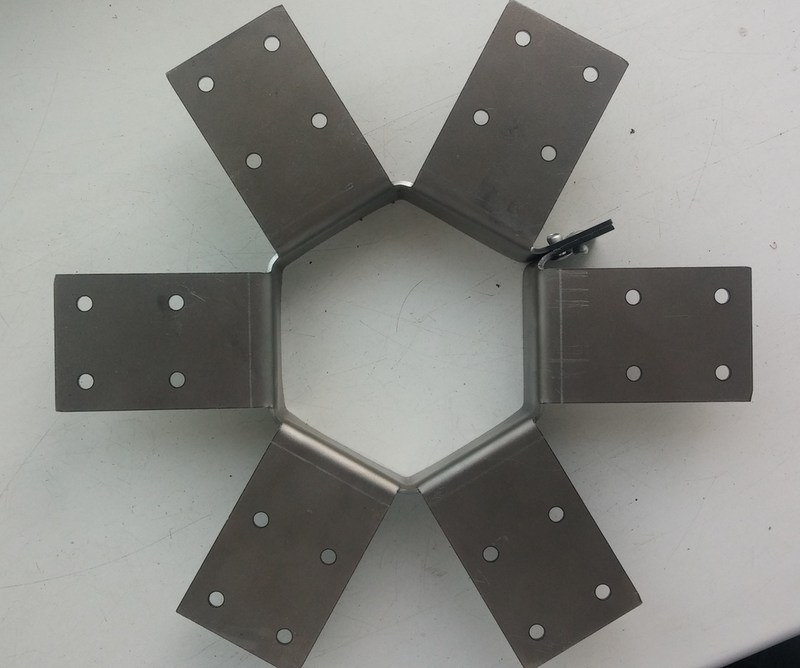
Что бывает/Фото/20150721_202117000.png
