peter-hanzo/KD/Что бывает/Фото/-z_s-UAlyaI.jpg

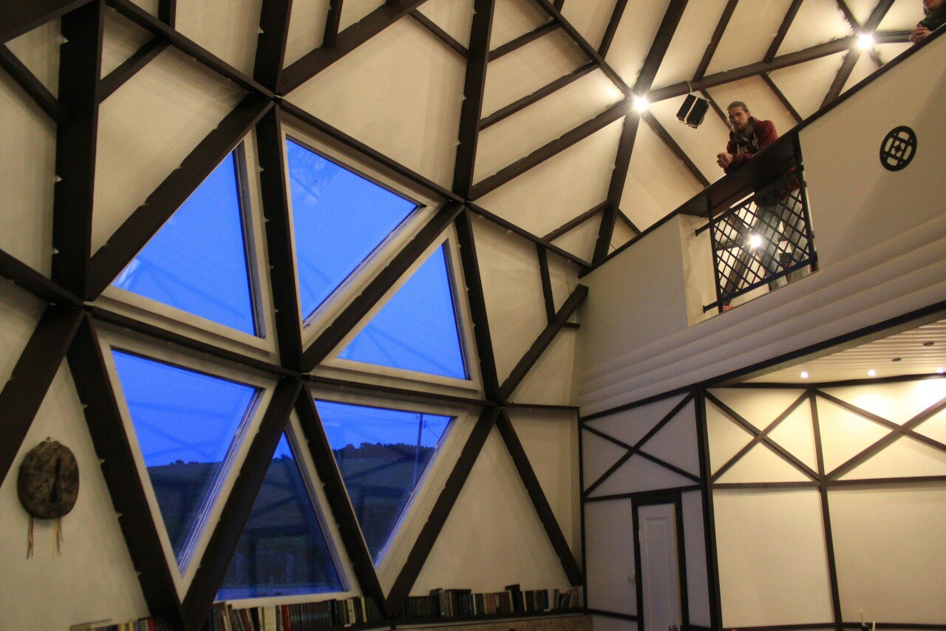
Что бывает/Фото/-z_s-UAlyaI.jpg
