peter-hanzo/KD/Что бывает/Фото/i9jv7Zx5LEU.jpg

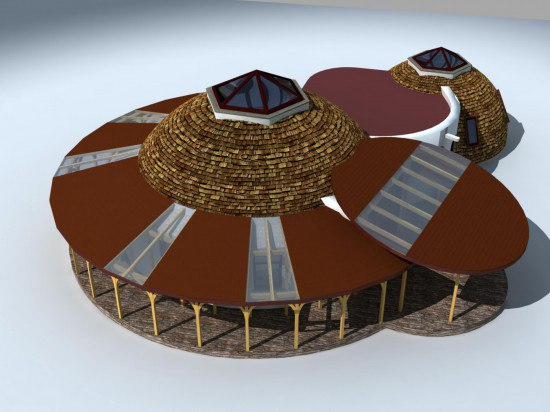
Что бывает/Фото/i9jv7Zx5LEU.jpg
