peter-hanzo/KD/Что бывает/Фото/Konnektor-v-sbore.jpg

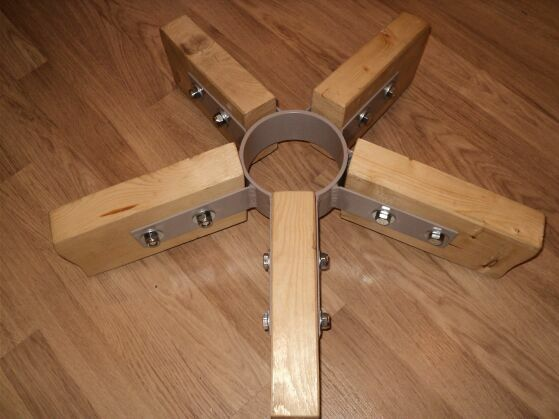
Что бывает/Фото/Konnektor-v-sbore.jpg
