peter-hanzo/KD/Что бывает/Фото/ParmhL-X0w4.jpg

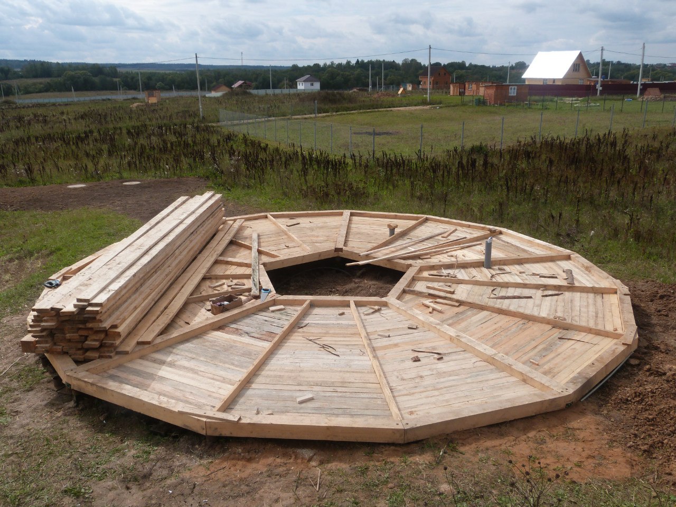
Что бывает/Фото/ParmhL-X0w4.jpg
