peter-hanzo/KD/Что бывает/Фото/ScreenClip2.jpg

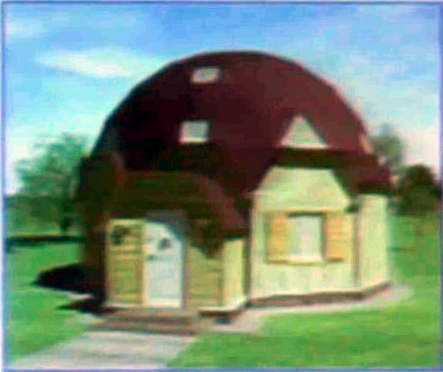
Что бывает/Фото/ScreenClip2.jpg
