peter-hanzo/KD/Что бывает/Фото/ScreenClip.jpg

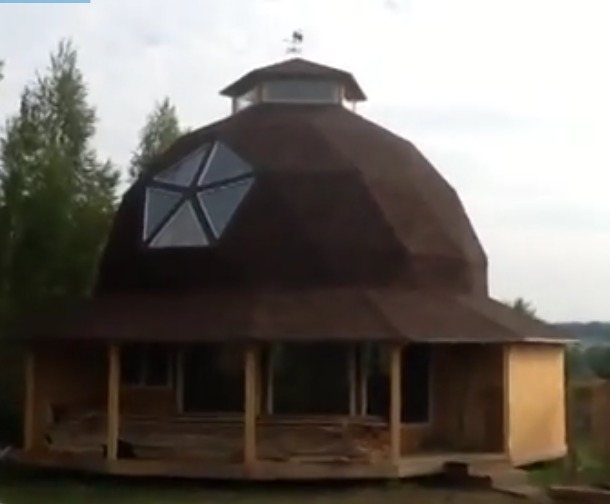
Что бывает/Фото/ScreenClip.jpg
