peter-hanzo/KD/Что бывает/Фото/vIGqZ7vpNKo.jpg

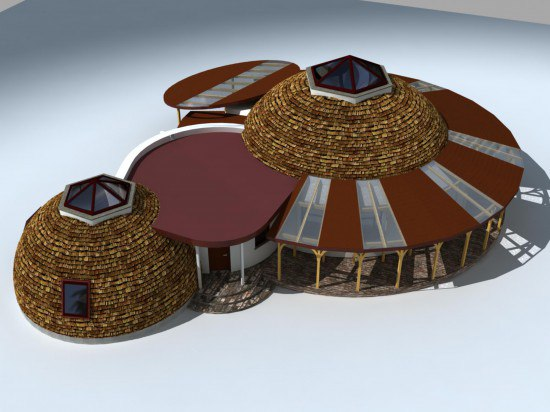
Что бывает/Фото/vIGqZ7vpNKo.jpg
