peter-hanzo/KD/Что бывает/Чертежи/2VcT8kL9bVw.jpg

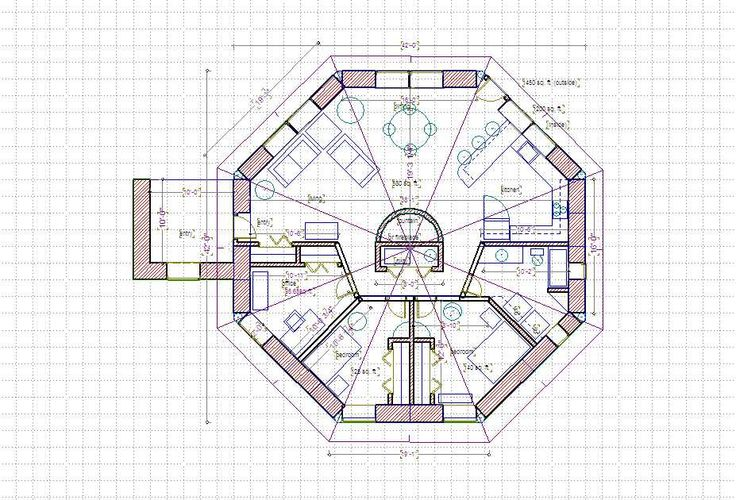
Что бывает/Чертежи/2VcT8kL9bVw.jpg
