peter-hanzo/KD/Что бывает/Чертежи/222.jpg

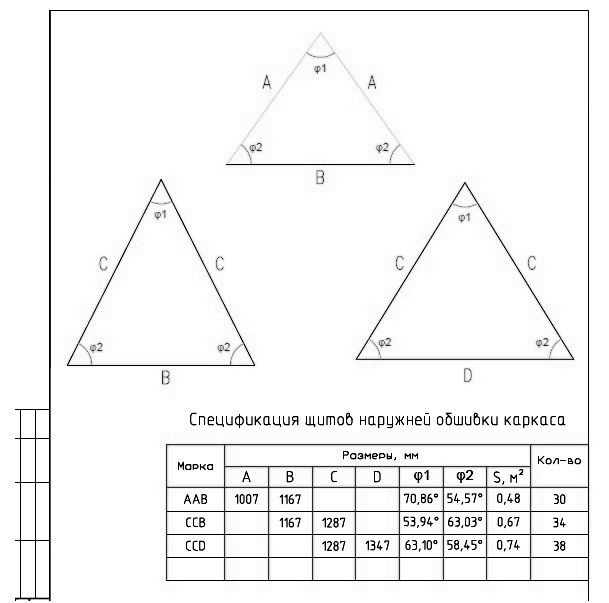
Что бывает/Чертежи/222.jpg
