peter-hanzo/KD/Что бывает/Чертежи/3344.jpg

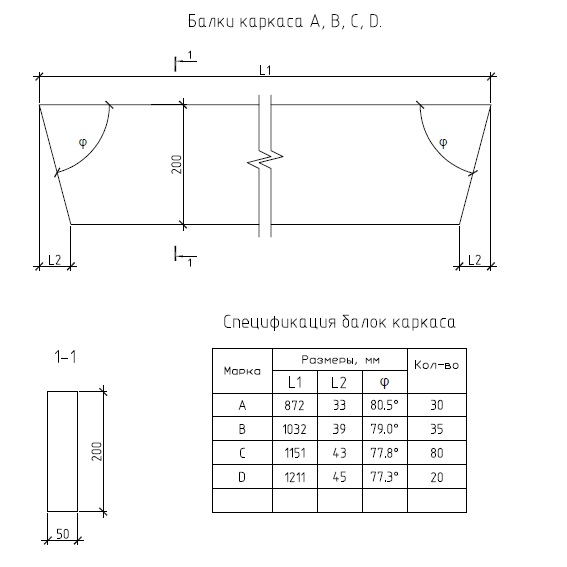
Что бывает/Чертежи/3344.jpg
