peter-hanzo/KD/Что бывает/Чертежи/_Gk3tbmH9X0.jpg

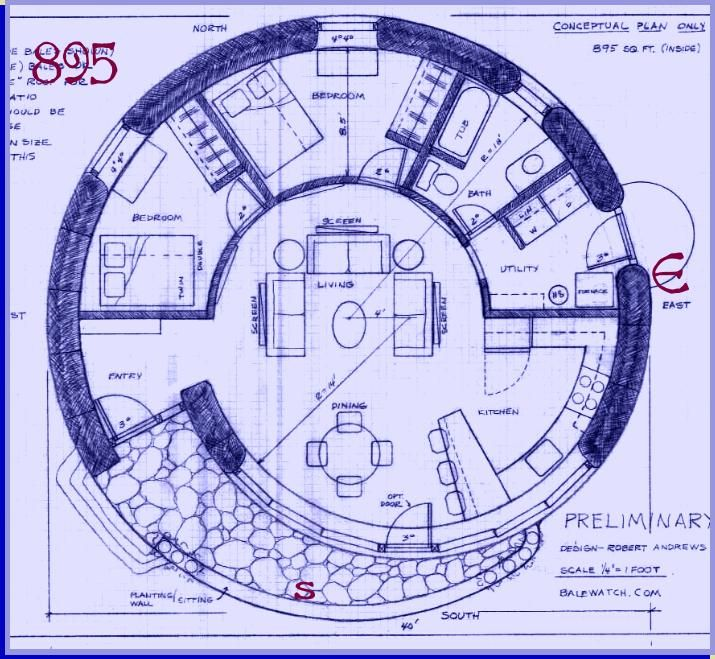
Что бывает/Чертежи/_Gk3tbmH9X0.jpg
