peter-hanzo/KD/Что бывает/Чертежи/Skhema_obshivki_karkasa.png

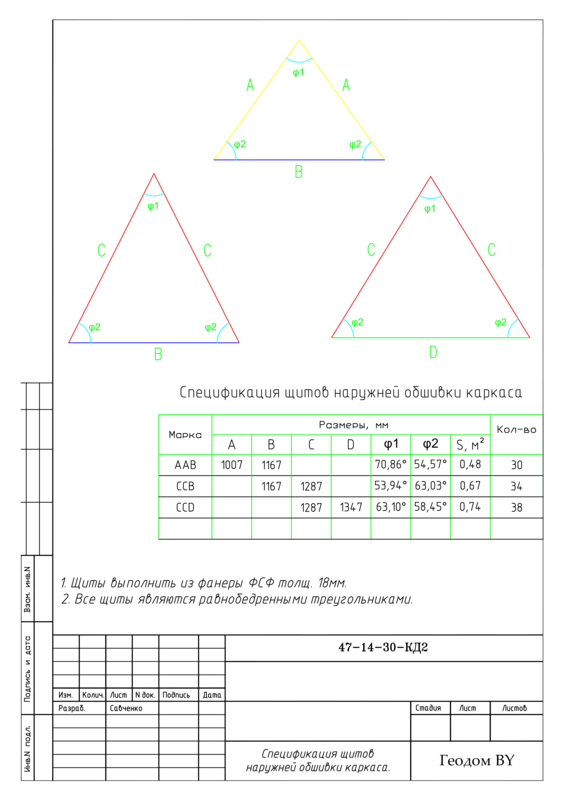
Что бывает/Чертежи/Skhema_obshivki_karkasa.png
