peter-hanzo/KD/Что бывает/Чертежи/Spetsifikatsia_balok.png

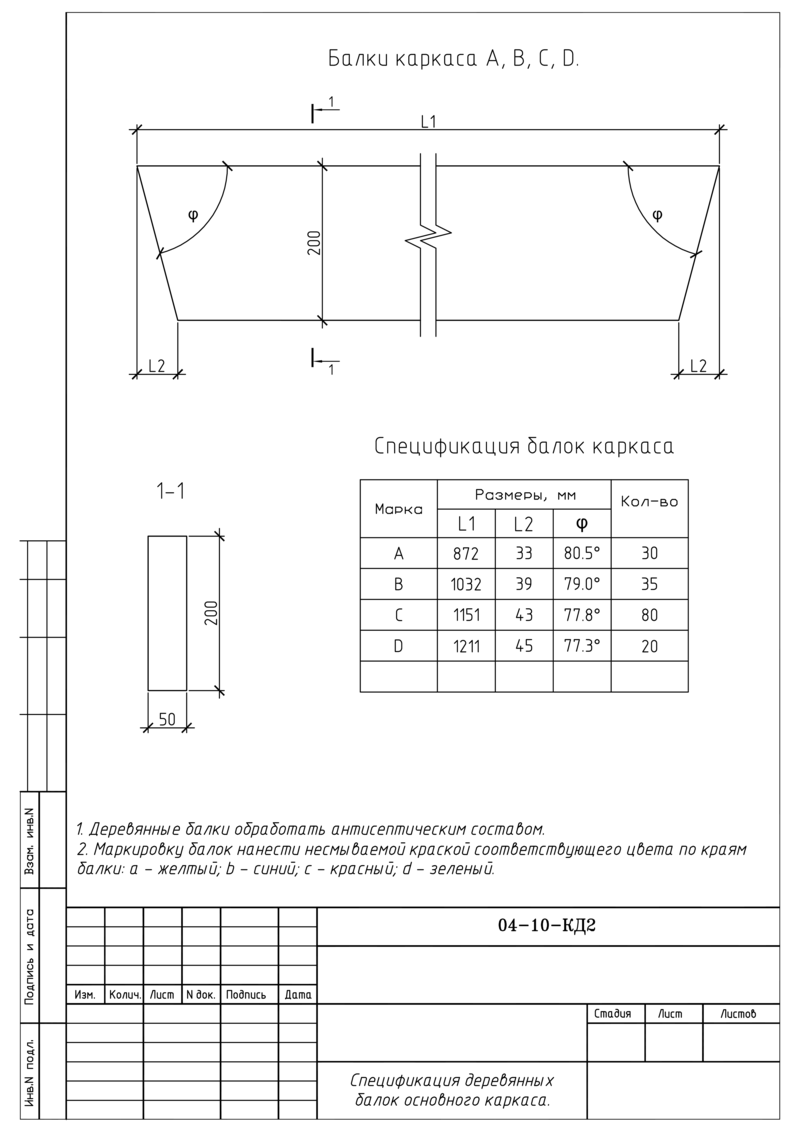
Что бывает/Чертежи/Spetsifikatsia_balok.png
