peter-hanzo/KD/Что бывает/Чертежи/Xrhtx0kAVd0.jpg

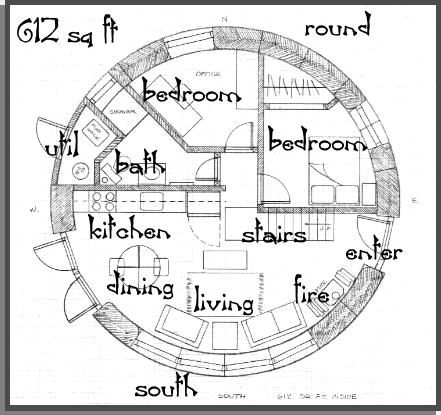
Что бывает/Чертежи/Xrhtx0kAVd0.jpg
