peter-hanzo/KD/Что бывает/Чертежи/Крепления.png

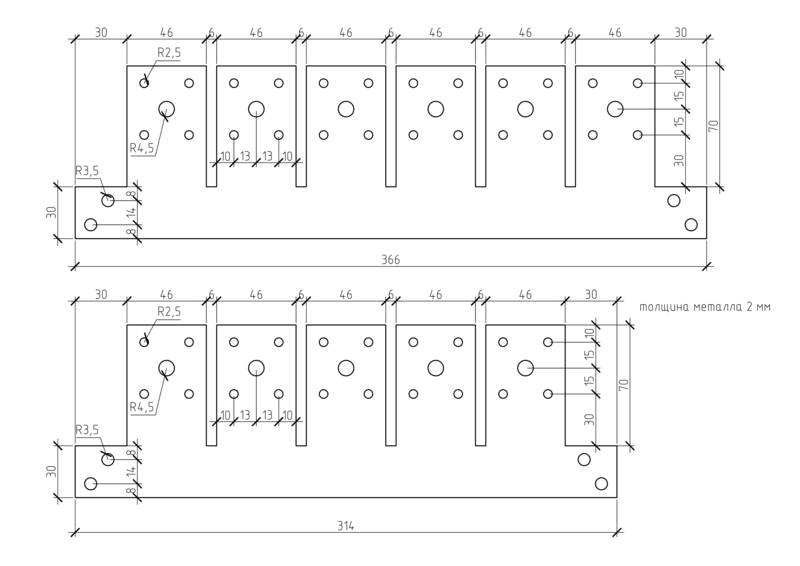
Что бывает/Чертежи/Крепления.png
