peter-hanzo/KD/Что бывает/Чертежи/треугольники раскрой.png

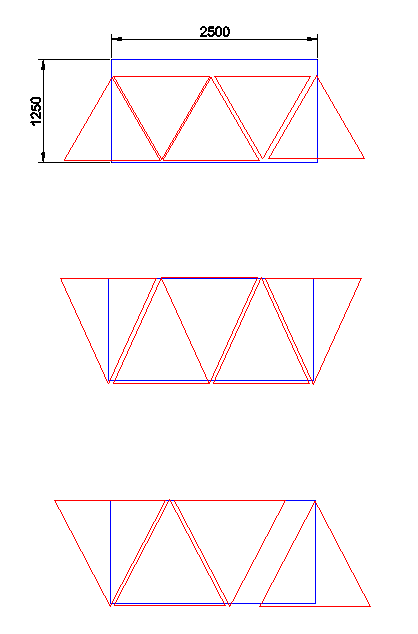
Что бывает/Чертежи/треугольники раскрой.png
