peter-hanzo/KD/Документы/Чертежи/Конструктив/крепление.dxf

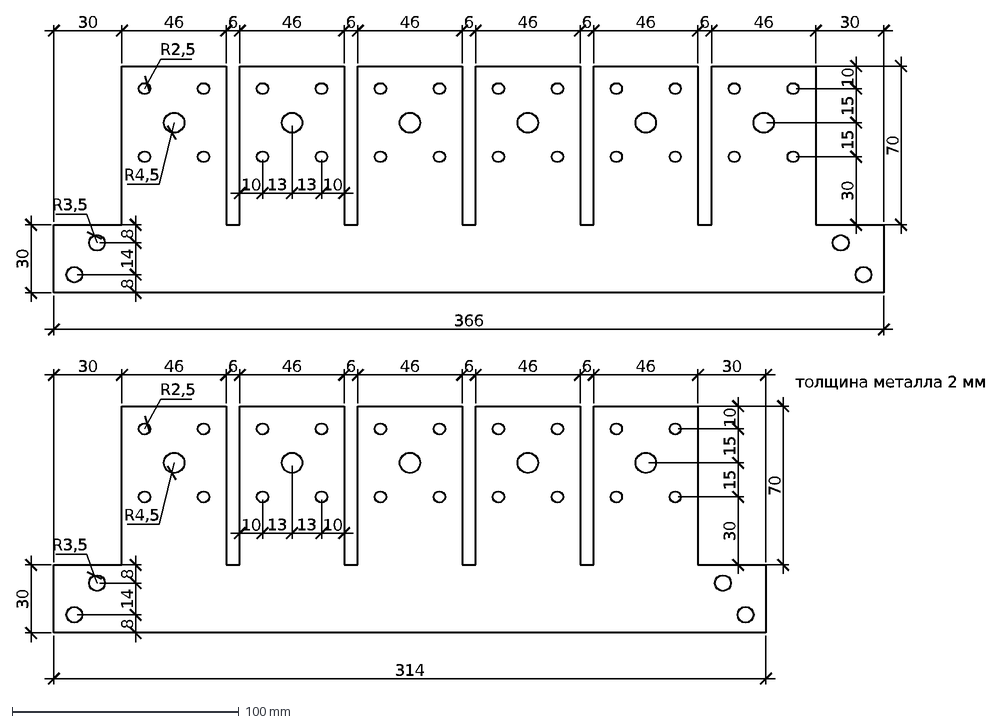
[picture p288: CAD file, 2015-06-07]
Документы/Чертежи/Конструктив/крепление.dxf
366
30
70
46
6
8
14
R3,5
R2,5
R4,5
10
13
15
314
толщина металла 2 мм
