peter-hanzo/KD/Документы/Чертежи/Архитектура (эскизный)/printable/лист 1 ведомость чертежей и ТЭП.png

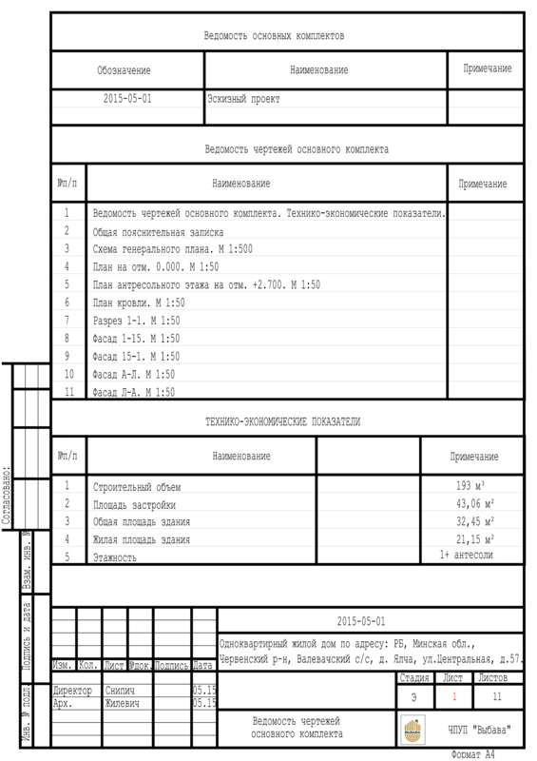
Документы/Чертежи/Архитектура (эскизный)/printable/лист 1 ведомость чертежей и ТЭП.png
