peter-hanzo/KD/Документы/Чертежи/Архитектура (эскизный)/printable/лист 2 ОПЗ.png

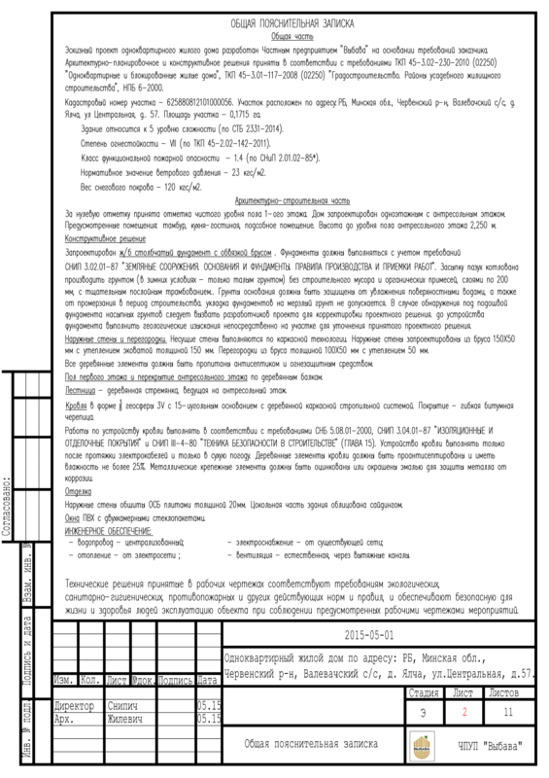
Документы/Чертежи/Архитектура (эскизный)/printable/лист 2 ОПЗ.png
