peter-hanzo/KD/Документы/Чертежи/Архитектура (эскизный)/printable/лист 3 схема генплана.png

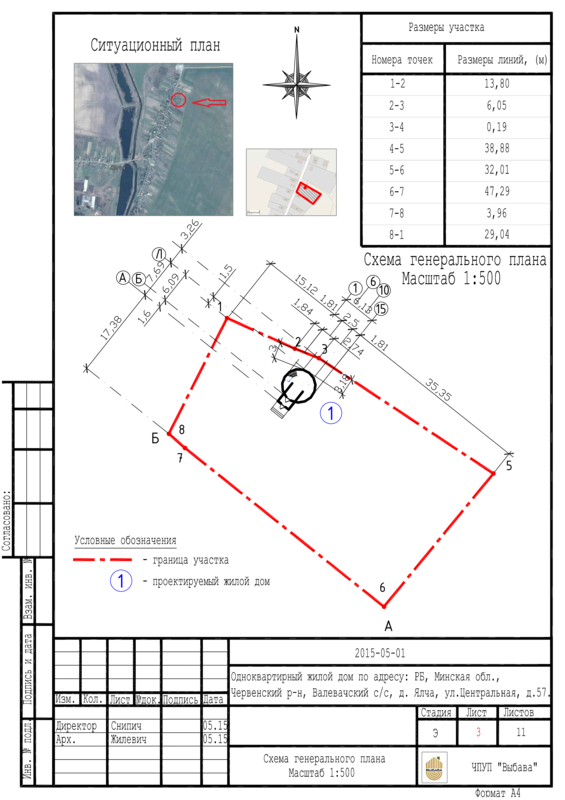
Документы/Чертежи/Архитектура (эскизный)/printable/лист 3 схема генплана.png
