peter-hanzo/KD/Документы/Чертежи/Архитектура (эскизный)/printable/лист 4 план А4.png

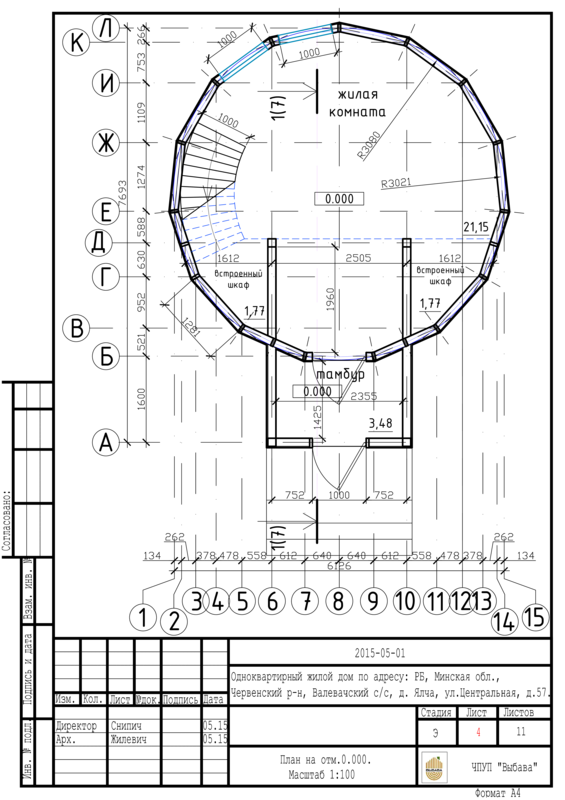
Документы/Чертежи/Архитектура (эскизный)/printable/лист 4 план А4.png
