peter-hanzo/KD/Документы/Чертежи/Архитектура (эскизный)/printable/лист 9 фасад.png

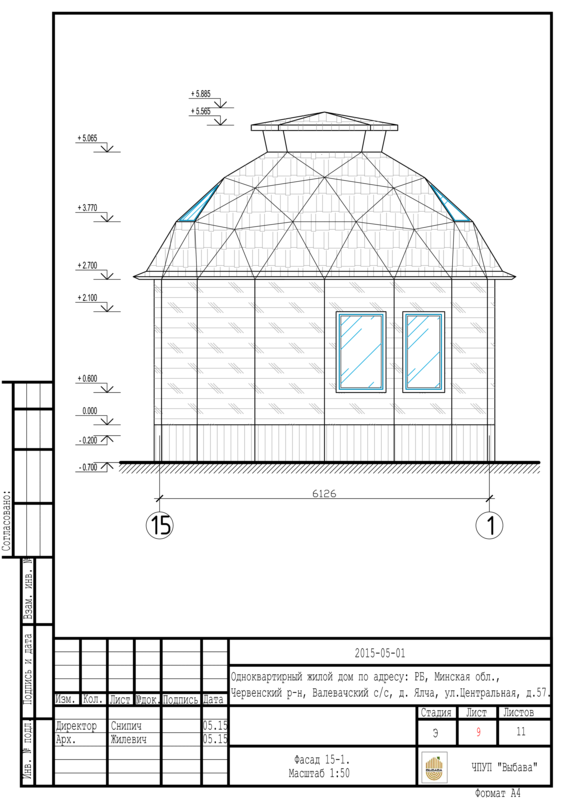
Документы/Чертежи/Архитектура (эскизный)/printable/лист 9 фасад.png
