peter-hanzo/KD/Документы/Чертежи/Архитектура (эскизный)/printable/лист 10 фасад А3.png

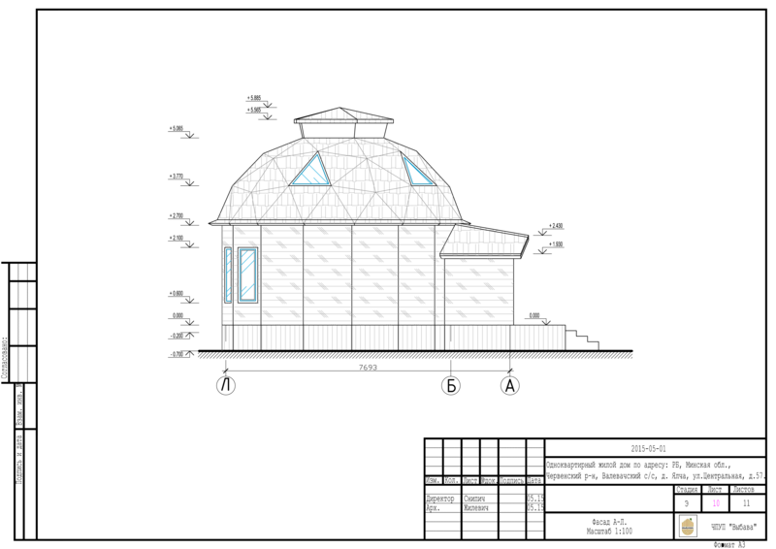
Документы/Чертежи/Архитектура (эскизный)/printable/лист 10 фасад А3.png
