peter-hanzo/KD/Что бывает/Чертежи/Skhema_obshivki_karkasa.pdf

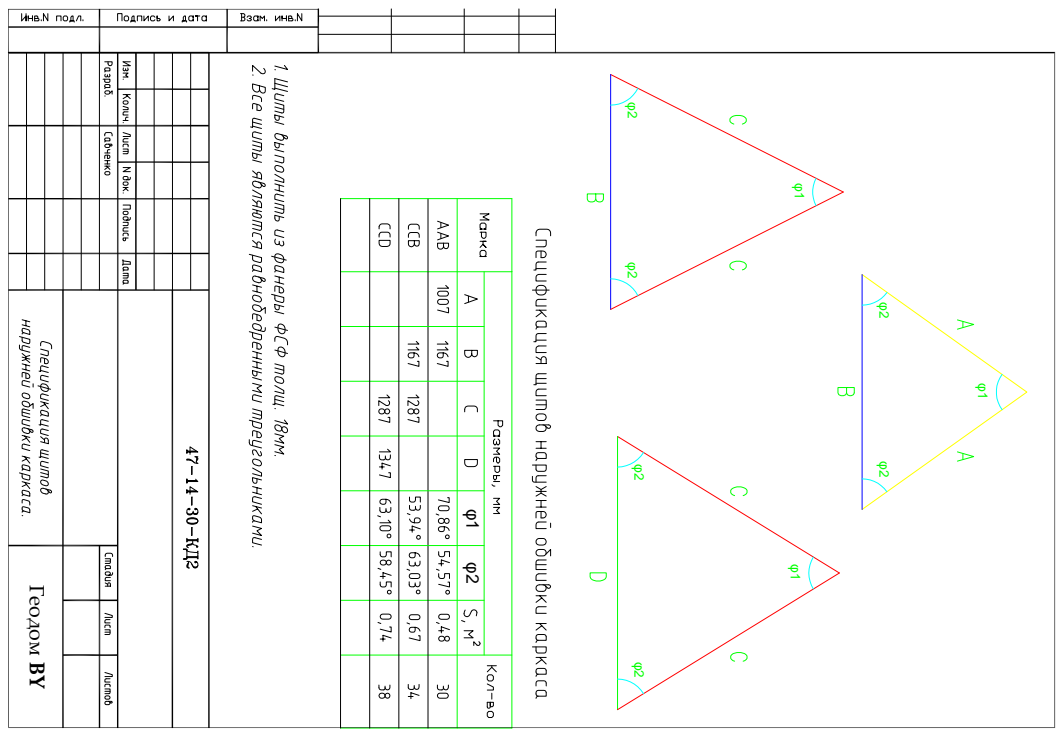
[picture p310: page 1]
Геодом BY
