peter-hanzo/KD/Что бывает/Чертежи/Spetsifikatsia_balok.pdf

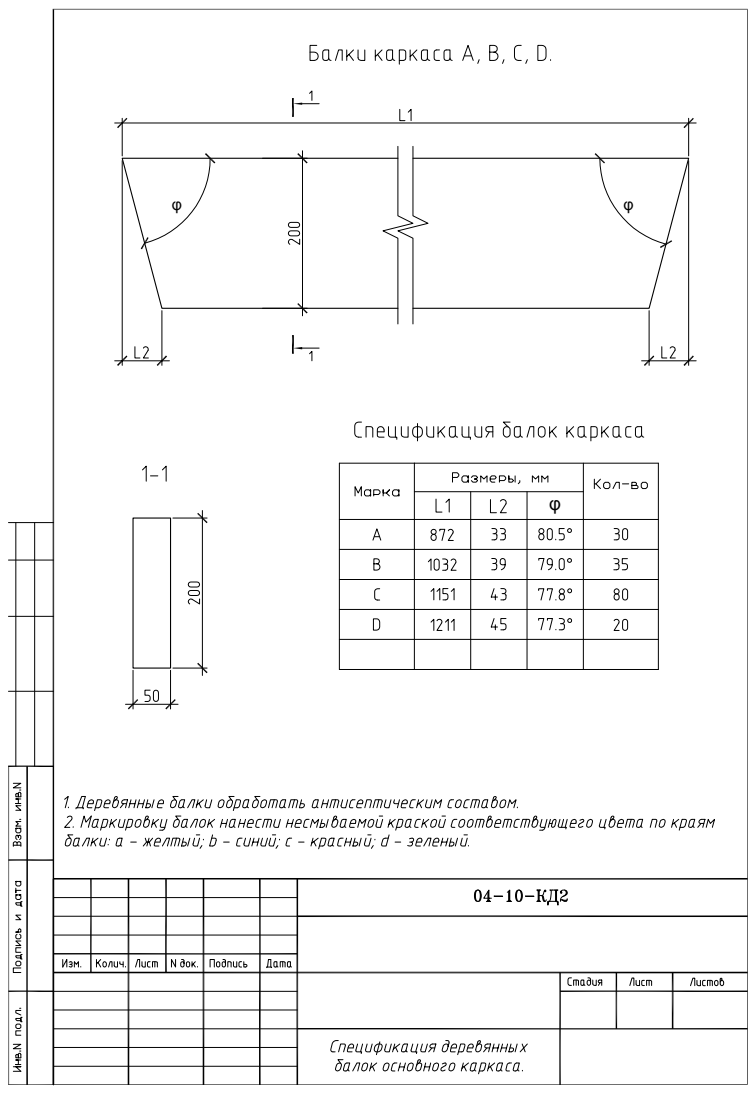
[picture p311: page 1]
