peter-hanzo/KD/Документы/Чертежи/Веранда/01.pdf

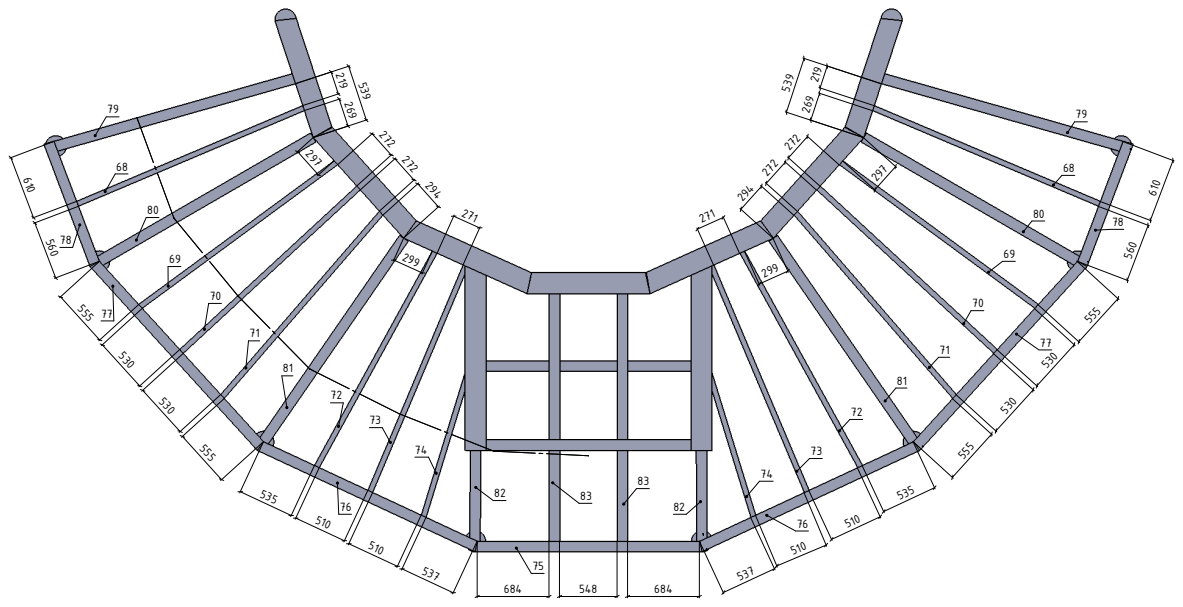
[picture p312: page 1]
