peter-hanzo/KD/Документы/Чертежи/Веранда/02.pdf

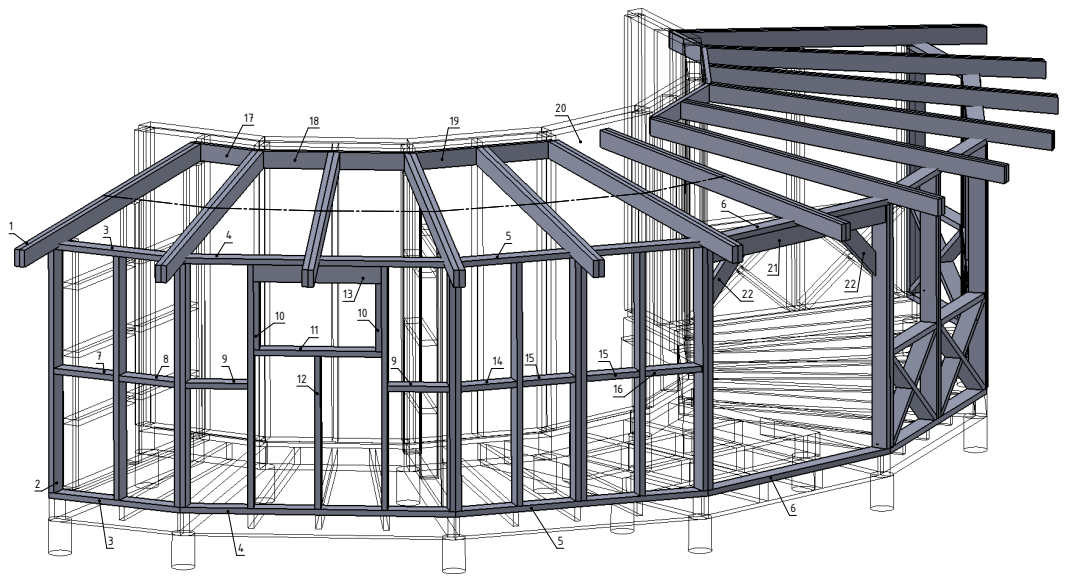
[picture p313: page 1]
