peter-hanzo/KD/Документы/Чертежи/Веранда/03.pdf

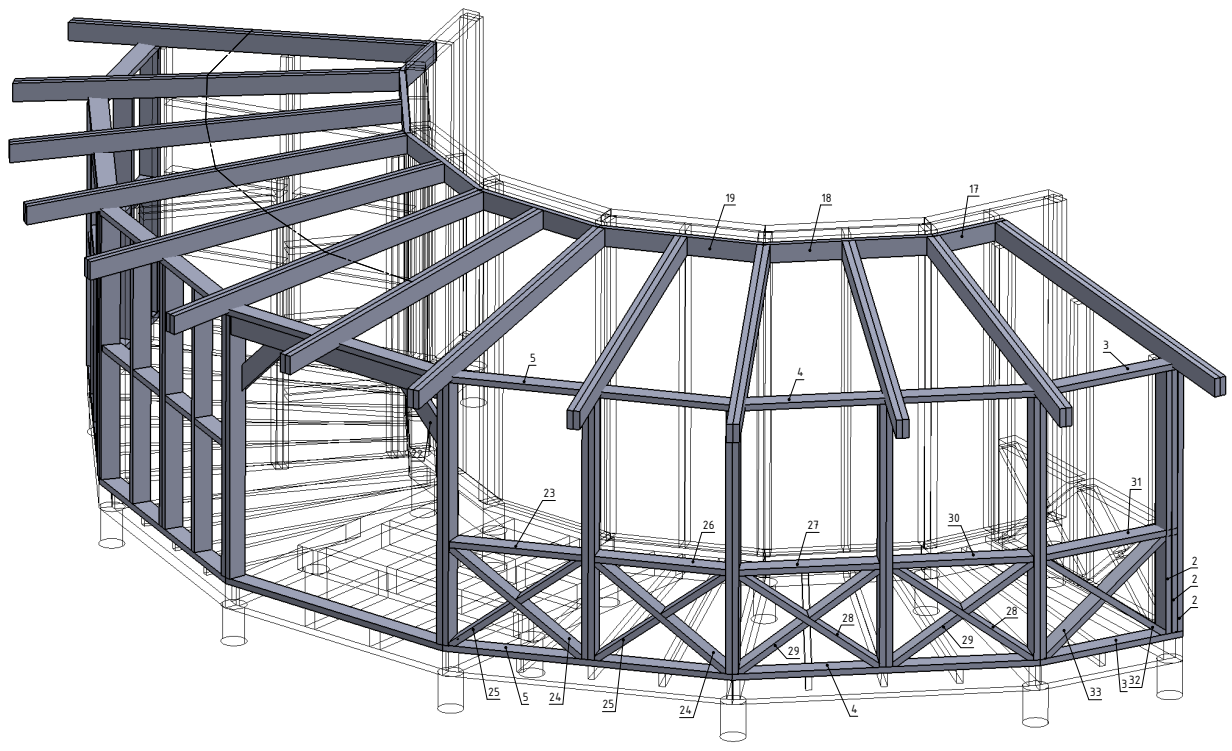
[picture p314: page 1]
