peter-hanzo/KD/Документы/Чертежи/Веранда/04.pdf

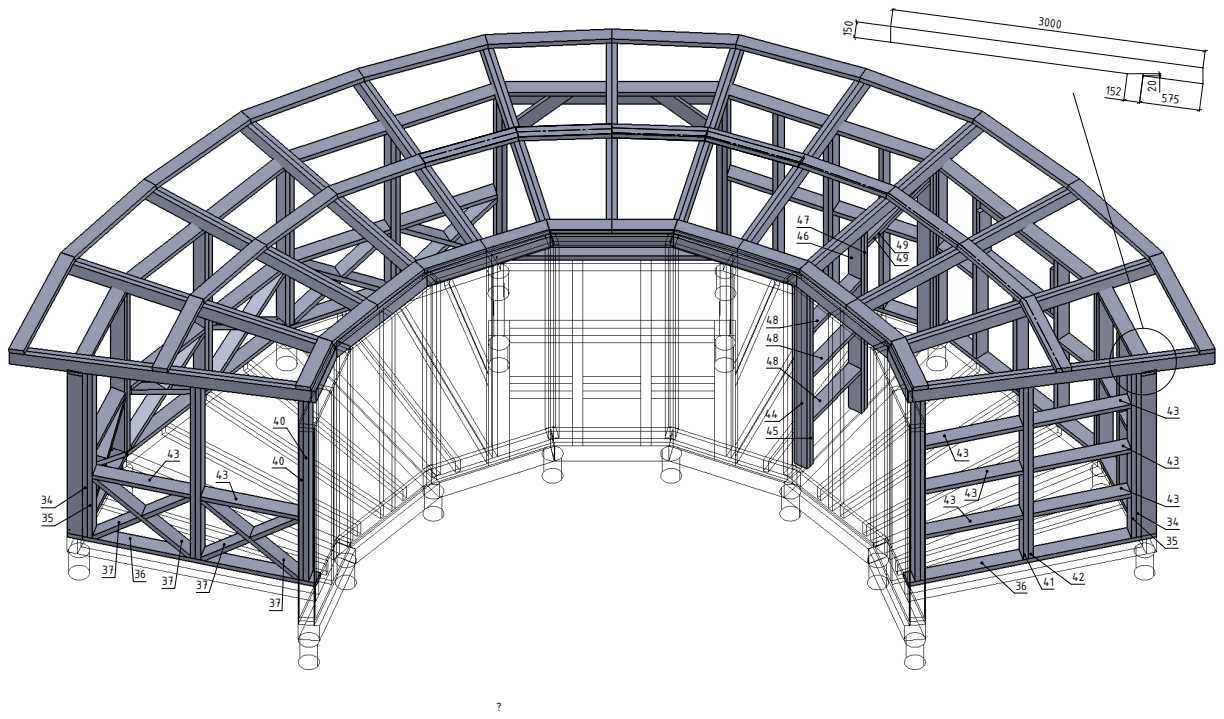
[picture p315: page 1]
