peter-hanzo/KD/Документы/Чертежи/Веранда/05.pdf

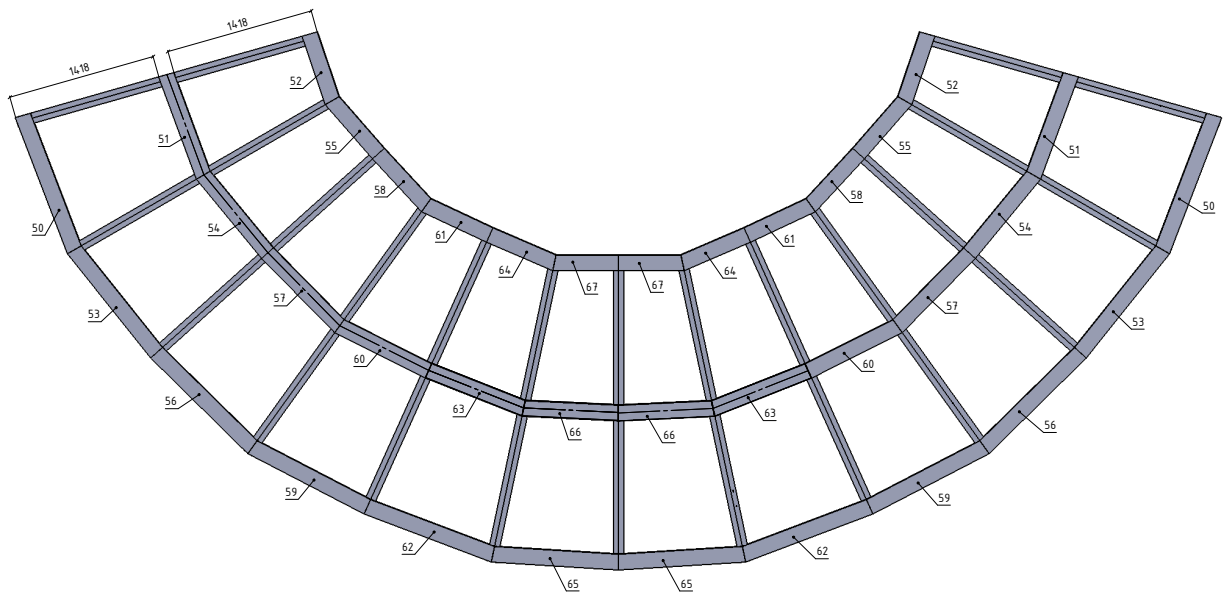
[picture p316: page 1]
