peter-hanzo/KD/Документы/Чертежи/Веранда/details_01.pdf

22

20

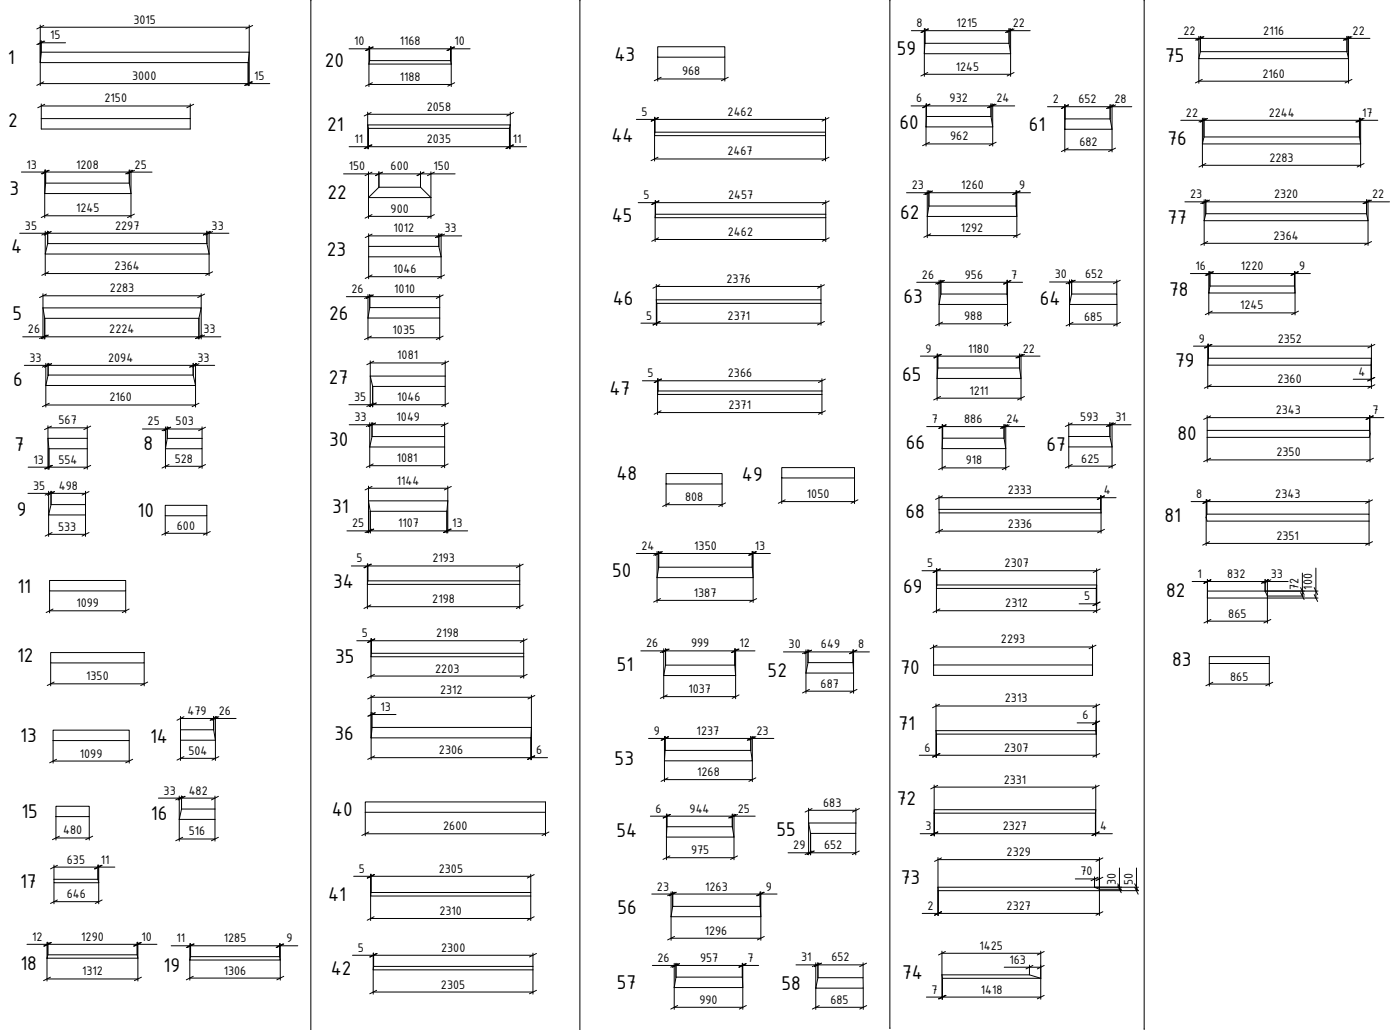
[picture p317: page 1]
