peter-hanzo/KD/Документы/Чертежи/Веранда/details_02.pdf

24
28

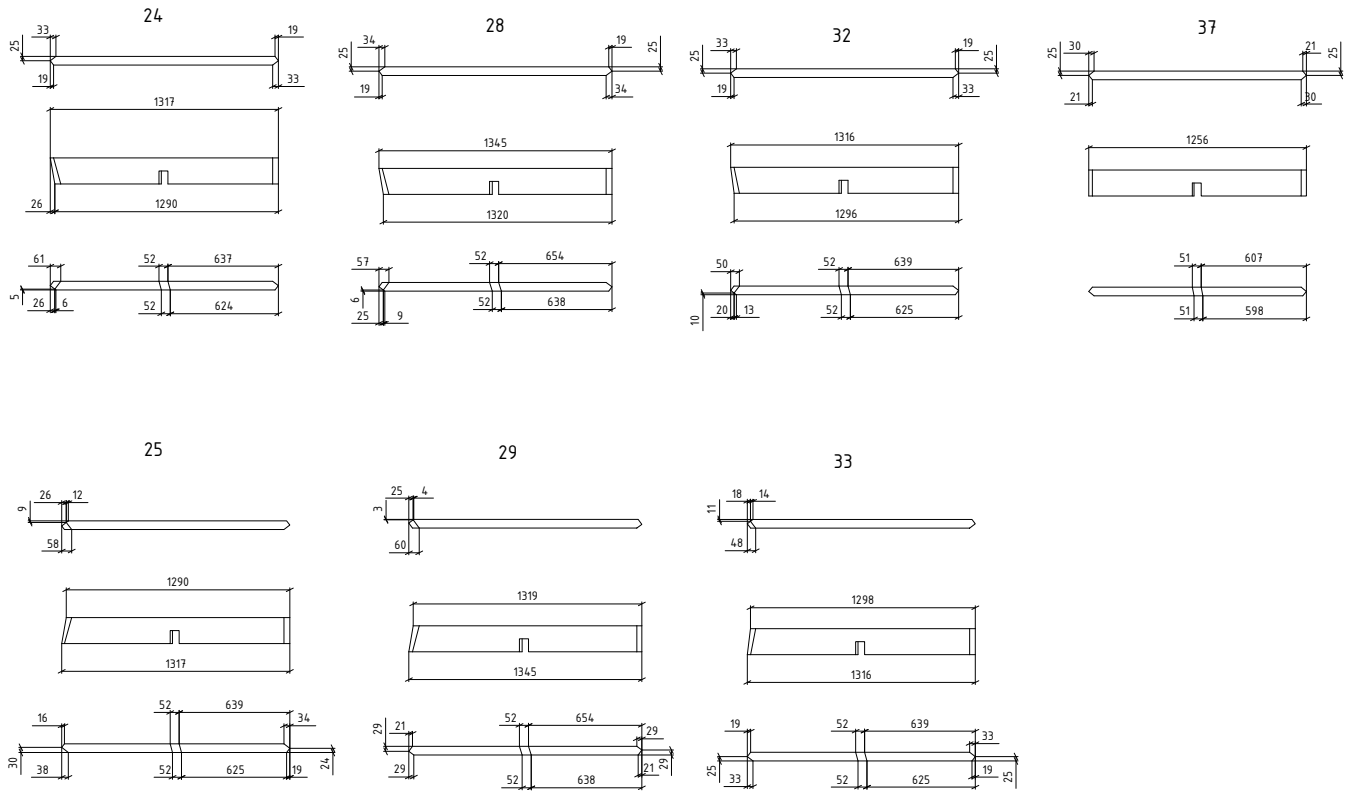
[picture p318: page 1]
