peter-hanzo/KD/Документы/Чертежи/Фундамент/разметка фундамета веранды-2.pdf

2 | 1

B

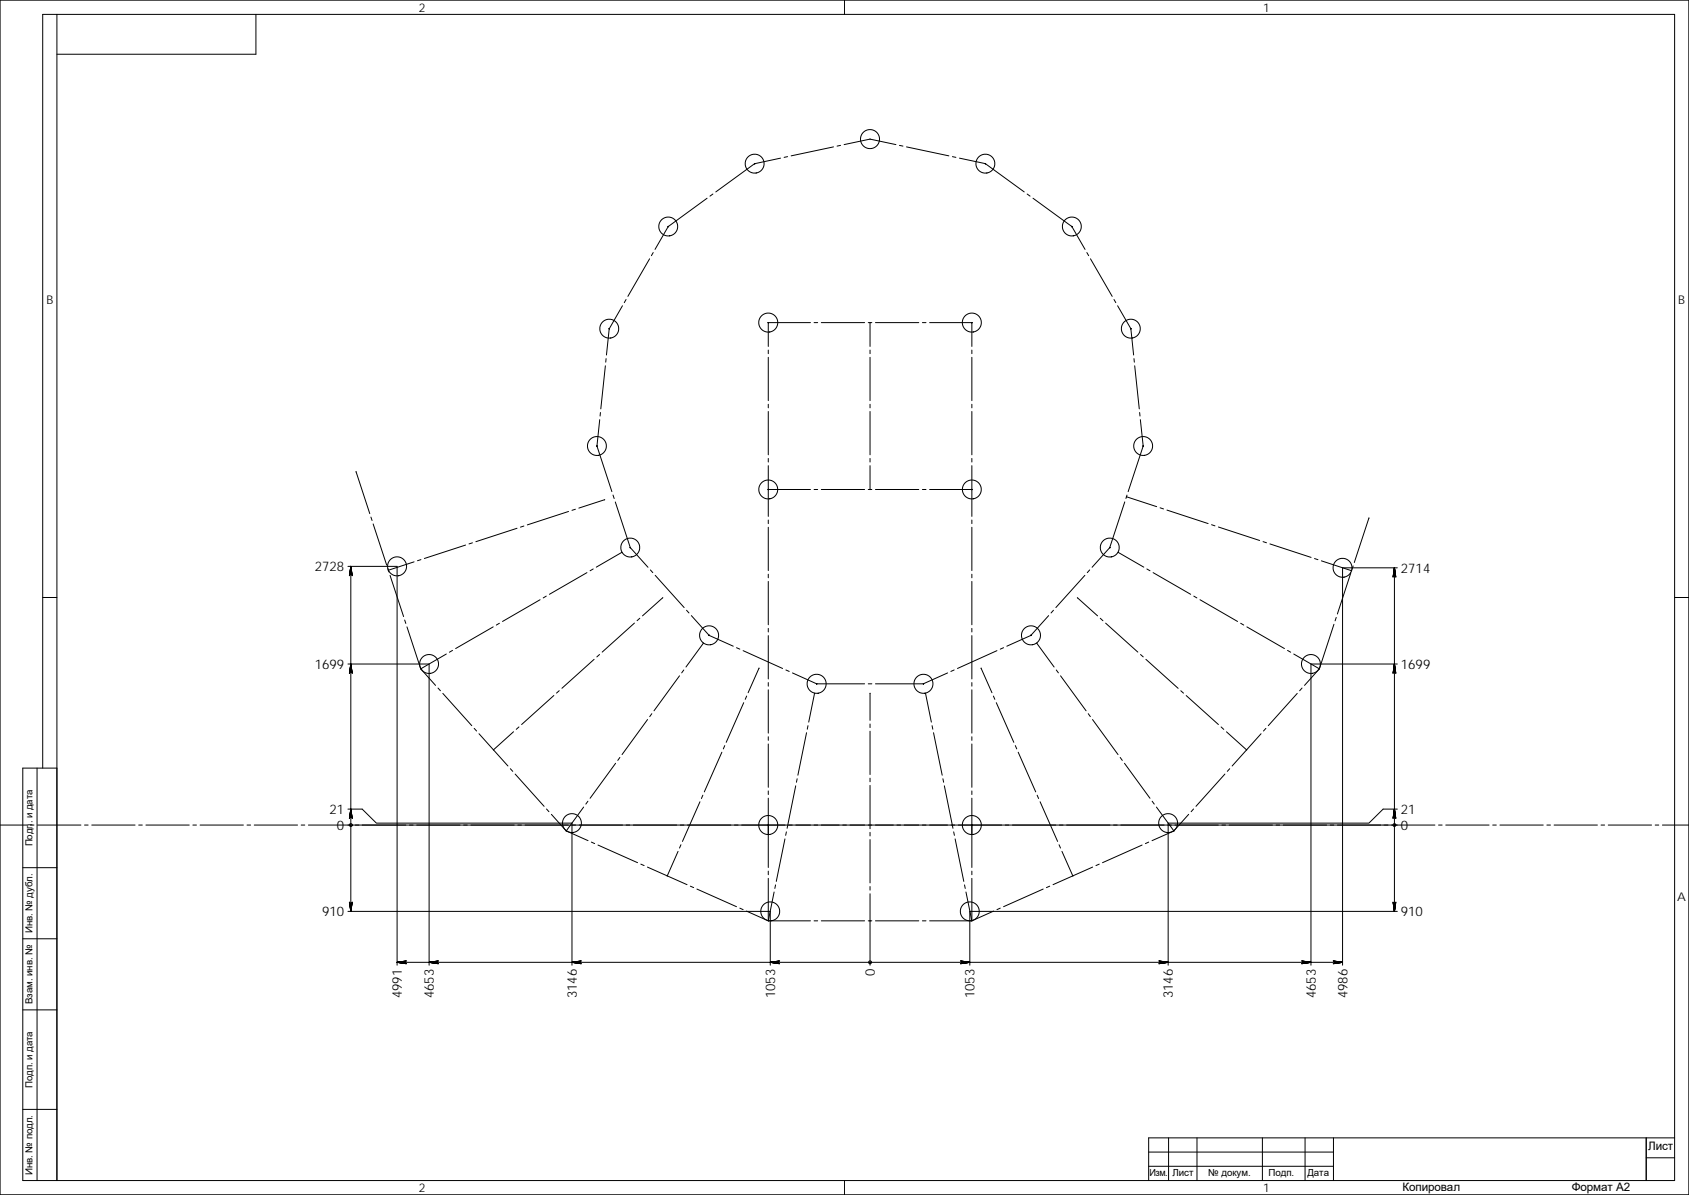
[picture p319: page 1]
Копировал; Лист; Формат А2; Изм.

Подп. и дата Взам. инв. № Инв. № дубл. Подп. и дата

Инв. № подл. № докум. Подп. Дата
