peter-hanzo/KD/Документы/Чертежи/Конструктив/веранда 2.pdf

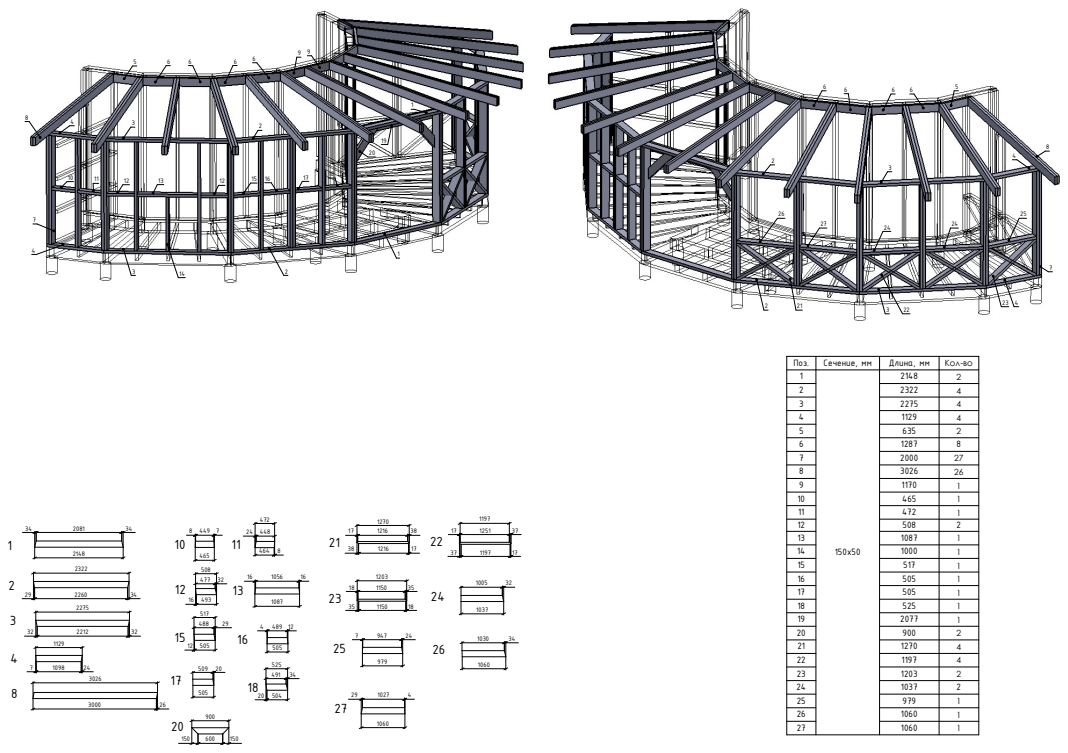
[picture p320: page 1]
Поз.; Сечение, мм; Длина, мм; Кол-во 1

2148 | 2
4 4

6 | 1287 | 2 8
7 | 2000 | 27
8 | 3026 | 26

2 4

1 1
