peter-hanzo/KD/Документы/Чертежи/Конструктив/второй этаж.pdf

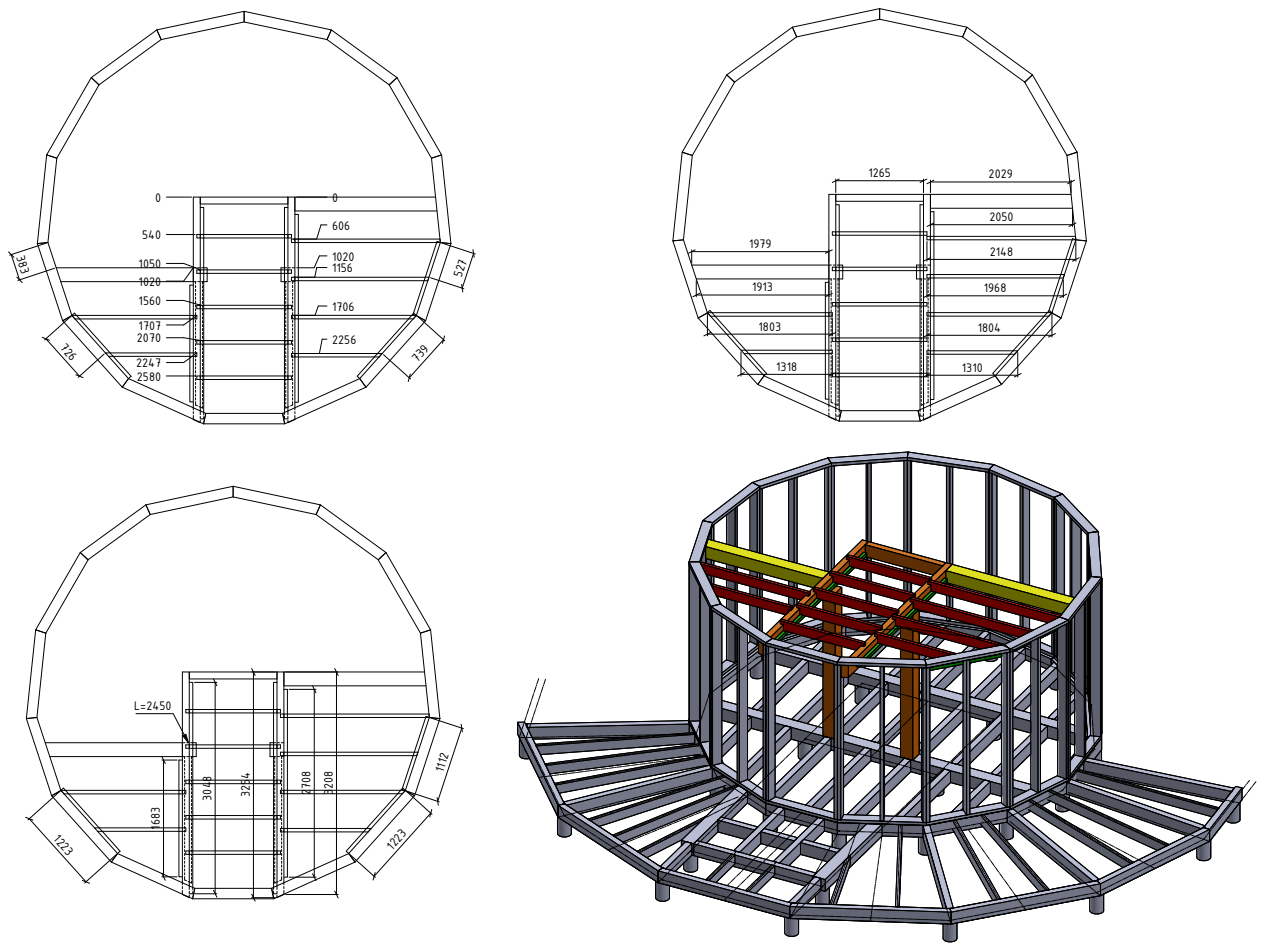
[picture p321: page 1]
