peter-hanzo/KD/Документы/Чертежи/Конструктив/обвязка фундамента веранды.pdf

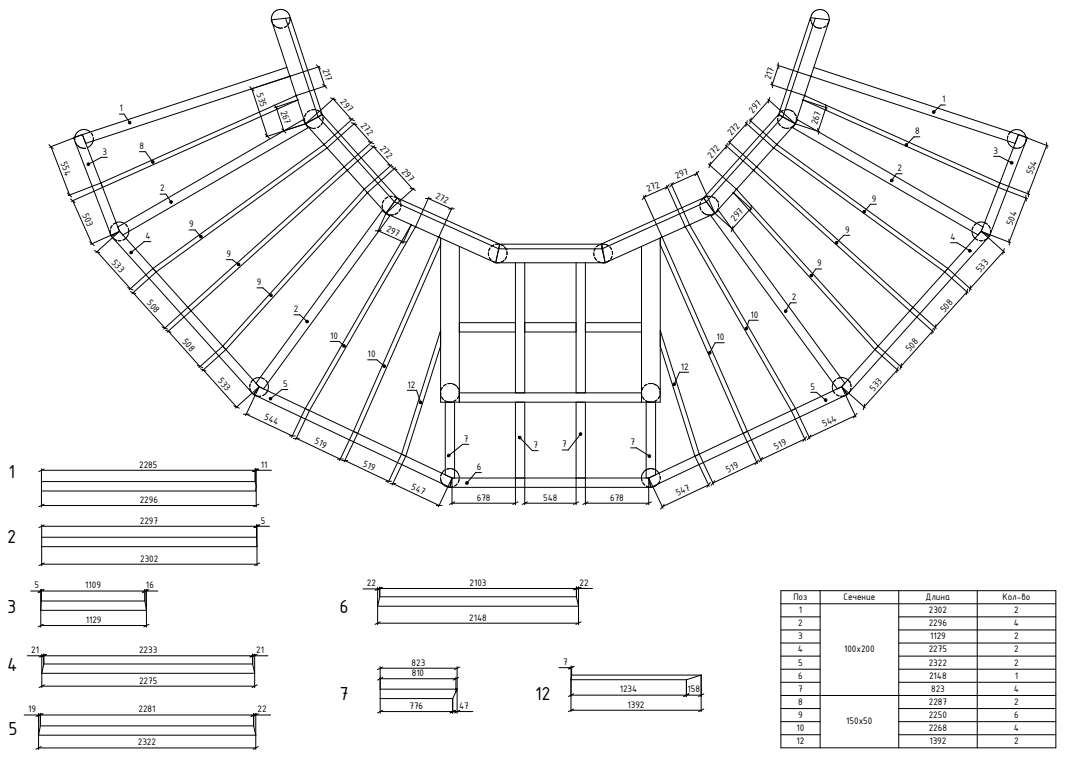
[picture p322: page 1]
Поз; Сечение; Длина; Кол-во

1 | | 2302 2
2 | 100x200 | 2296 | 4
3 | | 1129 | 2
4 | | 2275 | 2
5 | | 2322 | 2
6 | | 2148 | 1
7 | | 823 | 4
8 | | 2287 2
9 | 150x50 | 2250 | 6
10 | | 2268 | 4
12 | | 1392 | 2
