peter-hanzo/KD/Документы/Чертежи/Крыша/Верх_01.pdf

2 | 1

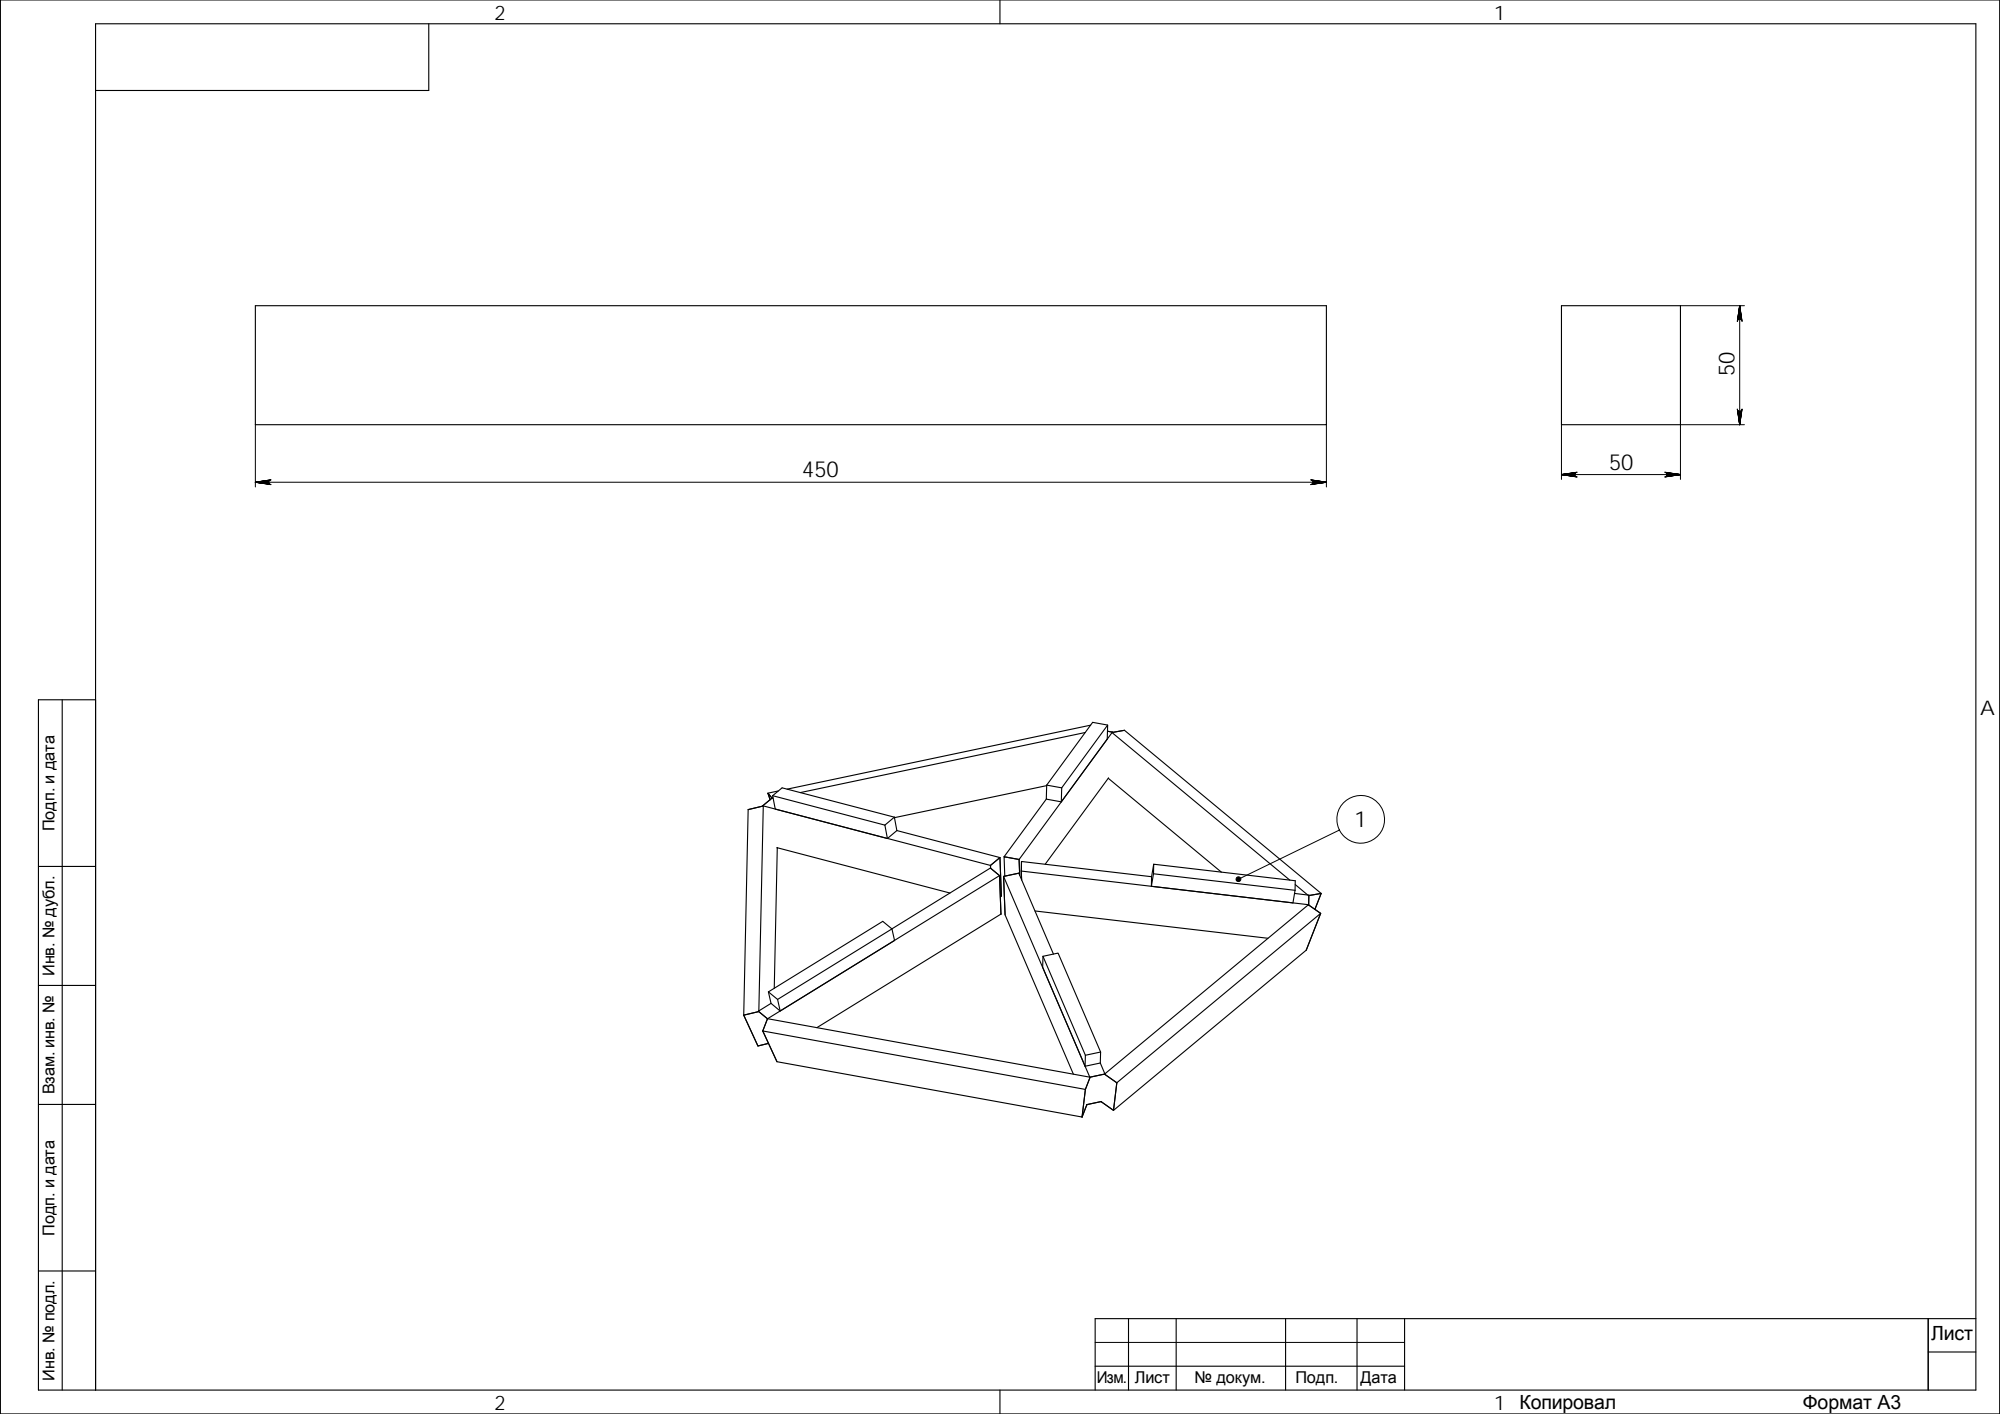
[picture p323: page 1]
Изм.; Лист; Копировал; Формат А3

Инв. № подл. Подп. и дата Взам. инв. № Инв. № дубл. Подп. и дата № докум. Подп. Дата
