peter-hanzo/KD/Документы/Чертежи/Крыша/Верх_02.pdf

287.3

2 | 1

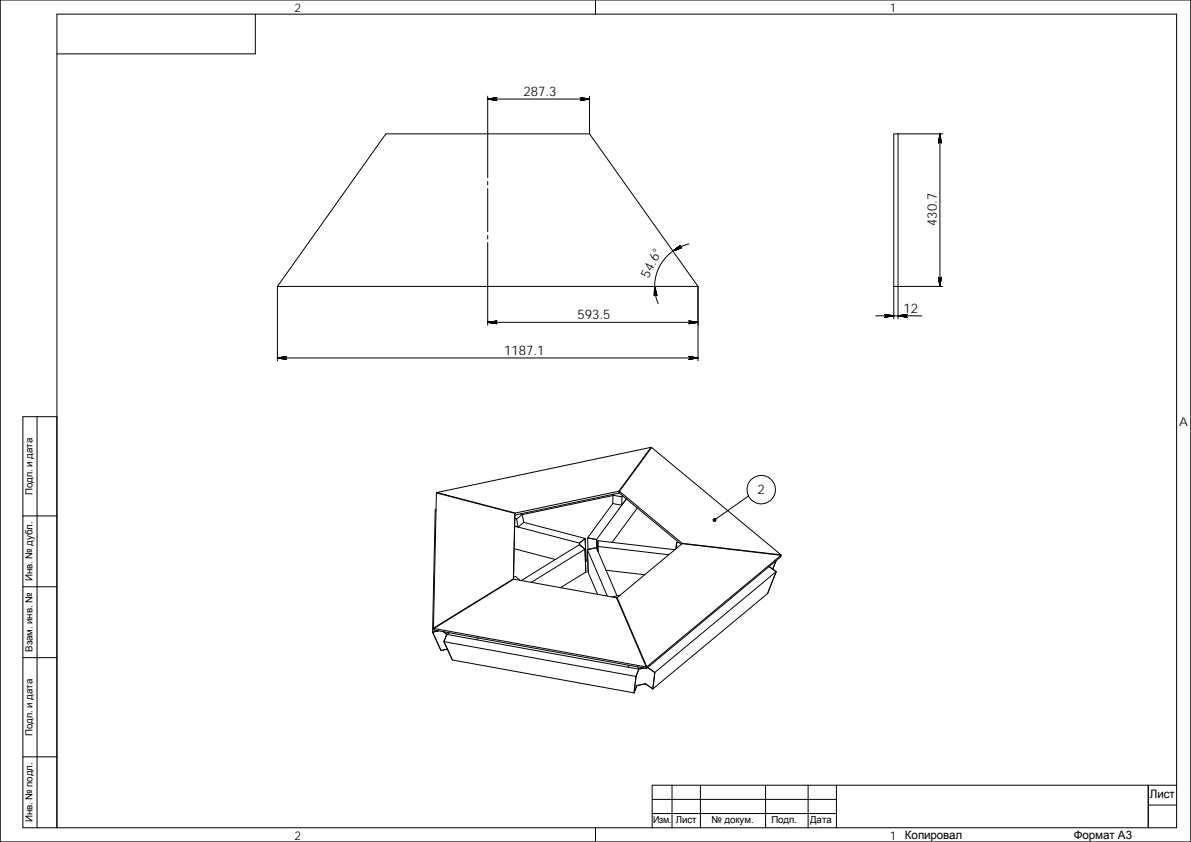
[picture p324: page 1]
Формат А3; Изм.; Лист; Копировал

Инв. № подл. Подп. и дата Взам. инв. № Инв. № дубл. Подп. и дата № докум. Подп. Дата
