peter-hanzo/KD/Документы/Чертежи/Крыша/Верх_03.pdf

340.4

2 | 1

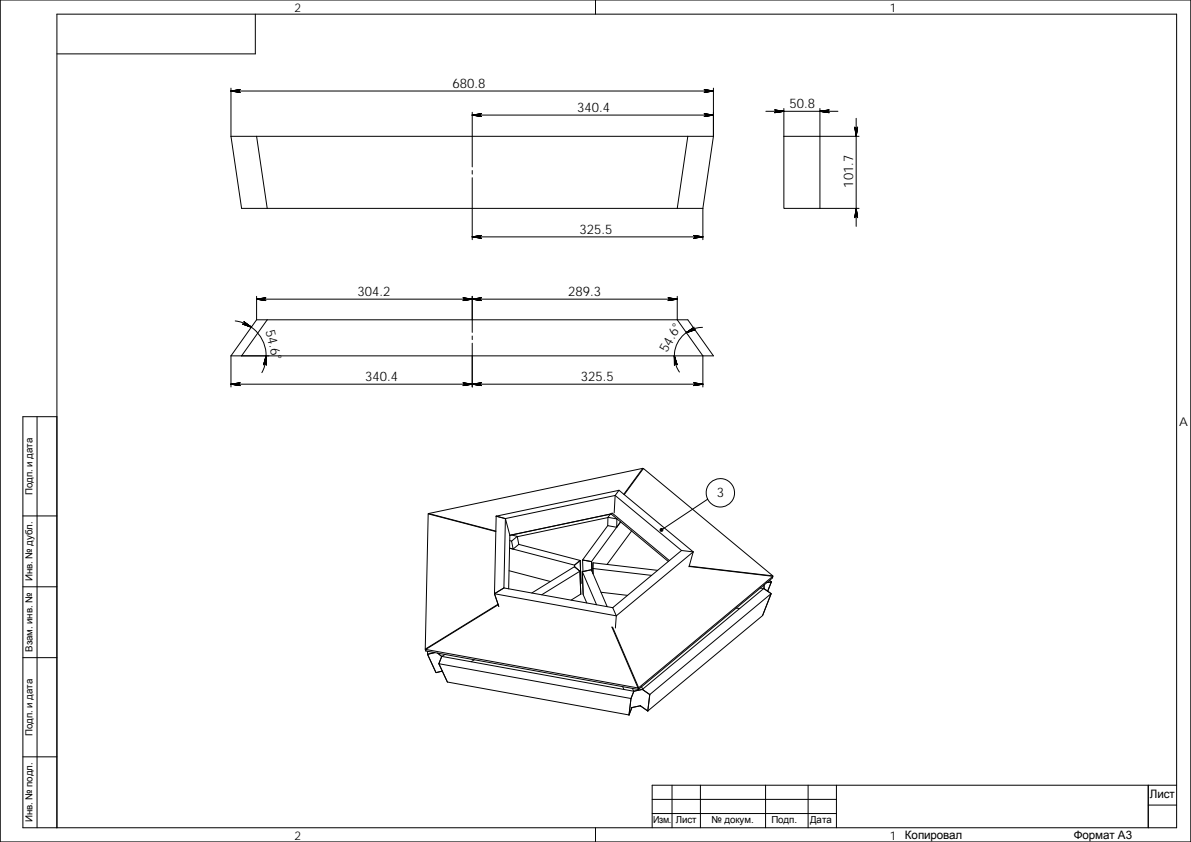
[picture p325: page 1]
Копировал; Лист; Формат А3; Изм.

Инв. № подл. Подп. и дата Взам. инв. № Инв. № дубл. Подп. и дата № докум. Подп. Дата
