peter-hanzo/KD/Документы/Чертежи/Крыша/Верх_07.pdf

2 | 1
454.1 | 221.4

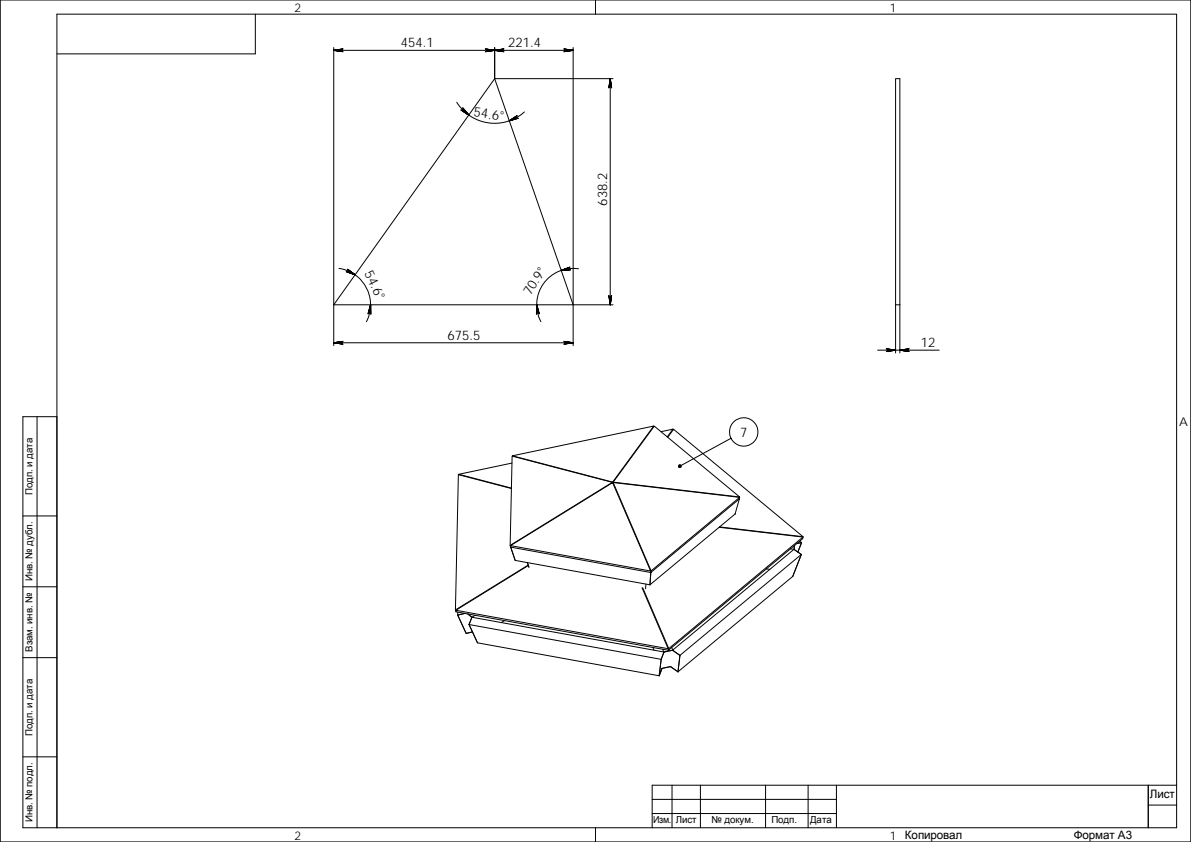
[picture p326: page 1]
Копировал; Лист; Формат А3; Изм.

Инв. № подл. Подп. и дата Взам. инв. № Инв. № дубл. Подп. и дата № докум. Подп. Дата
