peter-hanzo/KD/Документы/Чертежи/Крыша/Металл-профиль.pdf

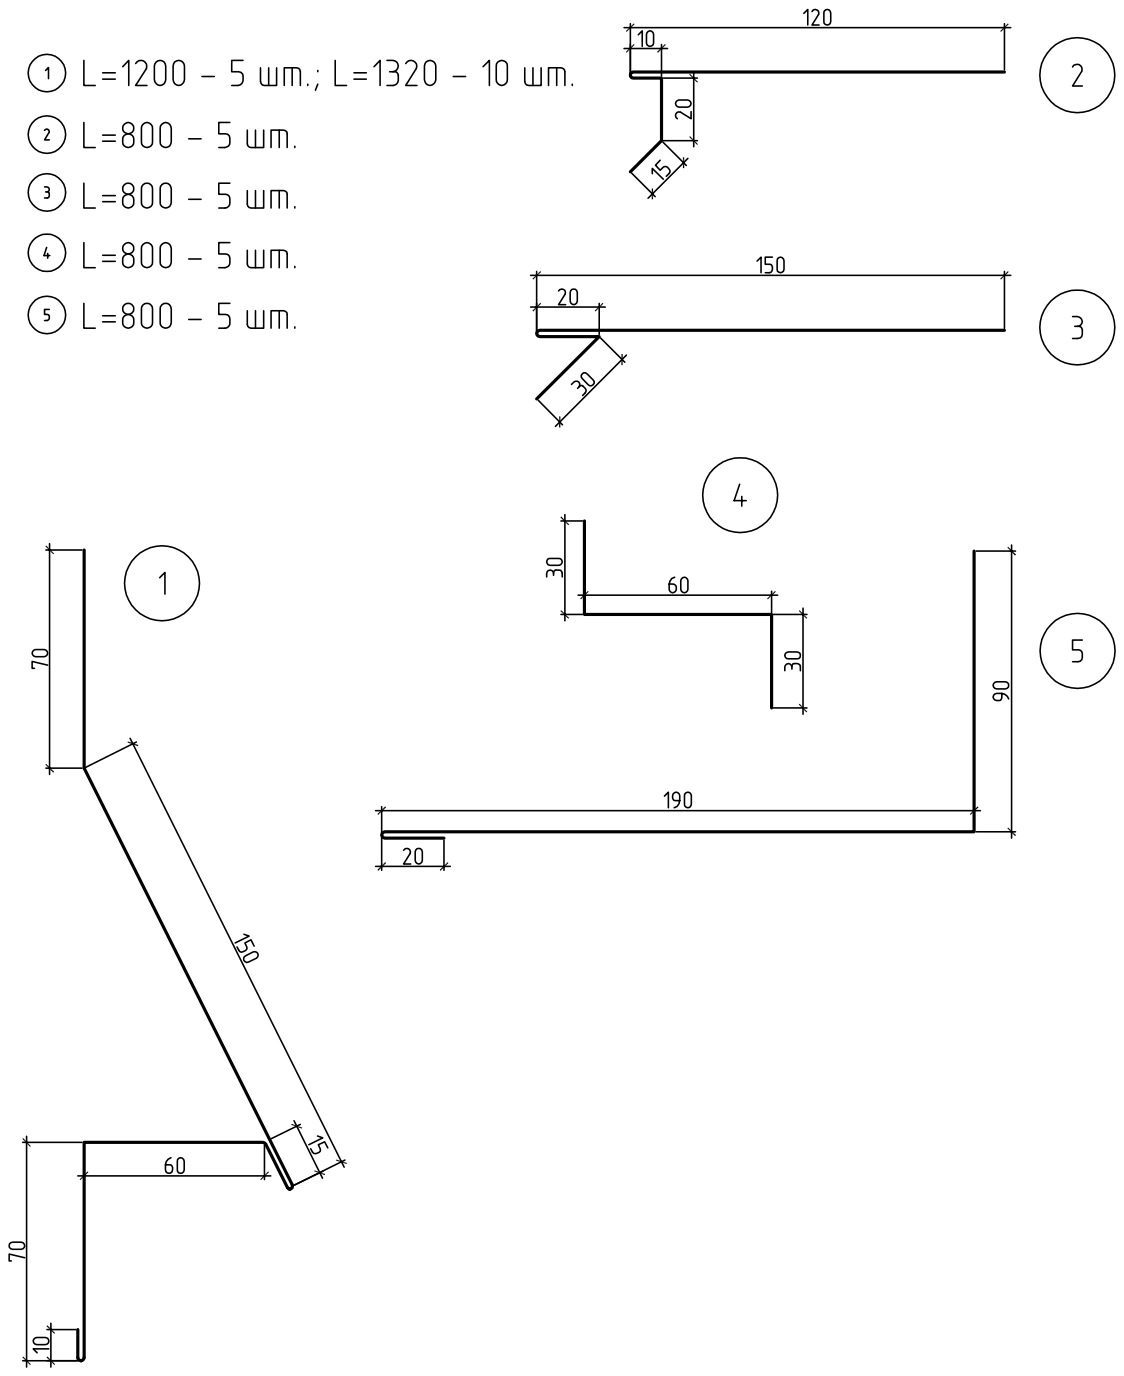
[picture p327: page 1]
