peter-hanzo/KD/Документы/Чертежи/Конструктив/Схема сборки и обшивки каркаса под брусок50на50.pdf

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

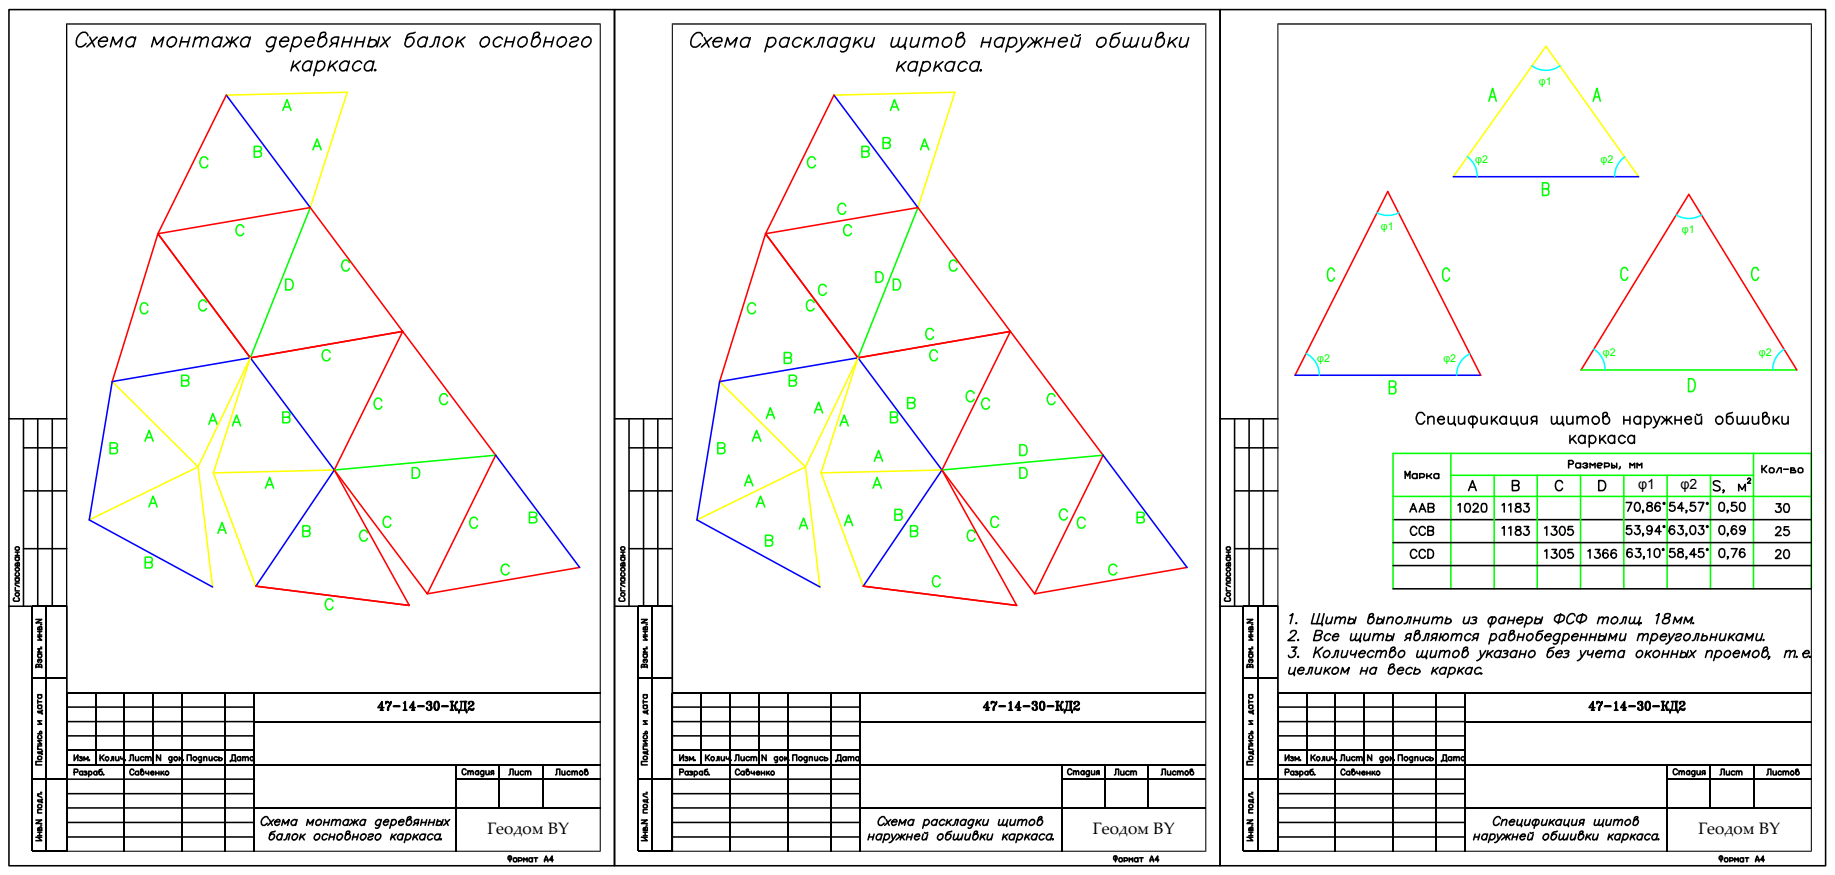
[picture p329: page 1]
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
