peter-hanzo/KD/Документы/Чертежи/Конструктив/perekrytie_1-y_etazh.pdf

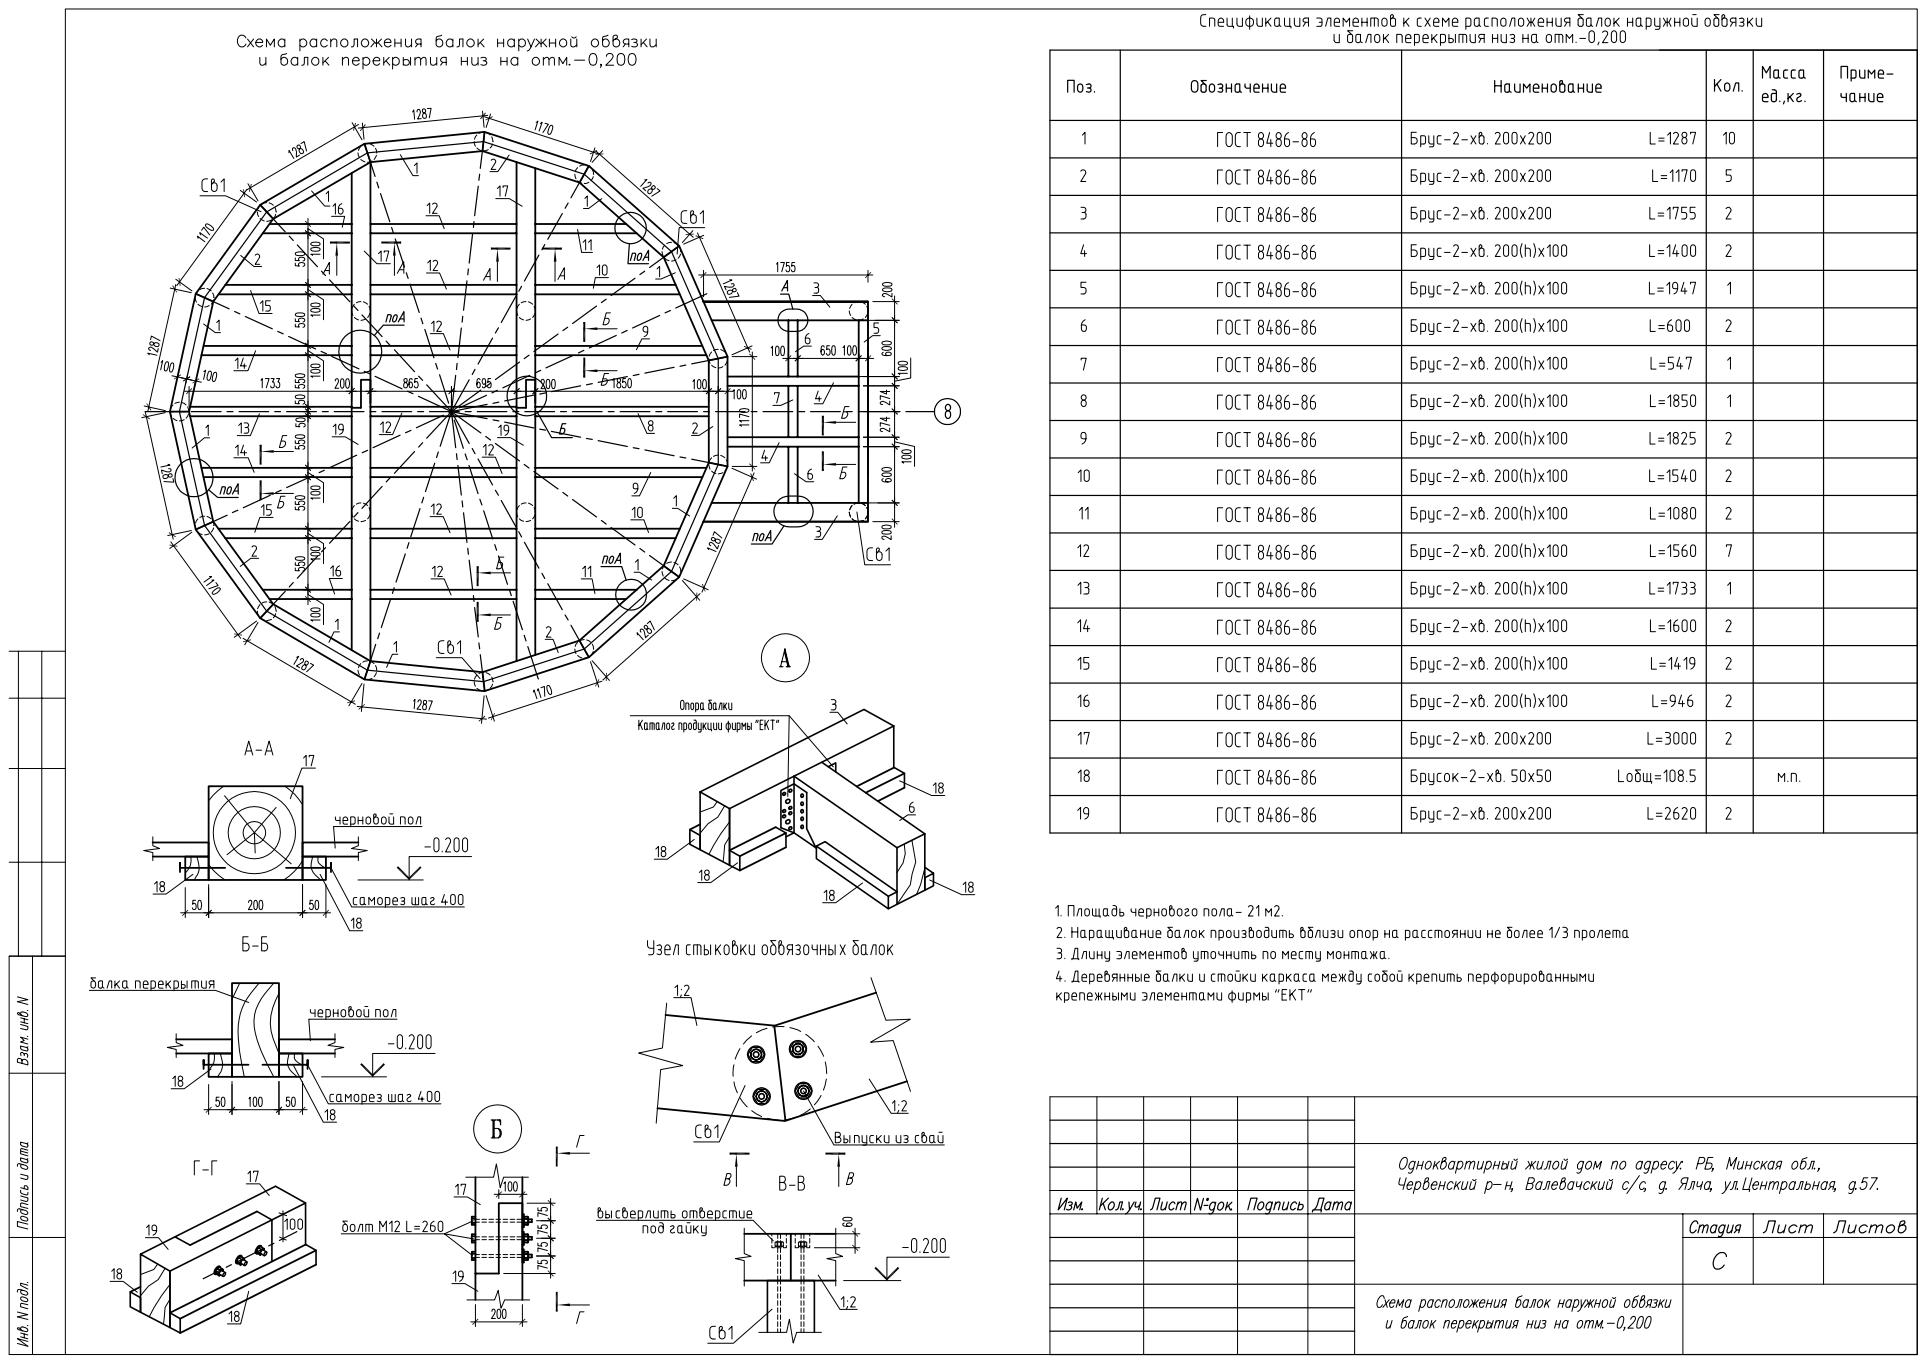
[picture p330: page 1]
