peter-hanzo/KD/Документы/Чертежи/Конструктив/Спецификация балок обвязки.pdf

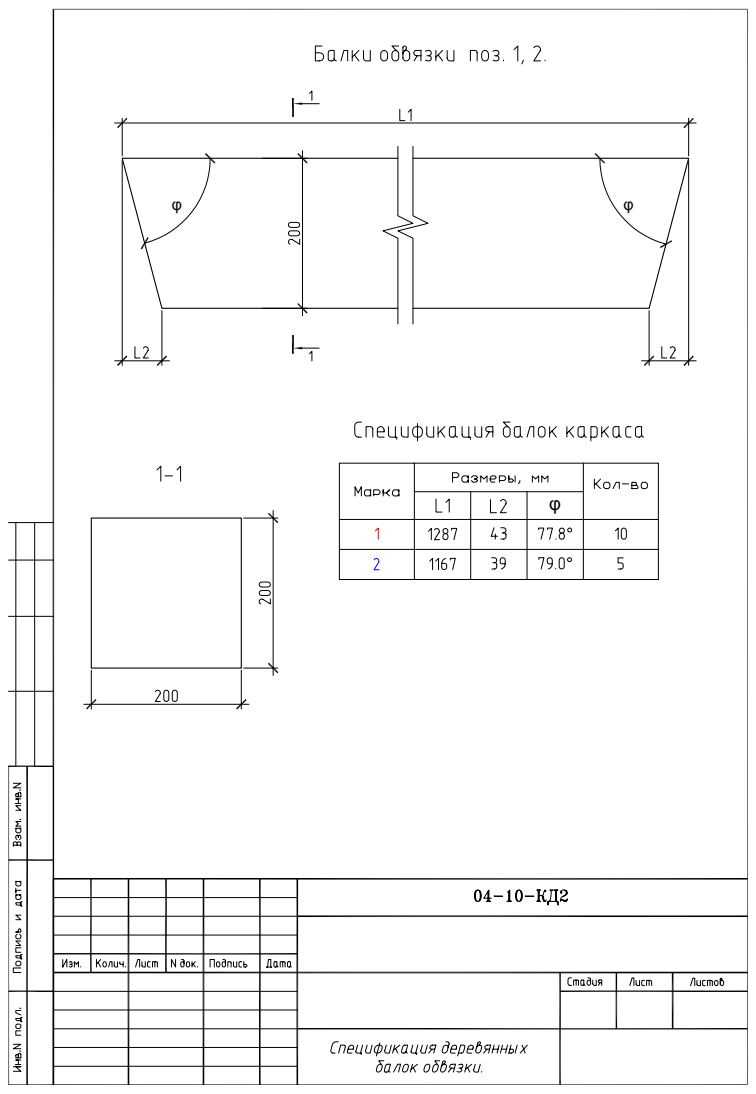
[picture p337: page 1]
