peter-hanzo/KD/Документы/Чертежи/Конструктив/Спецификация балок.pdf

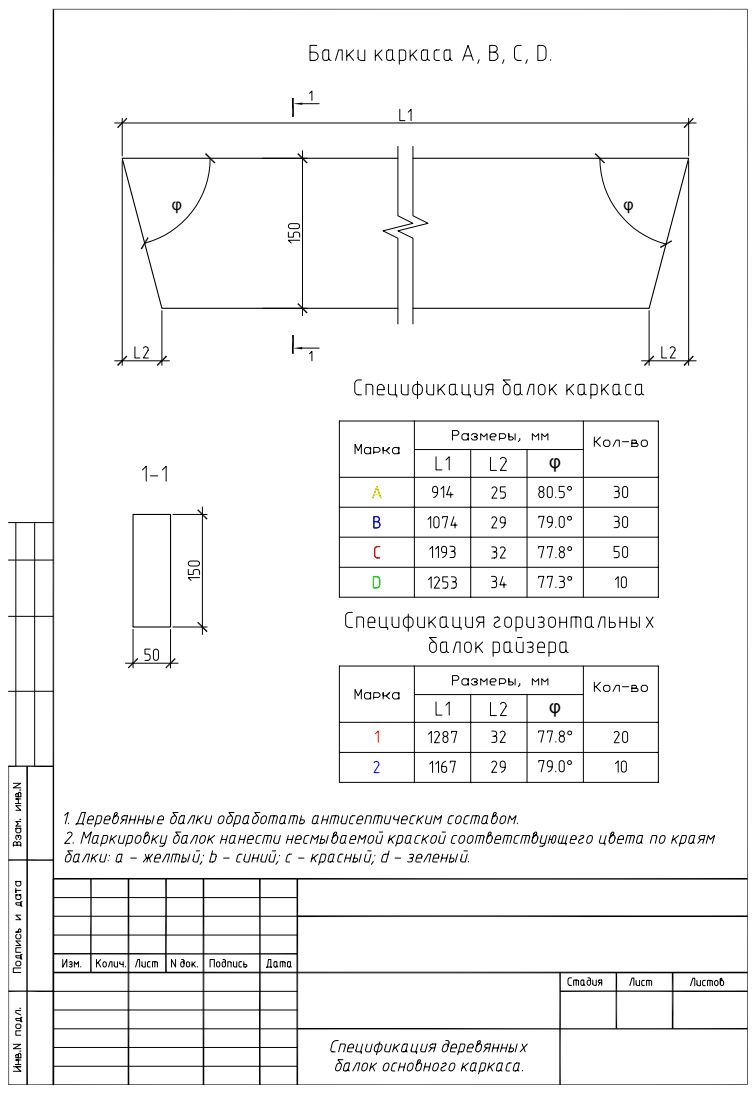
[picture p338: page 1]
