peter-hanzo/KD/Документы/Чертежи/Конструктив/Схема сборки и обшивки каркаса.pdf

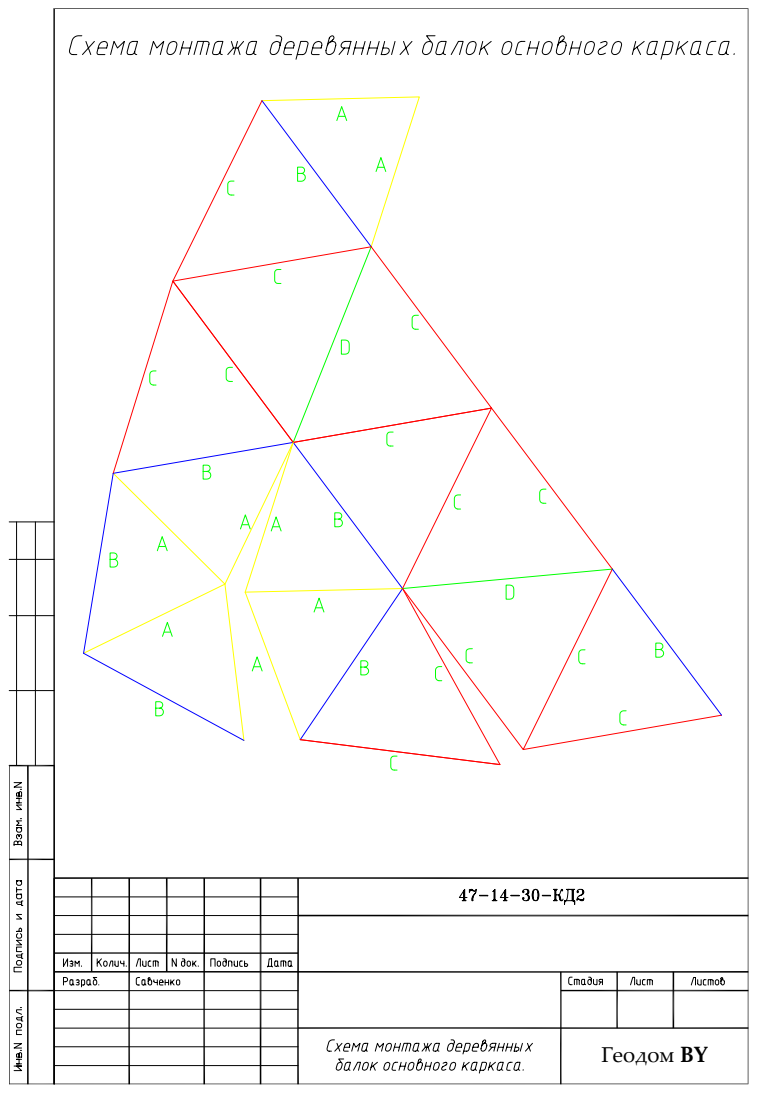
[picture p339: page 1]
Геодом BY

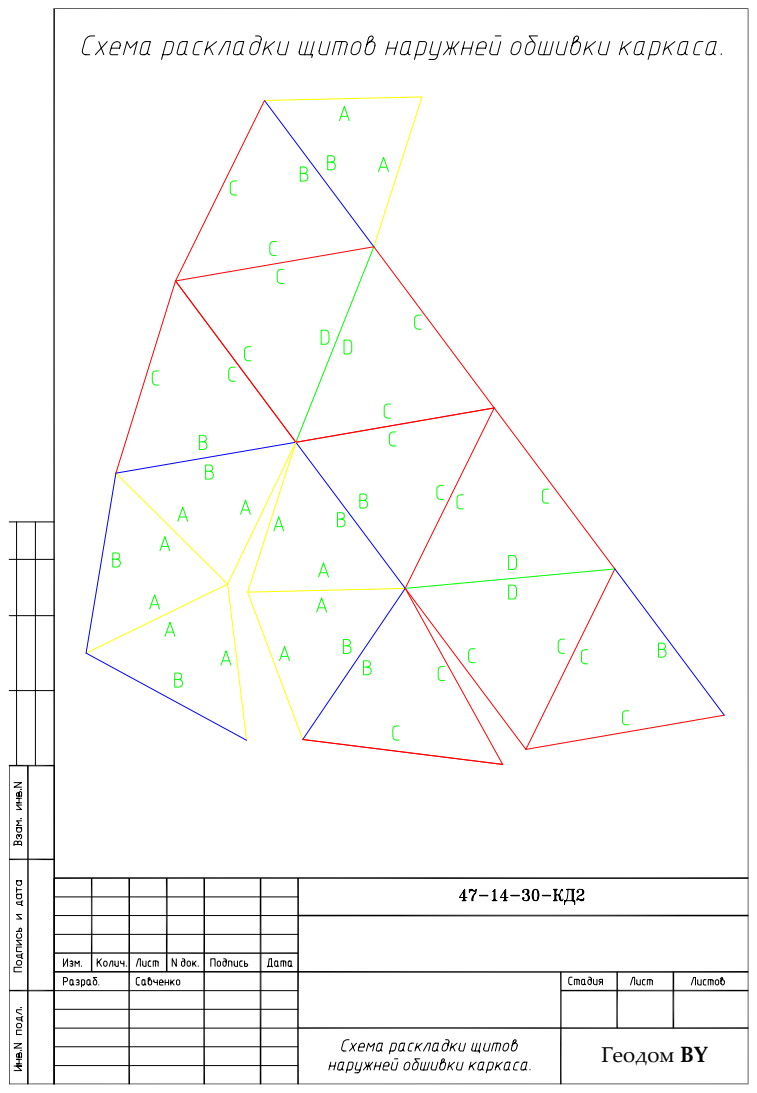
[picture p340: page 2]

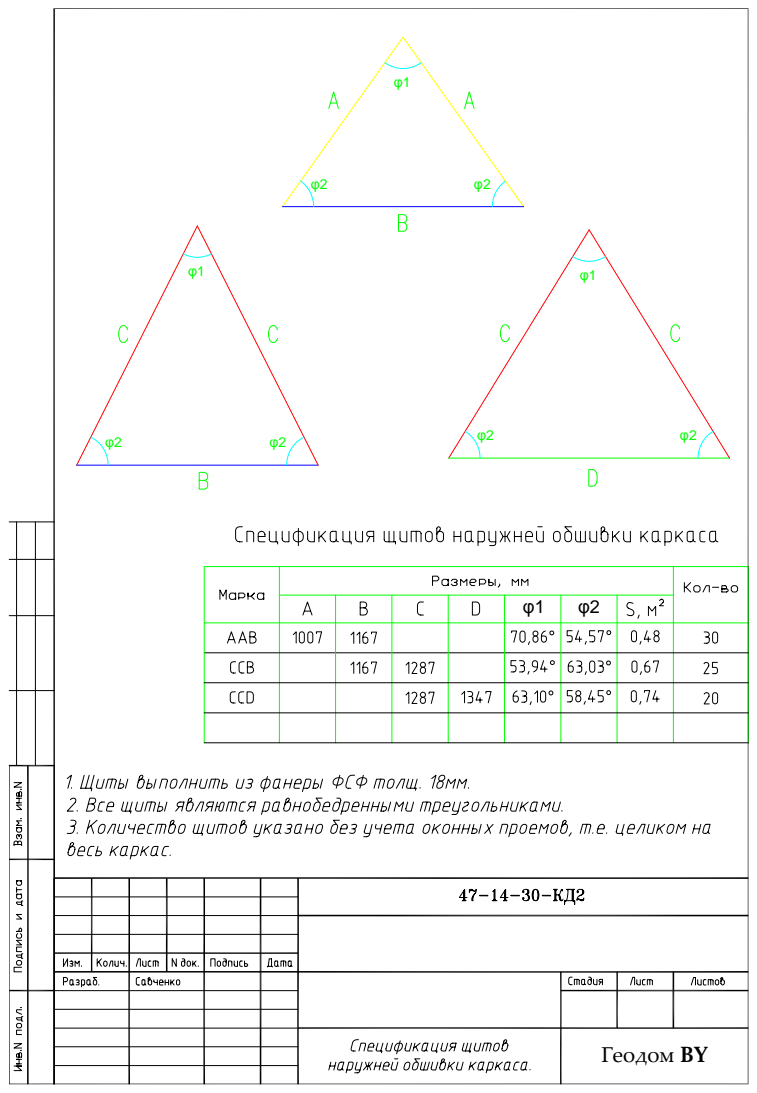
[picture p341: page 3]
