peter-hanzo/KD/Документы/Чертежи/Конструктив/пластины и уголок.pdf

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

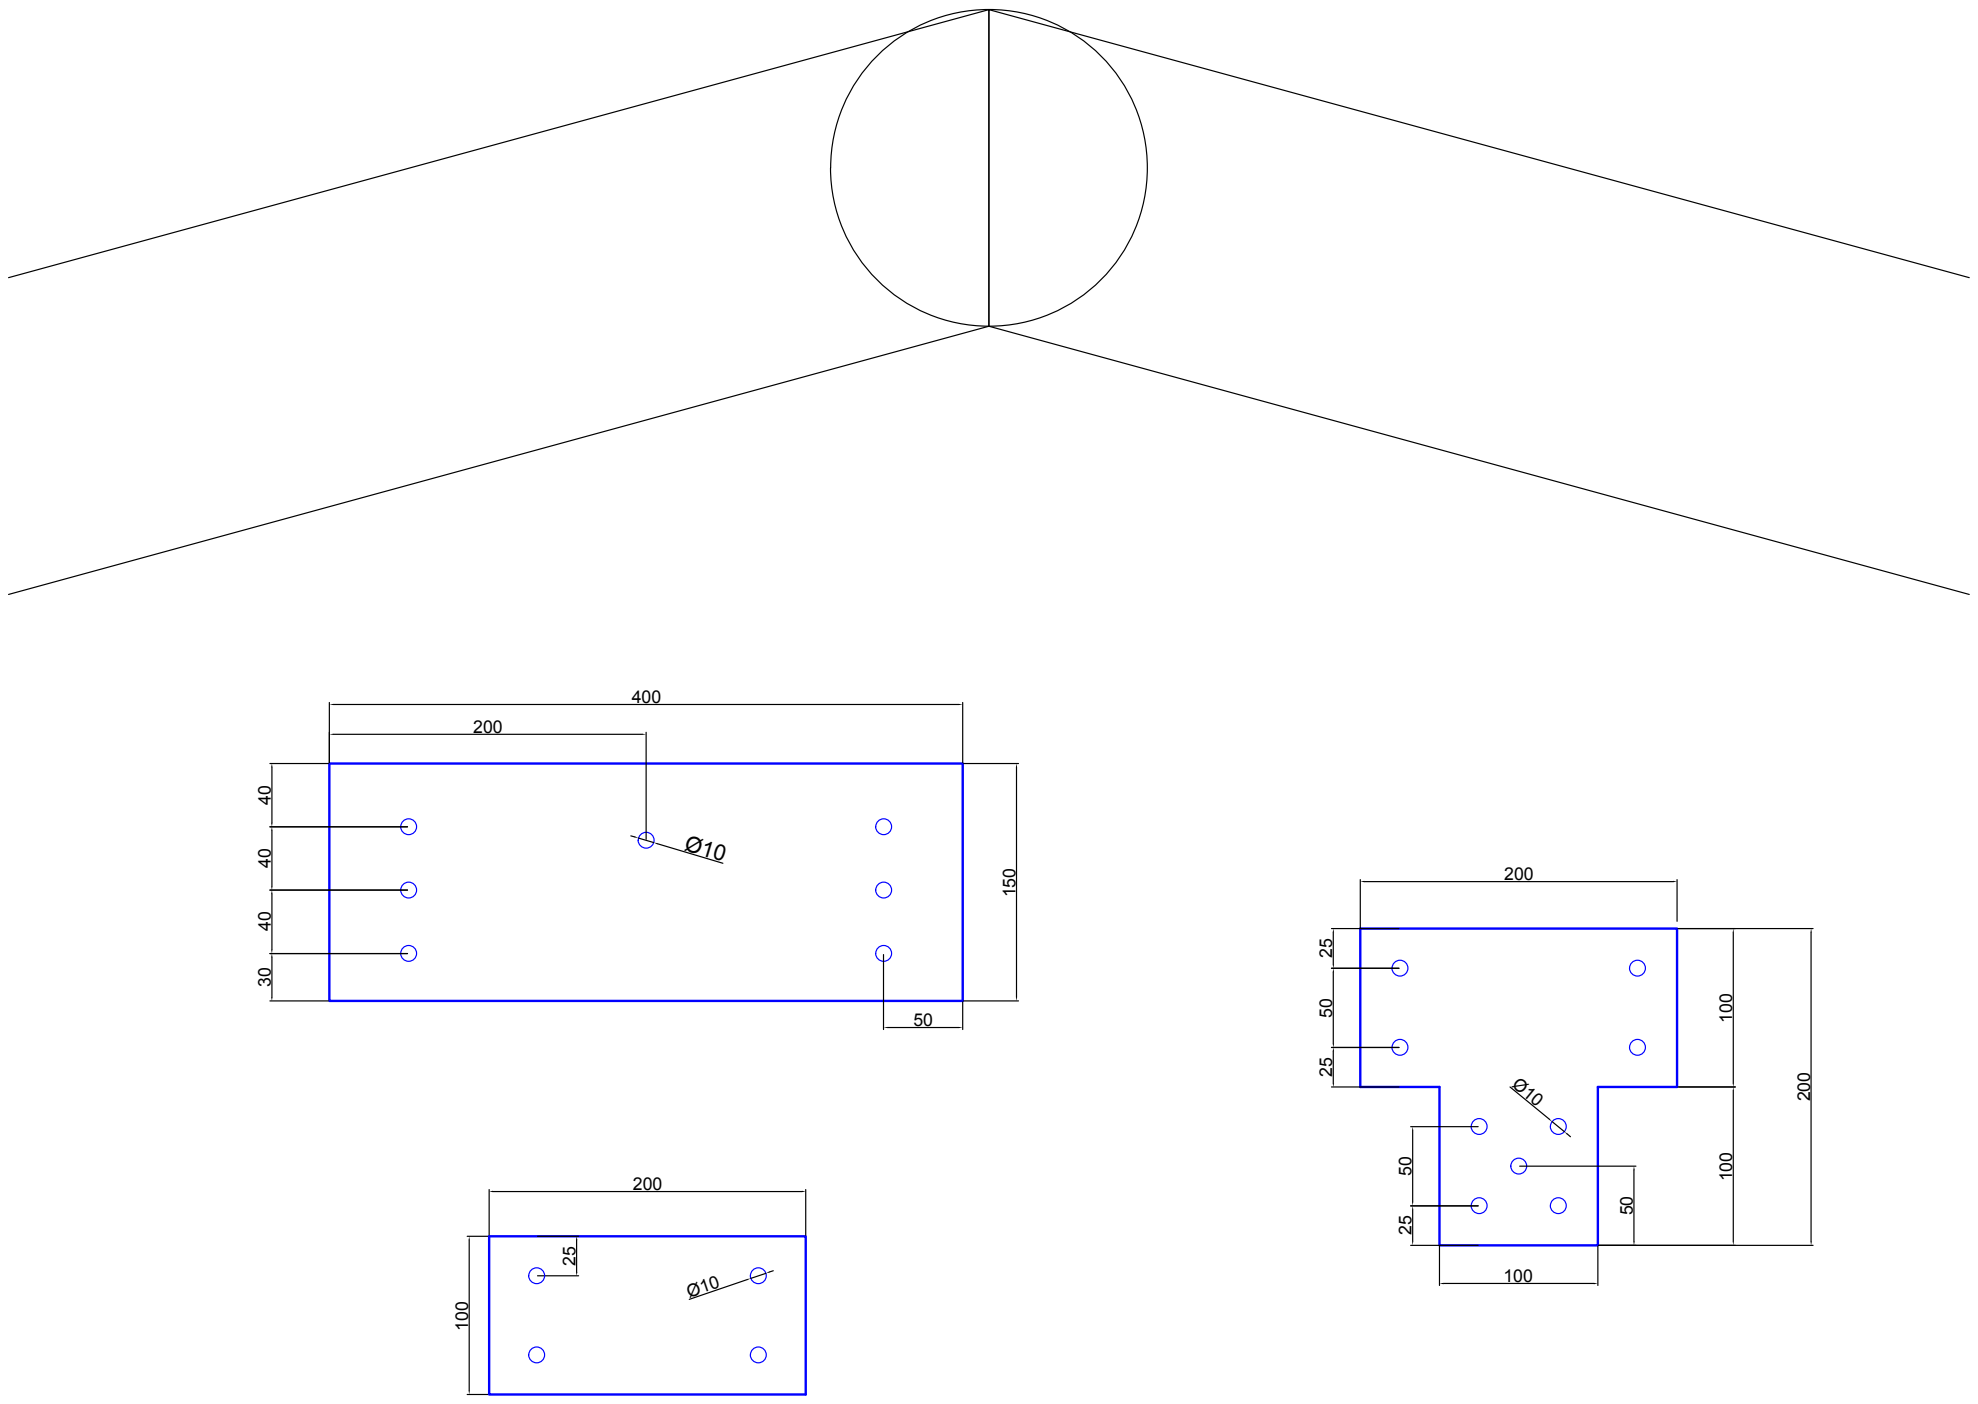
[picture p342: page 1]
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
