peter-hanzo/KD/Документы/Чертежи/Фундамент/разметка фундамента-1.pdf

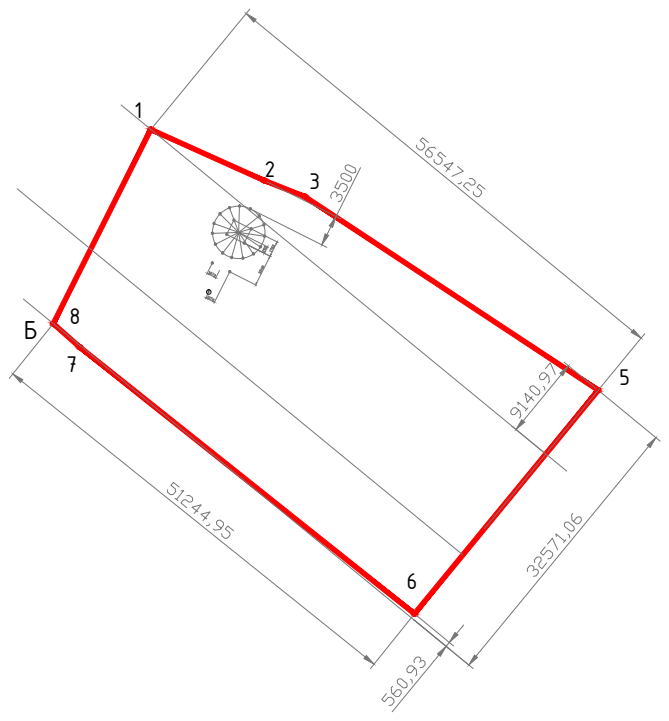
[picture p343: page 1]
