peter-hanzo/KD/Документы/Чертежи/Фундамент/разметка фундамента-2.pdf

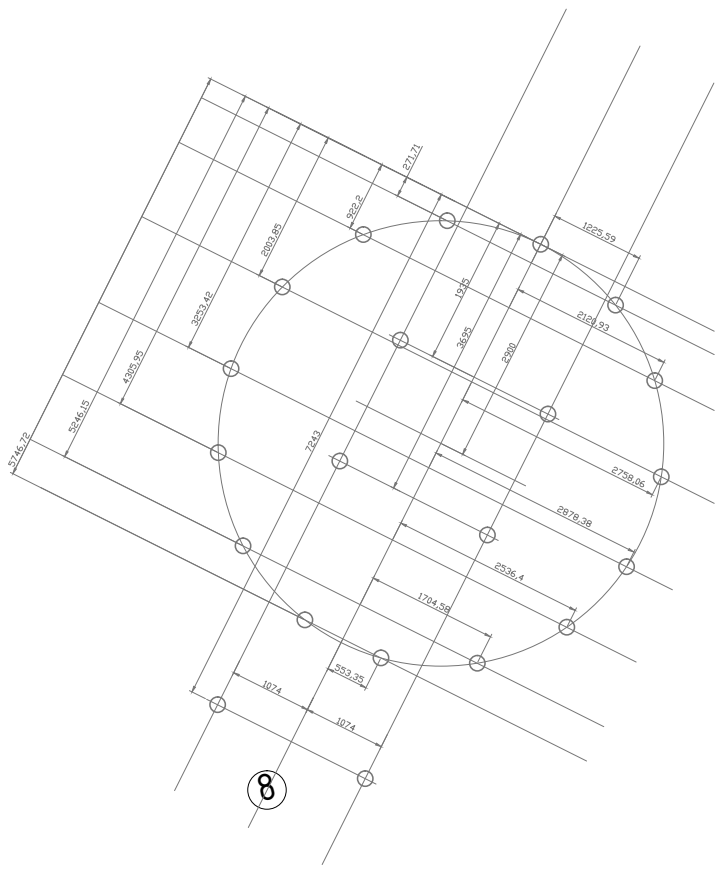
[picture p344: page 1]
