peter-hanzo/KD/Документы/Чертежи/Фундамент/План фундамента.pdf

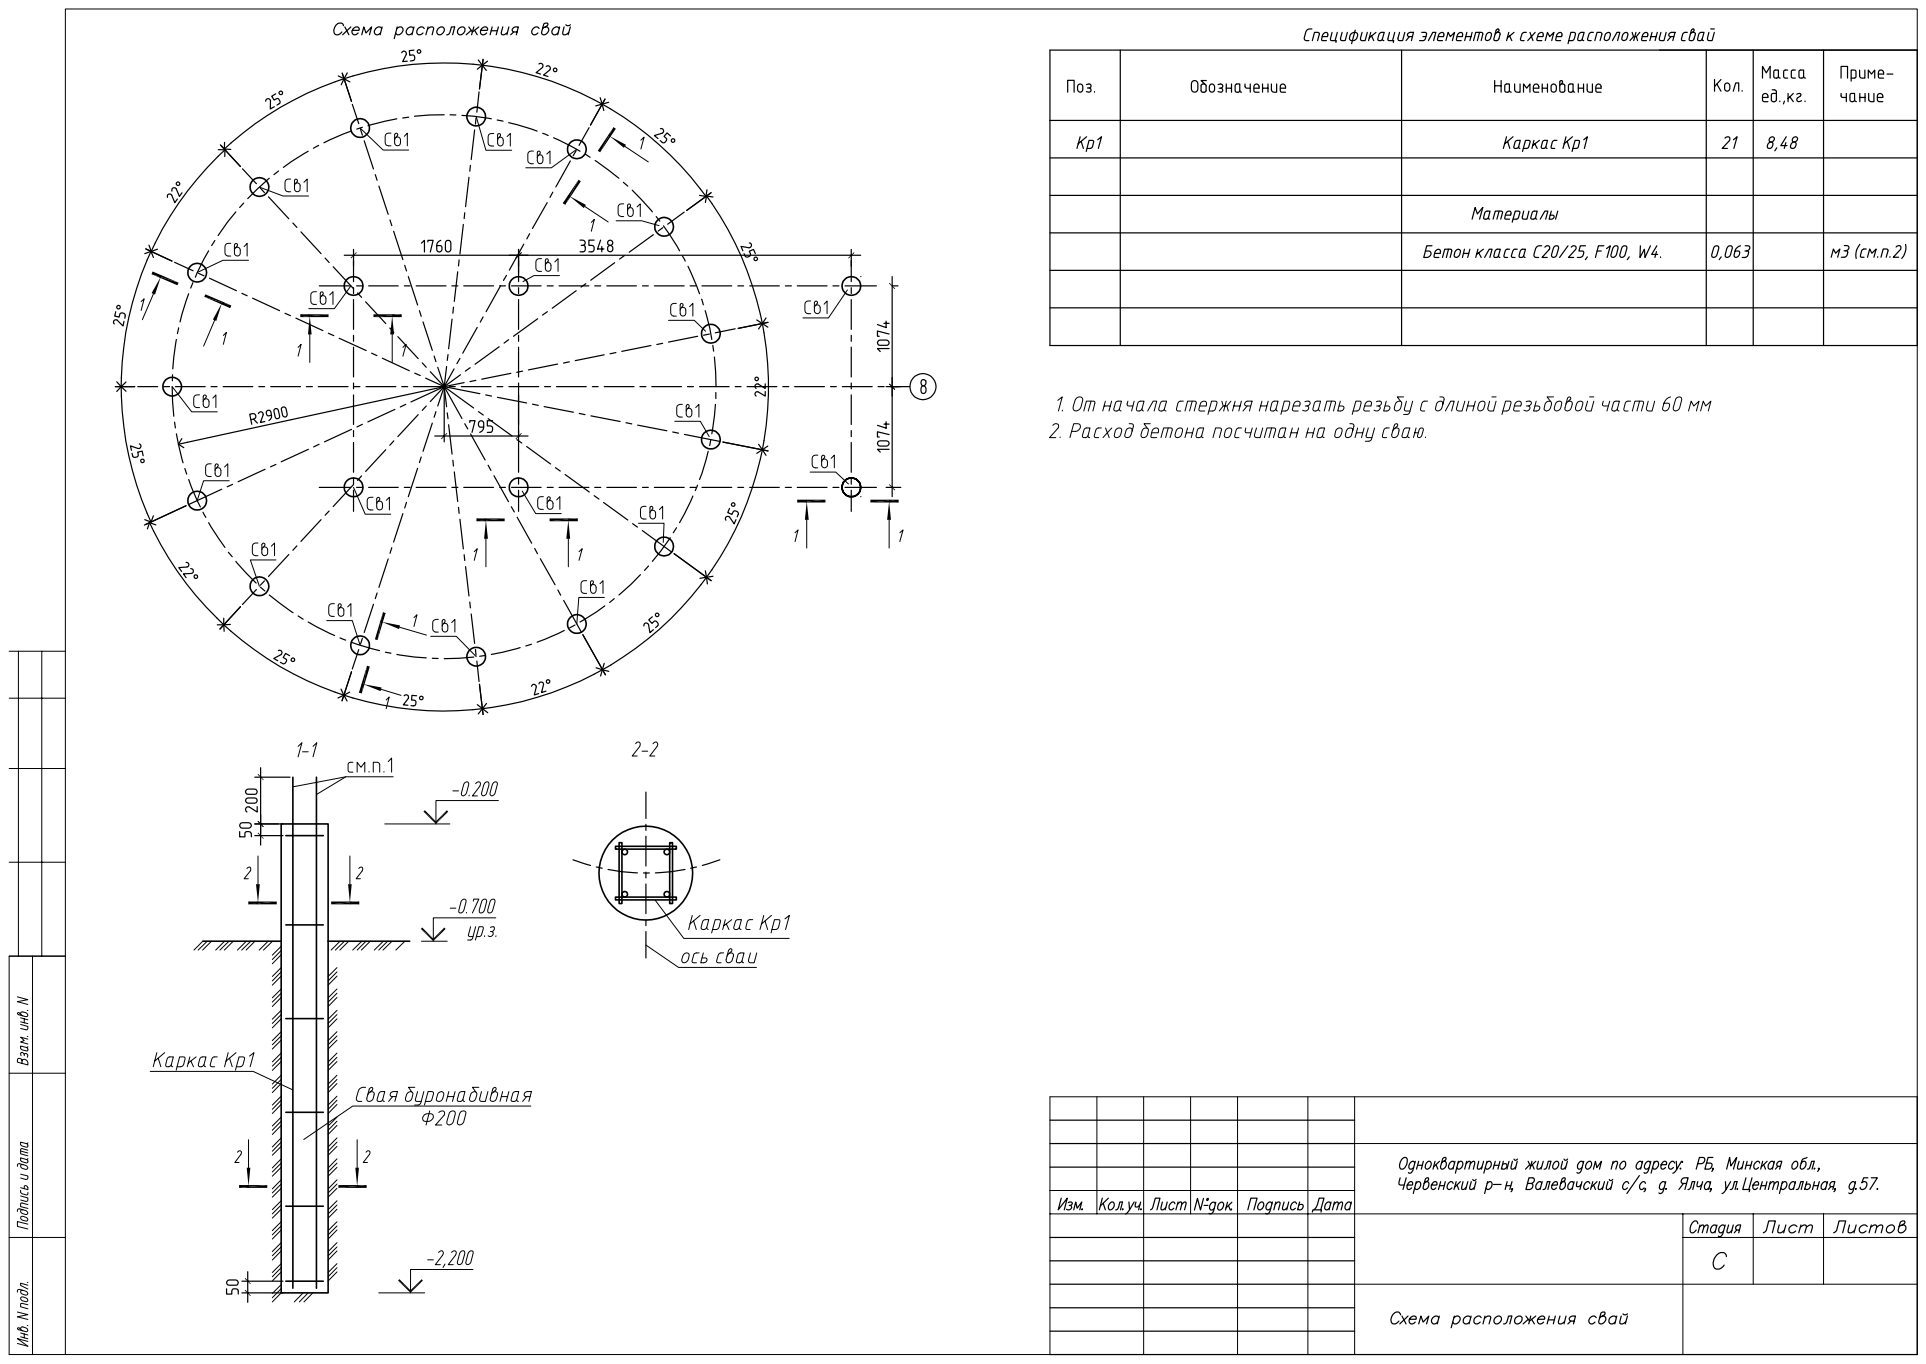
[picture p345: page 1]

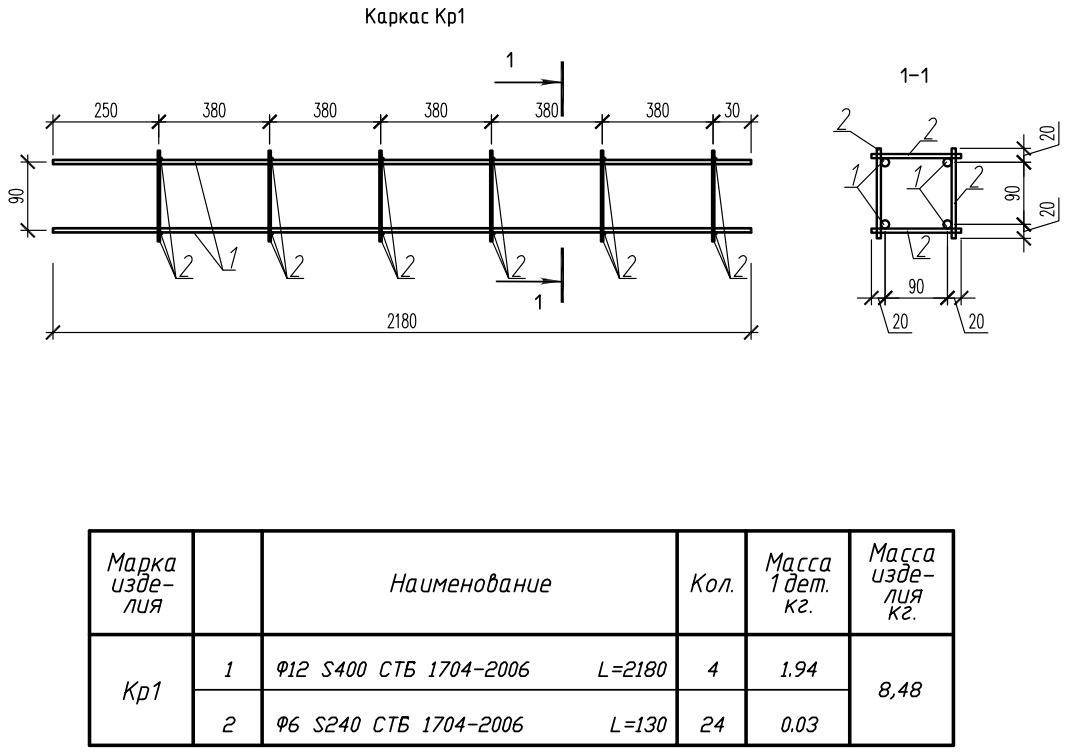
[picture p346: page 2]
