peter-hanzo/KD/Что бывает/Чертежи/Пример архитектурного проекта/лист 1.pdf

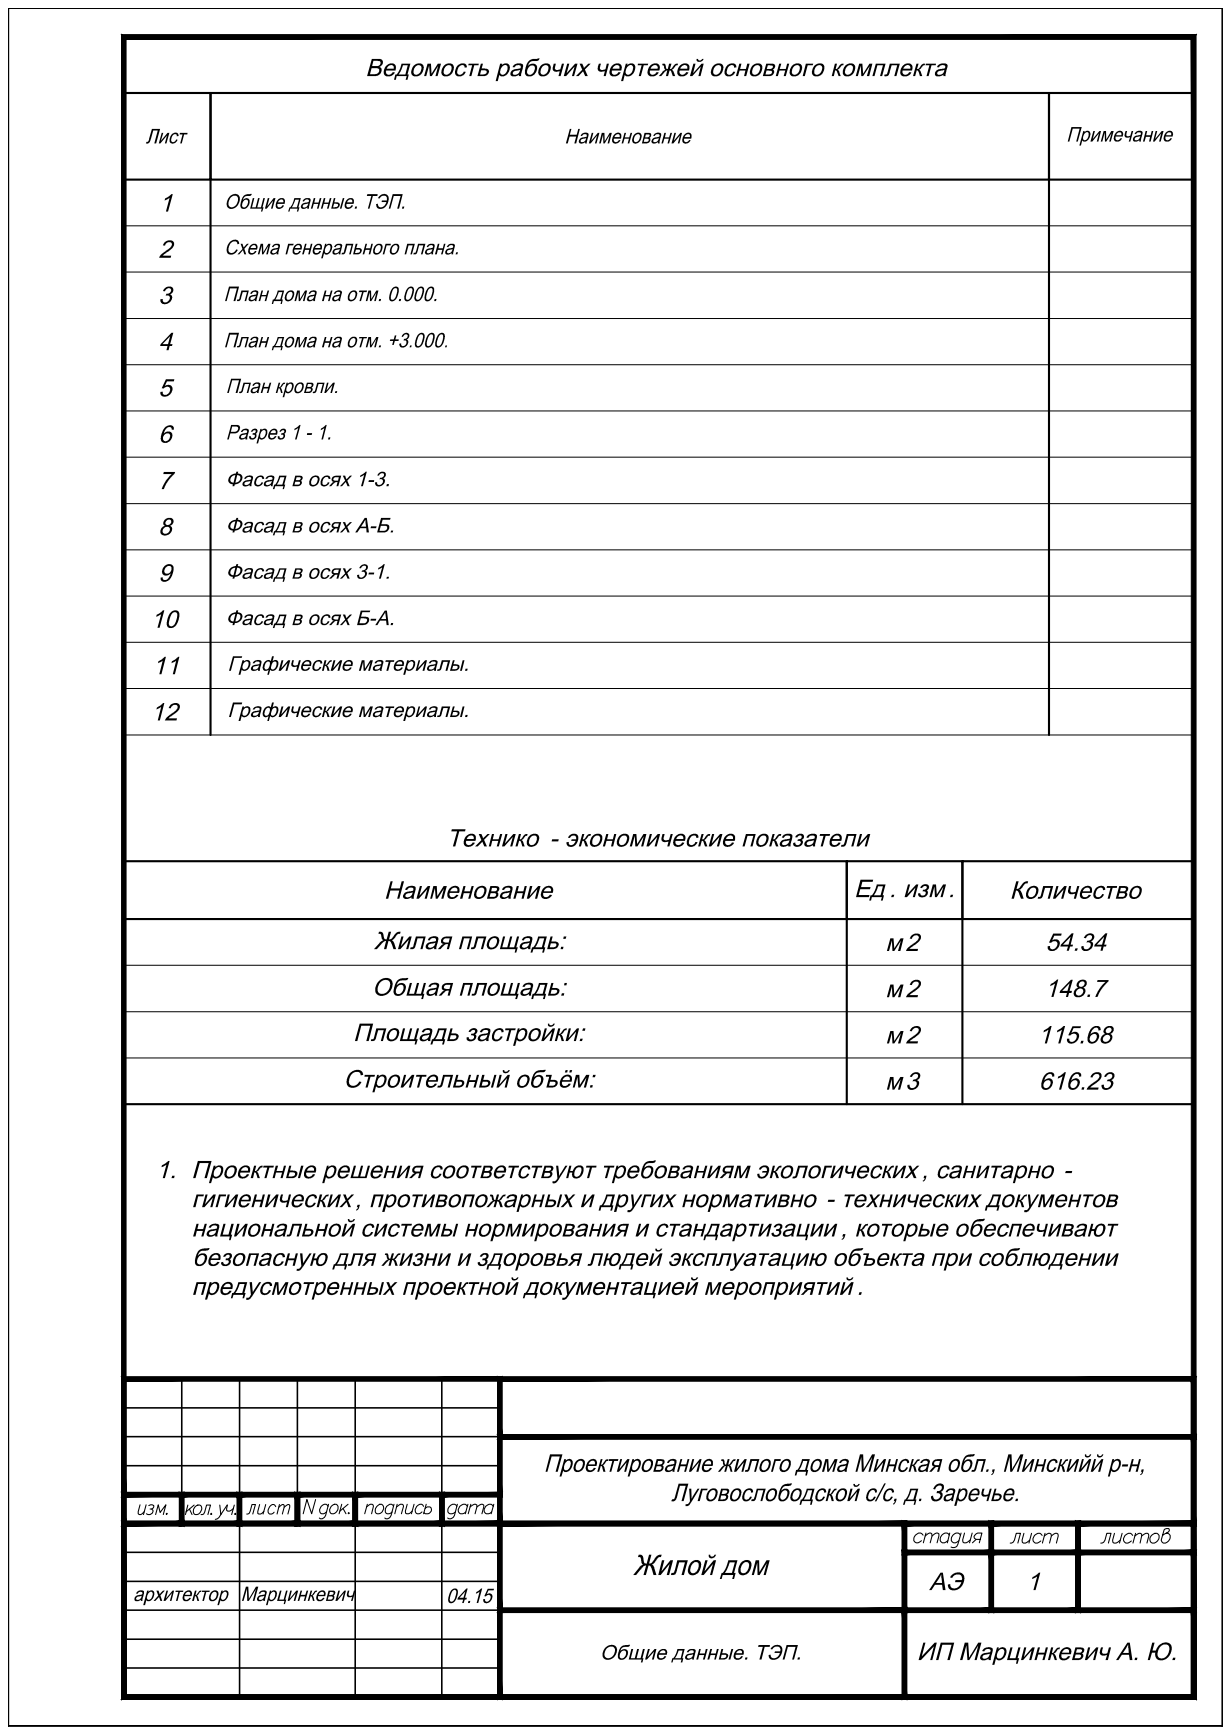
[picture p347: page 1]
