peter-hanzo/KD/Что бывает/Чертежи/Пример архитектурного проекта/лист 10.pdf

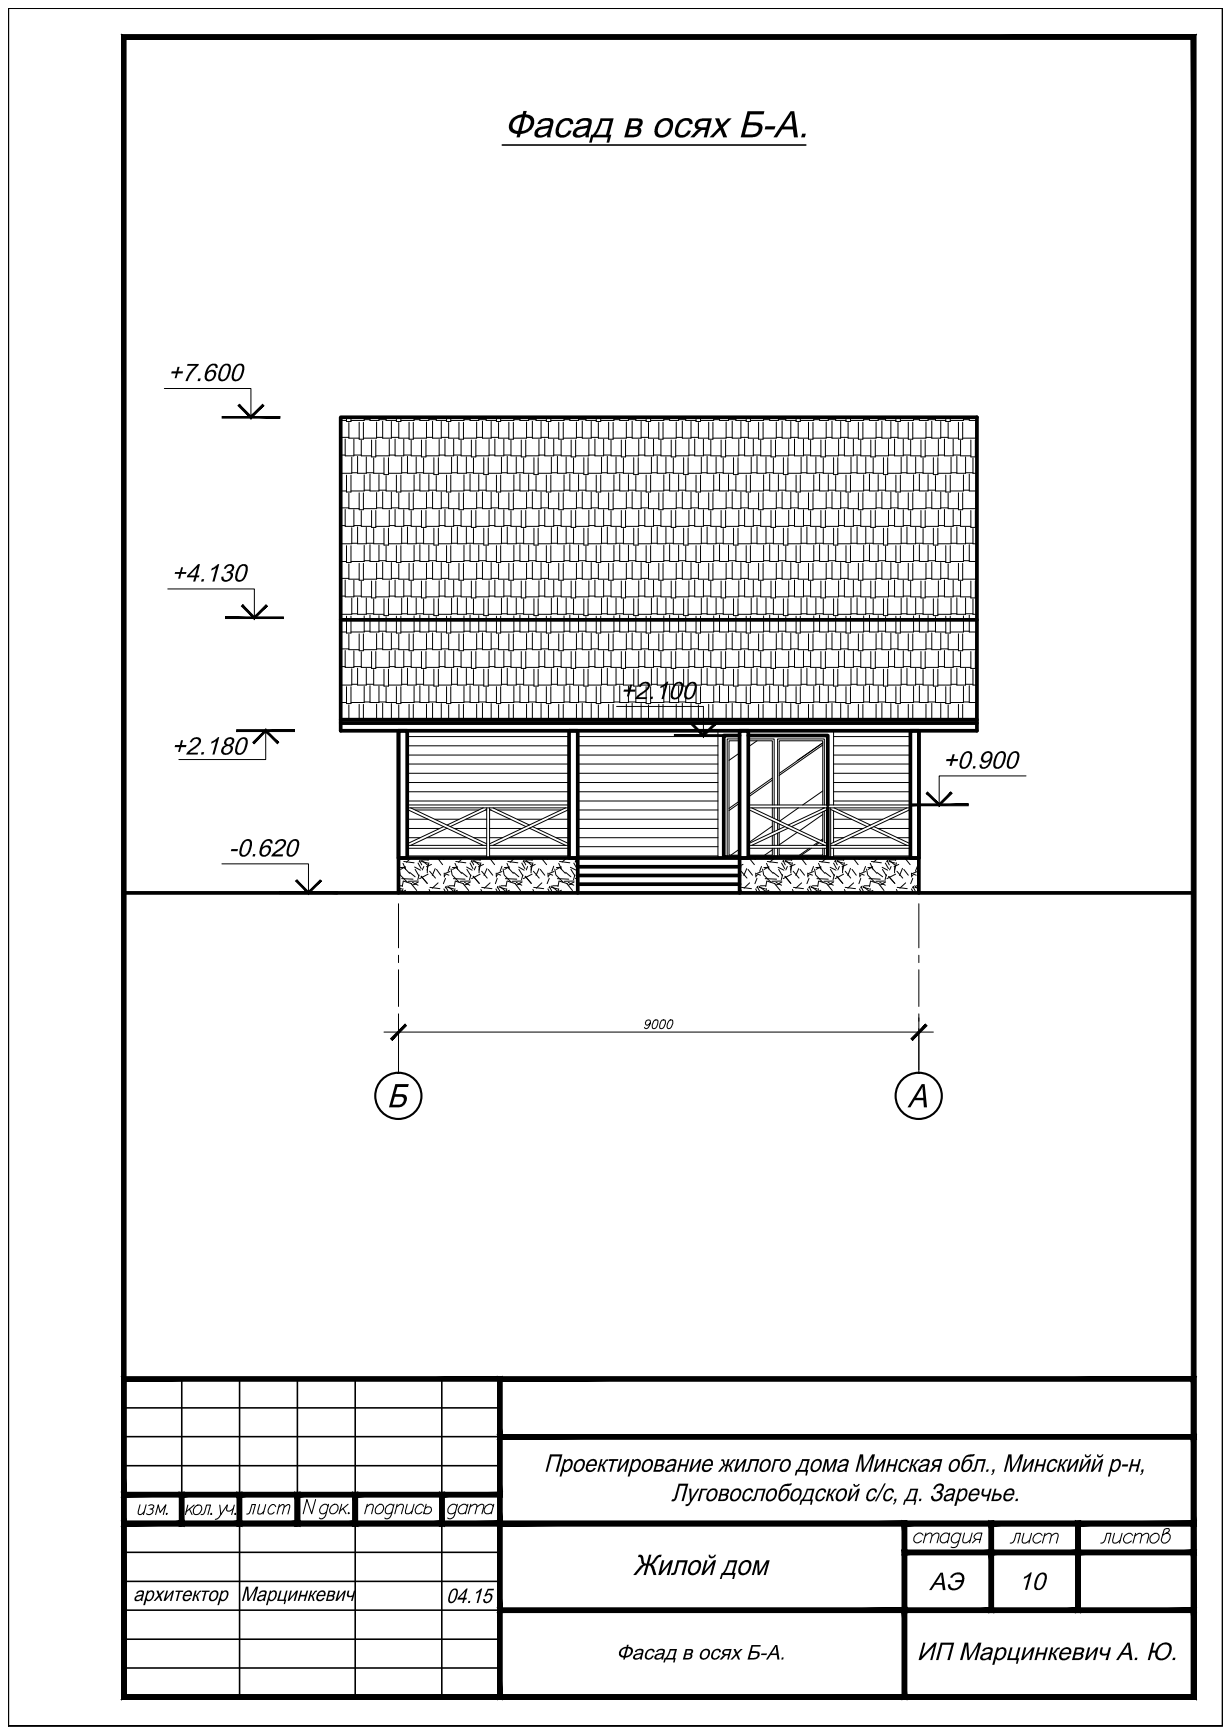
[picture p348: page 1]
