peter-hanzo/KD/Что бывает/Чертежи/Пример архитектурного проекта/лист 11.pdf

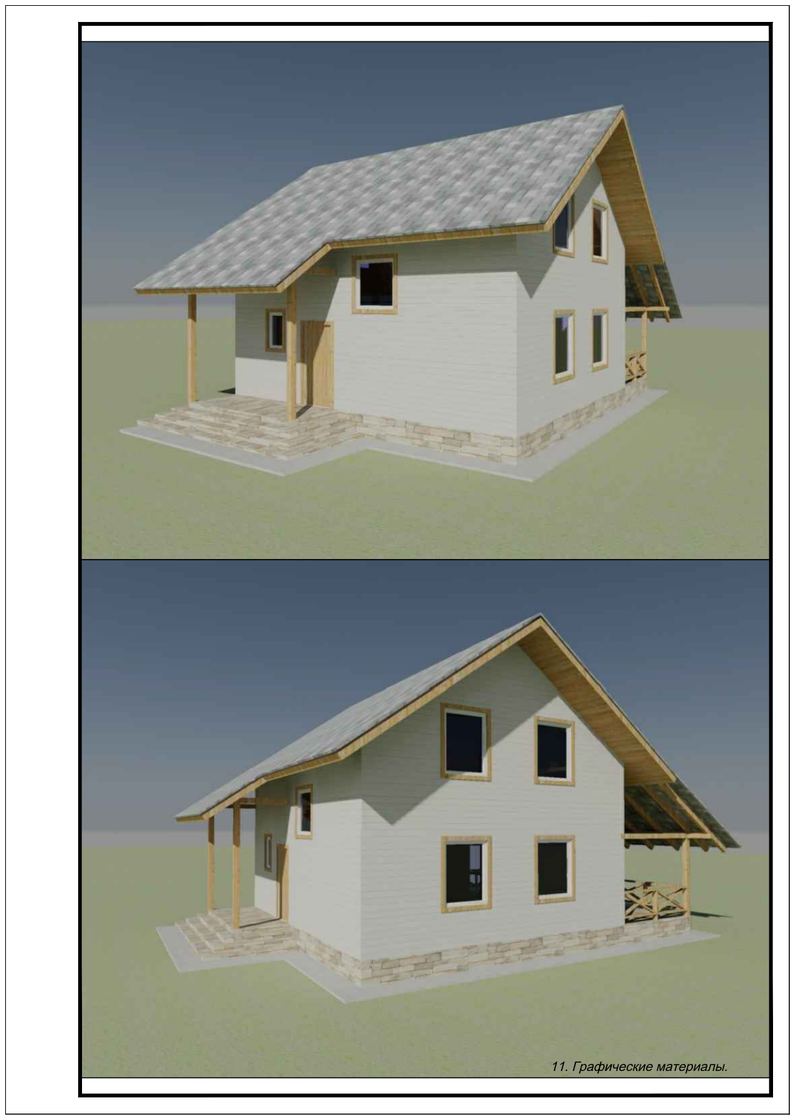
[picture p349: page 1]
