peter-hanzo/KD/Что бывает/Чертежи/Пример архитектурного проекта/лист 12.pdf

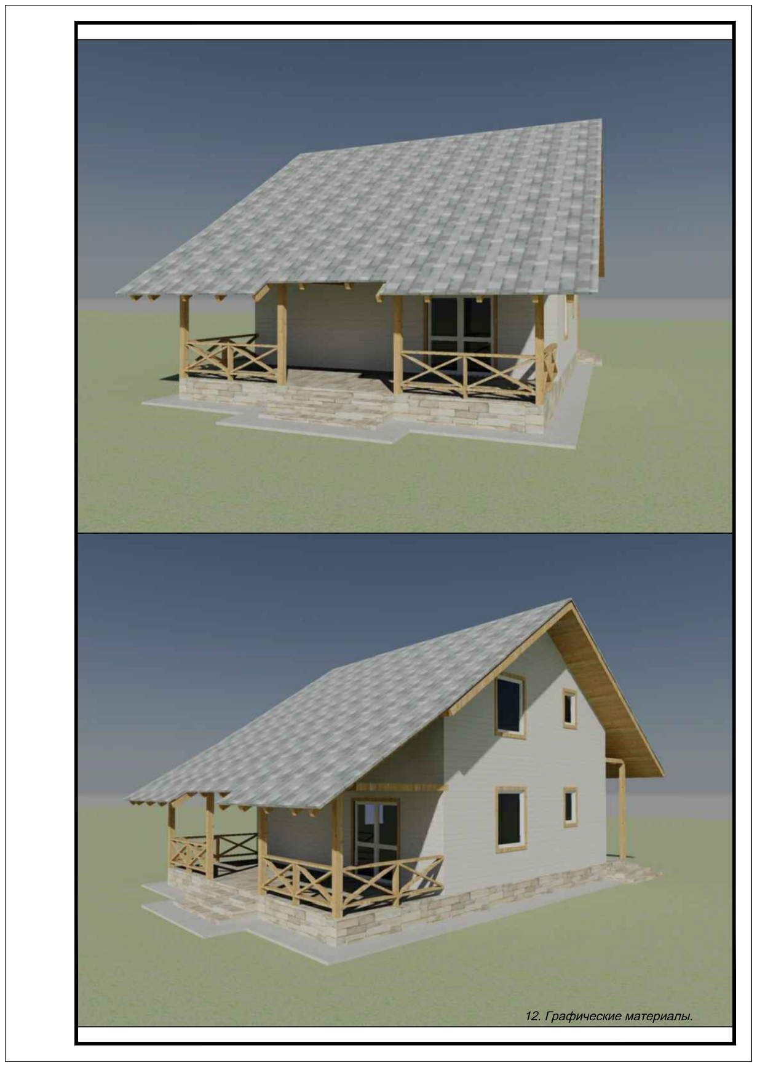
[picture p350: page 1]
