peter-hanzo/KD/Что бывает/Чертежи/Пример архитектурного проекта/лист 2.pdf

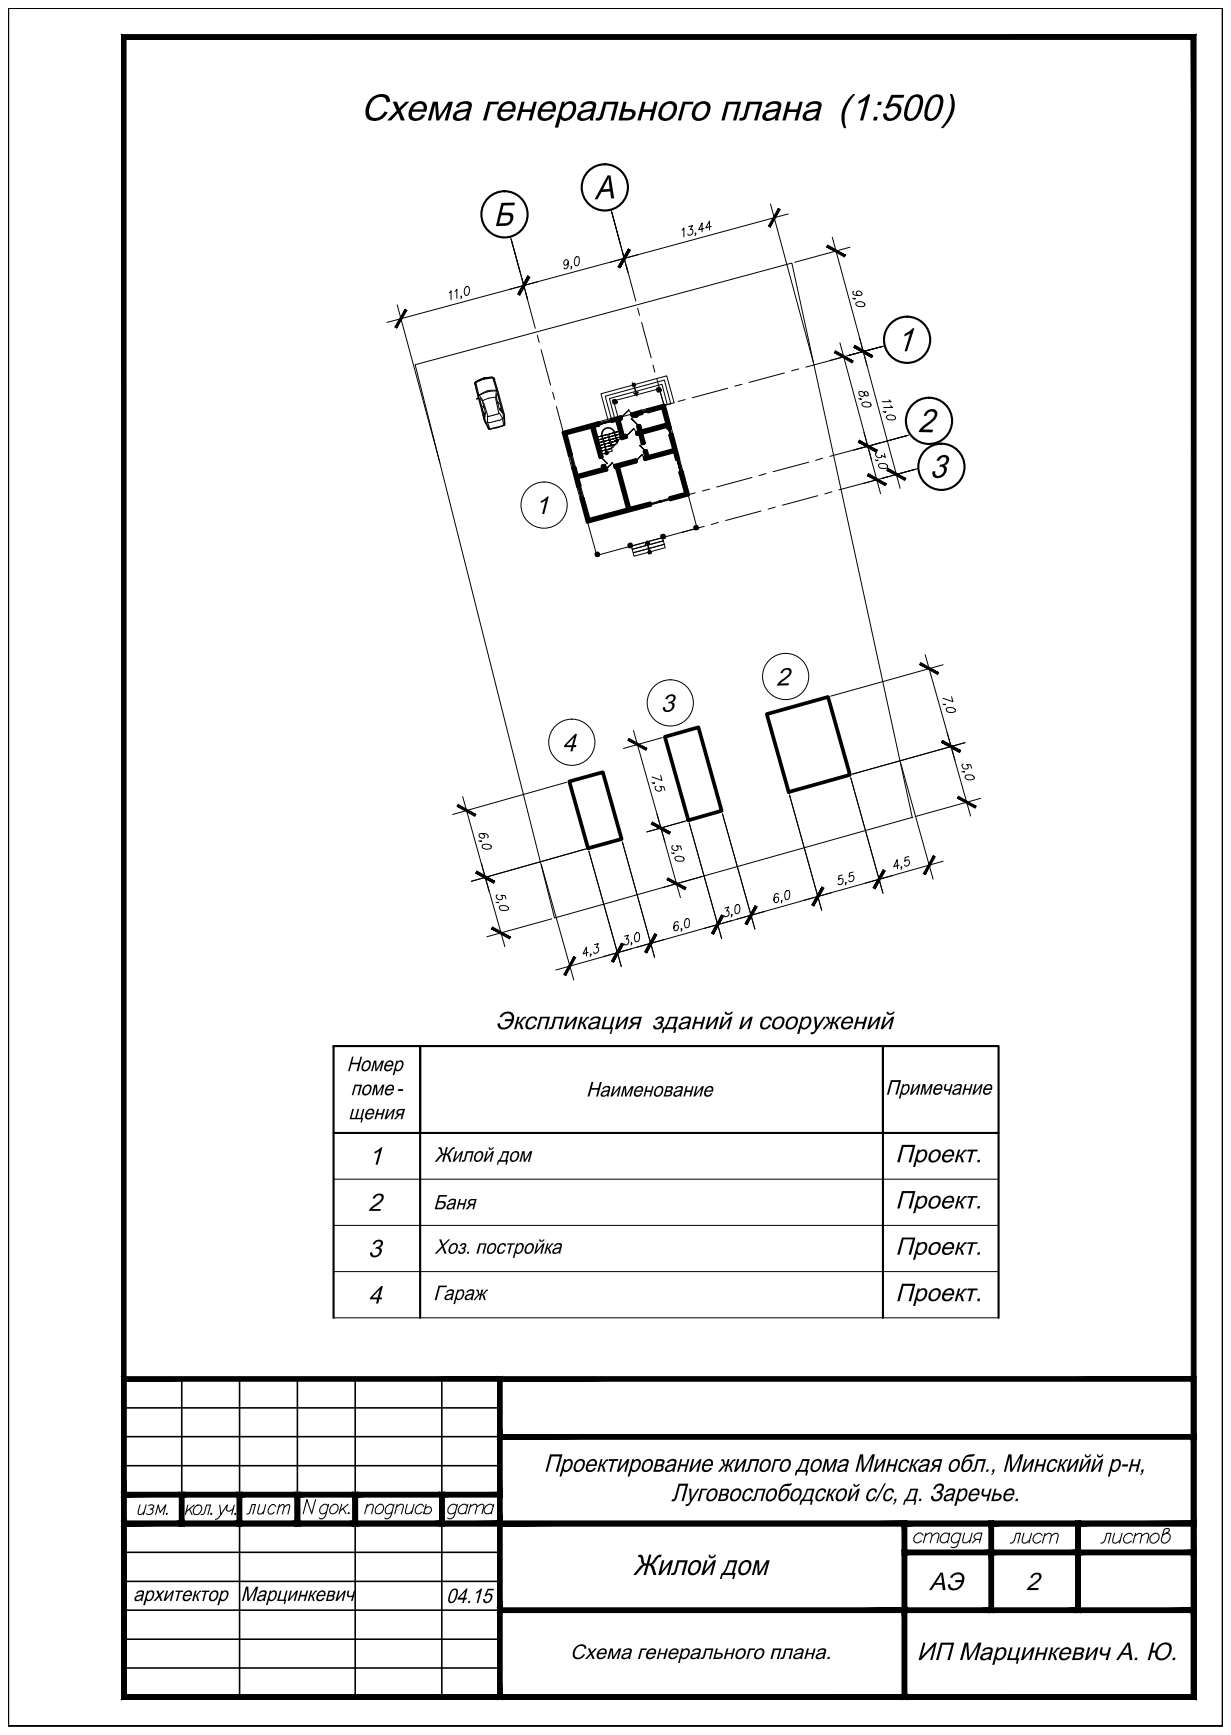
[picture p351: page 1]
