peter-hanzo/KD/Что бывает/Чертежи/Пример архитектурного проекта/лист 3.pdf

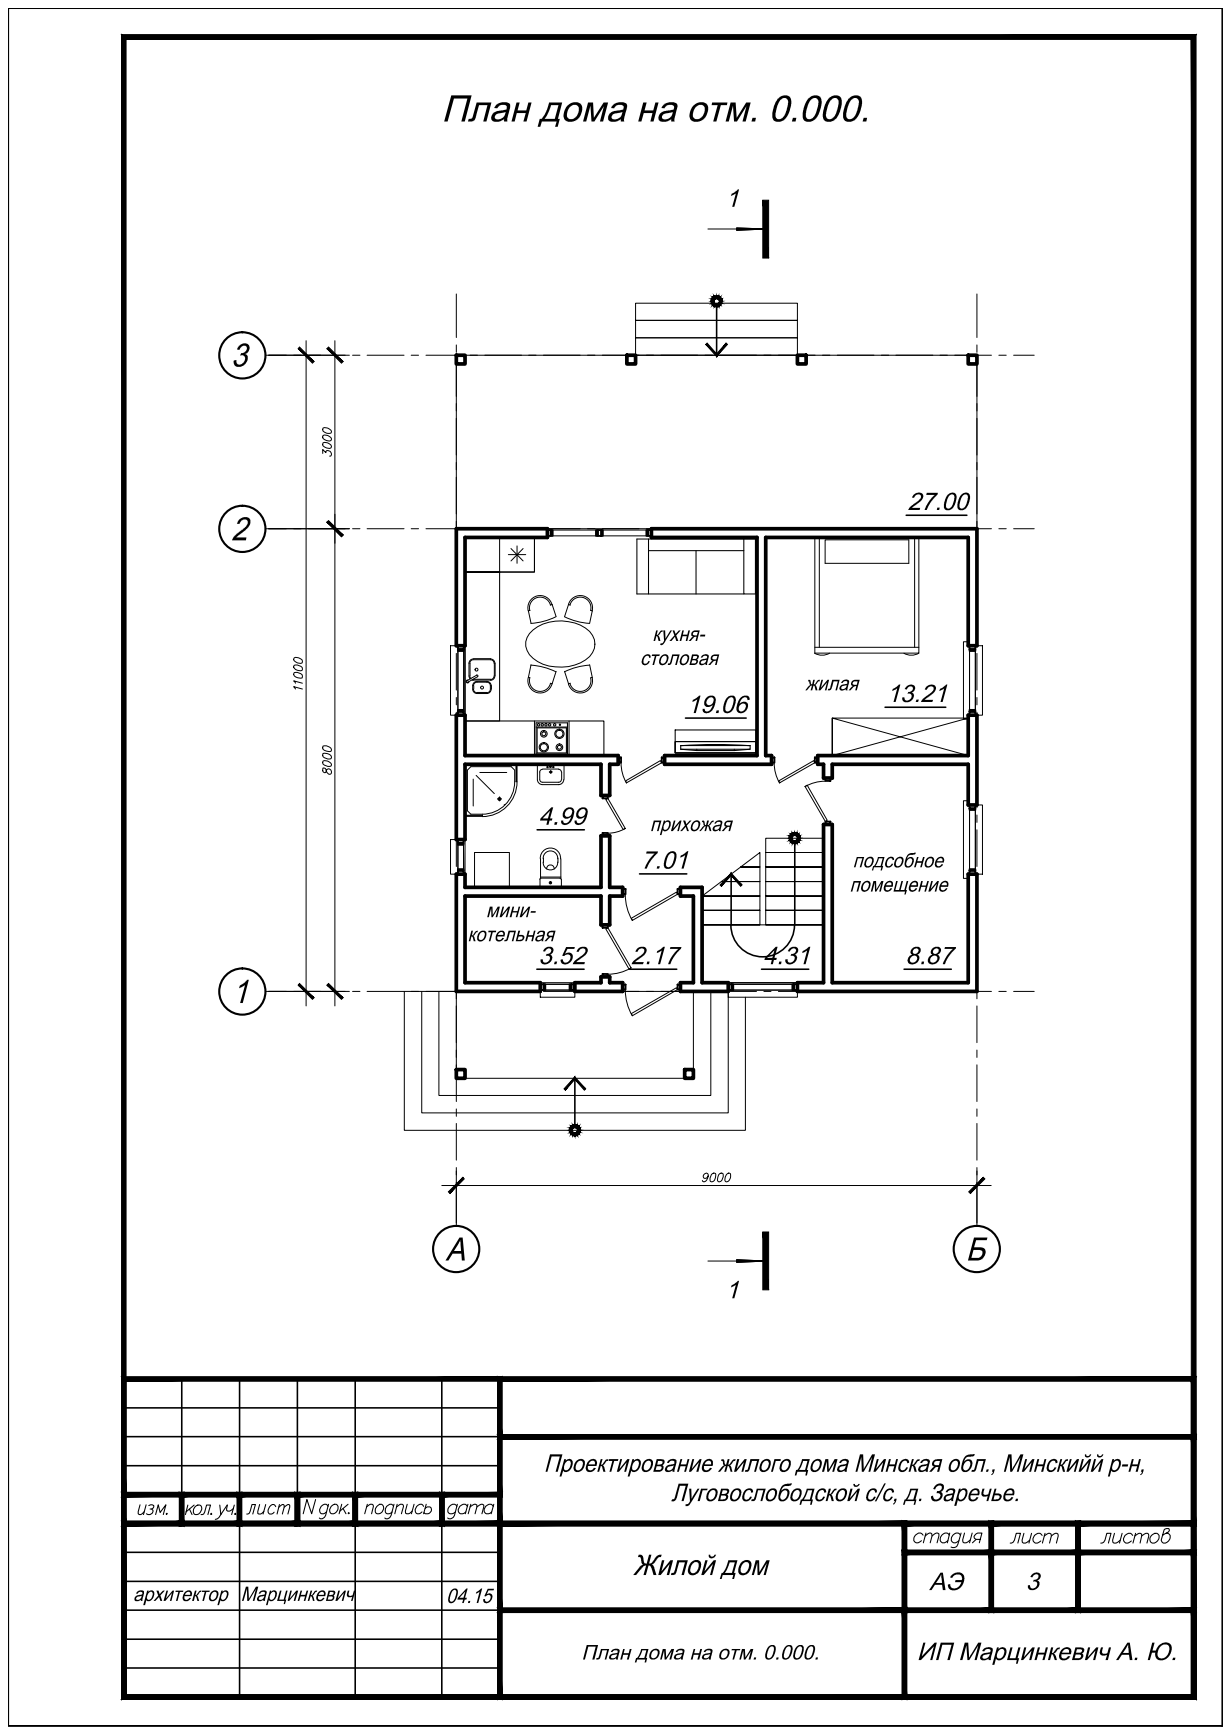
[picture p352: page 1]
