peter-hanzo/KD/Что бывает/Чертежи/Пример архитектурного проекта/лист 4.pdf

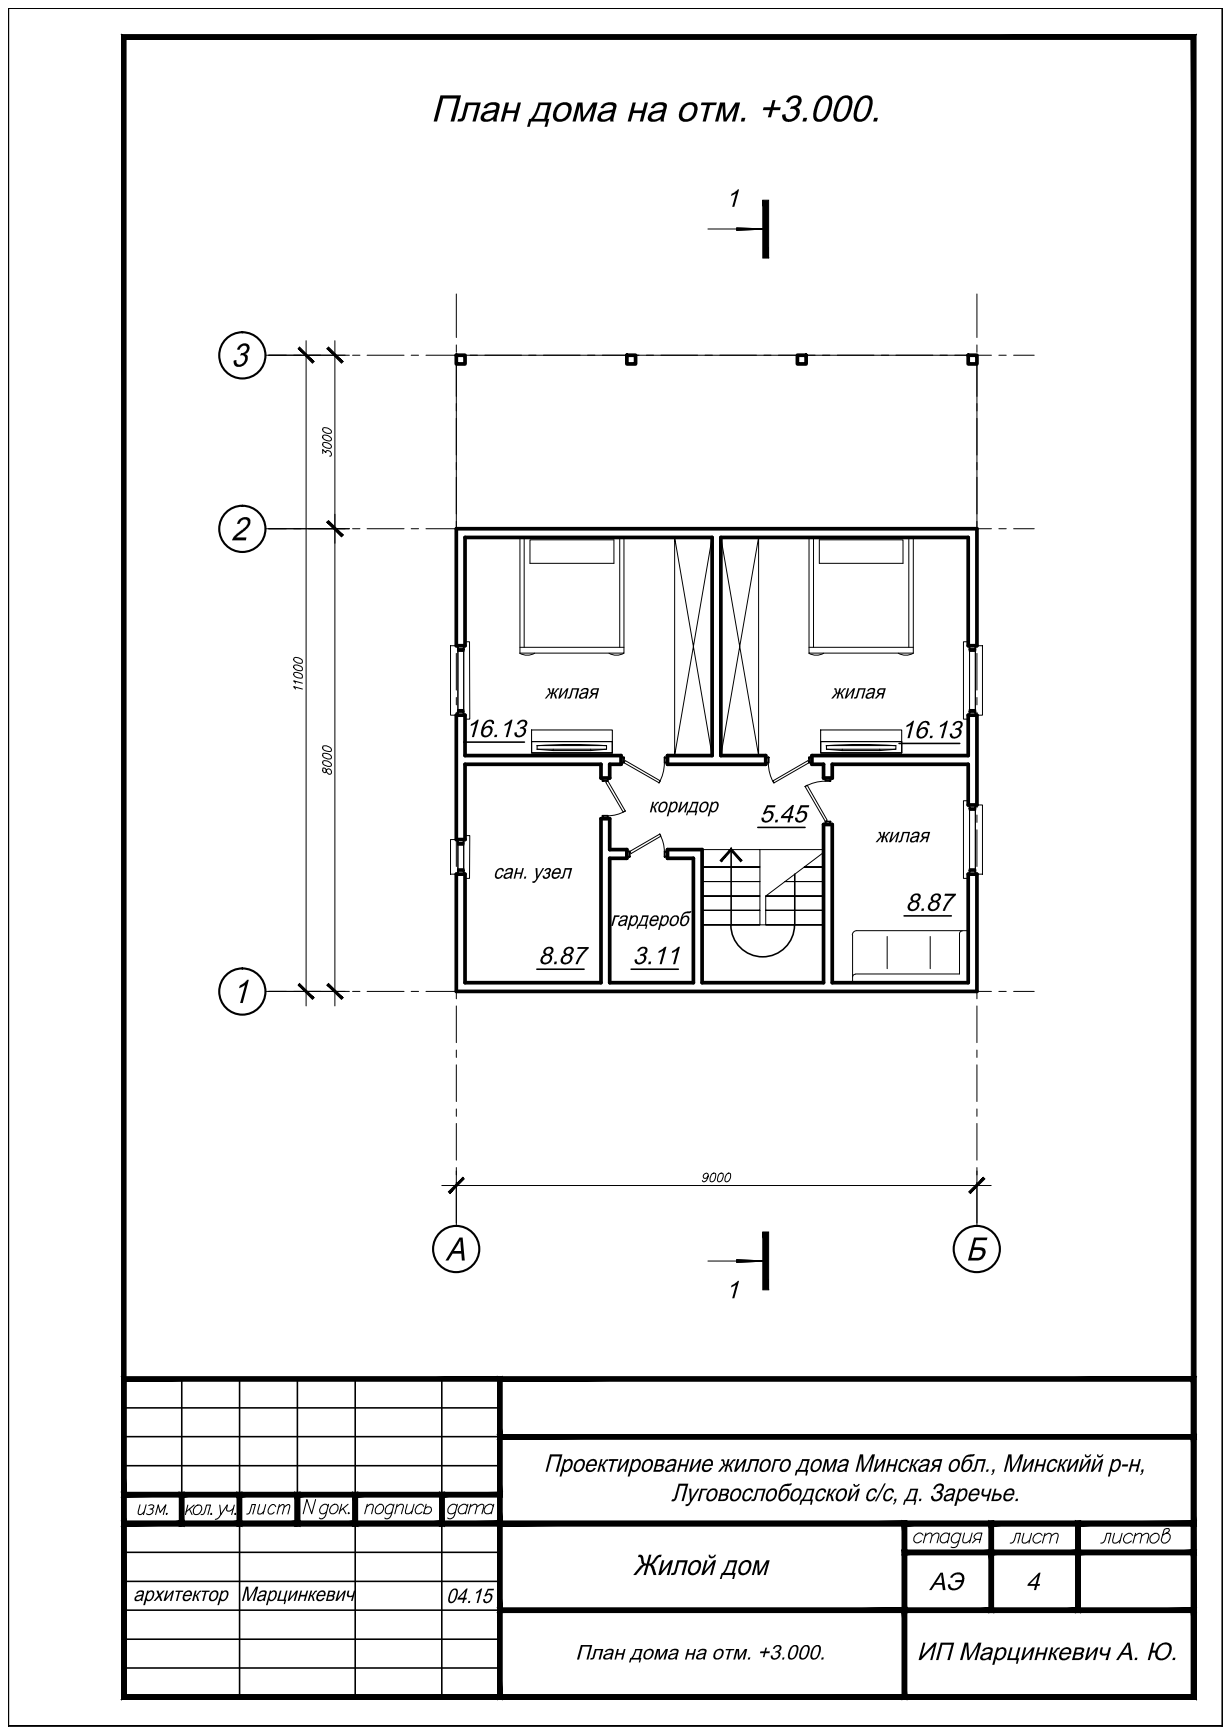
[picture p353: page 1]
