peter-hanzo/KD/Что бывает/Чертежи/Пример архитектурного проекта/лист 5.pdf

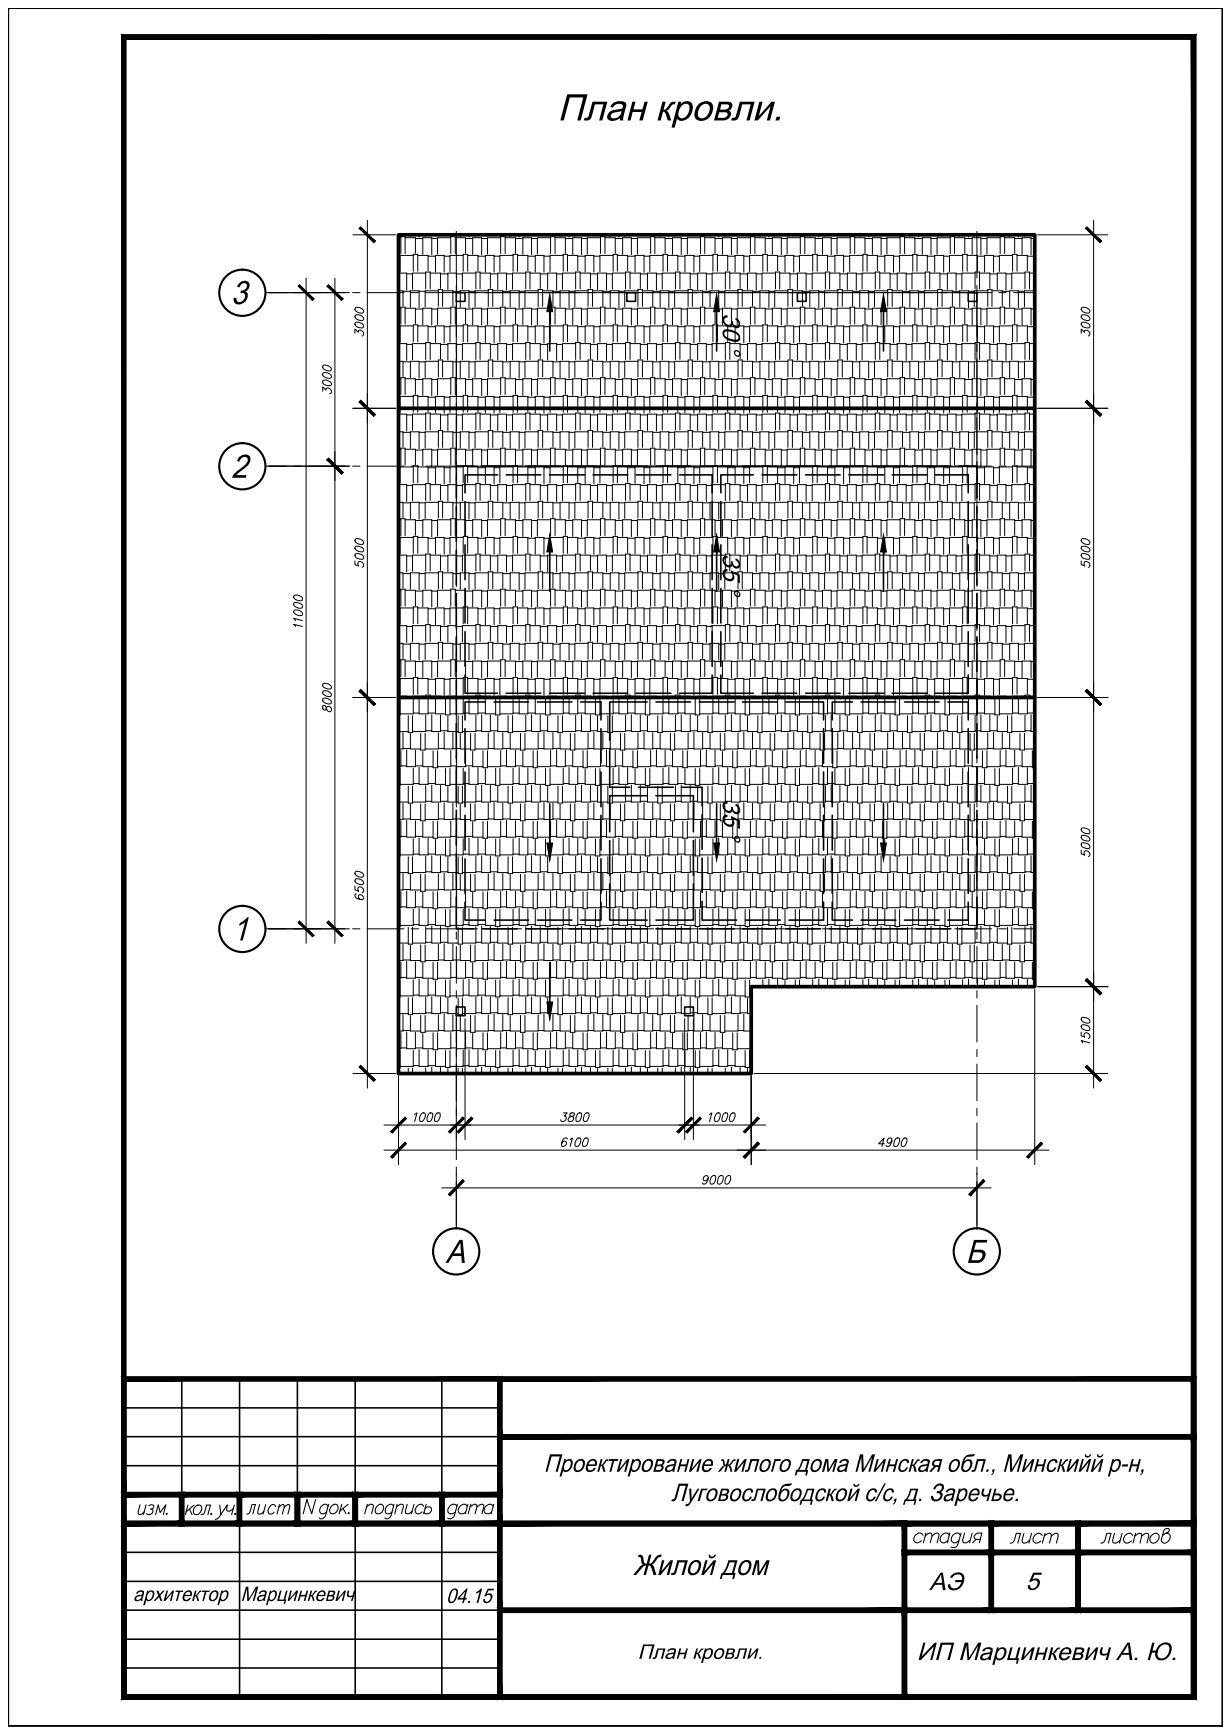
[picture p354: page 1]
