peter-hanzo/KD/Что бывает/Чертежи/Пример архитектурного проекта/лист 6.pdf

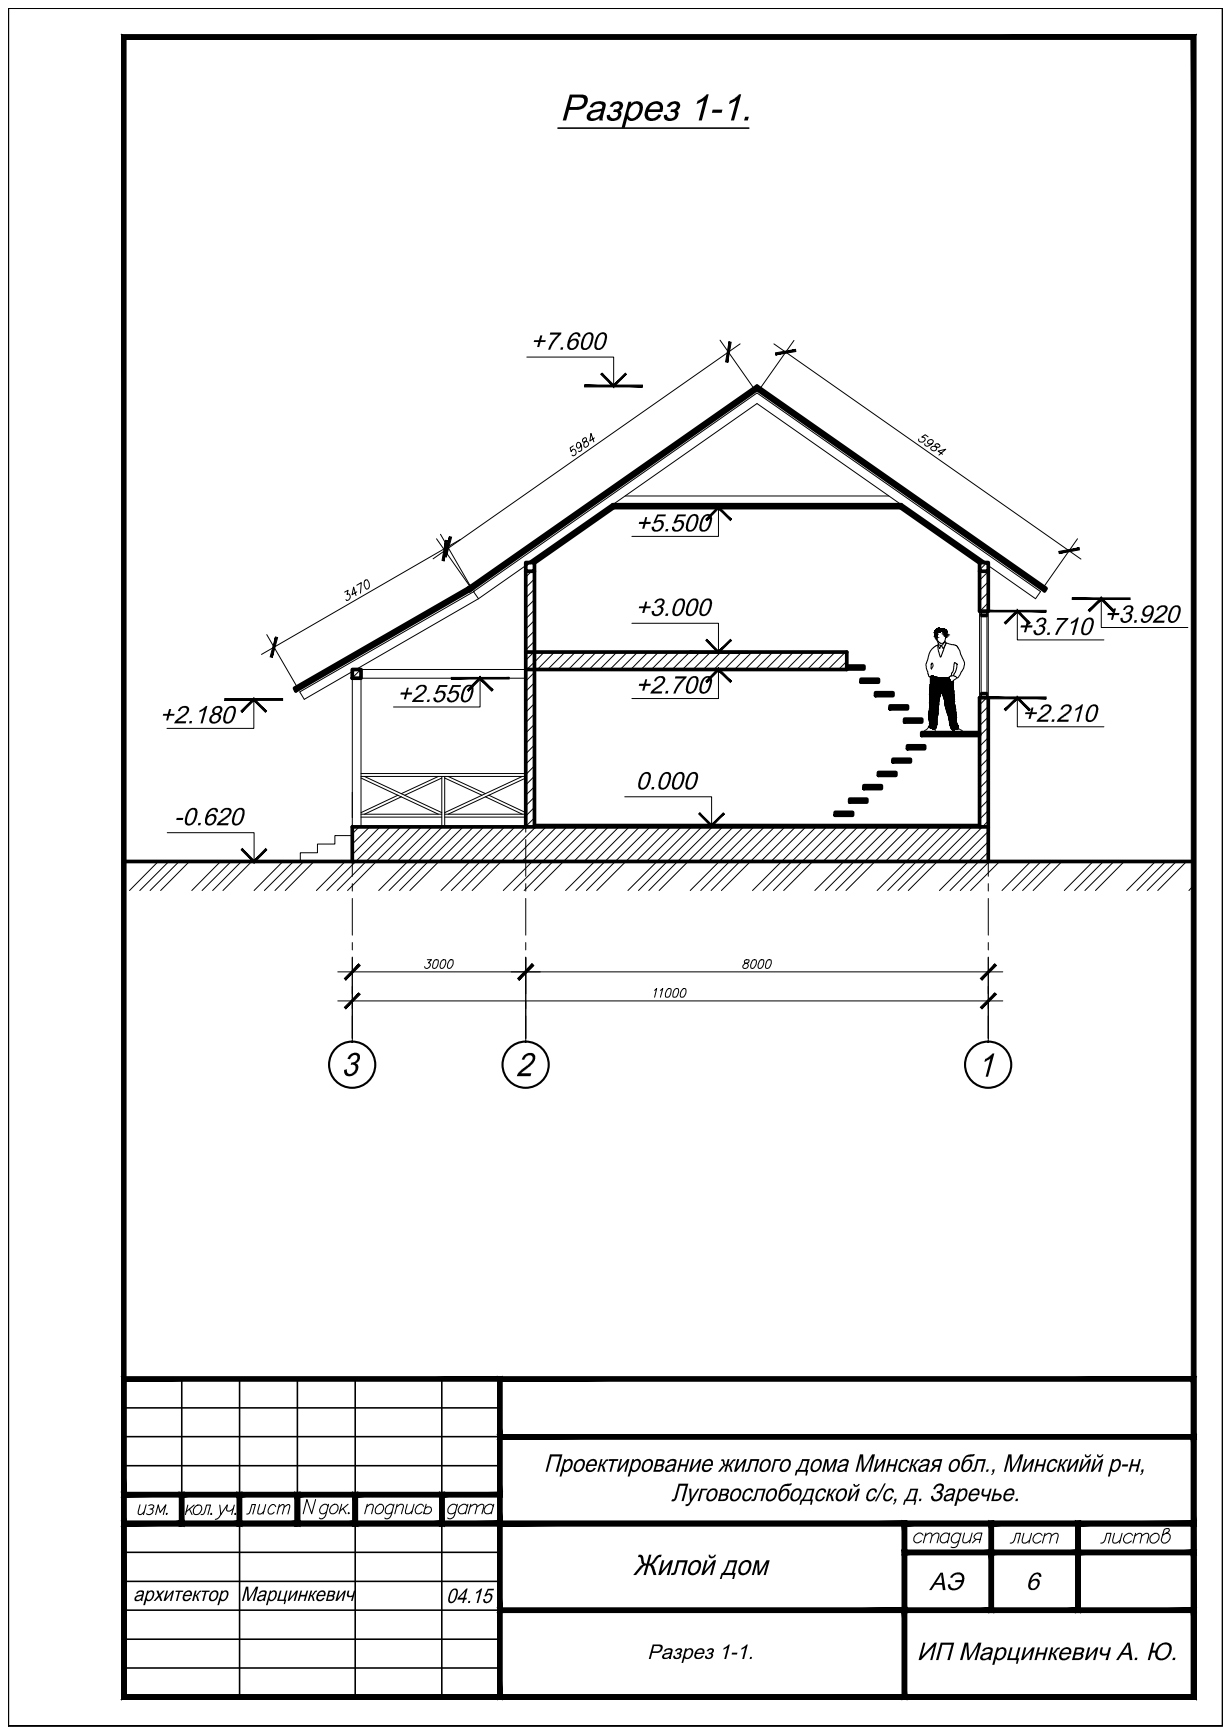
[picture p355: page 1]
