peter-hanzo/KD/Что бывает/Чертежи/Пример архитектурного проекта/лист 7.pdf

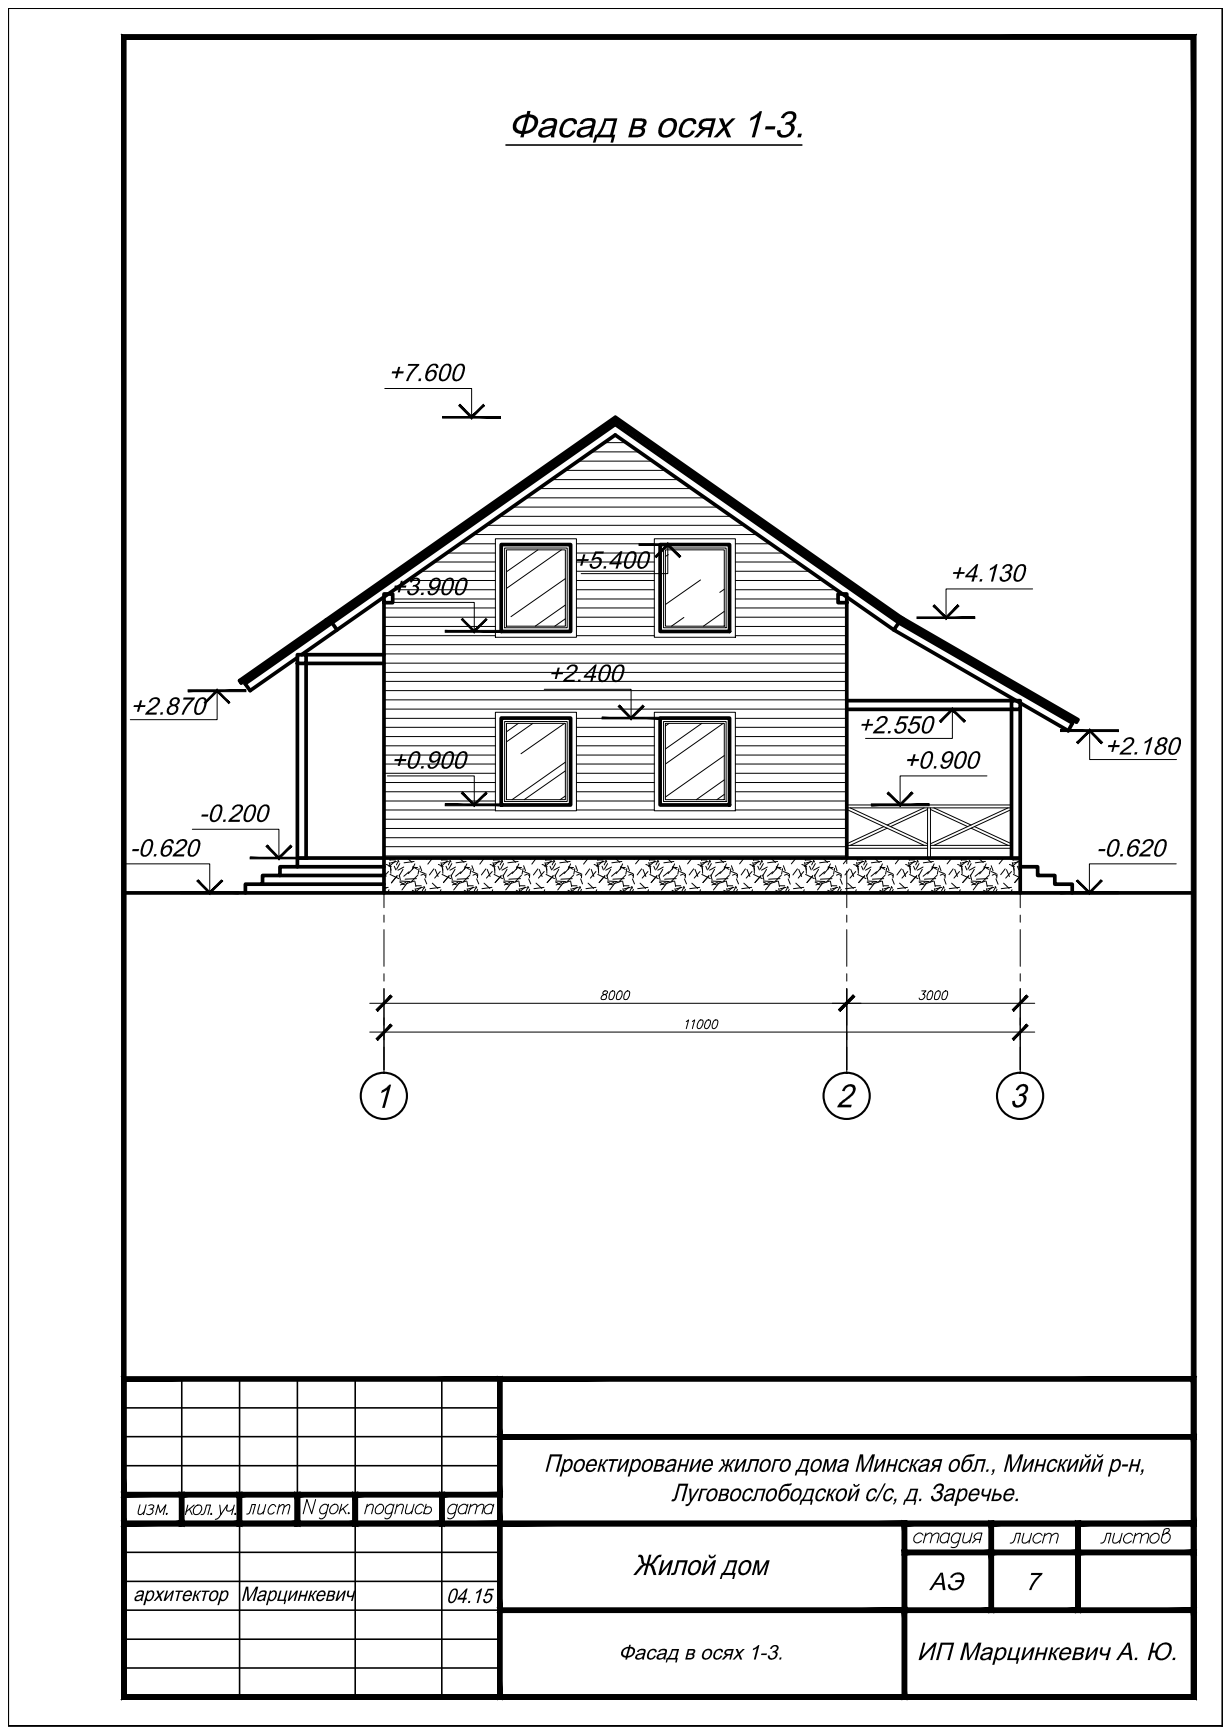
[picture p356: page 1]
