peter-hanzo/KD/Что бывает/Чертежи/Пример архитектурного проекта/лист 8.pdf

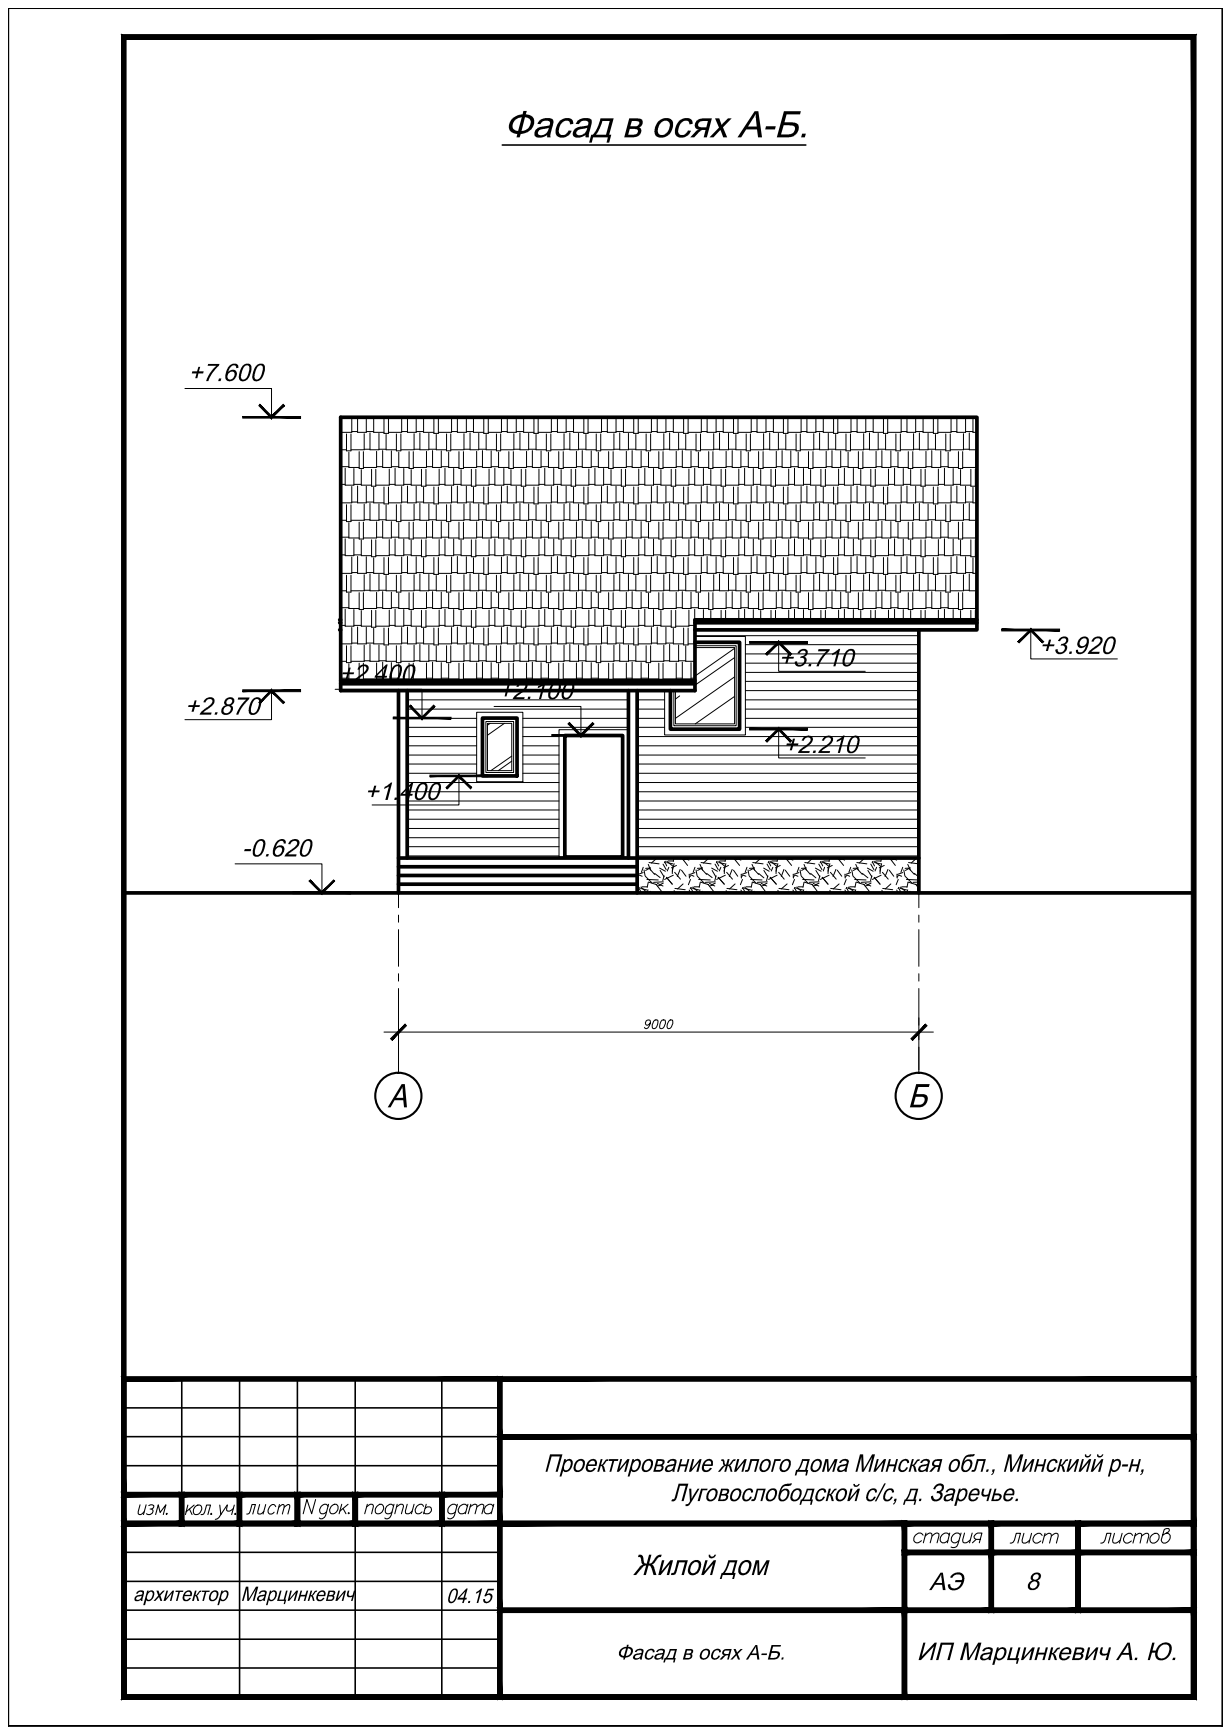
[picture p357: page 1]
