peter-hanzo/KD/Что бывает/Чертежи/Пример архитектурного проекта/лист 9.pdf

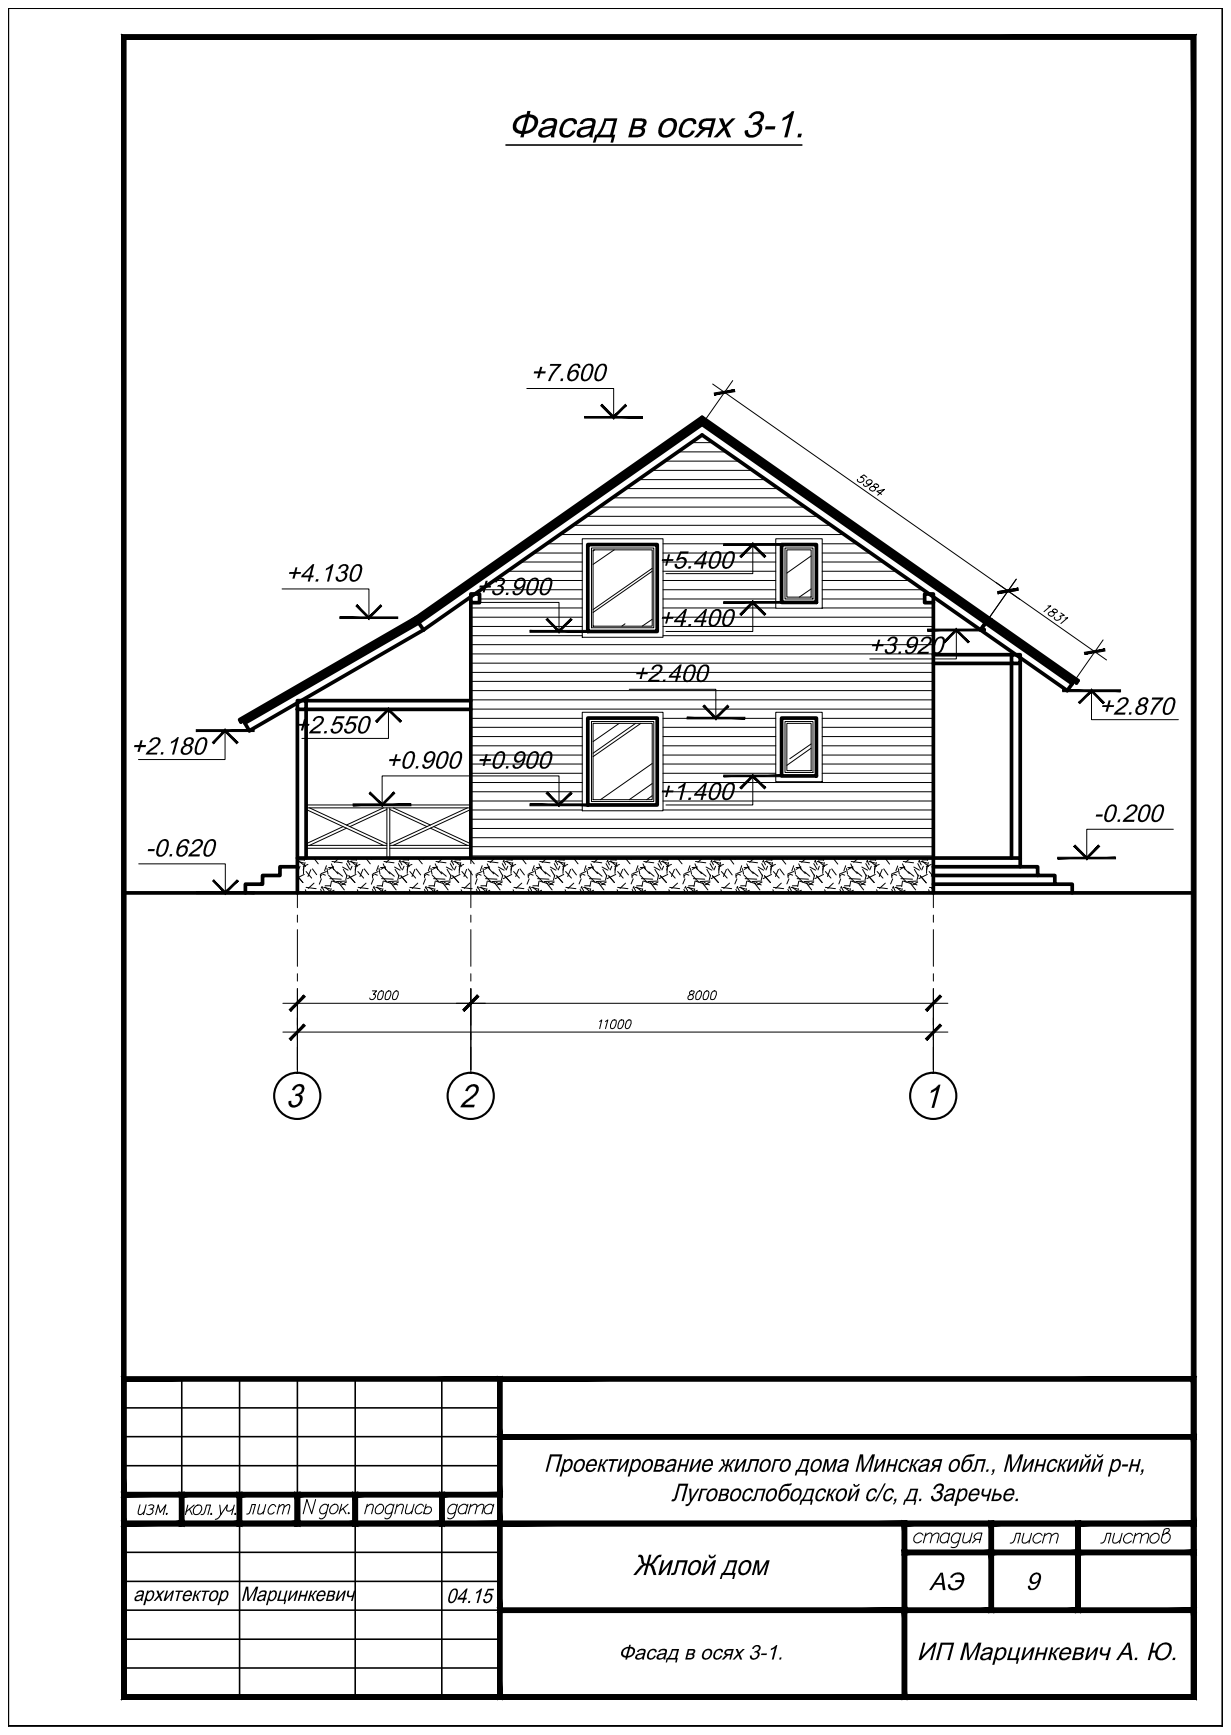
[picture p358: page 1]
