peter-hanzo/KD/Что бывает/Чертежи/Пример архитектурного проекта/план 1-го этажа с размерами.pdf

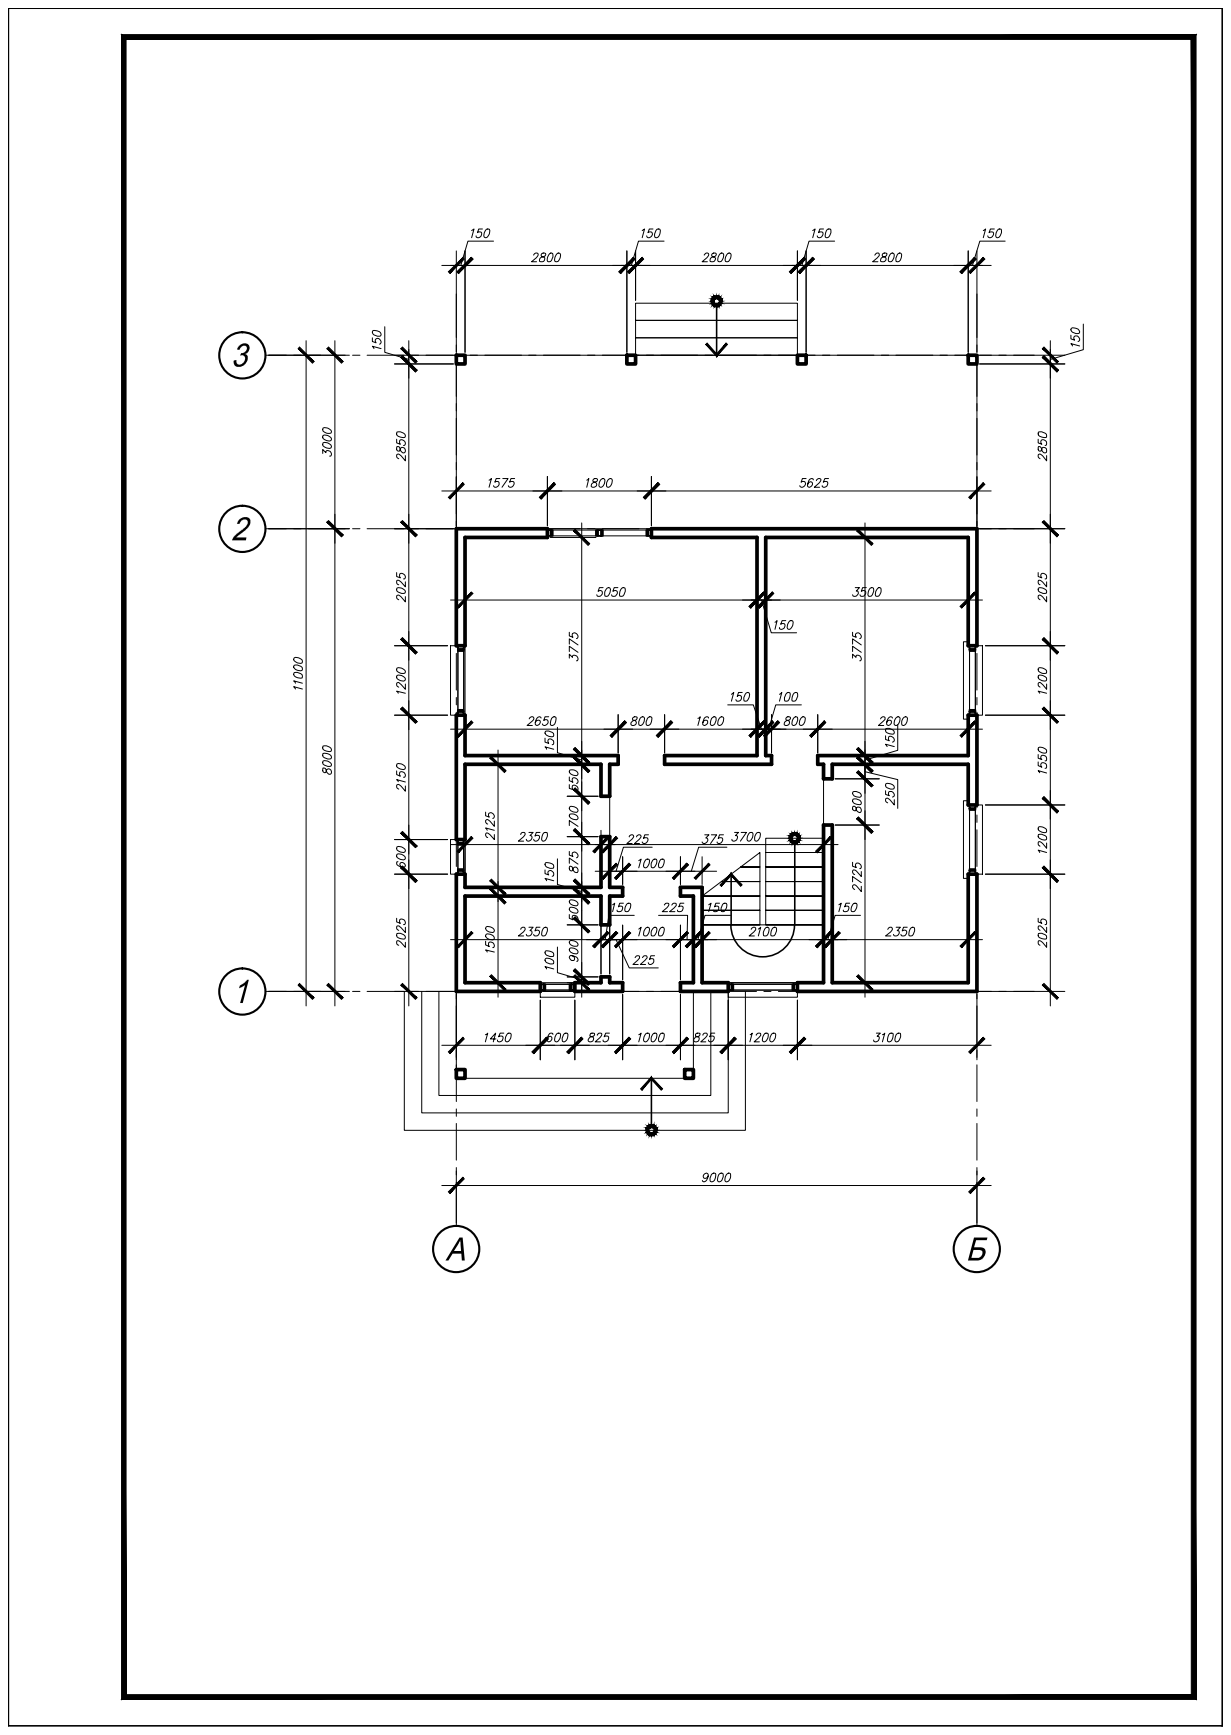
[picture p359: page 1]
