peter-hanzo/KD/Что бывает/Чертежи/Пример архитектурного проекта/план мансардного этажа с размерами.pdf

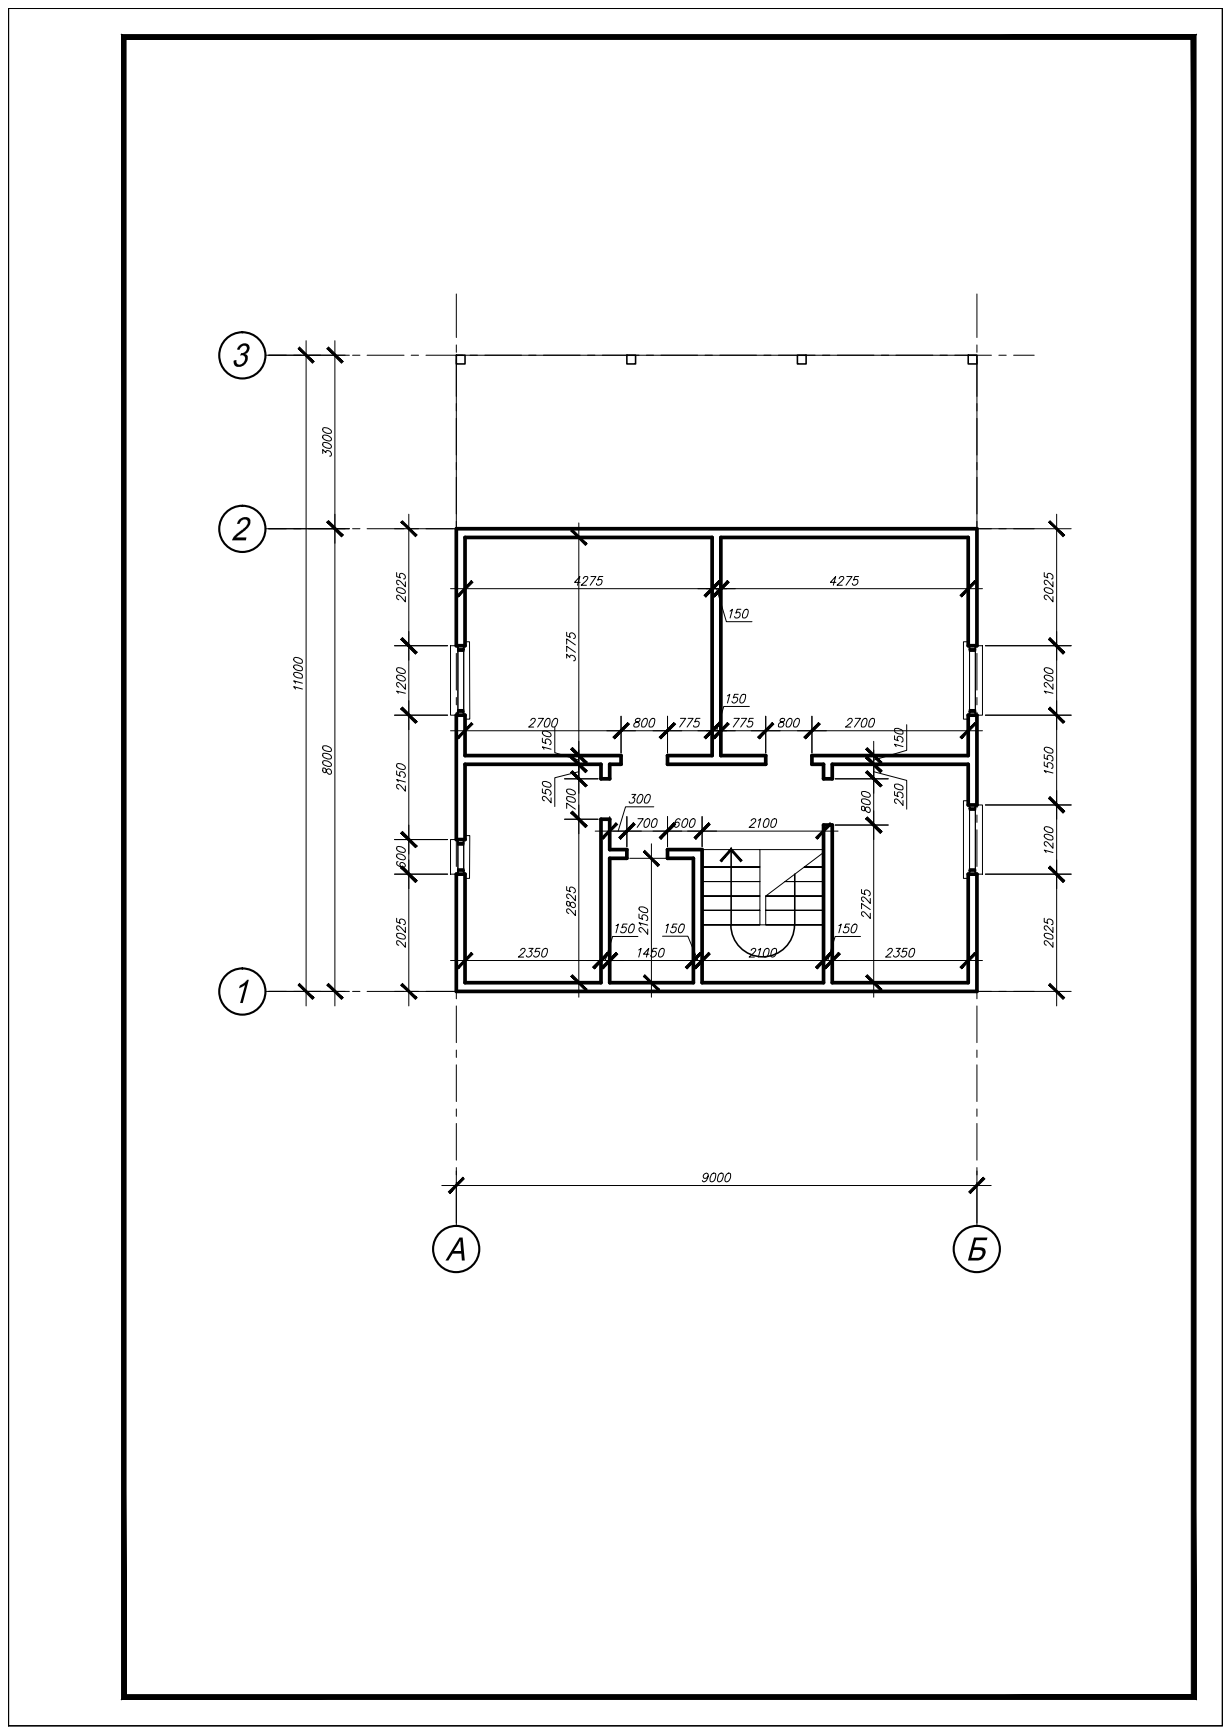
[picture p360: page 1]
