peter-hanzo/KD/Что бывает/Чертежи/Пример архитектурного проекта/Пояснительная записка.pdf

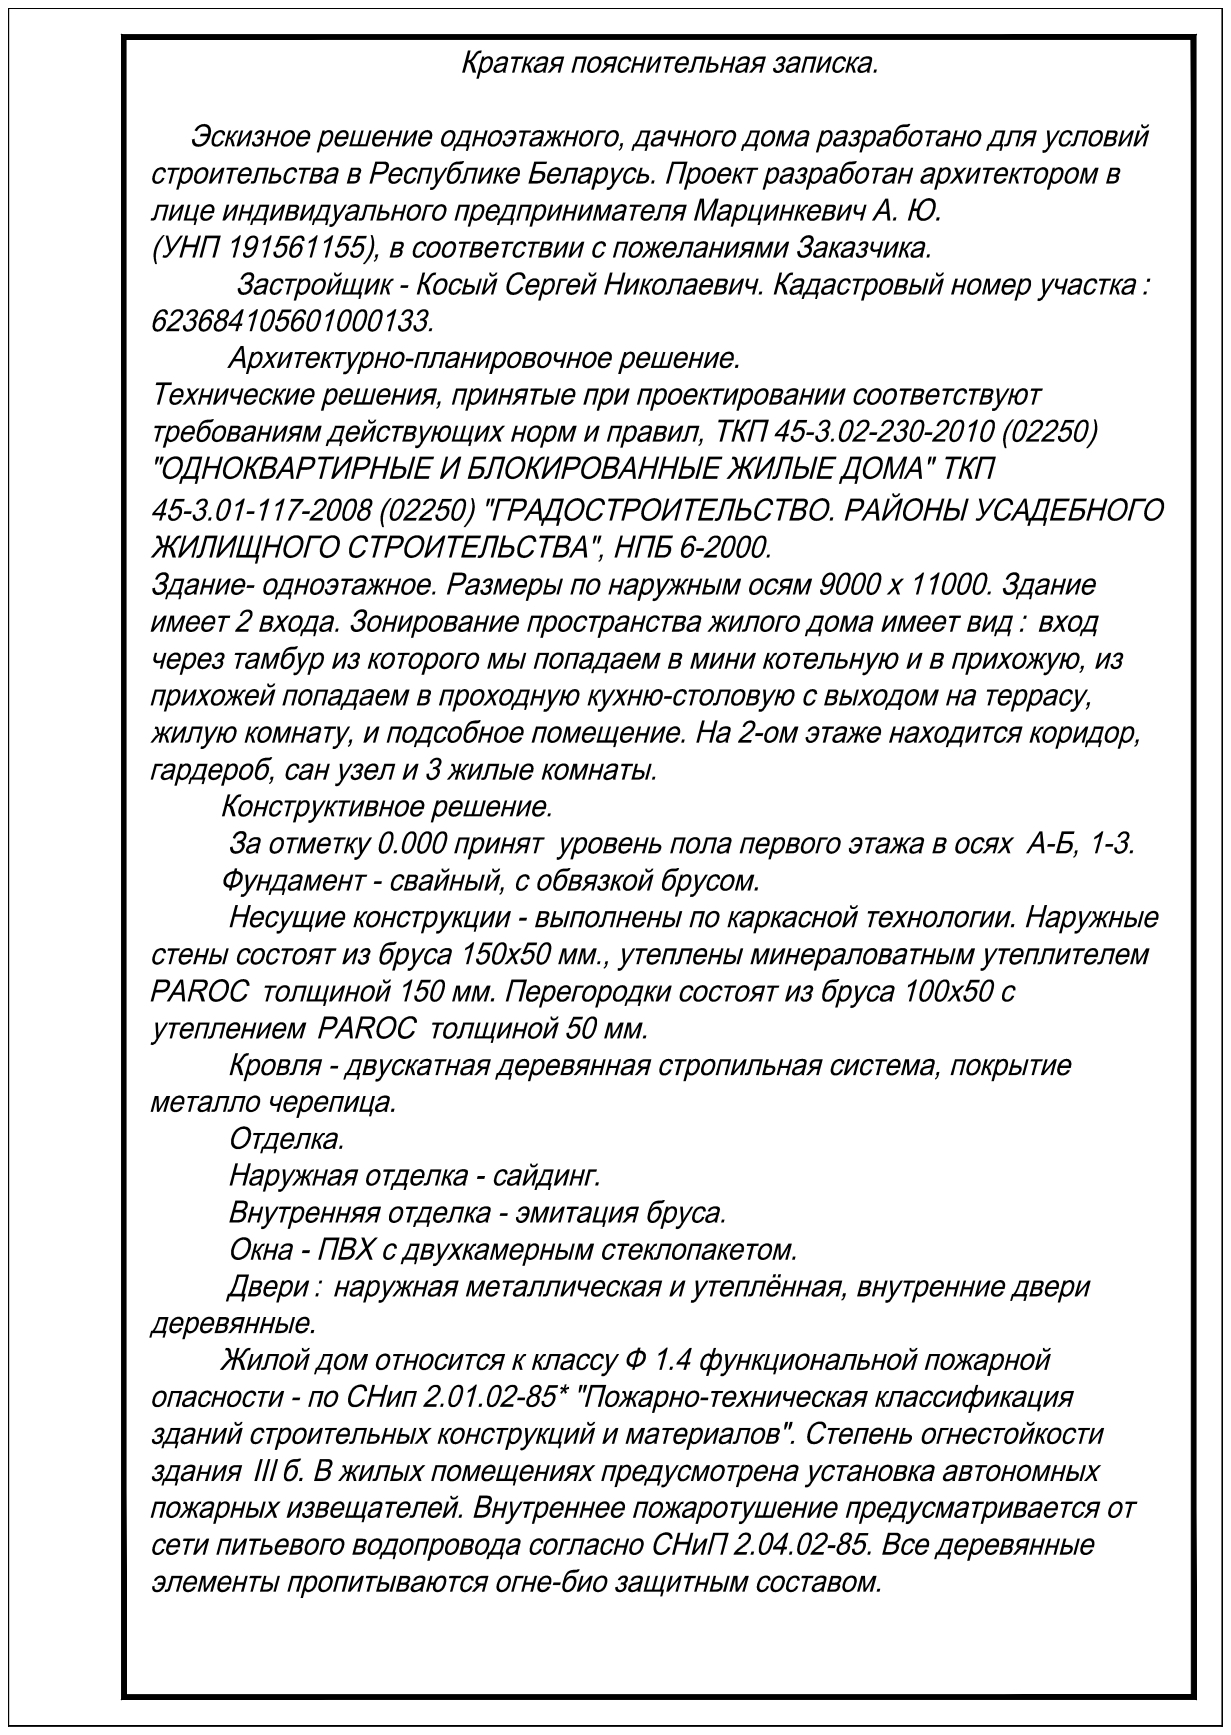
[picture p361: page 1]
