peter-hanzo/KD/Что бывает/Чертежи/Пример архитектурного проекта/Титульный лист.pdf

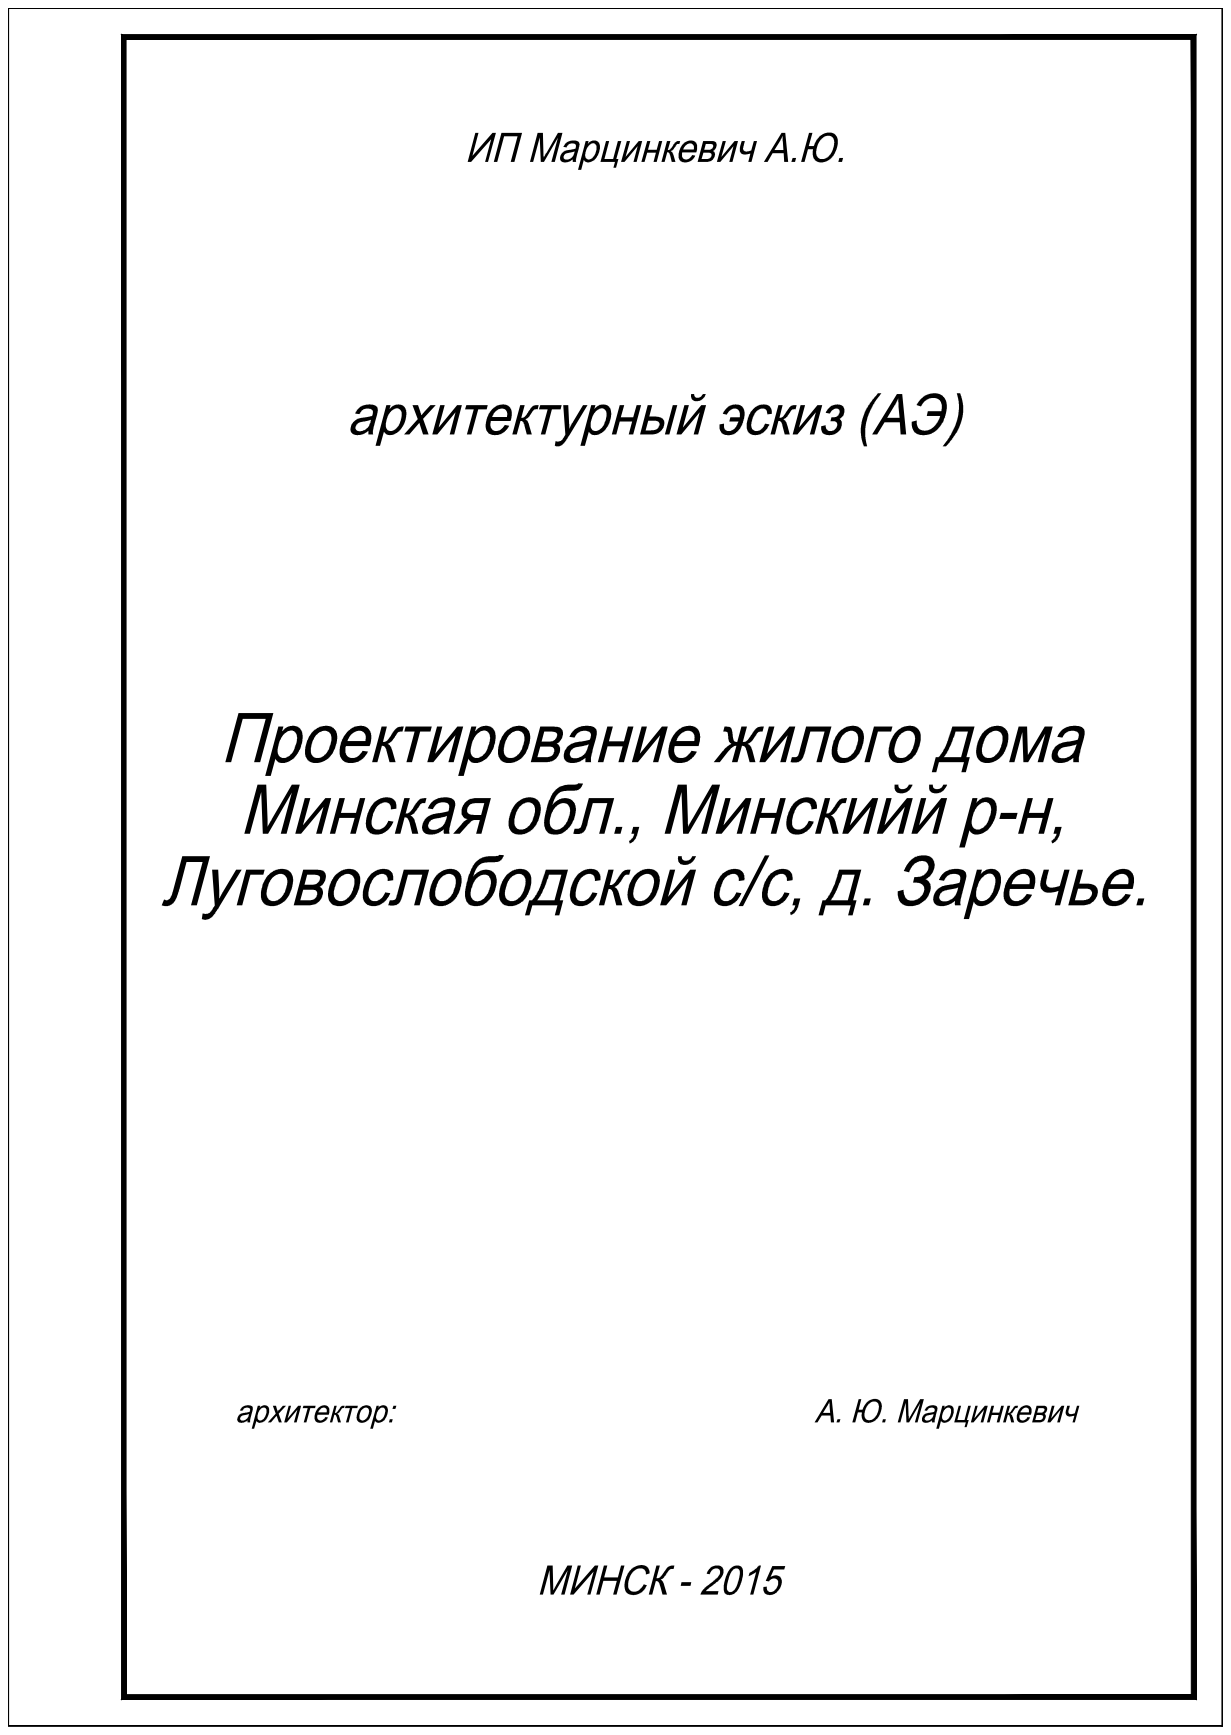
[picture p362: page 1]
