peter-hanzo/KD/Документы/Чертежи/Фундамент/разметка фундамента-3.pdf

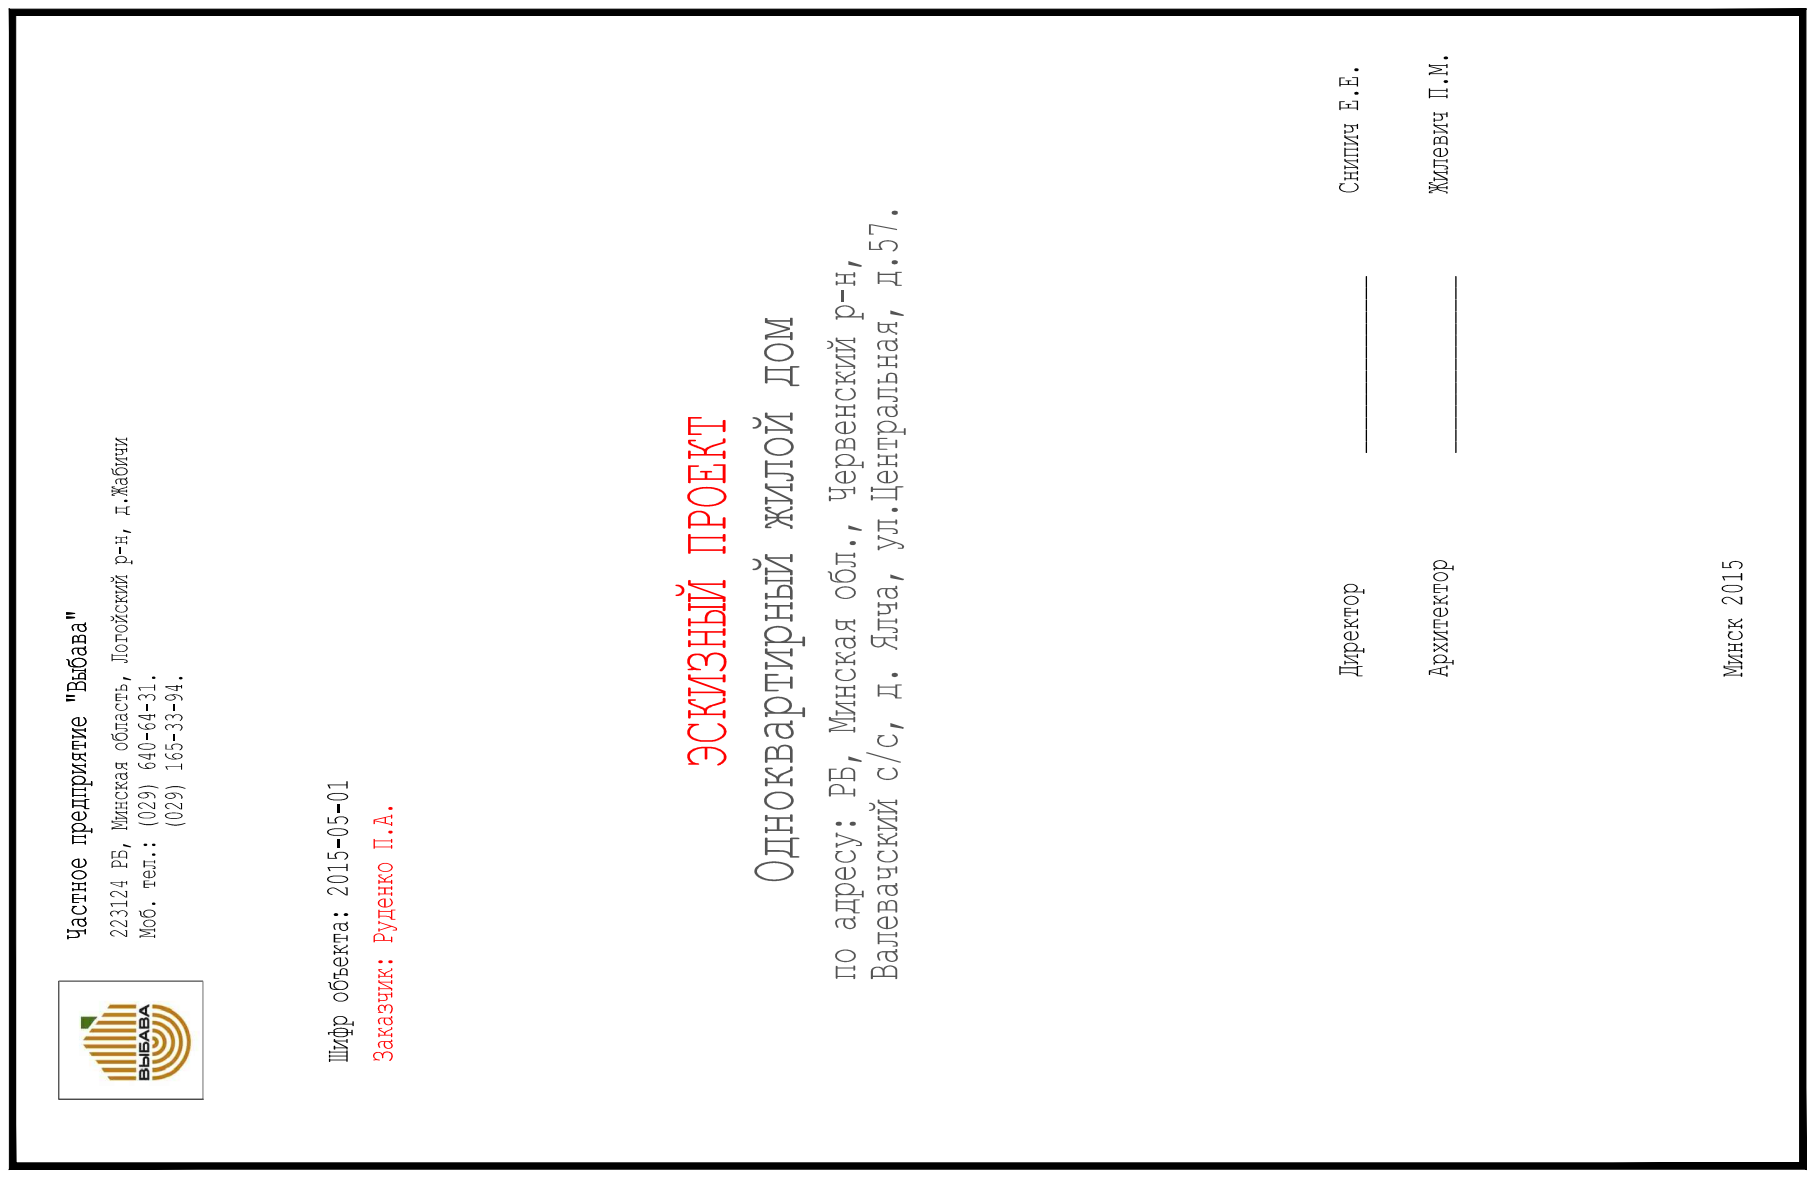
[picture p363: page 1]
