peter-hanzo/KD/Документы/Чертежи/Конструктив/Крепления.pdf

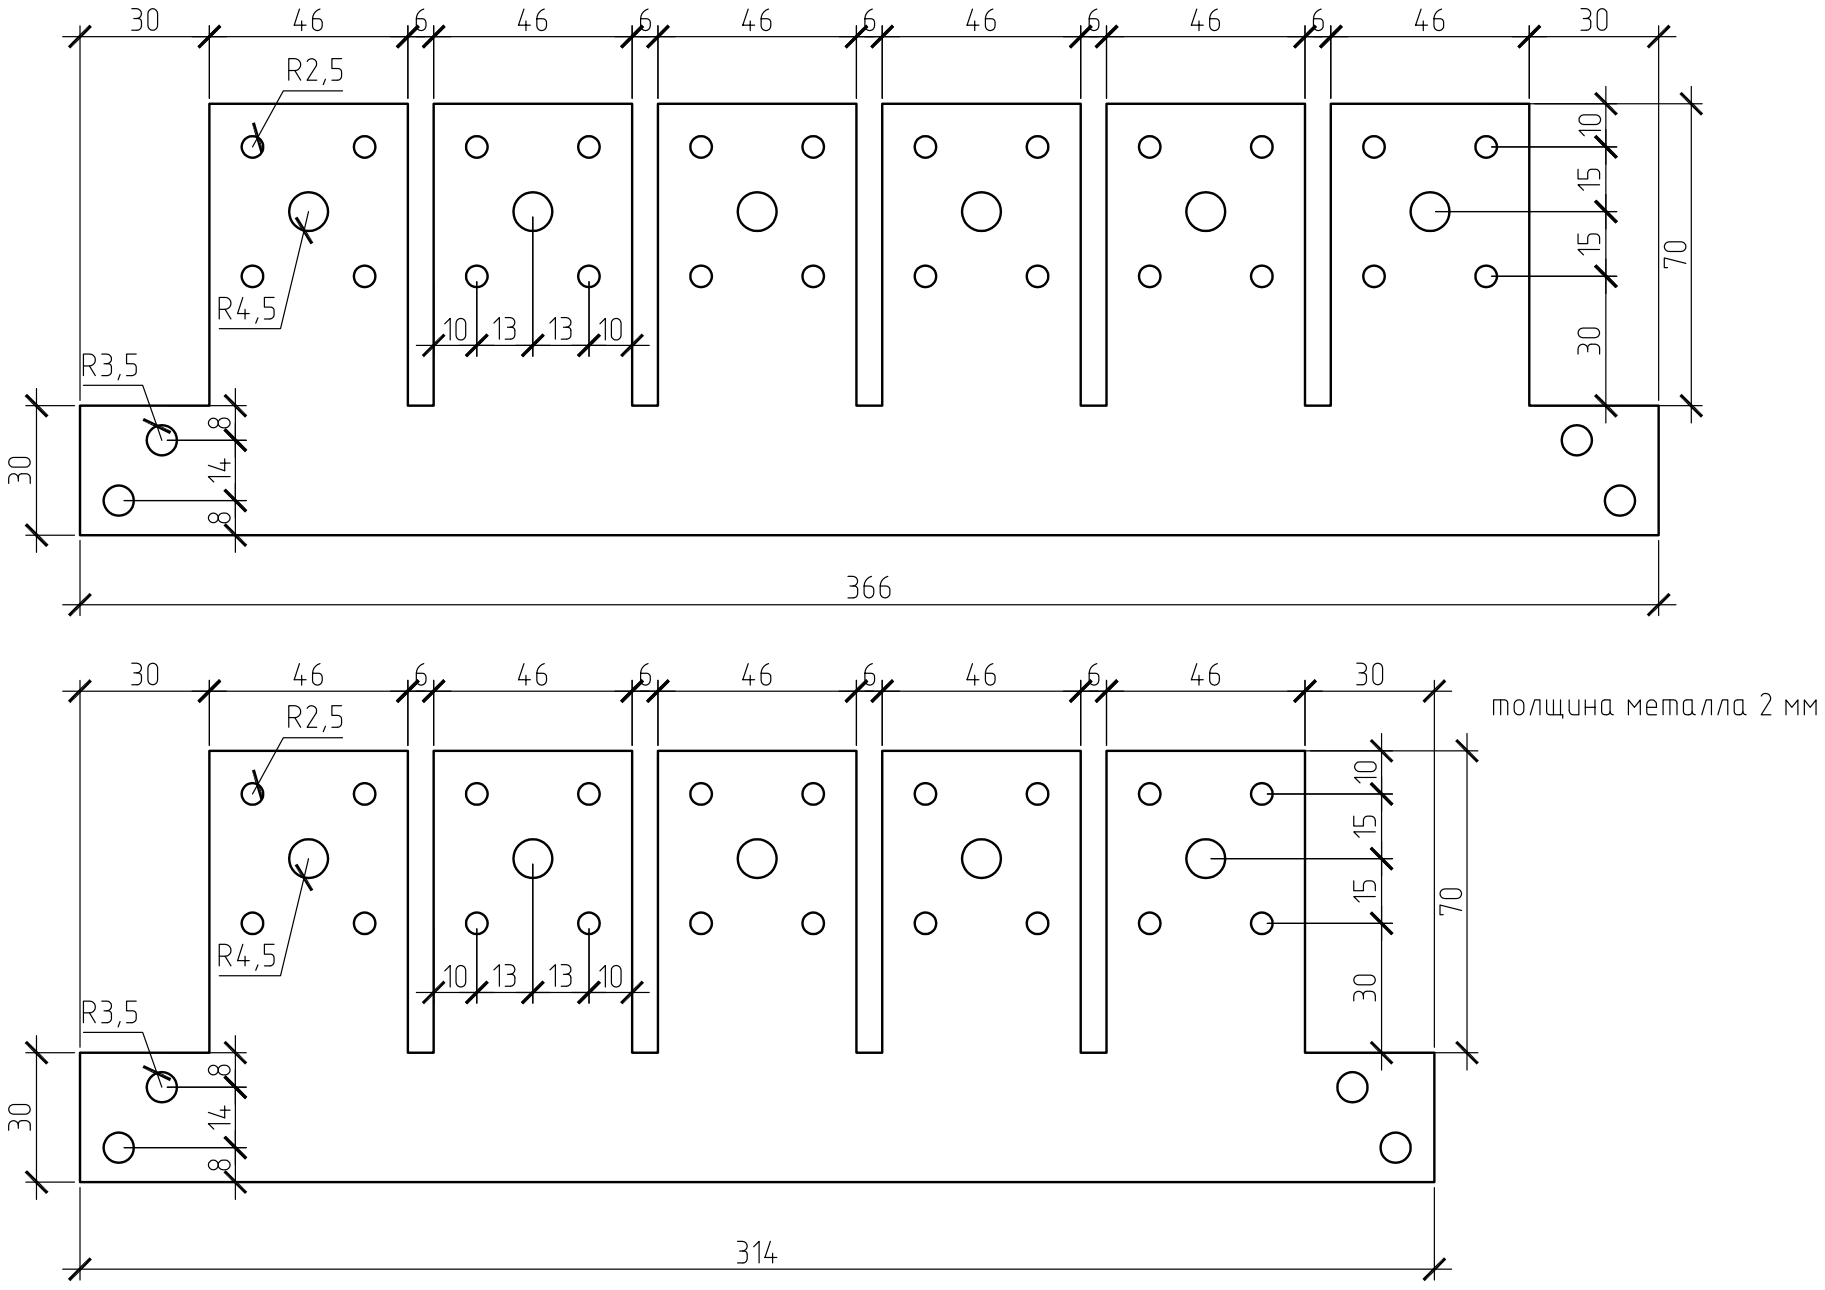
[picture p364: page 1]
