peter-hanzo/KD/Документы/Чертежи/Архитектура (эскизный)/printable/лист 3 схема генплана.pdf

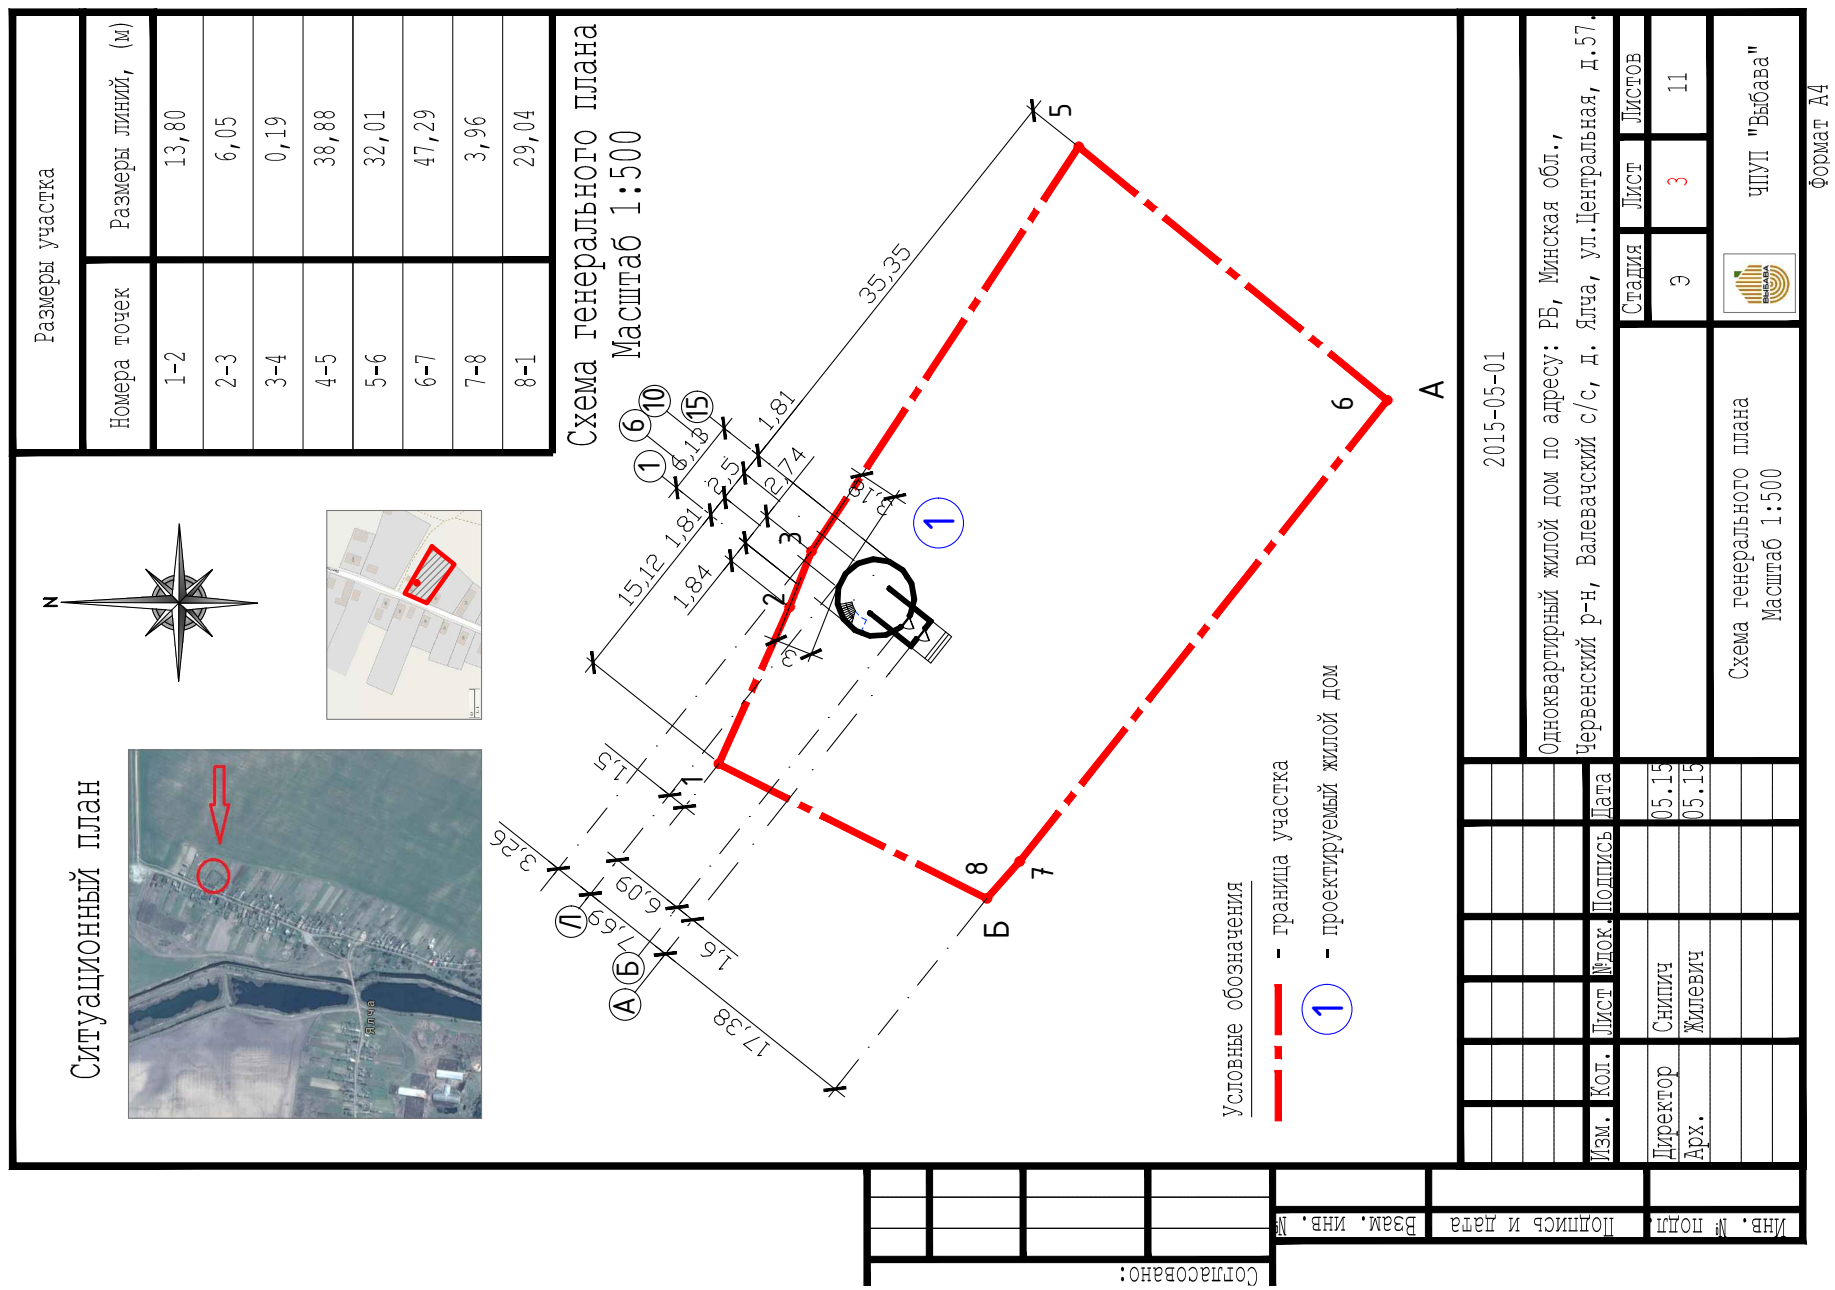
[picture p365: page 1]
