peter-hanzo/KD/Документы/Фактические расходы/2015-07/2015-07-13 - 23 800р - Транспорт - Минск-Ялча.JPG

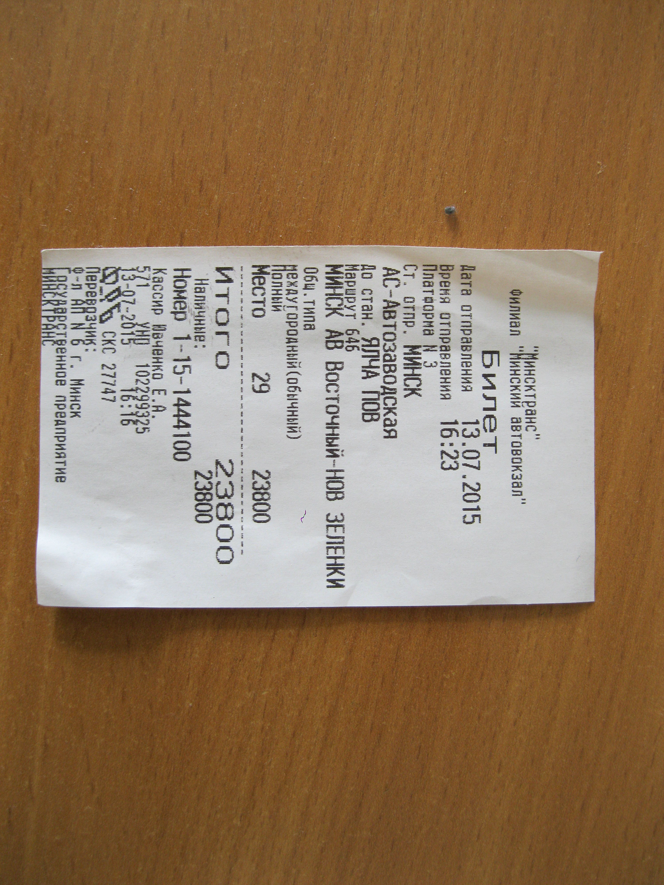
Документы/Фактические расходы/2015-07/2015-07-13 - 23 800р - Транспорт - Минск-Ялча.JPG
