peter-hanzo/KD/Документы/Фактические расходы/2015-07/2015-07-14 - 27 000р - Транспорт - Ялча-Минск.JPG

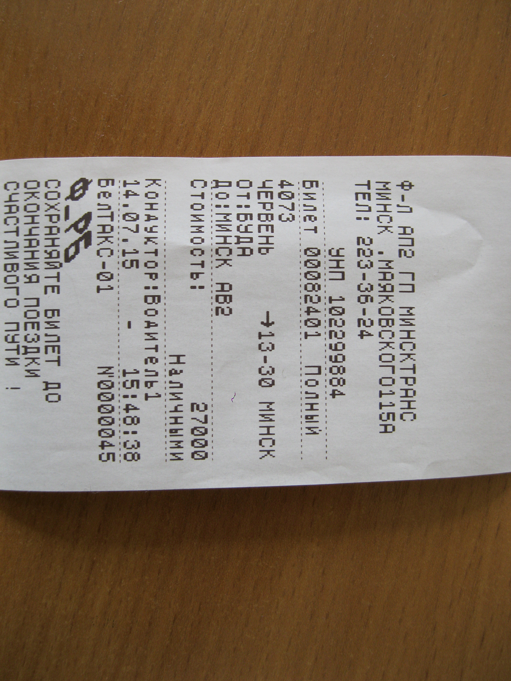
Документы/Фактические расходы/2015-07/2015-07-14 - 27 000р - Транспорт - Ялча-Минск.JPG
